antorsae/lx/baffle_modeling/l22mg-current-status/README.md

# L22MG current simulation status

This note identifies the current dense-BEM validation artifacts and the remaining gap to the requested acceptance target. The current default target is Juan's same-room/same-driver L22MG top-baffle measurement, not an Andres regenerated or retimed HDF5.

Requirement-by-requirement evidence and gaps are tracked in `docs/l22mg-requirement-trace/README.md`.

Secondary LX521 full-system context is now isolated in `docs/l22mg-lx521-system-sanity/README.md`. That report audits `output/data/polar_data_lx521_system.h5` only as a sanity surface for the measured high-mid system data path; it is not an L22MG mounted-alone acceptance target and is not used to tune the source or any rear/source scalar.

## Current Juan-Target Validation Path

- Current target: `output/data/polar_data_juan_lx521_top_raw.h5`, driver `L22MG (LX521 top raw)`.
- Measurement geometry: 0.50 m and LM/L22MG height, matching Juan's baffleless source measurements.
- Default validation angles: loaded from the target HDF5. For the Juan L22MG top-baffle target this is exactly 0/15/30/45/60/75/90 deg.
- Smoke evidence: `docs/l22mg-juan-top-target-angle-smoke/README.md` records `validation_angle_policy=target_hdf5_angles`, identical model/target angle lists, and no angular interpolation.
- Gate evidence: `docs/l22mg-juan-top-target-angle-smoke-gates/README.md` is a bounded edge-solver smoke, not acceptance. It proves the current target/geometry/angle provenance is auditable; the current full dense-BEM 300-1200 Hz evidence is the q7/near Juan-target candidate family summarized below, and it still fails shape, mesh, and passive-geometry gates.
- Mesh-target gate evidence: `scripts/backfill_l22mg_mesh_target_metadata.py` computes the same lambda/6 broad and lambda/10 boundary/local sizing metadata from stored HDF5 BEM attrs, and `docs/l22mg-mesh-target-metadata-smoke-gates/README.md` proves the gate-summary layer consumes it as an acceptance gate. The smoke intentionally fails because a 90 mm dense-BEM mesh at 2 kHz exceeds those targets. The current full-band artifacts have now been backfilled and report `mesh target = fail`: the h42/local32 rows are below lambda/6 broadly at 1200 Hz but exceed the 28.58 mm lambda/10 boundary/local target. This sizing gate is still not mesh-convergence proof.
- Mesh-target-compliant BEM smoke: `docs/l22mg-bem-juan-top-h1659-modal-compact2-solid-passive-h42-h28-q7near-meshtarget-smoke-gates/README.md` reruns the compact2 solid-passive q7/near path sparsely from 300-1200 Hz with h42/boundary28/local28. It passes the mesh-target gate at the 1200 Hz exported max frequency, with 28.00 mm boundary/local h below the 28.58 mm lambda/10 target, exact Juan target angles, direct-solver residual 8.315e-16, and source-CV pass. It is not an acceptance run: no mesh-convergence pair was run, all-angle normalized RMS is 4.028 dB, target-quality warnings remain, and passive-geometry parity remains `not_proven`.
- Mesh-target-compliant convergence smoke: `docs/l22mg-bem-juan-top-h1659-modal-compact2-solid-passive-h42-h28-h36-h24-q7near-meshtarget-conv-smoke-gates/README.md` adds the missing BEM convergence pair for the same sparse compact2 solid-passive path, comparing h42/boundary28/local28 against h36/boundary24/local24 while still solving exactly at the Juan 0/15/30/45/60/75/90 deg target angles. It passes coverage, angle-grid, source-CV, mesh-target sizing, and direct-solver gates, but it still fails acceptance: max normalized-polar mesh movement is 0.702 dB over 300-1200 Hz, above the 0.5 dB gate, all-angle normalized RMS remains 4.028 dB, target-quality warnings remain, and passive-geometry parity remains `not_proven`.
- Finer mesh-target convergence checks: `docs/l22mg-bem-juan-top-h1659-modal-compact2-solid-passive-h36-h24-h32-h21-q7near-meshtarget-conv-smoke-gates/README.md`, `docs/l22mg-bem-juan-top-h1659-modal-compact2-solid-passive-h32-h21-h28-h18-q7near-meshtarget-conv-smoke-gates/README.md`, and `docs/l22mg-bem-juan-top-h1659-modal-compact2-solid-passive-h28-h18-h24-h16-q7near-meshtarget-conv-smoke-gates/README.md` continue the same sparse current-format path with h36/boundary24/local24 versus h32/boundary21/local21, h32/boundary21/local21 versus h28/boundary18/local18, and h28/boundary18/local18 versus h24/boundary16/local16. All pass mesh-target sizing, exact Juan target angles, source-CV, and direct-solver gates, but all still fail all-angle mesh convergence because the 300 Hz / 90 deg point moves 1.179 dB, 1.733 dB, and 3.444 dB respectively. Through-80 movement is much lower, 0.227 dB, 0.572 dB, and 0.305 dB, but the acceptance gate is all-angle and remains failed.
- Target-panel averaging diagnostics: `docs/l22mg-bem-juan-top-h1659-modal-compact2-solid-passive-h32-h21-h28-h18-q7near-targetavg3-meshtarget-conv-smoke-gates/README.md` and `docs/l22mg-bem-juan-top-h1659-modal-compact2-solid-passive-h32-h21-h28-h18-q7near-targetavg7-meshtarget-conv-smoke-gates/README.md` repeat the h32/boundary21/local21 versus h28/boundary18/local18 pair with target-panel normal-trace averaging. q3 reduces the 300-1200 Hz max mesh movement from 1.733 dB to 0.953 dB and through-80 movement from 0.572 dB to 0.310 dB. q7 improves the same pair further to 0.672 dB all-angle max and 0.187 dB through-80 max, with 0.168 dB RMS movement, but still fails the 0.5 dB all-angle convergence gate. Shape also still fails at 3.920 dB all-angle normalized RMS. The regenerated convergence summary/detail CSVs explicitly record `target_average_order=3`, `target_average_order=7`, and `target_average_chunk_size=128`, so this numerical control is no longer implicit.
- Juan acceptance scorecard: `docs/l22mg-juan-acceptance-scorecard/README.md` selects the current strongest Juan-target row, `compact2-h32-h21-h28-h18-targetavg7-meshtarget-conv-smoke`, and expands the gate result into one row per criterion. It passes target provenance, 0.50 m LM/L22 measurement geometry, exact 0/15/30/45/60/75/90 deg target-angle solving, one global validation gain plus one global delay, zero angle-dependent/band-specific/rear/source dB corrections, full 300-1200 Hz coverage, wavelength mesh-target sizing, direct dense-BEM residual metadata, source-CV, source-offplane-not-required, contours, decomposition, and non-blocking `driver_stl_geometry_provenance` for the H1659-derived geometry dimensions. It still fails acceptance because all-angle shape is 3.920 dB, mesh movement is 0.672 dB versus the 0.5 dB gate, the 300 Hz / 75 deg target-quality warnings remain blocking, and the L22-only passive state is unproven. The scorecard now also writes `target_quality_masked_shape_diagnostic.csv`: excluding the stored 75 deg / 300.293-383.423 Hz target-quality cluster lowers the diagnostic-only all-angle RMS to 3.461 dB and through-80 RMS to 2.858 dB, but full-data acceptance remains unchanged. It also links the separate current-radius five-width deliverable, with 205/255/305/355/405 mm rows and required 205/305/405 rows present, while keeping width behavior qualitative because the 305 mm baseline still fails.
- Dense-BEM Juan-target smoke: `docs/l22mg-bem-juan-top-h1659-modal-compact2-dipole-angle-smoke/README.md` uses the current best Juan-only recommended source row, `h1659-modal-compact2-az24-reg1e-06`, with `rear_phase_mode=dipole`, exact target HDF5 angles, 640 BEM panels, and direct-solve max relative residual 7.106e-16. Its gate summary, `docs/l22mg-bem-juan-top-h1659-modal-compact2-dipole-angle-smoke-gates/README.md`, passes target provenance, angle-grid, source-CV, source off-plane-not-required, and BEM linear-solver gates. It is still `not_proven` overall because it is a bounded 300-360 Hz smoke and has no BEM mesh-convergence sweep.
- Full-band coarse dense-BEM Juan-target check: `docs/l22mg-bem-juan-top-h1659-modal-compact2-fullband-coarse-gates/README.md` compares h60/local45 against h50/local38 and h50/local38 against h42/local32 over 300-1200 Hz using the same Juan target and source-CV recommended source. Both rows pass target provenance, exact angle-grid, source-CV, source off-plane-not-required, full-band coverage, and direct-solver residual gates. Both still fail acceptance: h60/h50 has 4.795 dB all-angle normalized RMS and 1.058 dB mesh change; h50/h42 has 4.607 dB all-angle normalized RMS and 1.662 dB mesh change. Through-60 RMS is much better at 1.045 dB and 0.945 dB, but all-angle failure is dominated by the 75 deg low-frequency residual near 300.3 Hz.
- q7/near-panel full-band follow-up: `docs/l22mg-bem-juan-top-h1659-modal-compact2-fullband-q7near-gates/README.md` repeats the current Juan-target/source-CV recommended path with q7 integration and q7 near-panel subdivision. The default gate-summary report, `docs/l22mg-validation-gate-summary/README.md`, now summarizes this current Juan q7/near candidate family by default; legacy Andres/diagnostic artifacts require an explicit artifact preset. The `andres-mounted` q7/near run reduces the h50/local38 versus h42/local32 mesh delta from 1.662 dB to 1.207 dB, but h42/local32 versus h36/local27 is still 1.376 dB, so the low-frequency high-angle mesh movement is not solved by q7/near-panel integration alone. Its best row still fails shape at 4.429 dB all-angle normalized RMS over 300-1200 Hz, with through-60 RMS 0.934 dB and worst residual about +19.8 dB at 300.3 Hz / 75 deg.
- Width-sweep reporting guard: gate summaries now require the 205/305/405 mm rows before any passing 305 mm baseline can be called a quantitative width sweep, and they mark width-sweep artifacts with stale Juan source radius metadata as `stale_source_radius_diagnostic_only`. The current five-width BEM sweep, `docs/l22mg-bem-juan-top-h1659-modal-compact2-current-width-sweep-h42-h28-q7near-targetavg7-gates/README.md`, uses the corrected 0.50 m Juan radius and exact target angles, includes 205/255/305/355/405 mm rows, and is `qualitative_only` because the 305 mm baseline still fails all-angle shape and has no internal mesh-convergence pair. If a future baseline passes but still lacks required rows, the status is `not_proven`.
- Solid-passive Juan-target follow-up: `docs/l22mg-bem-juan-top-h1659-modal-compact2-solid-passive-gates/README.md` adds a target-neutral `passive-aperture-treatment=none` variant for the compact2 source, exact Juan HDF5 angles, 0.50 m source/target radius, q7 near-panel integration, and h42/local32 versus h36/local27 convergence. This is still the best current default-gate row by all-angle shape, but it fails acceptance: 4.233 dB all-angle normalized RMS, 0.977 dB through 60 deg, 3.541 dB through 80 deg, and worst residual +18.9 dB at 300.293 Hz / 75 deg. Mesh convergence worsens to 2.344 dB max, and passive-geometry parity remains `not_proven`.
- Additional source-candidate follow-up: the remaining finite H1659 rows that passed Juan-only source-CV now have current 0.50 m Juan-target full-band solid-passive BEM evidence. `docs/l22mg-bem-juan-top-h1659-modal-full2-solid-passive-gates/README.md` rejects full2 at 4.270 dB all-angle RMS, 3.558 dB through 80 deg, and 2.326 dB mesh max. `docs/l22mg-bem-juan-top-h1659-modal-compact3-solid-passive-gates/README.md` rejects compact3 at 5.410 dB all-angle RMS, 4.308 dB through 80 deg, and 5.470 dB mesh max. `docs/l22mg-bem-juan-top-h1659-modal-full4-svd-solid-passive-gates/README.md` rejects full4-SVD at 10.911 dB all-angle RMS, 8.705 dB through 80 deg, and 3.643 dB mesh max. `docs/l22mg-bem-juan-top-h1659-profile-ring-full-solid-passive-gates/README.md` rejects the full profile-ring SVD/no-SVD rows at 9.254/9.265 dB all-angle RMS, 6.696/6.707 dB through 80 deg, and 0.902/0.889 dB mesh max. This means the current recommended finite equivalent-source family is now contradicted by mapped BEM evidence, not merely missing BEM evidence.
- Axisymmetric directivity Juan-target diagnostic: `docs/l22mg-bem-juan-top-axisymmetric-directivity-1000-1200-current/README.md` and `docs/l22mg-bem-juan-top-axisymmetric-directivity-1000-1200-current-gates/README.md` map the no-inversion rotated naked-polar source into the current Juan L22 top-baffle target at the corrected 0.50 m radius and exact 0/15/30/45/60/75/90 deg target angles. It is current negative evidence, not a fit correction: source CV remains `diagnostic_only`, coverage is only 1000-1200 Hz, all-angle normalized RMS is 5.768 dB, through-80 RMS is 3.344 dB, worst error is +13.807 dB at 1000.1 Hz / 90 deg, and passive geometry remains `not_proven`.
- Passive-geometry gate: the default gate-summary report marks all current Juan q7/near rows as `passive geom = not_proven`. The older rows use `andres-mounted` passive geometry, meaning a raised UM face and closed tweeter patches inherited from the Andres mounted-driver condition. The solid-passive rows avoid silently applying Andres-mounted geometry, but the current validation target is Juan's L22-only top-baffle capture and the HDF5 also contains a separate `L22MG+L10NEO+Tweeters (LX521 top raw)` capture; the L22-only HDF5 now records `passive_state_status=unused_um_tweeter_state_unrecorded`, which is an explicit unknown rather than evidence for open holes, covered patches, or mounted inactive drivers. This is an explicit parity blocker, not a correction knob.
- Juan passive-state provenance audit: `docs/l22mg-juan-top-passive-state-audit/README.md` reads the stored HDF5 notes directly and writes the structured passive-state attrs. It confirms the L22MG target notes prove 50 cm distance, LM/L22MG mic height, LX521 top-baffle mounting, and raw/no-crossover/no-EQ processing, while the unused L10NEO/tweeter physical state remains unrecorded. It also confirms the multi-driver capture explicitly records L22MG + L10NEO + tweeters on the top baffle, but that is a multi-source no-crossover context measurement, not an L22-alone passive-geometry target. The passive-geometry gate now points to this audit.
- Focused Juan low-frequency/high-angle diagnostic: `docs/l22mg-juan-top-lowfreq-high-angle-diagnostic/README.md` reads the previous mounted-passive q7/near artifact's `/validation_decomposition` group without refitting or rerunning. At the worst point, 300.3 Hz / 75 deg, the Juan top-baffle target is -29.9 dB normalized, the synthetic nude reference is -10.6 dB, and the mounted model is -10.1 dB. Relative to the synthetic nude field, the target deepens by -19.3 dB while the model fills by +0.5 dB. The same report reads the stored mesh-convergence summary: h42/local32 versus h36/local27 moves 1.38 dB at 300 Hz / 90 deg and 0.572 dB through 80 deg at 300 Hz / 75 deg. The newer solid-passive row leaves the same measured-target null as the dominant all-angle blocker: +18.909 dB at 300.293 Hz / 75 deg. New BEM convergence runs now also export `bem_mesh_convergence_detail.csv` so this mesh-delta surface is inspectable per frequency and angle instead of only as maxima. The focused rerun `docs/l22mg-juan-top-q7near-300hz-mesh-detail-diagnostic/README.md` uses the same h42/local32 versus h36/local27 q7/near pair over the 300 Hz blocker and shows the side-by-side detail: at 300.293 Hz / 75 deg the validation residual is +19.806 dB while the mesh normalized delta is -0.572 dB; at 90 deg the validation residual is only +1.518 dB while the mesh delta is -1.374 dB. So the 75 deg acceptance failure is primarily model/source/measurement physics, while the 90 deg point remains the larger local mesh-movement diagnostic.
- Juan measured-target null audit: `docs/l22mg-juan-top-target-null-audit/README.md` compares measured Juan L22 top-baffle, measured Juan L22 nude, and the multi-driver top-baffle capture without running BEM or changing gates. At 300.293 Hz / 75 deg the L22-alone top target is -29.894 dB normalized while the measured L22 nude is -9.594 dB, so the measured target-minus-nude transfer is -20.300 dB. The multi-driver top capture at the same frequency/angle is -18.024 dB, 11.870 dB shallower than the L22-alone target. That does not invalidate the L22-alone target, but it makes this 75 deg null a repeatability/target-quality item before treating it as decisive proof of BEM/source failure.
- Juan top-baffle front/rear consistency audit: `docs/l22mg-juan-top-front-rear-consistency/README.md` reads measured Juan HDF5 front and rear data only. At the same 300.293 Hz / 75 deg blocker, the L22-alone front target is -29.894 dB but the rear side is -9.455 dB, so front-minus-rear is -20.440 dB and the measured front-minus-rear baffle-transfer delta is -21.300 dB. Over 300-600 Hz and 60-90 deg, L22 top front/rear normalized RMS difference is 10.733 dB. This strengthens the target-quality/repeatability warning and prevents a future BEM/source change from being accepted merely because it target-fits that isolated front-side null.
- Juan target-polar-quality audit: `docs/l22mg-juan-top-target-polar-quality/README.md` flags the same low-frequency region without looking at the model. With a -25 dB threshold over 300-600 Hz, it finds one deep cluster: 75 deg at 300.293 Hz, -29.894 dB normalized, 83.1 Hz wide, and 17.3 dB deeper than adjacent angles. The same-angle local contrast is only -0.6 dB, so this is broad in frequency but angularly isolated.
- Target-null gate-summary integration: `docs/l22mg-juan-top-target-null-gate-summary/README.md` shows the current q7/near full-band row and the focused 300 Hz row now report `target null = warning`. The warning is diagnostic target-quality context, not an alternate target and not a scalar correction; it prevents the 300 Hz / 75 deg residual from being read as a silent clean acceptance anchor.
- Juan low-frequency geometry sensitivity: `docs/l22mg-juan-top-lowfreq-geometry-sensitivity/README.md` reruns only the 300.293/304.321 Hz blocker against the Juan target while changing physical geometry/passive assumptions, not source/rear scalars. Tested variants include the current raised UM face, closed solid passive patches, open passive holes, raised tweeter faces, and Wmax 205/405 mm. None closes the 75 deg null: the best 70-90 deg RMS is still 13.301 dB (`width205_um_face`), and every variant's max miss remains at 300.293 Hz / 75 deg around 18.9-19.9 dB. Simple baffle width/passive treatment changes therefore do not explain the measured L22-alone 75 deg target null.
- Juan passive-state band sensitivity: `docs/l22mg-juan-top-passive-state-band-sensitivity/README.md` reruns a sparse 300-600 Hz diagnostic at the actual Juan target angles 0/15/30/45/60/75/90 deg. Solid patches are the best of the tested passive-state variants, but still leave 9.890 dB RMS over 70-90 deg and 0.932 dB RMS over 0-60 deg; open holes are essentially similar at 9.919 dB over 70-90 deg. This does not prove the passive state, but it shows simple passive-state assumptions do not close the low-frequency high-angle target null.
- Juan low-frequency source-support/acoustic-center sweep: `docs/l22mg-juan-top-lowfreq-source-support-sweep/README.md` reuses the same 300.293/304.321 Hz Juan target hotspot and fixed mounted-baffle BEM geometry, then varies only Juan-fitted source supports plus bounded acoustic-center offsets of -20/0/+20 mm. The best row, `d65_r0-25-50-75-95_svd1e-6_ac-20mm`, keeps 0-60 deg RMS at 1.434 dB and improves 70-90 deg RMS from 14.046 dB for the current source to 7.361 dB. That is useful sensitivity evidence, but still far from the 1.5 dB target and not an acceptance path; it also remains a source-support diagnostic, not a target-derived correction.
- Andres published parity remains available only as an explicit legacy validation target, now through `--validation-preset andres-published-parity`. Preset smoke evidence: `docs/l22mg-andres-published-parity-preset-smoke/README.md` records the canonical HDF5/driver/hypothesis bundle, exact 0/10/.../90 deg target-angle solve, 1 m UM-height mic (+165 mm relative to L22), published-explorer parity match, and no angular interpolation; `docs/l22mg-andres-published-parity-preset-smoke-gates/README.md` verifies the same provenance through the gate-summary layer. The gate-summary and source-decision join now also reject Andres published-parity rows unless the stored mic geometry is explicitly `validation_mic_reference=um`, `validation_mic_z_offset_mm=165.0`, and `validation_mic_horizontal_radius_m=1.0`; the passive-geometry gate also requires `andres-mounted` plus `passive_um_driver_included=True`, so a UM cutout without a modeled mounted UM driver face cannot pass as published-parity evidence. First-lobe, strongest-lobe, direct-gate, and late-window Andres variants remain diagnostics unless the published explorer is regenerated from the same data.
- Current-format Andres dense-BEM preset smoke: `docs/l22mg-bem-andres-published-parity-preset-h1659-compact2-smoke/README.md` runs the actual dense Neumann BEM backend, not the edge baseline, with `--validation-preset andres-published-parity`, the corrected 0.50 m Juan naked-source radius, H1659 modal compact-2 source, Andres-mounted passive geometry, and direct solver residual 7.106e-16. Its gate summary, `docs/l22mg-bem-andres-published-parity-preset-h1659-compact2-smoke-gates/README.md`, passes target provenance, exact target-angle grid, source-CV, BEM solver residual, contours, and decomposition. It is still not acceptance evidence because it only covers 300-360 Hz, has no mesh-convergence sweep, fails source off-plane spread, and the available-overlap all-angle RMS is 9.277 dB due to the published 90 deg low-frequency null. Through-60 over this bounded overlap is 0.333 dB and through-80 is 1.515 dB.
- Current-format Andres bounded BEM convergence smoke: `docs/l22mg-bem-andres-published-parity-preset-h1659-compact2-conv-smoke/README.md` repeats that dense-BEM preset path and compares h60/boundary45/local45 against h50/boundary38/local38 over 300-360 Hz. The gate summary, `docs/l22mg-bem-andres-published-parity-preset-h1659-compact2-conv-smoke-gates/README.md`, keeps it `not_proven`: coverage is not full-band and the h60-to-h50 mesh movement is still too large for acceptance, with max normalized change 1.303 dB at 300 Hz / 80 deg and RMS 0.511 dB over the available overlap. The validation miss itself remains dominated by the published 90 deg low-frequency null: all-angle RMS 9.277 dB, through-60 0.333 dB, through-80 1.515 dB, worst +29.386 dB at 330 Hz / 90 deg.
- Current-format Andres q7/near bounded convergence smoke: `docs/l22mg-bem-andres-published-parity-preset-h1659-compact2-q7near-h50-h42-smoke/README.md` compares h50/boundary38/local38 against h42/boundary32/local32 with q7 triangle quadrature plus q7 near-panel integration over the same 300-360 Hz Andres preset band. Its gate summary, `docs/l22mg-bem-andres-published-parity-preset-h1659-compact2-q7near-h50-h42-smoke-gates/README.md`, is still diagnostic: max normalized mesh change is 1.236 dB at 300 Hz / 90 deg, through-80 max is 0.994 dB at 300 Hz / 80 deg, and RMS mesh movement is 0.461 dB. The finer/q7 path improves the validation overlap versus the h60 smoke, with all-angle RMS 8.852 dB, through-60 0.170 dB, through-80 0.989 dB, and worst +28.244 dB at 331.4 Hz / 90 deg, but it still cannot be read as full-band or mesh-converged acceptance evidence.
- Current-format Andres physical rear-basket smoke: `docs/l22mg-bem-andres-published-parity-physical-rear-basket-smoke/README.md` runs the coupled H1659 physical-diaphragm/rear-basket prescribed-Neumann source against Andres published parity at the corrected 0.50 m Juan radius, exact 0/10/.../90 deg target angles, Andres-mounted passive geometry, and no source/rear scalar correction. Its gate summary, `docs/l22mg-bem-andres-published-parity-physical-rear-basket-smoke-gates/README.md`, is negative bounded evidence only: it covers 300-301 Hz, passes target provenance, exact angle grid, mesh-target sizing, dense direct residual, passive geometry, contours, and decomposition, but fails coverage, source CV, source off-plane generalization, target measurement quality, and shape at 6.869 dB all-angle RMS. Through-60 is 0.233 dB and through-80 is 1.218 dB, but the worst residual remains +21.4 dB at 301 Hz / 90 deg. It is now joined into the source-candidate decision report as Andres side evidence, not as Juan acceptance evidence.

- Current-format Andres coupled rear-basket plus active-driver feature-proxy smoke: `docs/l22mg-bem-andres-published-parity-coupled-rear-basket-feature-proxy-smoke/README.md` adds the explicit H1659 feature-proxy path to the same coupled physical source: rigid STL-derived frame/flange/motor scatterer, mounting pockets forced on, thin 0.6 mm flange sidewalls omitted as a labelled constant-panel mesh-quality approximation, Andres-mounted passive geometry, corrected 0.50 m Juan source radius, and exact Andres target HDF5 angles. Its gate summary, `docs/l22mg-bem-andres-published-parity-coupled-rear-basket-feature-proxy-smoke-gates/README.md`, is also negative bounded evidence only. Over the same 300-301 Hz overlap it worsens the physical rear-basket smoke to 13.965 dB all-angle RMS, 2.465 dB through 60 deg, 6.156 dB through 80 deg, and worst +40.1 dB at 301 Hz / 90 deg. This rules out the first rigid feature-proxy obstruction as a hidden fix for the Andres low-frequency high-angle null; it is not a raw-STL solve, not elastic driver physics, and not a scalar correction.
- Current-format Andres full-band modal-full2 rerun: `docs/l22mg-bem-andres-published-parity-h1659-modal-full2-300-1200-current/README.md` reruns the strongest historical Andres full-band source family with `--validation-preset andres-published-parity`, corrected 0.50 m Juan naked-source radius, exact 0/10/.../90 deg target-angle solve, Andres-mounted passive geometry, q7 plus q7 near integration, and h22/local13.2 versus h20/local12 convergence over 300-1200 Hz. Its gate summary, `docs/l22mg-bem-andres-published-parity-h1659-modal-full2-300-1200-current-gates/README.md`, passes target provenance, full 300-1200 coverage, exact target-angle grid, mesh convergence (0.111 dB max, 0.027 dB RMS), direct solver residual (1.576e-15), Juan-only source-CV, passive geometry, contours, and decomposition. It still fails acceptance because all-angle normalized RMS is 4.428 dB and source off-plane generalization fails; through-60 RMS is 0.686 dB and through-80 RMS is 1.377 dB.
- Andres acceptance scorecard: `docs/l22mg-andres-acceptance-scorecard/README.md` selects that current full-band modal-full2 row as the strongest current-radius published-parity evidence because it has full 300-1200 coverage and proven mesh convergence. The scorecard expands the gate result into one row per criterion: target provenance, UM-height measurement geometry, exact target-angle solve, one global validation gain plus one global delay, zero angle-dependent/band-specific/rear/source dB corrections, coverage, mesh convergence, wavelength mesh-target sizing, dense direct residual, source CV, passive geometry, contours, and decomposition pass; target measurement quality remains `not_proven` because late-window/high-angle stability is unresolved, all-angle normalized polar shape fails at 4.428 dB, and source off-plane generalization fails at 13.406 dB over 70-90 deg. The off-plane row now separates the selected source's small z=0-to-UM-height movement (0.153 dB RMS over 70-90 deg) from the much larger Juan-CV-eligible source-family spread at UM height (13.406 dB RMS / 26.652 dB max over 70-90 deg). It now also includes a `validation_metric_breakdown` diagnostic row for on-axis, baffle-transfer, F90-F0, DI, -6 dB beamwidth, and complex-pressure residuals, plus `high_angle_late_window_caveat` and `target_quality_masked_shape_diagnostic` rows that record the through-60/through-80 shape numbers, raw-IR gate movement, target-quality cluster masking, and target >= -20 dB masking without excluding data or changing acceptance. The diagnostic CSV, `docs/l22mg-andres-acceptance-scorecard/target_quality_masked_shape_diagnostic.csv`, shows full-data RMS 4.428 dB, cluster-masked RMS 2.561 dB, and target >= -20 dB RMS 1.365 dB; this localizes the high-angle target-quality blocker but is not an acceptance substitute. Width sweeps remain `qualitative_only`.
- Current-format Andres axisymmetric-directivity diagnostic: `docs/l22mg-bem-andres-published-parity-axisymmetric-directivity-1000-1200-current/README.md` refreshes the no-inversion directivity-table source with the corrected 0.50 m Juan radius, Andres published-parity target, exact 0/10/.../90 deg target angles, Andres-mounted passive geometry, and h42/local32 q7-near BEM. Its gate summary, `docs/l22mg-bem-andres-published-parity-axisymmetric-directivity-1000-1200-current-gates/README.md`, passes target provenance, exact angle grid, direct solver residual (1.041e-15), passive geometry, contours, and decomposition, but remains rejected diagnostic evidence: coverage is only 1000-1200 Hz, no mesh convergence sweep was run, all-angle normalized RMS is 3.912 dB over the available overlap, source CV is `diagnostic_only`, and source off-plane spread fails at 13.940 dB over 70-90 deg. The direct rotated naked polar is therefore current-radius negative evidence, not a high-fidelity acceptance source.

## Historical Andres Corrected-Geometry Validation Artifact

- Report: `docs/l22mg-bem-passive-um-cutout-widecloud-svd1e-5-h20-h18-conv-q7-near-1200-12ppo/README.md`.
- HDF5: `output/l22mg-bem-passive-um-cutout-widecloud-svd1e-5-h20-h18-conv-q7-near-1200-12ppo/polar_data_l22mg_lx5214_baffle_sim.h5`.
- Strict gate report: `docs/l22mg-validation-gate-current-backfilled/README.md`.
- Validation decomposition diagnostic: `docs/l22mg-validation-decomposition-current/README.md`.
- Solver: dense constant-element exterior Neumann BEM, finite-thickness LX521.4 top baffle, passive aperture treatment `andres-mounted`.
- Baffle thickness: 19.05 mm.
- Mesh: `delaunay-local`, broad h = 20.0 mm, boundary/local h = 12.0 mm, local refinement width = 36.6 mm, q7 triangle quadrature plus q7 near-panel integration with one subdivision and distance factor 2.5.
- Mounted passive geometry: parameterized rigid UM face, diameter 82 mm, height 4 mm, mesh h 16 mm, over an 82 mm UM cutout; tweeter positions closed as solid patches.
- Source: split front/rear finite monopole cloud fit to Juan nude L22MG only, half-depth 45 mm, radii 0/35/70/95 mm, regularization 1e-6, SVD rcond 1e-5.
- Important: this is the latest mesh-converged corrected-geometry validation comparison now replayed against the canonical Andres published-parity target, `output/data/polar_data_andres_early_peak_legacy.h5`. That HDF5 matches the already-published polar explorer at 1004 Hz, so it is the acceptance target unless the published explorer is regenerated from a different HDF5 in the same commit. The h20/local12.0 versus h18/local10.8 q7-near mesh comparison passes the 0.5 dB max-change gate, but the artifact still fails shape validation.
- Superseded reference: `docs/l22mg-bem-local-h22-h20-conv-1200-q3-d25-t1905-48ppo/README.md` used literal open passive UM/tweeter holes, so it is no longer a valid Andres-geometry baseline.
- Superseded mounted-passive reference: `docs/l22mg-bem-passive-um-widecloud-svd1e-5-h22-q7-near-1200-12ppo/README.md` placed the raised UM face over a closed solid patch. It remains useful as a before/after diagnostic, but not as the current Andres-mounted geometry baseline.
- Important: the current corrected-geometry artifacts now satisfy both the h22/h20 and h20/h18 mesh-change checks, but no current dense-BEM artifact satisfies the Andres shape validation target.

## Best Source Diagnostic So Far

- Report: `docs/l22mg-bem-passive-um-cutout-widecloud-svd1e-5-h22-q7-near-1200-12ppo/README.md`.
- HDF5: `output/l22mg-bem-passive-um-cutout-widecloud-svd1e-5-h22-q7-near-1200-12ppo/polar_data_l22mg_lx5214_baffle_sim.h5`.
- Difference from the older stable 0/40/75 mm source artifact: source radii are 0/35/70/95 mm, with 45 mm half-depth, dipole reconstructed rear phase, and SVD rcond 1e-5. The passive UM is now modeled as a mounted face over the UM cutout rather than over a solid patch.
- Conditioning: SVD-truncated Juan-only fit with `--source-svd-rcond 1e-5`; raw `design_cond_max` remains about 6.8e9, but effective condition is capped around 9.6e4 with effective rank 4-6.
- Validation improvement versus the older stable 0/40/75 mm source: normalized polar RMS 300-1200 Hz is 3.658 dB against the canonical published-parity Andres target in the stored h20/h18 mesh-converged wide/SVD baseline. Through-60-deg RMS is 1.327 dB and through-80-deg RMS is 1.956 dB, but the all-angle result still fails because the worst residual is +19.740 dB at 344.6 Hz / 90 deg. Important correction: these stored BEM artifacts were generated with the old, mistaken 0.75 m Juan source radius, so they are now historical geometry/numerics diagnostics until rerun at 0.50 m.
- Caveat: this still fails all-angle acceptance. `output/data/polar_data_andres_early_peak_legacy.h5` is now the canonical published-parity target because it matches the published polar explorer; first-lobe, direct-gate, and strongest-lobe HDF5 variants are diagnostics only unless the published explorer is regenerated from the same data.
- Diagnostic target replays: `docs/l22mg-retimed-artifact-rerank/README.md` and related direct-gate reports rerank older stored predictions against explicitly labelled first-lobe/direct-gate Andres variants without re-solving BEM. They remain useful for target-sensitivity and source-ranking diagnostics, but they do not replace the published-parity target.
- Acoustic-center offset test: `docs/l22mg-bem-passive-um-widecloud-svd1e-5-ac20-h22-q7-near-1200-12ppo/README.md` moves the wide-cloud equivalent source 20 mm rearward. It makes the F90 mean error shallower (+2.042 dB instead of -4.537 dB) but worsens all-angle normalized RMS to 6.161 dB and through-60 RMS to 3.666 dB. Acoustic-center offset alone is therefore not a viable fix for the high-angle miss.
- High-angle residual diagnostic: `docs/l22mg-high-angle-residual-um-cutout-full/README.md` decomposes the current mounted-UM-cutout error. For the current SVD wide-cloud model, 0-60 deg RMS is 1.341 dB, but 70-90 deg RMS is 7.139 dB. The 90 deg mean error is now near zero at +0.172 dB, but the 70-90 deg group still has a worst residual of 25.298 dB at about 1070 Hz / 80 deg. That means the remaining miss is a localized high-angle lobe/null-shape problem, not a single scalar null-depth, 90-degree timing issue, or acoustic-center issue.
- Juan-only source cross-validation: `docs/l22mg-source-model-cross-validation/README.md` now uses the corrected 0.50 m Juan source radius and holds out one nonzero naked angle at a time while keeping 0 deg as the normalization anchor. The current wide/SVD source has in-sample Juan normalized front/rear RMS 2.404/2.500 dB and absolute front/rear RMS 2.381/2.469 dB over 300-1200 Hz, but held-out worst-side RMS is 8.810 dB and is marked `rejected_weak_cv`. The first finite source that passes the Juan-only thresholds is `h1659-modal-compact2-az24-reg1e-06` at 3.298 dB, followed by `h1659-modal-full2-az24-reg1e-06` at 3.300 dB and `h1659-modal-compact3-az24-reg1e-06` at 3.768 dB. Stored 0.75 m BEM replays, including `h1659-modal-full2-300-1200`, are now stale for acceptance joining until rerun at 0.50 m.
- Active H1659 source-surface CV: the expanded source-CV table now includes Juan-fitted prescribed-Neumann active-surface rows. The stored split active-surface m4/gap30 candidate maps to `split-active-surface-compact-m4-az16-gap30-q3-reg1e-06-svd1e-05`, rank 12 of 29, but is `rejected_bad_insample_fit` with 3.673 dB in-sample side-worst and 4.376 dB held-out worst-side RMS; its stored BEM overlap is also poor at 5.320 dB all-angle RMS from 1000-1200 Hz. The single active-surface m3 row is rank 16 of 29, also `rejected_bad_insample_fit`, with 7.047 dB held-out worst-side RMS and 6.815 dB stored BEM overlap. `docs/l22mg-source-cv-active-surface-annular/README.md` adds a focused Juan-only annular active-surface basis audit: the best annular row is split compact, measured rear phase, gap 30 mm, with 4.179 dB held-out worst-side RMS but 3.728 dB in-sample side-worst RMS, so it remains `rejected_bad_insample_fit`. `docs/l22mg-bem-split-active-surface-annular-cv-smoke/README.md` verifies the simulator/HDF5 report path now labels `active_surface_basis_kind=annular` and matches that focused CV row; this is a smoke/report check, not an acceptance run.
- Physical diaphragm source CV: `docs/l22mg-source-cv-physical-diaphragm/README.md` adds a Juan-only coupled H1659 prescribed-Neumann source family with four capped radial velocity modes: piston, two cone bending/tilt shapes, and surround. No row passes the source recommendation gates. The best row, `physical-diaphragm-full-coupled-measured-az16-q3-reg1e-06-svd1e-05`, has 3.448 dB held-out side-worst RMS, but is still `rejected_bad_insample_fit` because in-sample side-worst normalized/absolute/phase RMS are 3.119 dB / 4.712 dB / 62.053 deg.
- Physical rear-filter diagnostic: `docs/l22mg-physical-rear-filter/README.md` fits the same four-mode physical diaphragm to Juan front only, then fits a smooth bounded rear transfer function from Juan rear only. The front-only diaphragm fit is acceptable on the front side over 300-1200 Hz (2.067 dB normalized, 2.053 dB absolute, 13.342 deg phase RMS), but rear normalized RMS remains 3.180 dB after both an unconstrained scalar and the smooth bounded filter. The smooth bounded filter has median -7.569 dB gain and cannot repair rear angular shape because it is shared by all rear angles.
- Physical rear-basket source CV: `docs/l22mg-source-cv-physical-rear-basket/README.md` keeps the diaphragm modes coupled front/rear and adds a small Juan-only rear basket/directivity block. The refreshed full-band set now includes bounded rb3/rb4 measured-phase probes plus frequency-smoothing probes around the actual best low-order m2/rb1 family. The best row is still unsmoothed `physical-rear-basket-compact-measured-m2-rb1-az16-gap16-q3-reg1e-06`, rejected at 3.592 dB held-out side-worst RMS because in-sample side-worst absolute/phase are 4.543 dB / 72.737 deg. The m2/rb1 smoothing probes do not fix this: fsmooth1e-8/1e-7/1e-6 stay at 3.592/3.593/3.596 dB held-out side-worst, 4.543/4.544/4.557 dB absolute, and about 72.74 deg phase. The older m4/rb2 and rb3/rb4 rows remain rejected, so frequency smoothing and extra rear-only terms do not create a Juan-accepted physical source.
- Bounded active-surface annular sweep: `docs/l22mg-source-cv-active-surface-annular-sweep/README.md` sweeps compact/full H1659 annular source surfaces, measured rear phase, 30/36 mm split gaps, and no/SVD truncation over 12 Juan-only candidates. No row passes the Juan-only recommendation gates. The best row is still the compact gap-30 annular source, now without SVD truncation, with 4.179 dB held-out worst-side RMS and 3.728 dB in-sample side-worst RMS over 300-1200 Hz. Because all rows are `rejected_bad_insample_fit`, this sweep is negative source evidence and does not justify a new BEM acceptance attempt.
- Source-CV report integration: current simulator reports now look up matching rows in `docs/l22mg-source-model-cross-validation/source_cv_summary.csv` plus physical-diaphragm and physical-rear-basket summaries by default, then copy the held-out metrics, in-sample side-worst normalized/absolute/phase metrics, recommendation status, recommendation reason, and matched CSV path into both README text and HDF5 metadata. `docs/l22mg-validation-gate-summary/README.md` now refuses stale embedded source-CV metadata when an artifact carries `naked_source_reference_radius_m=0.75`; those artifacts report source CV as not proven against the corrected 0.50 m Juan distance.
- Source-candidate decision join: `docs/l22mg-source-candidate-decision/README.md` combines the current 0.50 m main, physical-diaphragm, physical-diaphragm frequency-smoothing, and physical-rear-basket source-CV rows with the off-plane UM-height source ambiguity audit and the q7 target-averaged compact2 gate summary. It reports zero accepted source candidates across 129 current-radius rows. It now also attaches current-radius Andres published-parity BEM rows as a separate legacy comparison channel, not as Juan acceptance evidence: compact2 maps to the 300-360 Hz q7 smoke at 8.852 dB all-angle / 0.989 dB through-80, full2 maps to the full-band published-parity rerun at 4.428 dB all-angle / 1.377 dB through-80, and the coupled physical rear-basket smoke maps to `physical-rear-basket-andres-smoke` at 6.869 dB all-angle / 1.218 dB through-80 over 300-301 Hz. The decision input list also includes the current feature-proxy Andres smoke, which is worse at 13.965 dB all-angle / 6.156 dB through-80 over 300-301 Hz and therefore does not replace the selected lower-RMS rear-basket side row. The current five-width sweep gate summary for current-radius width reporting and the coupled physical rear-basket Juan-target BEM smoke, `docs/l22mg-coupled-rear-basket-source-smoke-gates/README.md`, remain subject to normal gate ordering and neither can make a failing baseline accepted. The physical rear-basket smoke now appears in the decision table as `coupled-rear-basket-source-smoke`, and rejects `physical-rear-basket-compact-measured-m4-rb2-az16-gap16-q3-reg1e-06` by both source CV and failed available-overlap BEM evidence: 7.608 dB all-angle RMS, 8.189 dB through-80, worst +19.8 dB at 300 Hz / 75 deg. The best physical rear-basket source-CV row, `physical-rear-basket-compact-measured-m2-rb1-az16-gap16-q3-reg1e-06`, is now also joined to bounded Juan and Andres BEM smokes; it is rejected by source CV and failed overlap evidence, with `physical-rear-basket-m2rb1-juan-smoke` at 6.447 dB all-angle / 6.959 dB through-80 and `physical-rear-basket-m2rb1-andres-smoke` at 10.021 dB all-angle / 1.719 dB through-80 over 300-301 Hz. The new m2/rb1 frequency-smoothed rows appear immediately behind it in the decision table, but remain rejected by source CV and have no BEM evidence because they do not pass the Juan source gates. The join maps physical rear-basket rb1/rb2 off-plane cases as well as physical-diaphragm cases; rb3/rb4 rows remain rejected by source CV before off-plane evidence is needed. It also carries the Juan-only rear shared-sign diagnostic: the current `-1` outward-normal convention remains the best normalized front/rear fit at 2.635 dB versus 3.584 dB for the deliberate `+1` diagnostic, so a sign flip is not a hidden source-fit fix. All six finite H1659 sources that pass Juan-only source-CV are attached to current Juan-target full-band BEM evidence and rejected. Compact2 is now joined to the mesh-target-compliant q7 target-averaged row at 3.920 dB all-angle RMS, 3.491 dB through-80 RMS, and 0.672 dB mesh movement; it still fails shape, all-angle mesh convergence, target-quality, and passive-geometry gates. The remaining mapped finite sources are unchanged: full2 is 4.270/3.558 dB, compact3 is 5.410/4.308 dB, full4-SVD is 10.911/8.705 dB, and the profile-ring-full SVD/no-SVD rows are 9.254/6.696 dB and 9.265/6.707 dB.
- Current validation decomposition diagnostics read the exported `/validation_decomposition` group without rerunning or refitting. Against the canonical published-parity target, the mesh-converged wide/SVD row's worst point is 344.6 Hz / 90 deg: Andres is -42.4 dB normalized, the synthetic nude reference is -20.8 dB, and the model is -22.7 dB. The h1659-modal-full2 full-band row's worst point is similar, 338.0 Hz / 90 deg: Andres is -42.6 dB normalized, synthetic nude is -21.7 dB, and the model is -19.4 dB. The failure is therefore not a hidden scalar-alignment issue; the published target contains a much deeper 90 deg low-frequency null than the model/nude reference. High-angle target-processing sensitivity remains diagnostic context and is treated separately below.
- Published-null context audit: `docs/l22mg-published-null-context/README.md` ties the low-frequency 90 deg blocker to the canonical published-parity target, diagnostic target variants, IR timing, and current model residual. The deepest published high-angle null is -42.74 dB at 330.3 Hz / 90 deg. At 338.013 Hz / 90 deg, published parity is -42.65 dB, while first-lobe, legacy-strongest, and direct-gate diagnostics are -16.75, -18.27, and -21.77 dB respectively. The current h1659-modal-full2 geometry baseline is -19.95 dB mean over the 338/344.6 Hz 90 deg group. The audit confirms the published/legacy high-angle peak is not the -12 ms early event, but at 90 deg it is the later absolute lobe of the near-reference wavelet, 0.083 ms / 28.6 mm after the first strong lobe; this keeps F90/null-depth diagnostic rather than decisive.
- Low-frequency null source-support sweep: `docs/l22mg-lowfreq-null-source-support-sweep/README.md` reuses a fixed h22/local13.2 q7-near Andres-mounted BEM system at 338.0 and 344.6 Hz, then varies only Juan-fitted source support. The sweep now includes H1659 profile/modal ring candidates as well as split-discrete supports. The best row is `h1659-modal-full3-az24-reg1e-06`: it keeps 0-60 deg RMS at 0.190 dB and improves the 70-90 deg low-frequency hotspot from 11.720 dB for the current split-discrete source to 8.289 dB, but it remains far from the 1.5 dB target and is not acceptance evidence. This rules out a simple Juan-only source-support retune as the explanation for the published 90 deg low-frequency null.
- Low-frequency null physical-geometry sensitivity: `docs/l22mg-lowfreq-null-geometry-sensitivity/README.md` holds the canonical Andres published-parity target fixed and uses the Juan-only `h1659-modal-full-2` source, then varies only physical/mic assumptions around the 338.0/344.6 Hz low-frequency null. The correct Andres-mounted baseline is still excellent through 60 deg (0.237 dB RMS) but fails 70-90 deg at 13.077 dB RMS and 90 deg at 22.596 dB RMS because the published target is about -42.5 dB at 90 deg while the model is about -19.9 dB. Raised tweeter faces are effectively neutral (13.073 dB 70-90 RMS), bounded mic-height shifts from 120 to 210 mm are effectively neutral, and 18.3 mm thickness is worse. Deliberately wrong UM/open-hole controls reduce the residual to about 9.2-9.4 dB over 70-90 deg but remain diagnostic-only and still far from acceptance, so the published low-frequency null is not explained by simple mounted-passive geometry, thickness, or mic-height tweaks.
- Linkwitz theory check: `docs/l22mg-linkwitz-baffle-dipole-theory/README.md` extracts the relevant baffle/dipole guidance from `linkwitz/linkwitzlab_archive.md`. It supports the finite-BEM approach and warns against point-source-only or scalar baffle corrections. It also motivated a bounded `ideal-dipole` rear-source diagnostic: forcing rear = -front deepens the h1659-modal-full2 90 deg low-frequency model by only about 0.67 dB, leaving 21.924 dB RMS error at 90 deg and 12.667 dB over 70-90 deg. The low-frequency null is therefore not explained by a simple measured-rear-magnitude imbalance.
- Direct-gated Andres target diagnostic: `scripts/build_andres_l22mg_direct_gate_target.py` builds `output/data/polar_data_andres_l22mg_direct_gate_0p8ms.h5` from the raw `.mdat` impulse responses using the first strong near-reference lobe and a 0.5 ms left / 0.8 ms right gate. The HDF5 is marked `diagnostic_only` and `not_acceptance_target`. Against the canonical published-parity target, `docs/l22mg-target-robustness/README.md` shows this short-gate target moves 0.836 dB RMS through 60 deg but 6.741 dB RMS over 70-90 deg. Raw saved-window references are not-first-lobe at 60/70/80/90 deg; those saved/global peaks are later than the first strong lobe and are treated as rejected reflected/scattered local-wave energy for timing. Replaying stored BEM artifacts against this diagnostic target can lower high-angle residuals, but it is still not a clean acceptance pass and cannot replace the published-parity target.
- Compact H1659 SVD profile-ring decomposition: `docs/l22mg-validation-decomposition-profile-ring-compact-svd/README.md` shows the same failure mode on the Juan-better compact profile-ring source. At 1070.1 Hz / 80 deg, Andres is -45.3 dB normalized, synthetic nude is -19.4 dB, and the model is -4.1 dB, so the model fills the high-angle null by +15.4 dB relative to its own nude reference while the measured mounted speaker is -25.9 dB below that reference. `docs/l22mg-high-angle-residual-profile-ring-compact-svd/README.md` confirms this source worsens the common 1000-1200 Hz 70-90 deg RMS from 6.963 dB for the current baseline to 17.032 dB.
- Split-discrete source hyperparameter sweep: `docs/l22mg-source-cv-split-discrete-sweep/README.md` runs a Juan-only leave-one-angle-out sweep over 152 finite split front/rear monopole-cloud candidates, varying source half-depth, radial support, ridge regularization, and SVD truncation. No candidate passes the Juan-only recommendation threshold. The best row is `sweep-split-discrete-d65-r0_20_40_60_80_95-reg1e-06`, with held-out worst-side RMS 6.729 dB over 300-1200 Hz. That older sweep is not yet regenerated for the corrected 0.50 m radius; the current compact 0.50 m wide/SVD row is 8.810 dB.
- Split-discrete smoothness regularization sweep: `docs/l22mg-source-cv-split-discrete-smoothness/README.md` adds an adjacent-source Tikhonov smoothness penalty to the finite split cloud and reruns Juan-only leave-one-angle-out CV. Smoothness does not help: the no-smooth d65/r0-20-40-60-80-95 baseline remains best at 6.729 dB held-out worst-side RMS, while the best smoothed row rises to 6.756 dB and all rows remain `rejected_weak_cv`. This rules out simple adjacent-source smoothness regularization as the missing source constraint.
- Best split-discrete sweep BEM check: `docs/l22mg-bem-passive-um-d65-r20-95-hotband/README.md` reruns that best Juan-only sweep candidate over 1000-1200 Hz with the current Andres-mounted geometry and q7-near dense BEM. It is not an acceptance run, but it rules out this hyperparameter path as a high-angle fix: on the common 1000-1200 Hz overlap, `docs/l22mg-high-angle-residual-d65-r20-95/README.md` shows 70-90 deg RMS worsening from 6.963 dB for the current corrected wide/SVD baseline to 7.893 dB for d65/r20-95, while 0-60 deg changes only from 1.540 to 1.462 dB. The 1070 Hz / 80 deg residual remains the dominant failure.
- Asymmetric split-discrete support diagnostic: current code now supports independent front/rear depth and ring radii for `--source-model split-discrete` via `--split-discrete-front-depth-mm`, `--split-discrete-rear-depth-mm`, `--split-discrete-front-ring-radii-mm`, and `--split-discrete-rear-ring-radii-mm`. This is still a Juan-only source-support parameterization, not an Andres-derived correction. The existing asymmetric sweep was generated before the 0.50 m correction and remains a source-support diagnostic, not current acceptance evidence; asymmetric front/rear support is available and auditable, but it has not revealed a hidden high-angle acceptance path.

## Mesh Convergence Status

- Feature-aware auto mesh smoke: `docs/l22mg-bem-auto-feature-mesh-smoke/README.md` verifies the simulator's `--bem-auto-mesh` path now derives BEM broad/local spacings from both wavelength and active baffle features. For an Andres-mounted 1200 Hz target it switches to `delaunay-local`, broad h = 23.75 mm from the L22 cutout diameter/8 cap, boundary/local h = 13.67 mm from the upper-mid feature diameter/6 cap, local refinement width = 36.6 mm, and passive UM face mesh h = 13.67 mm. This is a mesh-sizing policy smoke, not a convergence proof or acceptance run.
- Active-source-surface auto sampling: `--bem-auto-mesh` now also sizes H1659 prescribed-Neumann active-source-surface azimuth sampling from the source outer acoustic diameter and lambda/10 chord length, independently from the baffle local h. At a 2 kHz target, the compact H1659 surface is raised from 16 to 33 azimuth samples. Auto-mesh now also records and, unless explicitly overridden, applies a local refinement band width target of `max(2x local h, 2x baffle thickness, lambda/2 capped by L22 cutout radius)`, so future auto-mesh reports expose whether edge/cutout refinement was only narrow-thickness refinement or a wavelength-scale band. This closes a mesh-policy gap for active-surface/feature-proxy diagnostics; it is still not BEM convergence proof or acceptance evidence.
- Delaunay feature-clearance mesh smoke: `docs/l22mg-bem-feature-clearance-mesh-smoke/README.md` adds an explicit `--bem-feature-clearance-factor` for dense-BEM Delaunay meshes. Boundary rings are still sampled, but interior/local seed points are kept away from baffle edges and cutouts by a fraction of the local spacing. At h16/local9.6 on the current Andres-mounted cutout geometry, the default 0.25 clearance improves minimum triangle angle from 0.222 deg to 11.310 deg and max edge ratio from 90.1 to 5.1 while reducing panels from 4,450 to 4,048. `docs/l22mg-bem-feature-clearance-cli-smoke/README.md` verifies the CLI/HDF5/report path exports the same setting and mesh-quality metadata. `docs/l22mg-bem-feature-clearance-lobe-probe/README.md` then applies the same guard to the 1697 Hz / 70 deg h18/h16 q7 lobe probe: max normalized change drops from 1.916 dB unguarded to 1.008 dB guarded, and RMS change drops from 0.634 dB to 0.320 dB. This is a real numerical improvement, but still fails the 0.5 dB max-change convergence gate, so it is not validation evidence.
- Driver-frame auto-mesh smoke: `docs/l22mg-auto-mesh-driver-frame-mounting-holes-smoke/README.md` verifies `--bem-auto-mesh` now sizes the optional H1659 driver-frame submesh separately from the baffle local mesh. With a 2 kHz auto-mesh target and screw pockets enabled, the baffle local h stays at 13.67 mm from the UM feature cap while the driver-frame azimuth count is raised from 24 to 41 from the front-flange/lambda10 chord rule. This avoids both failure modes: silently ignoring active-driver frame detail, or forcing the entire baffle to millimeter-scale panels because of 8.8 mm screw pockets. The smoke is only 300-310 Hz q1 and is not validation evidence.
- Driver-STL feature audit/remesh proxy: `docs/l22mg-driver-stl/README.md` welds the H1659 STL topology, extracts a feature-edge graph, and exports a bounded feature proxy OBJ. With a 0.001 mm weld tolerance and 30 deg crease threshold, the raw STL has 5,138 welded vertices, 9,888 triangles, 15,024 unique edges, and 4,026 feature edges over 9.52 m of total feature-edge length. The raw STL triangle quality is poor for direct dense BEM use: minimum angle 1.18 deg, p01 minimum angle 1.18 deg, and max edge ratio 48.7. The refreshed feature proxy preserves the generated STL's circular acoustic profile, flange footprint, screw pockets, basket rings, six struts, and motor envelope at 1,620 triangles, about 0.164x the raw STL panel count, with no degenerate triangles and max edge ratio 9.3. It explicitly omits the 0.6 mm thin flange sidewalls to avoid long skinny constant-panel triangles; that is a labelled mesh-quality approximation, not a raw-STL solve, not elastic cone physics, and not validation evidence until paired with an accepted solver/source formulation.
- Passive tweeter raised-face diagnostic: current code now supports optional `--passive-tweeter-drivers`, adding two simple raised rigid 47 mm tweeter faces over otherwise closed tweeter patches. `docs/l22mg-passive-tweeter-faces-hotspot/README.md` checks that approximation at the dominant 1070.1 Hz / 80 deg residual using the current wide/SVD source and current Andres-mounted UM cutout geometry. It does not fix the null: the one-frequency normalized residual is +25.680 dB at 80 deg, through-80 RMS is 9.707 dB, and through-60 RMS is 1.714 dB. The report/HDF5 label the tweeter faces explicitly, so this is an auditable geometry diagnostic, not an Andres-derived correction or acceptance run.
- Active-driver acoustic feature-proxy smoke: `docs/l22mg-active-feature-proxy-explicit-smoke/README.md` verifies the new explicit `--active-driver-feature-proxy` path. The output HDF5 records `active_driver_feature_proxy_requested=True`, `active_driver_feature_proxy_included=True`, `include_driver_frame=True`, and `driver_frame_include_mounting_holes=True`; the report states this is a rigid H1659 frame/flange/motor scatterer plus a Juan-fitted prescribed-Neumann source surface, not a scalar correction, not fitted to Andres, not raw-STL BEM, and not elastic FEM-BEM. The simulator feature-proxy path now also defaults the 0.6 mm flange sidewalls off, matching the STL feature-proxy inspection and making that constant-panel mesh-quality approximation explicit; standalone driver-frame diagnostics keep sidewalls on unless disabled. This smoke is only 1000-1001 Hz, uses intentionally coarse q1/180 mm BEM, and fails the available-overlap shape diagnostic at 7.349 dB all-angle RMS, so it is metadata/plumbing evidence only, not validation evidence. Earlier `docs/l22mg-active-feature-proxy-smoke/README.md` verifies the legacy `--include-driver-frame` plus active-surface-source combination is also labelled as the same proxy path.
- Explicit feature-proxy annular hotspot check: `docs/l22mg-active-feature-proxy-annular-hotspot/README.md` runs the explicit feature-proxy path at the dominant 1070.1 Hz / 80 deg residual using Andres-mounted passive geometry, h20/local12 q7-near BEM, and the best bounded annular split active-surface source settings from Juan-only CV. It is negative evidence: the report matches `sweep-split-active-surface-compact-annular-az16-gap30-q3-reg1e-06` in the annular sweep CSV and records `rejected_bad_insample_fit`; the one-frequency normalized residual is +42.444 dB at 80 deg, through-80 RMS is 18.056 dB, and through-60 RMS is 5.897 dB. This rules out the current explicit feature-proxy plus annular source formulation as a high-angle fix, but it is still a hotspot diagnostic rather than full-band acceptance evidence.
- Mesh-quality metadata smoke: `docs/l22mg-mesh-quality-metadata-smoke/README.md` verifies the dense-BEM solver now writes mesh edge-length and triangle-quality metadata into the simulation HDF5 and report. The smoke is intentionally coarse, 300-310 Hz only, and not validation evidence; it exists to make mesh quality auditable in future convergence runs.
- Earlier sparse check: `docs/l22mg-bem-local-h24-h22-conv-1200-q3-d25-t1905/README.md` used 6 points/octave and found h24/local14.4 versus h22/local13.2 max normalized change = 0.394 dB. That is no longer treated as acceptance-grade convergence evidence.
- High-resolution h24/local14.4 versus h22/local13.2 check: `docs/l22mg-bem-local-h24-h22-conv-1200-q3-d25-t1905-48ppo/README.md`, 48 points/octave, max normalized change = 0.835 dB at about 899 Hz / 80 deg, RMS = 0.084 dB. This fails the 0.5 dB max-change target.
- High-resolution h22/local13.2 versus h20/local12.0 check: `docs/l22mg-bem-local-h22-h20-conv-1200-q3-d25-t1905-48ppo/README.md`, 48 points/octave, max normalized change = 1.391 dB at about 939 Hz / 80 deg, RMS = 0.092 dB. This also fails the 0.5 dB max-change target.
- Targeted lobe probe: `docs/l22mg-bem-mesh-lobe-probe/README.md` reruns only 850-985 Hz and confirms the hot spot is localized near 80 deg. The h20/local12.0 versus h18/local10.8 probe still reaches 1.185 dB at about 899 Hz / 80 deg, so finer constant-element panels have not removed the high-angle lobe sensitivity.
- Quadrature sensitivity probe: `docs/l22mg-bem-mesh-lobe-probe-q1q3/README.md` compares q1 and q3 integration at fixed mesh. It shows same-mesh changes above 0.5 dB at the same hot lobe: h22 worst = 2.232 dB at about 899 Hz / 80 deg, h20 worst = 0.574 dB at 875 Hz / 80 deg, and h18 worst = 1.145 dB at about 899 Hz / 80 deg. q3 remains required, but q3 alone is not a convergence proof.
- Higher-quadrature hot-spot probe: `docs/l22mg-bem-mesh-lobe-probe-q3q7-hotspot/README.md` compares q3 and q7 integration at fixed mesh for 875, 899, and 939 Hz. It still reaches 1.174 dB at about 899 Hz / 80 deg on h18/local10.8 and 1.116 dB at about 939 Hz / 80 deg, so q3 is not acceptance-grade integration for the hot lobe. The q7 h20/local12.0 versus h18/local10.8 mesh row still reaches 0.894 dB at about 899 Hz / 80 deg, so higher quadrature alone does not close the convergence gap.
- Near-panel integration probe: `docs/l22mg-bem-mesh-lobe-probe-q7-near/README.md` adds local q7 source-panel subdivision for close panel pairs. With one subdivision and distance factor 2.5, h22/local13.2 versus h20/local12.0 drops below the 0.5 dB lobe gate in the 850-985 Hz probe, but h20/local12.0 versus h18/local10.8 still reaches 0.532 dB at 920 Hz / 80 deg. This is a major reduction from the non-near q7 h20/h18 0.894 dB hot spot, but it is still not full convergence.
- Deeper near-panel subdivision is not automatically better: `docs/l22mg-bem-mesh-lobe-probe-q7-near2-hotspot/README.md` shows q7 near2 improves h20/local12.0 versus h18/local10.8 at 899-939 Hz, but worsens h22/local13.2 versus h20/local12.0 to 0.622 dB at about 899 Hz / 80 deg. Near-panel integration therefore needs a principled rule, not tuning to a single lobe.
- Corrected passive-geometry smoke: `docs/l22mg-bem-andres-mounted-q7-near-hotspot/README.md` reruns the q7/near hotspot probe with passive aperture treatment `andres-mounted`, meaning the UM/tweeter positions are closed rigid patches rather than open holes. That artifact predates the raised passive-UM face mesh, but it remains useful as a flat-mounted reference. The three-frequency probe still fails the 0.5 dB gate: h22/local13.2 q7-near1 versus h20/local12.0 q7-near1 reaches 0.766 dB at about 899 Hz / 80 deg, and h20/local12.0 q7-near1 versus h18/local10.8 q7-near1 reaches 0.530 dB at 920 Hz / 80 deg.
- Passive-UM raised-face probe: `docs/l22mg-bem-passive-um-q7-near-hotspot/README.md` adds the parameterized rigid UM face while keeping tweeters as closed solid patches. This improves the h20/local12.0 q7-near1 versus h18/local10.8 q7-near1 920 Hz hotspot from 0.530 dB to 0.317 dB, but the h22/local13.2 q7-near1 versus h20/local12.0 q7-near1 row still reaches 0.651 dB at about 899 Hz / 80 deg. The raised passive-UM geometry is therefore more faithful to Andres' mounted-driver condition, but still not full convergence.
- Pre-cutout current-source retimed hotspot probe: `docs/l22mg-bem-wide-svd-retimed-hotspot-q7-near/README.md` reruns selected high-angle residual hot spots, including 1070.1 Hz, using the wide/SVD source (45 mm half-depth, radii 0/35/70/95 mm, rcond 1e-5), raised passive UM over the older solid patch, closed tweeter patches, Andres UM-height mic, and 19.05 mm baffle. Raw q7 h20/local12.0 versus h18/local10.8 still reaches 0.548 dB at 1070.1 Hz / 90 deg, but q7-near1 h20/local12.0 versus h18/local10.8 drops to 0.389 dB. At 1070.1 Hz / 80 deg, the near1 h20/h18 normalized difference is -0.217 dB, much smaller than the measured/model residual peak, so the 1070 Hz / 80 deg validation failure is not explained by mesh movement alone. This probe should be rerun with `mounted_um_cutout=True` before using it as the current geometry convergence evidence.
- Exact current-geometry full-band convergence: `docs/l22mg-bem-passive-um-cutout-widecloud-svd1e-5-h22-h20-conv-q7-near-1200-12ppo/README.md` reruns the current mounted-UM-cutout wide/SVD source over 300-1200 Hz with q7 near-panel integration and compares h22/local13.2 against h20/local12.0. The default h22 case has max normalized-polar mesh change 0.210 dB at about 1133 Hz / 60 deg, RMS 0.058 dB, through-80 max 0.210 dB, and F90 RMS 0.078 dB. This passes the requested 0.5 dB mesh gate for the h22-versus-h20 check. It does not fix validation shape: normalized polar RMS remains 4.068 dB, through-60 RMS 1.341 dB, and through-80 RMS 3.905 dB.
- Exact current-geometry h20/h18 confirmation: `docs/l22mg-bem-passive-um-cutout-widecloud-svd1e-5-h20-h18-conv-q7-near-1200-12ppo/README.md` repeats the same corrected geometry with the h20/local12.0 baseline and h18/local10.8 comparison. The default h20 case has max normalized-polar mesh change 0.273 dB at 1200 Hz / 80 deg, RMS 0.067 dB, through-80 max 0.273 dB, and F90 RMS 0.098 dB. This also passes the 0.5 dB mesh gate. It slightly changes the validation numbers but still fails shape: normalized polar RMS is 4.053 dB, through-60 RMS 1.327 dB, and through-80 RMS 3.889 dB.
- Hot-spot matrix conditioning: `output/l22mg-bem-mesh-lobe-numerics.csv` checks the dense Neumann operator at 898.984 and 938.786 Hz for h24, h22, and h20 local meshes. Condition numbers are only about 10-11, so the lobe sensitivity is not explained by a near-singular BEM matrix at those hot spots.
- The exact current-geometry h22/h20 and h20/h18 q7-near sweeps now pass the 0.5 dB 300-1200 Hz max-change gate. The 300-1200 acceptance blocker is no longer mesh movement at these resolutions; it is the 70-90 deg validation shape.

## Linear Solver Residual Status

- The simulator now exposes `--bem-linear-solver direct|gmres|gmres-matrix-free` and writes BEM linear-solver settings plus max/RMS residual summaries into the simulation HDF5 root metadata. The generated README also states the linear solver and residual status.
- Smoke evidence: `docs/l22mg-bem-linear-solver-direct-smoke/README.md`, `docs/l22mg-bem-linear-solver-gmres-smoke/README.md`, and `docs/l22mg-linear-solver-smoke-summary/README.md`.
- The smoke is intentionally coarse and covers only 990-1010 Hz, so it is not an acceptance run. It checks only that the dense linear solve path is auditable and that direct LU and GMRES agree on the same dense system.
- Direct LU residual in that smoke: max relative residual 9.823e-16. GMRES residual: max relative residual 5.813e-09, max info 0, max iterations 29. Direct-vs-GMRES exported magnitude difference is 2.491e-07 dB max.
- Matrix-free GMRES smoke: `docs/l22mg-matrix-free-gmres-smoke-summary/README.md` verifies the new `gmres-matrix-free` path against the assembled dense direct solve on the same bounded 990-1010 Hz coarse setup. The matrix-free run has info 0, max relative residual 9.009e-09, max 30 iterations, and direct-vs-matrix-free exported front magnitude agreement 5.334e-07 dB. This removes dense operator storage for targeted larger diagnostics, but it is still an O(N^2) dense-kernel matvec, not FMM-BEM or H-matrix acceleration.
- Convergence-row residual smoke: `docs/l22mg-bem-convergence-residual-smoke/README.md` verifies the main `bem_mesh_convergence_metrics.csv` path now writes per-case linear-solver residual columns. Its coarse 990-1010 Hz run is not acceptance evidence, but it reports direct-solve max relative residual 1.036e-15 across convergence cases.
- Mesh-lobe probe residual smoke: `docs/l22mg-mesh-lobe-residual-smoke/README.md` verifies `scripts/probe_l22mg_mesh_lobes.py` now records coarse/reference linear-solver residuals in `mesh_lobe_probe_summary.csv` and prints the worst probed residual in the README. Its direct-solve max relative residual is 7.791e-16.
- This separates linear-solve error from the real remaining blockers. It does not fix the Andres shape failure and does not replace the failed 300-2000 constant-panel mesh convergence. GMRES in the current backend is still a dense or matrix-free dense-kernel audit/control path, not FMM-BEM or H-matrix acceleration.

## Measurement Geometry

- Juan nude source measurement distance in HDF5: 0.50 m front and rear. `polar_data_loader.py` promotes note-derived measurement location into structured HDF5 angle attrs on save, and `scripts/simulate_l22mg_baffle.py` rejects a silent mismatch between that structured Juan distance and `--naked-source-radius-m`; `--allow-naked-source-radius-mismatch` is required for an explicitly labelled legacy/diagnostic run.
- Current mounted-baffle validation target: Juan's same-room/same-driver LX521 top-baffle raw/no-crossover HDF5, `output/data/polar_data_juan_lx521_top_raw.h5`, driver `L22MG (LX521 top raw)`. It carries `measurement_distance_m=0.50` and `measurement_height_reference=l22mg`, so the default validation mic resolves to 50 cm exactly at LM/L22MG height rather than Andres' UM-height point.
- Andres validation geometry remains an explicit legacy target: 1 m horizontal radius at upper-mid height, +165 mm relative to L22 center.
- Andres L22MG timing audit: the legacy published-data validation target is the published polar explorer parity HDF5, `output/data/polar_data_andres_early_peak_legacy.h5`, and it is accepted only because `scripts/verify_andres_published_parity.py` proves the embedded/published explorer values match it at 1004 Hz. The first-lobe, strongest-lobe, and direct-gate HDF5 variants remain diagnostics unless the published explorer is regenerated from that same HDF5 in the same commit.
- Diagnostic first-lobe audit: `docs/andres-l22mg-ir-peak-audit/README.md` selects the first strong near-reference lobe at 70/80/90 deg, about 0.045/0.047/0.040 ms, and does not use the raw -12 ms early events or the later 0.128/0.131/0.123 ms absolute maxima. The old strongest-lobe audit is preserved only as legacy/diagnostic evidence in `docs/andres-l22mg-ir-peak-audit-strongest-legacy/README.md`; it shows why the absolute maximum is a bad high-angle timing anchor.
- Pipeline guard: the Andres pipeline default HDF5 name is the published-parity file, `polar_data_andres_early_peak_legacy.h5`, but `run_pipeline.py` refuses to overwrite it from the current loader unless `--allow-published-parity-hdf5-overwrite` is supplied. Use an alternate `--hdf5-output` for first-lobe/direct-gate diagnostics, or regenerate the published explorer in the same commit before changing the canonical file.
- Simulator target guard: `scripts/simulate_l22mg_baffle.py` now defaults to the Juan LX521 top raw L22MG target and refuses unknown/diagnostic targets unless an explicit diagnostic override is passed. Explicit Andres published-parity runs should use `--validation-preset andres-published-parity`; they are accepted only when the HDF5 is proven to match the published polar explorer. First-lobe, strongest-lobe, and raw direct-gate HDF5 files cannot silently become acceptance targets.
- Target robustness audit: `docs/l22mg-target-robustness/README.md` compares diagnostic Andres target variants against the published-parity reference after each is normalized to its own 0 deg response. The first-lobe diagnostic target moves only 0.040 dB RMS through 60 deg over 300-1200 Hz, but moves 4.326 dB RMS through 80 deg and 9.546 dB RMS over 70-90 deg, with a maximum -42.6 dB swing at 639 Hz / 70 deg. This does not exclude data; it shows that all-angle/high-angle acceptance is highly target-processing sensitive while through-60 is much more robust.
- Late-window sensitivity audit: `docs/l22mg-andres-late-window-sensitivity/README.md` recomputes raw-IR normalized polars with the same first-strong peak and compares shorter right gates to the 3.0 ms gate. The 0.8 ms-vs-3.0 ms movement is 0.822 dB RMS through 60 deg but 6.424 dB RMS over 70-90 deg, with a +34.8 dB delta at 1074 Hz / 80 deg. This is not an alternate target or correction; it quantifies why the late-window gate remains a blocker and why F90/null-depth cannot be decisive without corroborated Andres high-angle measurements.
- Target polar quality audit: `docs/l22mg-target-polar-quality/README.md` flags the deep measured target nulls that dominate validation. In the canonical published-parity Andres target, the main deep-null cluster is 90 deg / 330 Hz at -42.7 dB normalized, with 26.2 dB adjacent-angle contrast. The diagnostic first-lobe and legacy strongest-lobe variants have different deep high-angle nulls. These rows are not excluded from validation, but they are high-sensitivity target-quality warnings and should be corroborated before treating all-angle failure as clean direct-sound BEM-only residual.
- Andres passive-driver clarification: the upper-mid and both tweeters were physically mounted during Andres' L22MG baffle measurement. The validation geometry should therefore not model those positions as open holes. Current code supports `--passive-aperture-treatment andres-mounted`, which closes passive positions; open passive holes are now only a diagnostic.
- For BEM with `andres-mounted`, the simulator now defaults to a parameterized rigid passive-UM face (`--passive-um-driver`, default diameter 82 mm, height 4 mm, mesh h 16 mm). The tweeter locations remain closed solid patches because we do not yet have a useful tweeter faceplate/basket model in the dense-BEM mesh.
- Baffle-transfer metrics subtract the nude equivalent source evaluated at the same validation mic height.
- Rear level correction: none. Juan's rear magnitude is used as stored.
- Low-frequency rear-balance diagnostics: `docs/l22mg-lowfreq-null-rear-balance/README.md` now uses the corrected 0.50 m Juan source radius and splits the Andres published-parity h1659-modal-full2 BEM into front-only and rear-only responses at 338/344.6 Hz. A free complex rear scalar can force the published 90 deg null, but only with about +6.3 to +7.0 dB rear magnitude and about -61 to -62 deg phase; the Juan source-constraint check rejects it because it moves measured rear level by up to +7.31 dB and phase by about 60 deg. The current Juan-specific companion `docs/l22mg-juan-top-lowfreq-null-rear-balance/README.md` asks the same question at the 300.293 Hz / 75 deg top-baffle null. A scalar can match 75 deg alone, but it requires +9.53 dB rear level and -164.8 deg phase, violating Juan rear level/phase by +9.96 dB / 162 deg; fitting 75-90 deg still leaves 6.000 dB RMS and requires +10.73 dB / -167.4 deg. Both `rear_scalar_verdict.csv` files mark the target-fitting scalar rows `rejected_diagnostic`: this is diagnostic sensitivity evidence only, not a validation correction.
- Validation alignment: one scalar gain and one delay only.

## Normalization Rationale

- Juan and Andres absolute SPL levels are not assumed to be matched, so the primary validation compares normalized polar shape: SPL(theta)-SPL(0) at each frequency.
- The single scalar gain and delay align the validation comparison only; they are not source-fit parameters and cannot change normalized polar or directivity errors.
- The gate summary now also exports complex relative RMS after that same one gain/delay alignment. This exposes the optional complex-pressure residual without adding any source, rear, angle, or band-specific correction.
- On-axis SPL error after scalar gain is reported separately from the normalized-polar acceptance result.
- Baffle-transfer metrics use the same dataset-level reference alignment as validation before subtracting the nude equivalent source at Andres mic height. This is not a rear/source level correction and does not change normalized polar or directivity errors.

## Current Validation Result

The current strict gate surface for the same-room/same-driver workflow is `docs/l22mg-validation-gate-summary/README.md`, using Juan's L22MG top-baffle target at 50 cm and LM/L22MG height. It is regenerated from the current Juan q7/near candidate set, with detailed companion copies for the compact2, full2, compact3, full4-SVD, and profile-ring-full solid-passive source candidates. The aggregate compact2 row, `q7near-solid-h42-h36`, passes target provenance, full 300-1200 Hz coverage, exact target-angle modeling, BEM linear-solver residual, Juan-only source-CV, source off-plane-not-required, contour, and validation-decomposition gates. It still fails acceptance because all-angle normalized RMS is 4.233 dB, mesh max movement is 2.344 dB, BEM mesh-target wavelength sizing fails because boundary/local h = 32.00 mm exceeds the 1200 Hz lambda/10 target of 28.58 mm, the target measurement-quality gate is `not_proven`, and passive-geometry parity is `not_proven`. The newer q7 target-averaged compact2 row in `docs/l22mg-bem-juan-top-h1659-modal-compact2-solid-passive-h32-h21-h28-h18-q7near-targetavg7-meshtarget-conv-smoke-gates/README.md` improves those numbers to 3.920 dB all-angle RMS, 0.672 dB mesh movement, and mesh-target pass, but it still fails the 1.5 dB shape and 0.5 dB all-angle mesh-convergence gates. Through-60/through-80 RMS for that newer row is 0.875/3.491 dB, and the all-angle blocker remains the measured 300.293 Hz / 75 deg null. The front/rear consistency audit shows that blocker is front-side isolated relative to the rear top-baffle measurement, with -21.300 dB front-minus-rear baffle-transfer delta at the same point; the default gate summary now surfaces this as `target F/R = warning` and blocks acceptance as not proven until repeatability/provenance is resolved. The other recommended finite H1659 source rows are all worse by mounted-baffle validation shape: full2 4.270 dB, compact3 5.410 dB, full4-SVD 10.911 dB, and profile-ring-full SVD/no-SVD 9.254/9.265 dB all-angle RMS.

Andres published-parity gate summaries remain available only as explicit legacy comparison surfaces. The aggregate Andres gate report is now `docs/l22mg-validation-gate-andres-published-parity/README.md`, generated with `scripts/summarize_l22mg_validation_gates.py --artifact-preset andres-published-parity`; older broad diagnostics remain available with `--artifact-preset legacy-diagnostic`. Diagnostic first-lobe, direct-gate, and strongest-lobe comparisons are retained separately as target-sensitivity evidence and cannot become acceptance targets unless the published explorer is regenerated from the same HDF5. Those gates check published-parity target provenance, full 300-1200 Hz coverage where available, normalized polar RMS <= 1.5 dB, dense-BEM mesh convergence <= 0.5 dB, BEM mesh-target wavelength sizing metadata, BEM linear-solver residual metadata, the audit surface, the Juan-only source-CV gate, and the source off-plane generalization gate. Target robustness and late-window sensitivity are context only, not alternate acceptance targets.

The simulator writes `validation_decomposition.csv` and a `/validation_decomposition` HDF5 group for each run. Current Juan-target artifacts use those outputs for per-frequency/angle mounted-target SPL, gain-aligned model SPL, synthetic nude reference SPL at the validation mic, normalized polar residual, and baffle-transfer residual. This is an audit output only; it adds no target-derived source/rear correction.

The decomposition backfill utility supports batch/default-artifact mode and also refreshes strict timing attrs plus `validation_metrics.csv` from the audited target HDF5. The mesh-target backfill utility independently annotates stored BEM artifacts with wavelength-sizing metadata without rerunning acoustics. The default gate-summary set now follows the current Juan q7/near candidate family and reports decomposition present for all ten summarized rows, so the remaining gate failures are due to target-quality warnings, mesh convergence, failed mesh-target sizing, passive-geometry provenance, and polar-shape evidence rather than missing audit surfaces.

The current full-band baseline was generated before that export and strict timing metadata existed, so `scripts/backfill_l22mg_validation_decomposition.py` has backfilled the same decomposition, strict timing attrs, and validation metrics into its stored HDF5 and CSV without rerunning BEM. The backfilled metric reproduces the current 4.053 dB normalized RMS while changing the clean-timing count from 10 to 4 angles, confirming this is an audit-surface/timing-metadata update rather than a simulation change.

Current mounted-UM-cutout wide/SVD baseline:

- Full 300-1200 Hz coverage: yes.
- Normalized polar RMS 300-1200 Hz: 4.053 dB.
- Legacy clean-window subset RMS 300-1200 Hz: 1.035 dB, but that subset excludes 40-90 deg late-window warnings and is not an acceptance metric. The current gate treats the direct timing anchor separately from late-window target contamination.
- Normalized polar RMS through 60 deg 300-1200 Hz: 1.327 dB.
- Normalized polar RMS through 80 deg 300-1200 Hz: 3.889 dB.
- Worst normalized polar residual 300-1200 Hz: +25.451 dB at 1070.1 Hz / 80 deg; through-60 max is 3.976 dB at 1008.9 Hz / 40 deg.
- Baffle-transfer RMS 300-1200 Hz: 6.445 dB.
- F90-F0 mean error 300-1200 Hz: +0.185 dB; F90-F0 RMS error: 5.305 dB.
- DI RMS error 300-1200 Hz: 1.185 dB.
- On-axis RMS error after scalar gain alignment 300-1200 Hz: 5.771 dB.
- Mesh convergence: h20/local12.0 versus h18/local10.8 q7-near passes, max normalized change 0.273 dB over 300-1200 Hz.
- Juan-only source CV for these stored artifacts is now not proven in the gate summary because their HDF5 metadata carries the old 0.75 m source radius. The same source parameters rerun in the corrected 0.50 m source-CV table give 8.810 dB worst-side held-out normalized SPL RMS over 300-1200 Hz, rank 26 of 29 in the compact source-CV set.
- Source off-plane gate: fail. The mapped wide/SVD source has 1.601 dB z=0-to-UM-height movement and 14.751 dB legacy-reference source-family spread over 70-90 deg; the Juan-recommended h1659-modal-full2 full-band candidate also fails with 13.406 dB spread against the eligible recommended-source ensemble. Juan's horizontal polars therefore do not yet prove the 3D incident field at Andrés' UM-height mic.

This fails the requested normalized polar RMS target of <= 1.5 dB over 300-1200 Hz. `docs/l22mg-validation-gate-summary/README.md` now reports `width_sweep_status=qualitative_only` for these failed-baseline artifacts, so width sweeps remain diagnostics rather than accepted LX521 width behavior.

Measurement-geometry provenance is now explicit in the HDF5 files, not just in remembered notes. `docs/l22mg-measurement-geometry-provenance/README.md` audits Juan's L22MG naked front/rear data as 0.50 m measurements, Juan's LX521 top-baffle raw L22MG/L10NEO/multi-driver captures as 0.50 m at LM/L22MG height, and Andres' canonical published-parity L22MG target as 1.0 m at UM height. The Juan top-baffle file `output/data/polar_data_juan_lx521_top_raw.h5` now carries `measurement_distance_m=0.5` and `measurement_height_reference=l22mg` on the relevant driver groups as well as angle groups. The canonical published-parity file `output/data/polar_data_andres_early_peak_legacy.h5` has been backfilled with `measurement_distance_m=1.0` and `measurement_height_reference=um` on the `L22MG` group and all L22MG angle groups; this is provenance metadata only and does not change pressure data or target policy.

The current mesh-converged wide/SVD corrected-geometry baseline reaches the <=1.5 dB target through 60 deg, but all-angle acceptance is still blocked by late-window target contamination, high-angle lobe/null shape, source CV, and source off-plane generalization. The h1659-modal-full2 full-band replay improves through 80 deg to 1.470 dB against the published-parity target and passes its h22/local13.2 vs h20/local12.0 mesh-convergence check at 0.082 dB max change, but all-angle RMS is still 4.193 dB because of the 90 deg low-frequency miss and its source off-plane spread is 13.406 dB against the Juan-CV recommended-source ensemble. The refreshed rear-balance probes show that target-fitted rear gain/phase knobs can mimic single high-angle nulls, including the current Juan 300.293 Hz / 75 deg blocker, but the Juan consistency table exposes the cheat: normalized rear shape cannot reject a uniform scalar, while measured rear level/phase does. The generated `rear_scalar_verdict.csv` files mark those target-fitting scalar rows `rejected_diagnostic`, so this path cannot be read as a candidate acceptance fix. High-angle/F90/null-depth evidence remains diagnostic because late in-window peaks are still flagged and raw-IR short-gate sensitivity is about 6.4 dB RMS over 70-90 deg.

## Primary 300-2000 Hz Diagnostic

- Report: `docs/l22mg-bem-passive-um-cutout-widecloud-svd1e-5-h20-h18-conv-q7-near-2000-12ppo/README.md`.
- HDF5: `output/l22mg-bem-passive-um-cutout-widecloud-svd1e-5-h20-h18-conv-q7-near-2000-12ppo/polar_data_l22mg_lx5214_baffle_sim.h5`.
- Scope: corrected Andres-mounted geometry, UM-height mic, 19.05 mm baffle, current wide/SVD source, h20/local12.0 mesh, q7 quadrature, and q7 near-panel integration from 300-2000 Hz, with h18/local10.8 as the comparison mesh.
- This is not a new acceptance result. The formal acceptance gate remains the 300-1200 Hz shape plus dense-BEM mesh-convergence gate above.
- Full 300-2000 Hz diagnostic result: normalized polar RMS 5.334 dB, through-60 RMS 2.638 dB, through-80 RMS 5.222 dB, baffle-transfer RMS 9.801 dB, DI RMS 2.241 dB, -6 dB beamwidth RMS 18.545 deg, and on-axis RMS after scalar gain alignment 11.088 dB.
- Primary-band h20/h18 convergence fails: max normalized-polar mesh change is 4.065 dB at about 1697 Hz / 70 deg, with RMS 0.248 dB and through-80 max 4.065 dB. The same artifact still passes the 300-1200 mesh gate at 0.273 dB max. So the current mesh is adequate for the 300-1200 acceptance check but not for 300-2000 claims.
- The h22/h20 primary-band check also failed, but less severely: `docs/l22mg-bem-passive-um-cutout-widecloud-svd1e-5-h22-h20-conv-q7-near-2000-12ppo/README.md` found 2.315 dB max change at the same 1697 Hz / 70 deg region. The nonmonotonic h22/h20 to h20/h18 behavior means this high-frequency lobe needs finer/higher-order or accelerated BEM before 2 kHz results are acceptance-grade.
- Targeted 1697 Hz h16/h14 probes confirm this is not solved by one more dense constant-panel refinement. `docs/l22mg-bem-mesh-lobe-probe-q7-near-h16-1697/README.md` found h18/local10.8 q7-near1 versus h16/local9.6 q7-near1 still moves 1.376 dB at 70 deg. `docs/l22mg-bem-mesh-lobe-probe-q7-near2-h16-1697/README.md` found h18/local10.8 q7-near2 versus h16/local9.6 q7-near2 still moves 1.710 dB. `docs/l22mg-bem-mesh-lobe-probe-q7-near2-h14-1697/README.md` found h16/local9.6 q7-near2 versus h14/local8.4 q7-near2 still moves 2.368 dB. Fixed-mesh q7-to-near2 changes at the same lobe are still about 2.0-3.3 dB, so the current near-panel quadrature rule is also not stable enough for 300-2000 acceptance claims.
- Wider local-refinement check: `docs/l22mg-bem-mesh-lobe-probe-q7-near-width80-h16-1697/README.md` reruns the h18/local10.8 versus h16/local9.6 q7-near1 probe with local refinement width widened from 36.6 mm to 80 mm. It still fails, with max normalized-polar movement 1.494 dB at 1697.1 Hz / 70 deg and fixed-mesh q7-to-near1 changes of 2.587-3.087 dB. Direct-solve residuals are around 2.6-3.1e-15. This rules out an overly narrow 36.6 mm local-refinement band as the main cause of the primary-band lobe instability.
- Target-panel averaging check: `docs/l22mg-bem-mesh-lobe-probe-q7-near-targetavg3-h16-1697/README.md` adds q3 target-panel normal-trace averaging to the h18/local10.8 versus h16/local9.6 1697.1 Hz probe. It still fails: q7-near1 mesh movement is 2.497 dB at 70 deg, and fixed-mesh q7-to-near1 changes remain 1.541-2.468 dB. Direct-solve residuals remain around 2.5-3.0e-15. This rules out centroid target collocation as the main cause of the 1697 Hz primary-band lobe instability.
- The 300-1200 metrics in the same h20 run match the h20 acceptance diagnostic: normalized polar RMS 4.053 dB, through-60 RMS 1.327 dB, and through-80 RMS 3.889 dB. The additional 1200-2000 Hz span therefore worsens the primary-band comparison rather than hiding the existing high-angle issue.

## Dense Qualitative Width Sweep

- Deliverable rollup: `docs/l22mg-width-sweep-deliverable/README.md` verifies the current corrected-geometry sweep includes all required widths (205/305/405 mm) and all recommended widths (205/255/305/355/405 mm), with corrected 0.50 m Juan source radius.
- Report: `docs/l22mg-bem-juan-top-h1659-modal-compact2-current-width-sweep-h42-h28-q7near-targetavg7/README.md`.
- Gate summary: `docs/l22mg-bem-juan-top-h1659-modal-compact2-current-width-sweep-h42-h28-q7near-targetavg7-gates/README.md`.
- HDF5: `output/l22mg-bem-juan-top-h1659-modal-compact2-current-width-sweep-h42-h28-q7near-targetavg7/polar_data_l22mg_lx5214_baffle_sim.h5`.
- Settings use the current Juan top-baffle target at 0.50 m and LM/L22MG height, exact 0/15/30/45/60/75/90 deg target angles, target-neutral solid passive positions (`passive-aperture-treatment=none`), h42/boundary28/local28 mesh, q7 quadrature, q7 near-panel integration, and q7 target-panel normal-trace averaging. This sweep does not rerun a mesh convergence pair inside the invocation.
- The 305 mm baseline still fails acceptance: normalized polar RMS 300-1200 Hz = 4.214 dB, baffle-transfer RMS = 4.408 dB, DI RMS = 0.721 dB. The sweep is therefore qualitative current-radius evidence, not accepted LX521 width behavior.
- Superseded stale-radius width-sweep reference: `docs/l22mg-width-sweep-stale-radius-gate-smoke/README.md` and `docs/l22mg-bem-passive-um-cutout-widecloud-svd1e-5-h22-width-sweep-q7-near-1200-12ppo/README.md` used the old 0.75 m Juan source radius and remain historical diagnostics only. `docs/l22mg-bem-local-h24-width-sweep-1200-q3-d25-t1905/README.md` used older passive-hole geometry, q3 integration, and the older 0/40/75 mm source support.

| Wmax mm | F90-F0 mean 300-1200 dB | DI mean 300-1200 dB | -6 dB BW median 300-1200 deg | rear/front norm RMS 300-2000 dB |
| ---: | ---: | ---: | ---: | ---: |
| 205 | -19.50 | 5.29 | 113.2 | 0.90 |
| 255 | -18.00 | 5.33 | 112.9 | 0.99 |
| 305 | -17.77 | 5.44 | 111.6 | 1.25 |
| 355 | -18.54 | 5.63 | 108.9 | 1.69 |
| 405 | -18.74 | 5.72 | 107.7 | 2.06 |

## Implication

The latest mesh refinement work moved the dense backend to an auditable local mesh and found that localized high-angle mesh and quadrature sensitivity is strongly reduced by q7 near-panel integration inside the 300-1200 Hz acceptance band, but the current Juan-target h42/local32 versus h36/local27 rows still fail the 0.5 dB mesh gate. The raw Andres `.mdat` saved REW window references still point to later/global lobes at 60-90 deg, so they must not be reused as timing anchors; diagnostic first-lobe/direct-gate HDF5 files remain target-sensitivity checks, not acceptance targets. The low-frequency rear-balance probes show a free rear scalar can reproduce a single target null, but only as a target-fitted gain/phase knob that violates Juan rear level/phase; the Juan 75 deg fit alone needs +9.53 dB / -164.8 deg, and the 75-90 group still misses by 6.000 dB RMS. `rear_scalar_verdict.csv` marks the target-fitting scalar rows `rejected_diagnostic`, so this is rejected as a correction. The Juan-only physical rear-filter diagnostic reaches the same conclusion from the other direction: a smooth bounded rear transfer fitted only to Juan rear cannot change the remaining 3.180 dB rear normalized RMS, so the missing rear behavior is angular/spatial, not a shared scalar filter. The 300-2000 diagnostic is a separate numerical blocker: the 1697 Hz / 70 deg lobe still moves by 1.4-2.5 dB through targeted h16/h14, wider-refinement, and target-panel averaged probes. The current 0.50 m BEM reruns for the finite H1659 Juan-CV recommended sources are now complete and rejected by mapped Juan-target evidence, so the next step is source-surface/driver-geometry improvement and higher-order/adaptive or accelerated BEM before making 2 kHz claims.

## Geometry Diagnostics

- Corrected passive-aperture CLI smoke: `docs/l22mg-andres-mounted-cli-smoke/README.md` verifies the main simulator exports `passive_aperture_treatment=andres-mounted`, `include_passive_holes=False`, and reports the closed-patch approximation.
- Passive-UM contour smoke: `docs/l22mg-contour-passive-um-smoke/README.md` verifies the main simulator exports `passive_um_driver_included=True`, uses the Andres UM-height mic offset, keeps tweeter positions as solid patches, and writes `plots/naked_baffle_model_contours.png`. This is only a 300-360 Hz q1 smoke, not a 300-1200 Hz acceptance run.
- Passive-UM q7/near hotspot probe: `docs/l22mg-bem-passive-um-q7-near-hotspot/README.md` verifies the raised passive-UM BEM path on the 899/920/939 Hz lobe, and confirms it still fails the 0.5 dB convergence gate.
- Mounted-UM cutout correction: current code now represents Andres-mounted UM as an 82 mm cutout with a raised rigid UM face, not a cap over a solid baffle patch. The full 300-1200 Hz artifact `docs/l22mg-bem-passive-um-cutout-widecloud-svd1e-5-h22-q7-near-1200-12ppo/README.md` uses the current wide/SVD source and q7-near h22/local13.2 mesh. Versus the older solid-patch UM face full-band artifact, `docs/l22mg-high-angle-residual-um-cutout-full/README.md` shows 0-60 deg RMS improves from 1.561 to 1.341 dB, 70-90 deg RMS improves from 8.124 to 7.139 dB, and 90 deg-only RMS improves from 7.494 to 5.313 dB. The worst residual remains at about 1070 Hz / 80 deg. This is a real geometry correction, not an acceptance fix.
- Passive tweeter raised-face check: `docs/l22mg-passive-tweeter-faces-hotspot/README.md` adds simple rigid raised faces at the two tweeter positions while keeping their baffle patches closed. It does not explain the measured high-angle null: at 1070.1 Hz the 80 deg residual remains +25.680 dB, versus +25.451 dB in the current full-band baseline decomposition. The current baseline therefore keeps flat closed tweeter patches unless this option is explicitly requested for diagnostics.
- Active L22 flange hotband diagnostic: `docs/l22mg-bem-passive-um-active-face-hotband/README.md` adds the STL-derived surface annulus over 850-1100 Hz. It does not fix the null: hotband normalized RMS is 8.100 dB versus 8.061 dB for the no-active-face baseline over the same band.
- Active L22 low-panel STL-envelope hotband diagnostic: `docs/l22mg-bem-cutout-wide-svd-stl-envelope-hotband/README.md` reruns the coarse revolved STL radius envelope using the current wide/SVD source and corrected mounted-UM-cutout geometry. It worsens the 1000-1200 Hz comparison badly: normalized RMS 9.607 dB, through-60 RMS 4.054 dB, through-80 RMS 9.041 dB, baffle-transfer RMS 9.679 dB, F90-F0 mean error +12.876 dB, DI RMS 4.045 dB, and beamwidth RMS 96.067 deg. `docs/l22mg-high-angle-residual-stl-envelope-current/README.md` shows 70-90 deg RMS rising from 6.965 dB for the current wide/SVD source to 16.411 dB on the common 1000-1200 Hz overlap. The STL envelope remains only an obstruction-sensitivity diagnostic, not a feature-preserving STL solve or acceptance evidence.
- Active L22 feature-aware driver-frame diagnostic: `docs/l22mg-bem-passive-um-driver-frame-hotband/README.md` adds a coarse rigid H1659-derived flange/basket/strut/motor frame using `--include-driver-frame` while deliberately leaving the equivalent-source aperture open. This is an explicit physical obstruction test, not a scalar correction. It worsens the 1000-1200 Hz validation badly: common-overlap 70-90 deg RMS rises from 7.941 dB for the current wide/SVD model to 23.466 dB, 80-90 deg RMS rises from 7.208 dB to 23.148 dB, and 90 deg RMS rises from 5.075 dB to 20.814 dB (`docs/l22mg-high-angle-residual-driver-frame/README.md`). The first coarse rigid frame model is therefore ruled out as a fix for the high-angle residual.
- Driver-frame mounting-pocket smoke: `docs/l22mg-driver-frame-mounting-holes-smoke/README.md` verifies the coarse H1659 frame can now include the six STL-derived flange screw pockets via `--driver-frame-include-mounting-holes`. The smoke is only 300-310 Hz, q1, and not validation evidence; it confirms HDF5/report metadata exports `driver_frame_include_mounting_holes=True` and the solver uses a 1,164-panel coarse frame with mounting pockets, instead of silently treating the flange as a featureless annulus.
- Active prescribed-Neumann piston smoke: `docs/l22mg-bem-active-piston-smoke/README.md` adds `--bem-active-piston-source`, a flat 170 mm source disk inside the L22 cutout with default strength following Juan's 0 deg naked response only. This is a source-surface boundary-condition diagnostic, not an Andres-derived correction and not a Juan-polar source fit. On the 1000-1050 Hz smoke overlap it fails badly: normalized RMS is 10.086 dB all-angle, 3.673 dB through 60 deg, 8.951 dB through 80 deg, and F90-F0 mean error is +17.132 dB. A naive flat active piston therefore under-predicts the measured high-angle null and is ruled out as an immediate fix.
- Active H1659 modal Neumann-surface diagnostic: current code supports `--source-model active-surface-modal`, which fits radial modal normal-velocity amplitudes on an H1659-shaped source surface to Juan's naked polars only, then reuses those amplitudes as a prescribed Neumann boundary in the baffle solve. This is not an Andres-derived correction. The raw-normal corrected bounded 1000-1200 Hz hotband, `docs/l22mg-bem-active-surface-modal-oriented-hotband/README.md`, uses the compact H1659 profile, 3 radial modes, 16 azimuth samples, SVD rcond 1e-5, and dipole rear phase. It fails validation: normalized RMS 6.815 dB, through-60 RMS 2.602 dB, through-80 RMS 6.554 dB, target-above-minus-20 RMS 3.458 dB, and F90-F0 mean error +6.965 dB. It also fails the new source-CV screen as `rejected_bad_insample_fit`, with 7.047 dB held-out worst-side RMS. The earlier `docs/l22mg-bem-active-surface-modal-hotband/README.md` was generated before the active-surface raw-normal fix and should be treated as superseded.
- Active-frame plus active-surface feature proxy: current reports now expose `--active-driver-feature-proxy` as the explicit acoustic feature-proxy switch: rigid frame/flange/motor scattering plus Juan-fitted active H1659 prescribed-Neumann source surface, with mounting pockets forced on. Legacy runs that combine `--include-driver-frame` with active H1659 source surfaces are still labelled as the same proxy path. The explicit annular hotspot check above shows that the best current annular split active-surface proxy worsens the 1070 Hz / 80 deg miss, so this path is not an immediate validation fix. It is still not raw-STL BEM, not elastic cone/suspension coupling, and not an Andres-fitted correction.
- Split active H1659 modal Neumann-surface diagnostic: current code now also supports `--source-model split-active-surface-modal`, which fits independent front/rear prescribed-Neumann H1659 source surfaces to Juan only. The split-source gap is a source-model discretization parameter, not an Andres correction. The best bounded hotband checked here, `docs/l22mg-bem-split-active-surface-measured-m4g30-hotband/README.md`, uses stored Juan rear phase, 4 radial modes, 16 azimuth samples, 30 mm front/rear gap, and SVD rcond 1e-5. It improves F90-F0 mean error to +0.894 dB on 1000-1200 Hz but still fails shape validation: normalized RMS 5.320 dB, through-60 RMS 2.090 dB, through-80 RMS 5.364 dB, target-above-minus-20 RMS 2.634 dB, baffle-transfer RMS 5.697 dB, DI RMS 1.029 dB, and beamwidth RMS 14.097 deg. It now maps to the source-CV row `split-active-surface-compact-m4-az16-gap30-q3-reg1e-06-svd1e-05`, rank 12 of 29, but is `rejected_bad_insample_fit`. This rules out the current split active-surface formulation as an immediate acceptance fix.
- Axisymmetric directivity-table diagnostic: current code supports `--source-model axisymmetric-directivity`, which rotates Juan's measured complex front/rear angular field around the driver axis and propagates it from the corrected 0.50 m measurement radius. This is a no-inversion Juan-only source diagnostic and does not use Andres or Juan top-baffle data as a fit knob. Its Juan-only held-out CV is strong at 1.229 dB worst-side RMS, but it is marked `diagnostic_only`, not a finite source-support recommendation. The current Juan-target BEM diagnostic at `docs/l22mg-bem-juan-top-axisymmetric-directivity-1000-1200-current/README.md` maps to source-decision label `axisymmetric-directivity-juan-current` and rejects it against the canonical target: 5.768 dB normalized RMS over the 1000-1200 Hz overlap, 3.344 dB through 80 deg, and +13.807 dB worst residual at 1000.1 Hz / 90 deg, with passive geometry still `not_proven`. The refreshed Andres published-parity BEM diagnostic at `docs/l22mg-bem-andres-published-parity-axisymmetric-directivity-1000-1200-current/README.md` also rejects it as an acceptance source: 3.912 dB normalized RMS over 1000-1200 Hz, 3.145 dB through 80 deg, and +8.514 dB worst residual at 1199.7 Hz / 80 deg, with source off-plane spread still 13.940 dB.
- Axisymmetric directivity high-angle residual: the older `docs/l22mg-high-angle-residual-axisymmetric-directivity/README.md` remains a stale pre-0.50 m comparison and is superseded by the current published-parity BEM diagnostic above. The conclusion is unchanged: directly rotating the naked polar table is useful negative evidence, not a high-angle fix or finite high-fidelity source model.
- Source-family high-angle matrix: `docs/l22mg-source-family-high-angle-matrix/README.md` replays stored current-source, source-support, axisymmetric, active-surface, profiled/modal H1659, passive-tweeter-face, and explicit feature-proxy predictions as high-angle diagnostics. The refreshed report ranks the 70-90 deg residual over each case's available 300-1200 Hz coverage so hotspot-only rows cannot be mistaken for full-band rows. It remains source-family evidence, not an acceptance target override; the current source-candidate decision table is the authoritative Juan-target join.
- Juan-only leave-one-angle-out source CV: `docs/l22mg-source-model-cross-validation/README.md` is now the strongest source-fit overfit check. It uses only Juan's corrected 0.50 m naked measurements and scores held-out normalized SPL angle-minus-0, with no Andres gain/delay/rear correction. The current wide/SVD split cloud ranks 26th of 29 compact candidates with 8.810 dB worst-side held-out RMS over 300-1200 Hz, despite in-sample side-worst normalized/absolute/phase 2.500 dB / 2.469 dB / 14.961 deg. The practical conclusion is unchanged: fitting the seven horizontal naked angles is not enough; the next source step needs stronger physical constraints or additional measurements, not Andres-derived scalar correction.
- Source CV absolute and phase source-fit guards: the compact source-CV report now also records in-sample absolute SPL and phase RMS fit metrics and requires side-worst normalized <= 3.0 dB, side-worst absolute SPL <= 3.0 dB, and side-worst phase <= 30 deg before a finite source can be `recommended_juan_only`. This closes the scalar/timing loopholes exposed by `docs/l22mg-lowfreq-null-rear-balance/README.md`: normalized shape cannot detect a uniform rear gain, absolute SPL cannot detect a uniform rear timing/phase error, but Juan source-level and phase fit can. The finite H1659 sources that pass these Juan-only gates now all have mapped current Juan-target BEM evidence and are rejected there: compact2, full2, compact3, full4-SVD, profile-ring-full-SVD, and profile-ring-full. `docs/l22mg-source-candidate-decision/README.md` exposes normalized, absolute, and phase in-sample source-fit columns and finds zero accepted source candidates across 129 current-radius rows.
- Source coefficient frequency-smoothness audit: `docs/l22mg-source-cv-frequency-roughness-smoke/README.md` verifies that source-CV summaries now export `coeff_frequency_roughness_rms_rel_per_octave`, `coeff_frequency_roughness_max_rel_per_octave`, and coefficient-norm dB step metrics. This is a Juan-only diagnostic smoothness surface, not an Andres-derived correction and not yet an acceptance threshold. The bounded smoke covers only 300-360 Hz and is deliberately labelled diagnostic-only; it reports RMS relative coefficient roughness of 1.162/octave for the current wide/SVD source and 1.488/octave for the stable split source.
- Active-surface coefficient frequency-smoothing control: `scripts/simulate_l22mg_baffle.py` now exposes `--source-frequency-smoothness-regularization` for active-surface source models only. It applies log-frequency second-difference smoothing to Juan-fitted active-surface coefficients and exports `source_frequency_smoothness_regularization` plus smoothing diagnostics, so this is a source-model regularization control, not a validation-target correction. Smoke evidence `docs/l22mg-source-cv-physical-diaphragm-fsmooth-smoke/README.md` covers 300-600 Hz only and is diagnostic/incomplete-band; the smoothed compact physical-diaphragm rows exercise the new metadata (`source_frequency_smoothness_rows=2`) but remain rejected as source candidates in that smoke.
- Focused full-band active-surface frequency-smoothing CV: `docs/l22mg-source-cv-physical-diaphragm-fsmooth/README.md` tests 16 compact/full physical-diaphragm rows over 300-1200 Hz. The best row remains the unsmoothed full measured physical diaphragm at 3.481 dB held-out side-worst CV, but it is still `rejected_bad_insample_fit` because the side-worst in-sample normalized, absolute, and phase errors are 3.159 dB, 4.726 dB, and 61.985 deg. Smoothed rows exercise `source_frequency_smoothness_rows=23` but slightly worsen CV/in-sample metrics, so no smoothed physical-diaphragm row deserves mounted-BEM follow-up yet.
- Extended, uniform-annular, and fine active-surface CV: `docs/l22mg-source-cv-active-surface-annular-extended/README.md` expands the Juan-only H1659 prescribed-Neumann annular source search around side gap, azimuth count, regularization, SVD cutoff, full/compact profile, and rear phase. `docs/l22mg-source-cv-active-surface-annular-fine/README.md` adds 88 finer annular/uniform-annular rows. The older extended/uniform/fine summaries are now phase-backfilled from the same Juan-only full-fit path as the compact CV report. The best held-out side RMS is below the 4 dB CV threshold (`3.913 dB` for compact annular gap 28 mm, reg 3e-6), but every fine row is still `rejected_bad_insample_fit`: the best row has 3.867 dB in-sample side-worst normalized RMS, 4.379 dB in-sample side-worst absolute RMS, and 48.735 deg phase RMS. The off-plane audit now includes these extended, uniform-annular, and fine rows: the best gap-28/reg3e-6 row has only 0.103 dB z-offset sensitivity over 70-90 deg, but 13.432 dB source-family spread at UM height; the best uniform-annular local row is similarly small in z-offset movement but has 13.743 dB source-family spread. `docs/l22mg-source-candidate-decision/README.md` includes these sets and still has zero accepted source candidates.
- Source-support hotspot sweep: `docs/l22mg-source-support-hotspot-sweep/README.md` reuses one fixed Andres-mounted BEM matrix at the 1070.068 Hz / 80 deg residual hotspot and sweeps 22 Juan-only split-discrete source supports. The best coarse-screen row, 55 mm half-depth with radii 0/25/50/75/95 mm and SVD rcond 1e-5, improves the one-frequency 70-90 deg RMS from 17.096 dB for the current support to 12.812 dB while keeping 0-60 deg at 1.441 dB. A higher-fidelity q7-near 1000-1200 Hz rerun in `docs/l22mg-bem-passive-um-d55-r25-95-svd1e-5-hotband/README.md` does not confirm an acceptance path: common-overlap 70-90 deg RMS is 7.551 dB versus 6.965 dB for the current wide/SVD source, and 80-90 deg RMS is 6.889 dB versus 6.812 dB (`docs/l22mg-high-angle-residual-d55-r25-95/README.md`). It slightly improves 0-60 deg RMS from 1.603 to 1.299 dB on the same 1000-1200 Hz overlap, but the high-angle residual remains dominated by 1070 Hz / 80 deg. This rules out simple symmetric source-support retuning as a sufficient fix.
- A thin STL-derived surface-mounted flange annulus was tested in `docs/l22mg-bem-local-h24-1200-q3-d25-stl-face/README.md`.
- The annulus dimensions were derived from `linkwitz/H1659-08_U22REX_P-SL_driver.stl`: inner diameter 190 mm, outer diameter 221 mm, proud height 0.6 mm.
- This diagnostic worsened validation relative to the 18.3 mm no-flange baseline: normalized polar RMS 300-1200 Hz rose from 4.561 dB to 7.658 dB, and F90-F0 mean error rose from +1.742 dB to +12.533 dB.
- The active validation artifact therefore remains no-flange, now with the h22/local13.2 d25 finite-source run and 19.05 mm baffle thickness.

## Source Diagnostics

- Consolidated source/active-geometry diagnostics: `docs/l22mg-source-geometry-diagnostics/README.md`.
- A split axisymmetric ring source was tested in `docs/l22mg-bem-local-h24-1200-q3-ring-d25/README.md`.
- It is more circularly symmetric and better conditioned than the split point cloud, but it fits Juan's measured horizontal naked polars worse.
- It worsened Andres normalized polar RMS 300-1200 Hz from 4.561 dB to 5.513 dB relative to the 18.3 mm split-discrete baseline, although it improved on-axis RMS from 4.861 dB to 2.246 dB.
- A Juan-only discrete measured-phase source diagnostic was tested in `docs/l22mg-bem-local-h24-1200-q3-discrete-measured-d45-t1905/README.md`.
- It uses stored Juan rear phase rather than reconstructed dipole phase and fits Juan's naked polars better than the current split-dipole source, but it worsens Andres validation: normalized polar RMS 300-1200 Hz rises from 4.528 dB to 6.062 dB, baffle-transfer RMS rises from 4.557 dB to 8.256 dB, and DI RMS error rises from 1.203 dB to 4.608 dB.
- Hotband source diagnostics are summarized in `docs/l22mg-hotband-variant-comparison.csv`. The 45 mm half-depth split cloud with radii 0/35/70/95 mm reduces 850-1100 Hz normalized RMS from 8.061 dB to 3.177 dB, but it is poorly conditioned.
- Full-band SVD-conditioned wide-cloud diagnostic: `docs/l22mg-bem-passive-um-widecloud-svd1e-5-h22-q7-near-1200-12ppo/README.md` is now summarized against the published-parity target in `docs/l22mg-validation-gate-summary/README.md` as 3.284 dB all-angle, 1.561 dB through 60 deg, and 1.908 dB through 80 deg. It still fails all-angle acceptance and source CV.
- Full-band untruncated wide-cloud diagnostic: `docs/l22mg-bem-passive-um-widecloud-h22-q7-near-1200-12ppo/README.md` replays at 4.632 dB all-angle against the retimed target, essentially matching the SVD-conditioned result, but has `design_cond_max` about 6.8e9.
- The explicit d25 wide-cloud check, `docs/l22mg-bem-passive-um-widecloud-d25-h22-q7-near-1200-12ppo/README.md`, replays at 7.587 dB all-angle against the retimed target and remains worse.
- Full-band ultrawide source test: `docs/l22mg-bem-passive-um-ultrawide-svd1e-5-h22-q7-near-1200-12ppo/README.md` uses radii 0/35/70/95/110 mm and SVD rcond 1e-5. It improves the Juan nude source fit but worsens Andres validation to 5.426 dB all-angle and 3.081 dB through 60 deg, indicating that the remaining error is not fixed by a wider equivalent-source support alone.
- Full-band acoustic-center test: `docs/l22mg-bem-passive-um-widecloud-svd1e-5-ac20-h22-q7-near-1200-12ppo/README.md` uses the best wide-cloud source with `--acoustic-center-offset-mm 20`. It worsens validation to 6.161 dB all-angle even though it fills the F90 null, so fitting the high-angle null by moving the source center would damage the rest of the polar.
- High-angle residual decomposition: `docs/l22mg-high-angle-residual/README.md` should be used when judging future source/geometry variants. A useful variant must reduce the 70-90 deg RMS and the 1070 Hz / 80 deg residual without increasing the already-near-threshold 0-60 deg RMS.
- Extended circular-source audit: `docs/l22mg-source-model-audit-ring-extended/README.md` adds denser axisymmetric split-ring candidates with radii up to the 95 mm cutout scale, 48 azimuth samples, and SVD truncation. The best rich split-ring row is still only rank 27 in the Juan-only source-fit audit, with worst-side normalized RMS 2.629 dB over 300-1200 Hz. This means a circular aperture basis is more physical for off-plane evaluation, but the current ring basis does not fit the naked L22 data as well as the split-discrete clouds.
- Rich circular-source BEM hotspot check: `docs/l22mg-bem-passive-um-rich-ring-hotspot/README.md` runs a 1000-1200 Hz dense-BEM diagnostic with the best rich split-ring candidate, raised passive UM, closed tweeter patches, q7-near1 integration, and Andres UM-height mic. It worsens the high-angle validation on the same 1000-1200 Hz overlap: 70-90 deg RMS rises from 7.941 dB for the current wide/SVD source to 11.009 dB, 80-90 deg RMS rises from 7.208 dB to 12.255 dB, and 90 deg RMS rises from 5.075 dB to 14.618 dB. The current failure is therefore not fixed by imposing a simple circular ring source.
- H1659 acoustic-surface source-profile diagnostic: `docs/l22mg-bem-passive-um-h1659-profile-compact-hotband/README.md` and `docs/l22mg-bem-passive-um-h1659-profile-full-hotband/README.md` move the split-discrete equivalent-source points from the artificial +/-45 mm source planes onto cone/surround depth profiles derived from `linkwitz/generate_H1659_driver_stl.py`, while keeping points in Juan's measured horizontal plane and adding no rigid active-driver scatterer. These profiles fit Juan's naked source better than the current wide/SVD source over 300-1200 Hz: compact/full overall fit RMS is about 1.282/1.292 dB versus 2.200 dB for the wide/SVD source. But both badly over-fill the mounted high-angle null on the common 1000-1200 Hz overlap (`docs/l22mg-high-angle-residual-h1659-profile-all/README.md`): 70-90 deg RMS rises from 7.941 dB for wide/SVD to 23.406 dB compact and 22.085 dB full; 90 deg RMS rises from 5.075 dB to 20.903/19.578 dB. Better naked-source least-squares fit alone is therefore not a sufficient validation criterion.
- H1659 profiled axisymmetric-ring source diagnostic: `docs/l22mg-source-model-audit-profiled-ring/README.md` adds circular rings at the H1659 cone/surround radius-depth profile. The compact profile is the best conditioned finite Juan-only source in that audit: worst-side normalized fit RMS 1.121 dB over 300-1200 Hz with condition max 1.2e5. Its bounded 1000-1200 Hz BEM check in `docs/l22mg-bem-passive-um-profile-ring-compact-hotband/README.md` improves over the horizontal H1659 point-profile hotband, but still misses Andres badly: available-overlap normalized RMS 8.865 dB, through-60 RMS 1.976 dB, through-80 RMS 7.987 dB, and F90-F0 mean error +12.466 dB. The exact Juan-CV compact SVD profile-ring row is now tested in `docs/l22mg-bem-passive-um-profile-ring-compact-svd1e-5-hotband/README.md`; it fits Juan better than the current wide/SVD source but is worse against Andres, with 9.596 dB all-angle RMS, 8.698 dB through 80 deg, and +41.260 dB worst residual at 1070 Hz / 80 deg. The full H1659 profile-ring candidate cross-validates slightly better against Juan at 3.321 dB held-out worst-side RMS, but its bounded BEM check in `docs/l22mg-bem-passive-um-profile-ring-full-hotband/README.md` also fails: available-overlap normalized RMS 6.898 dB, through-60 RMS 4.394 dB, through-80 RMS 6.756 dB, and worst residual +27.945 dB at 1070 Hz / 80 deg. The high-angle comparison in `docs/l22mg-high-angle-residual-profile-ring-compact-svd/README.md` shows compact SVD profile-ring 70-90 deg RMS 17.032 dB versus 6.963 dB for the current corrected wide/SVD baseline on the common 1000-1200 Hz overlap. This rules out profiled ring support as an immediate high-angle fix, while preserving it as a cleaner Juan-only source option than the flat ring basis.
- H1659 smooth modal-ring source diagnostic: current code also supports `h1659-modal-*` source profiles, which use smooth radial modal combinations of the H1659 cone/surround rings instead of one free fitted strength per radius. The Juan-only audit in `docs/l22mg-source-model-audit-modal-ring/README.md` shows `h1659-modal-full-4` fits the naked data well: worst-side normalized fit RMS 1.138 dB over 300-1200 Hz with max design condition 2.82e5 and SVD effective condition 9.06e4. Its bounded 1000-1200 Hz BEM check in `docs/l22mg-bem-passive-um-h1659-modal-full4-hotband/README.md` fails badly against Andres: available-overlap normalized RMS 11.286 dB, through-60 RMS 5.572 dB, through-80 RMS 10.548 dB, and F90-F0 mean error +14.285 dB. The comparison in `docs/l22mg-high-angle-residual-modal-ring/README.md` shows 70-90 deg RMS rises from 6.965 dB for the current wide/SVD source to 18.764 dB on the common 1000-1200 Hz overlap. Smooth radial modal source support is therefore ruled out as a high-angle fix, despite its improved Juan-only fit.
- Off-plane source ambiguity audit: `docs/l22mg-offplane-source-ambiguity/README.md` evaluates Juan-fitted sources at the Andres UM-height mic positions before any BEM scattering. The wide/SVD source changes by 1.601 dB RMS in the 70-90 deg group when moving from Juan's horizontal plane to z=+165 mm, while the axisymmetric directivity table changes by only 0.147 dB, axisymmetric H1659 sources change by 0.098-0.183 dB, and the active-surface/physical rear-basket variants change by about 0.090-0.234 dB. More importantly, the different Juan-source families disagree strongly at UM height; the extended, uniform-annular, fine annular, physical-diaphragm, and physical rear-basket rows are now included in that spread. The targeted eligible-source report exports `source_eligible_pairwise_spread_surface.csv` and `plots/source_eligible_pairwise_spread_contour.png`, showing the Juan-CV recommended finite H1659 ensemble reaches 26.655 dB pointwise spread at 734 Hz / 90 deg. The audit now also exports front/rear normalized, absolute, and phase source-fit RMS columns because normalized SPL fit alone is not sufficient evidence for an acceptance-grade physical source; the selected Andres `modal-full2` row has side-worst in-sample fit 2.682 dB normalized, 2.629 dB absolute, and 15.134 deg phase. That means the 3D incident field used by BEM at Andres' mic height is not uniquely constrained by Juan's horizontal naked polars. This remains an explicit source-generalization gate in the strict summary; it does not replace Andres BEM validation.

## Thickness Diagnostic

- The 19.05 mm alternate thickness was tested in `docs/l22mg-bem-local-h24-h22-conv-1200-q3-d25-t1905/README.md`.
- It slightly improved normalized polar RMS 300-1200 Hz from 4.561 dB to 4.528 dB in the sparse 6 points/octave h24 run.
- This is a real geometry parameter from the original scope, not an Andres-derived correction, but it is far too small an improvement to resolve the validation failure.

The generated solver-upgrade path report, `docs/l22mg-bem-upgrade-path/README.md`, now reads the current Andres/Juan scorecards and driver-STL audit directly. It records the corrected 0.50 m Juan source radius, keeps 0.75 m source-radius artifacts stale, and separates raw STL, feature proxy, dense BEM, FMM/H-matrix, and higher-order BEM roles.

The next serious steps are still:

- improve the finite equivalent-source model without Andres-derived corrections;
- pair the quality-controlled driver-STL feature proxy with a validated source/driver-surface formulation instead of using the diagnostic envelope or raw STL facets directly;
- move to FMM/H-matrix or higher-order BEM before treating detailed driver geometry as acceptance-grade.
