antorsae/lx/top_baffle_v2/artifacts/obiwan/README.md

# Obiwan — regular and integrated waveguide uppers

For current H2C print files and the integrated **Dayton ND25FN-4 waveguide**
upper, use the [H2C catalog](../../to_print/h2c/README.md) and
[three-family selection guide](../../docs/TWEETER_OPTIONS.md).
This facade retains the regular carrier and earlier split geometry; current
print files for every upper are linked below.

Obiwan ND25FW-4, coaxial BMR, opposed BMR and ND25FN-4 waveguide uppers
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
