antorsae/lx/top_baffle_v2/candidates/nd25fn4_crescent/README.md

# Dayton ND25FN-4 waveguide — design sources and geometry evidence

The **Dayton ND25FN-4 waveguide** is the third tweeter family in this project.
It fuses the Obiwan MU10 upper-mid carrier and the printed front/rear tweeter
waveguides into one body. The same body fits both LM stand states.
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
