antorsae/lx/docs/andres/static_plots/core/10F8424_contour_absolute.png

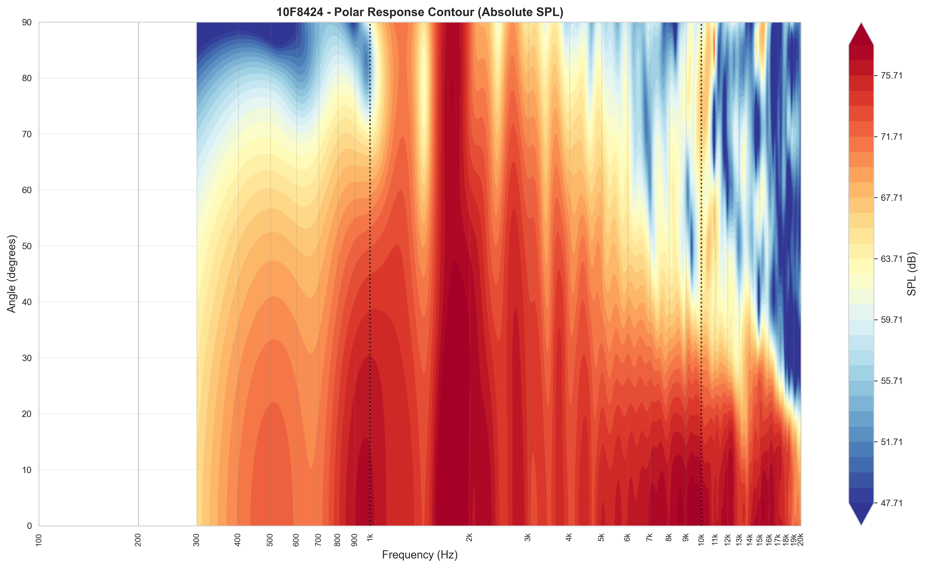
docs/andres/static_plots/core/10F8424_contour_absolute.png
