antorsae/lx/docs/andres/static_plots/core/10F8424_contour_normalized.png

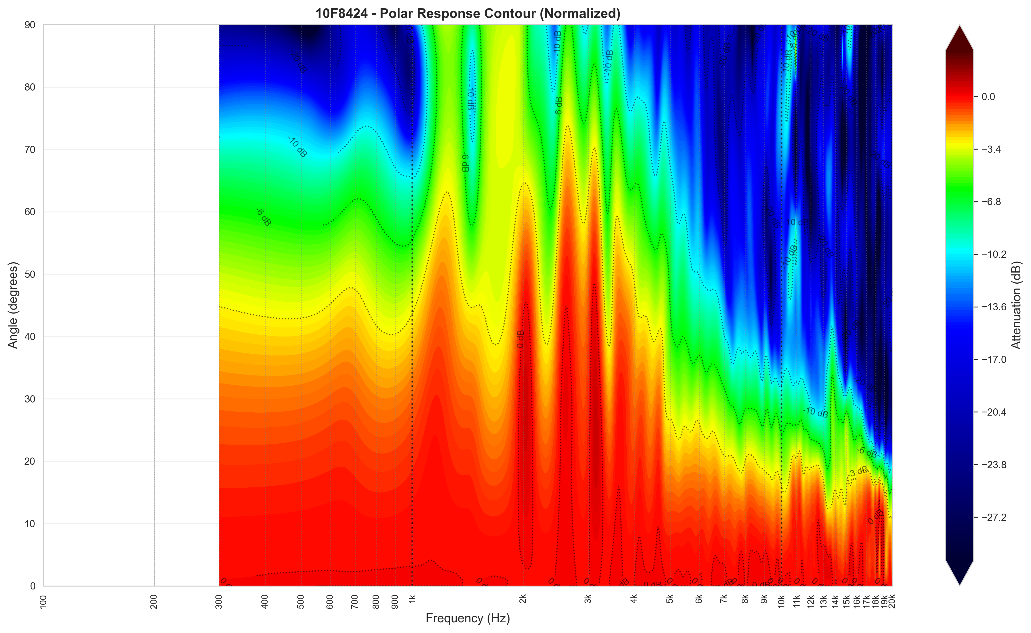
docs/andres/static_plots/core/10F8424_contour_normalized.png
