antorsae/lx/docs/andres/static_plots/core/10F8424_freq_response_angles.png

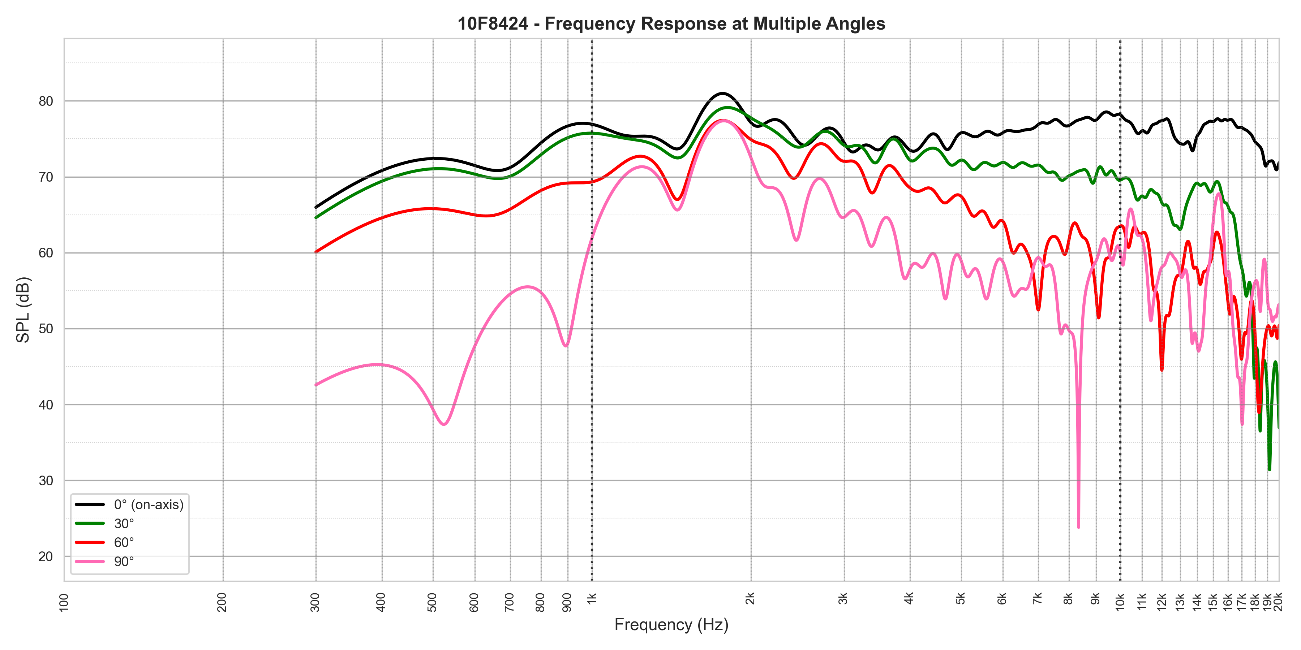
docs/andres/static_plots/core/10F8424_freq_response_angles.png
