antorsae/lx/docs/andres/static_plots/core/di_comparison.png

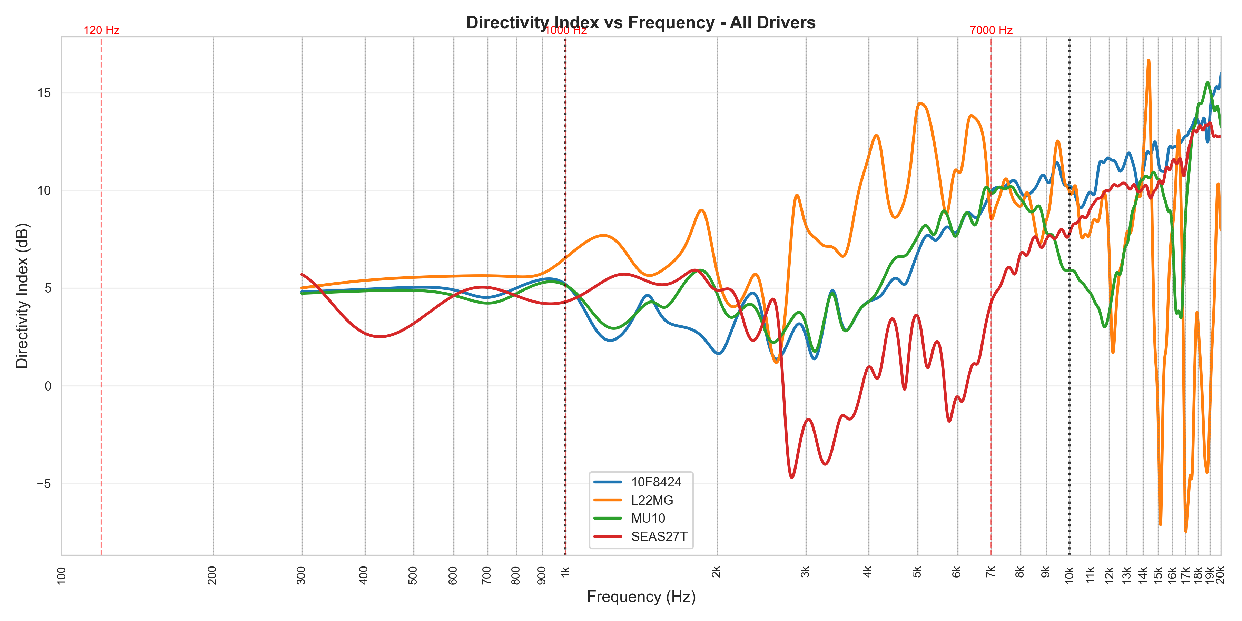
docs/andres/static_plots/core/di_comparison.png
