antorsae/lx/docs/andres/static_plots/core/L22MG_contour_normalized.png

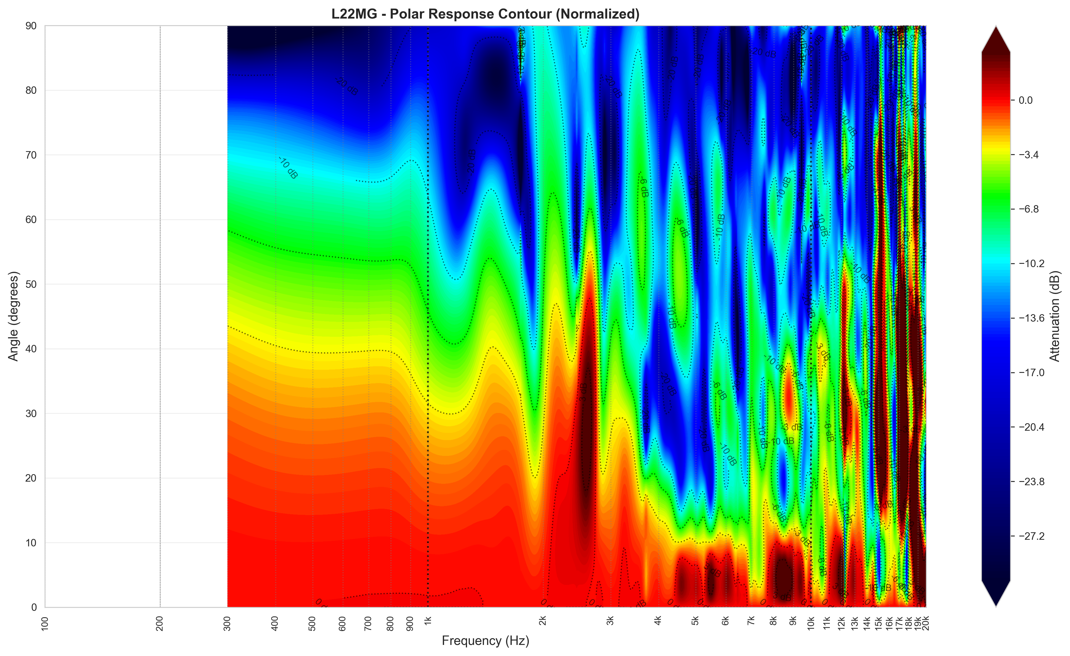
docs/andres/static_plots/core/L22MG_contour_normalized.png
