antorsae/lx/docs/andres/static_plots/core/L22MG_freq_response_angles.png

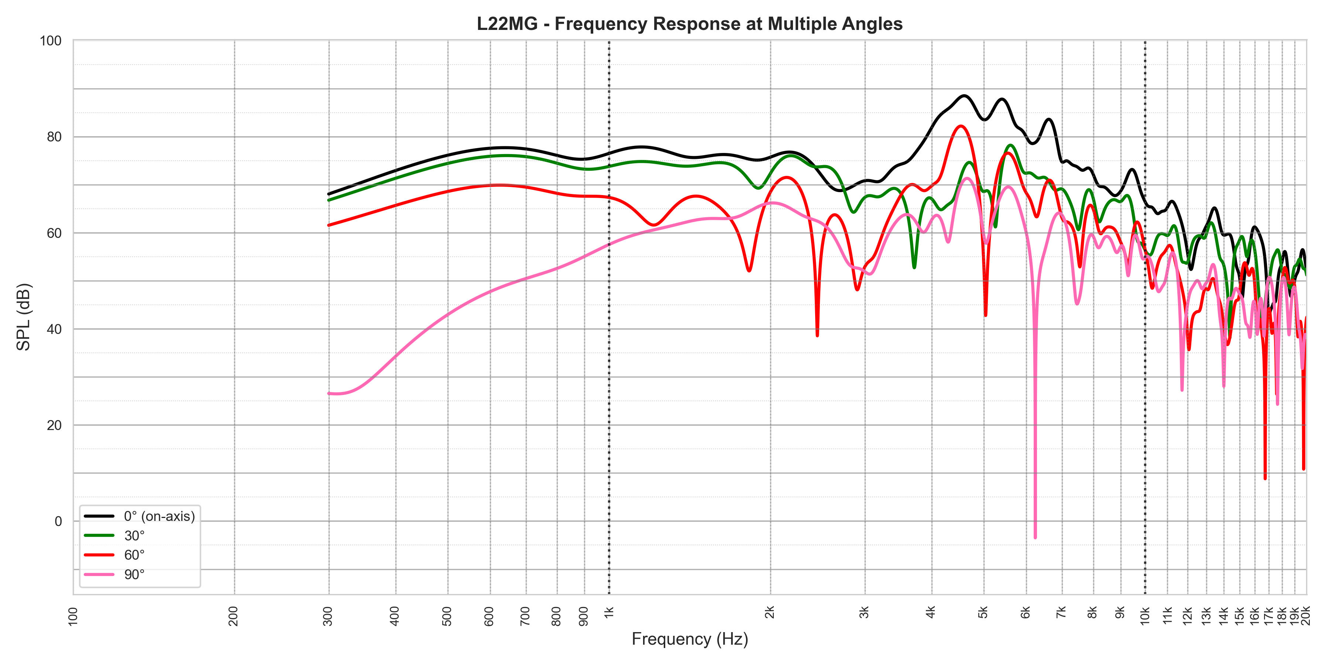
docs/andres/static_plots/core/L22MG_freq_response_angles.png
