antorsae/lx/docs/andres/static_plots/core/MU10_contour_absolute.png

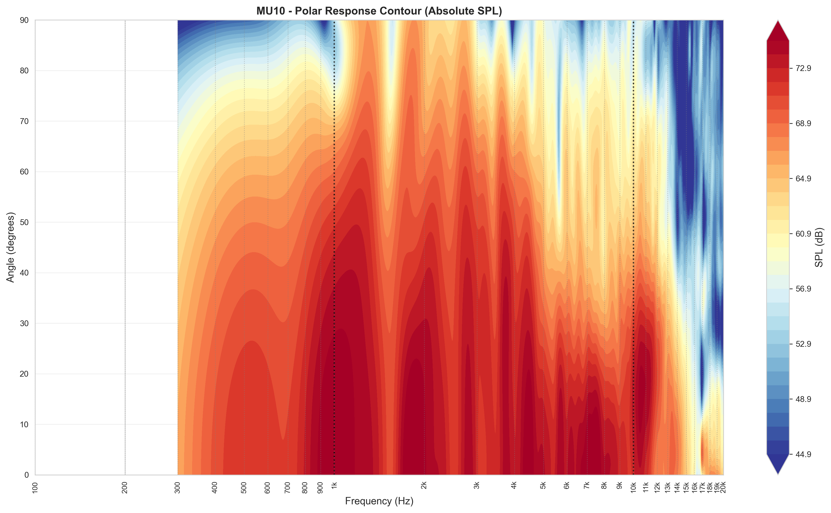
docs/andres/static_plots/core/MU10_contour_absolute.png
