antorsae/lx/docs/andres/static_plots/core/MU10_contour_normalized.png

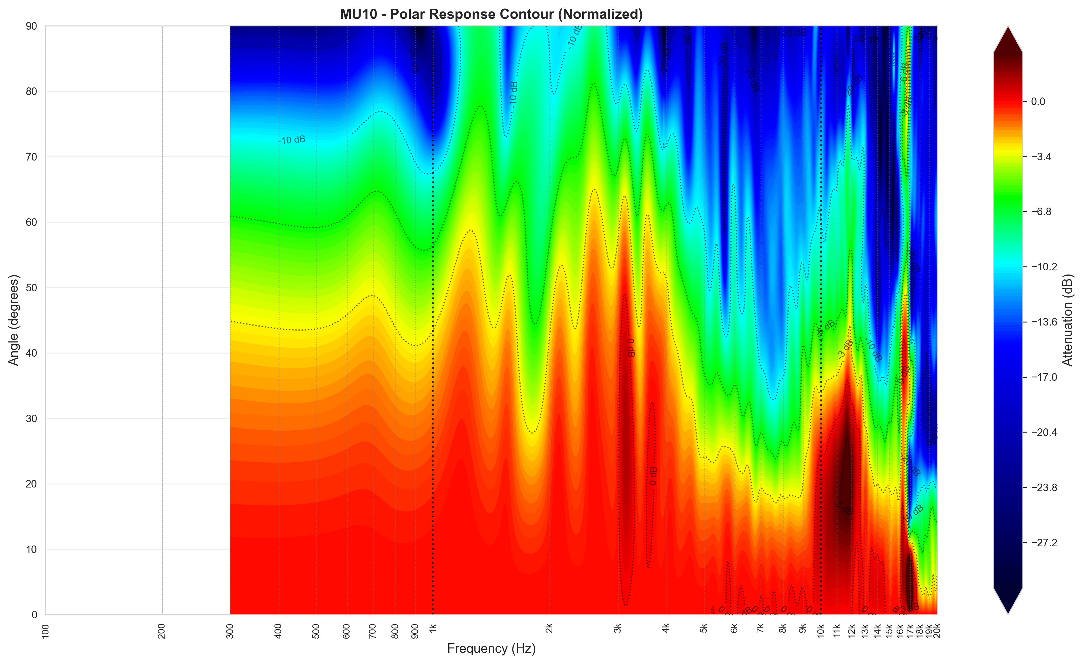
docs/andres/static_plots/core/MU10_contour_normalized.png
