antorsae/lx/docs/andres/static_plots/core/MU10_freq_response_normalized.png

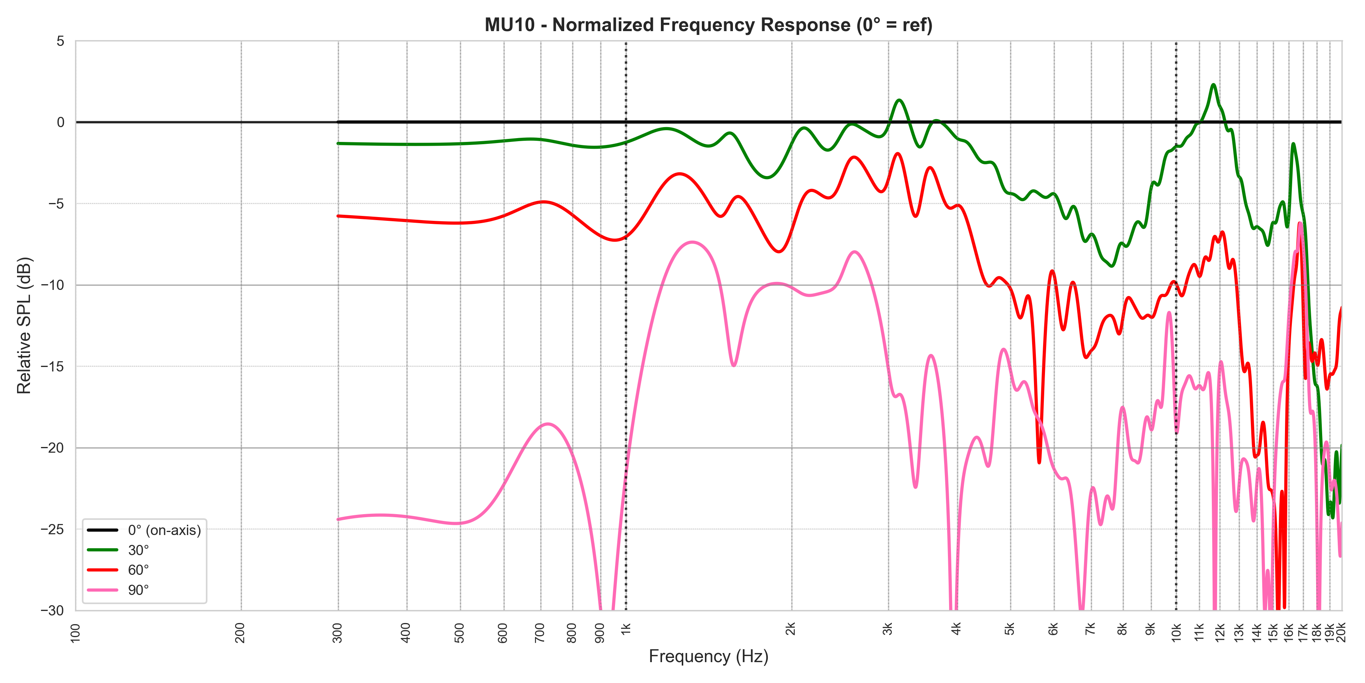
docs/andres/static_plots/core/MU10_freq_response_normalized.png
