antorsae/lx/docs/andres/static_plots/core/SEAS27T_contour_absolute.png

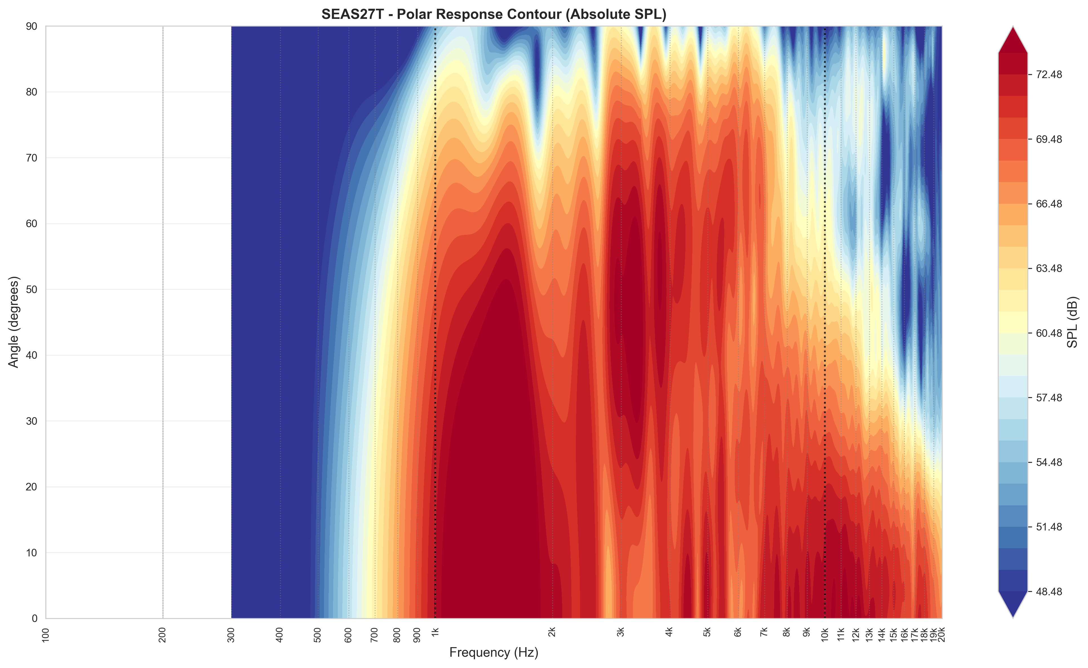
docs/andres/static_plots/core/SEAS27T_contour_absolute.png
