antorsae/lx/docs/andres/static_plots/core/SEAS27T_freq_response_angles.png

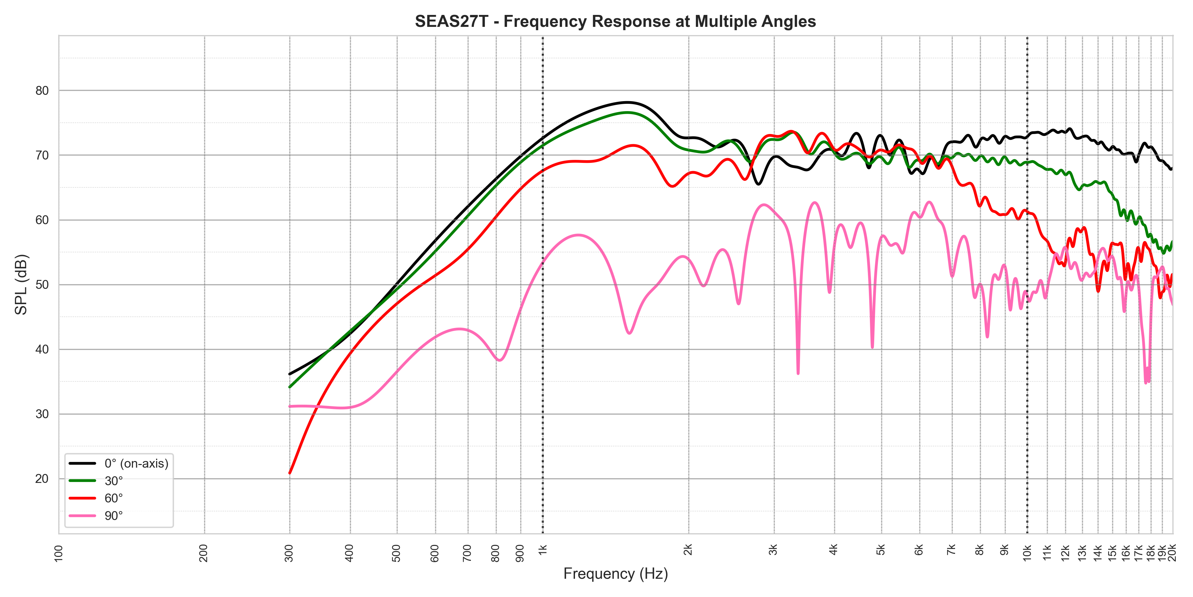
docs/andres/static_plots/core/SEAS27T_freq_response_angles.png
