antorsae/lx/docs/andres/static_plots/crossover/crossover_120Hz.png

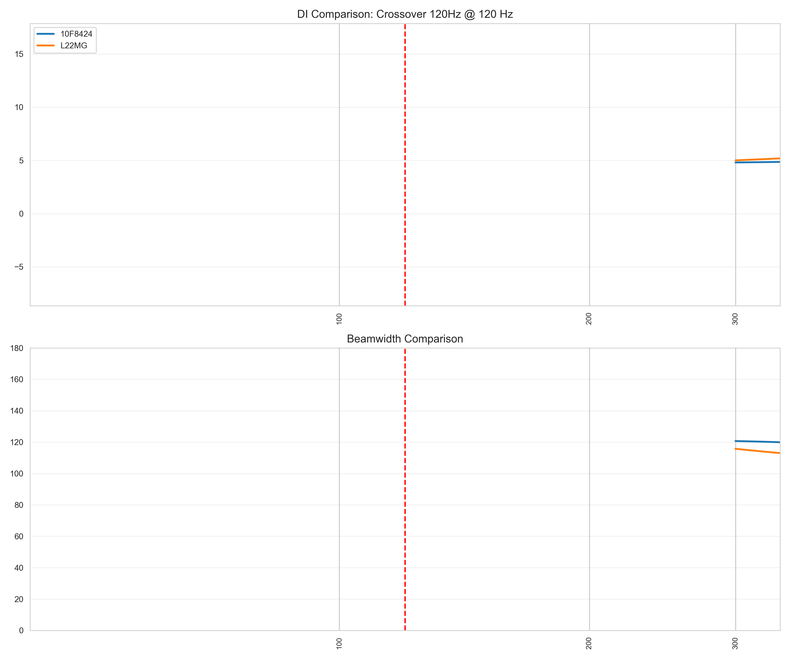
docs/andres/static_plots/crossover/crossover_120Hz.png
