antorsae/lx/docs/andres/static_plots/polar/10F8424_polar_circular.png

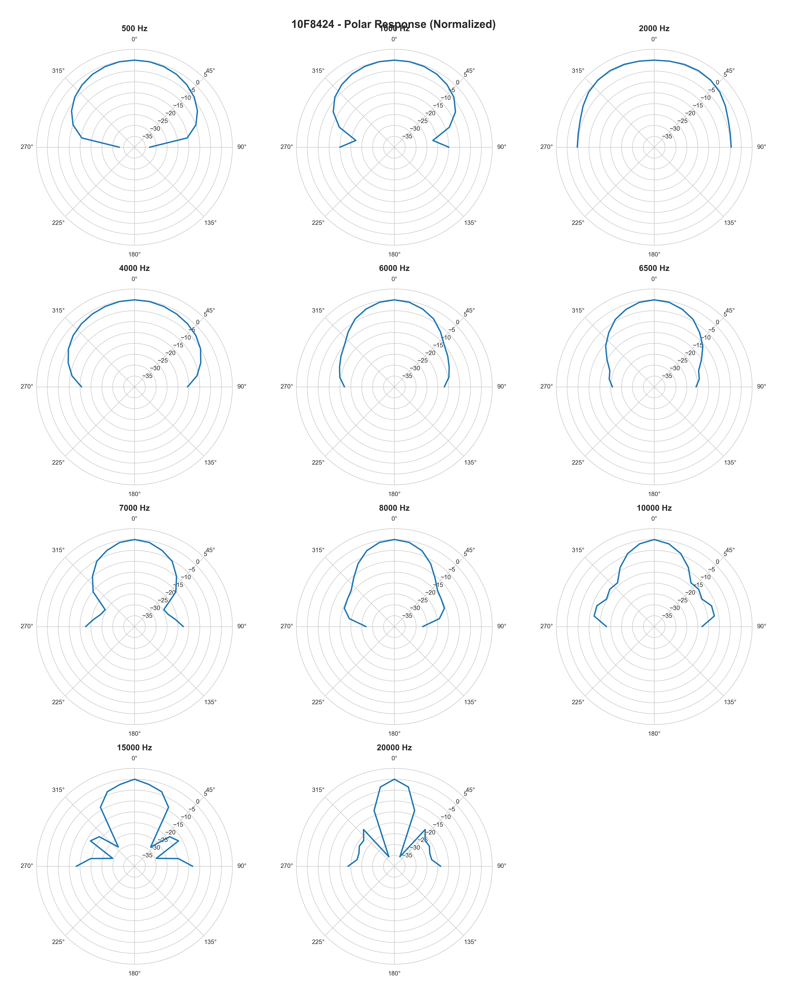
docs/andres/static_plots/polar/10F8424_polar_circular.png
