antorsae/lx/docs/andres/static_plots/polar/polar_gallery_overlaid.png

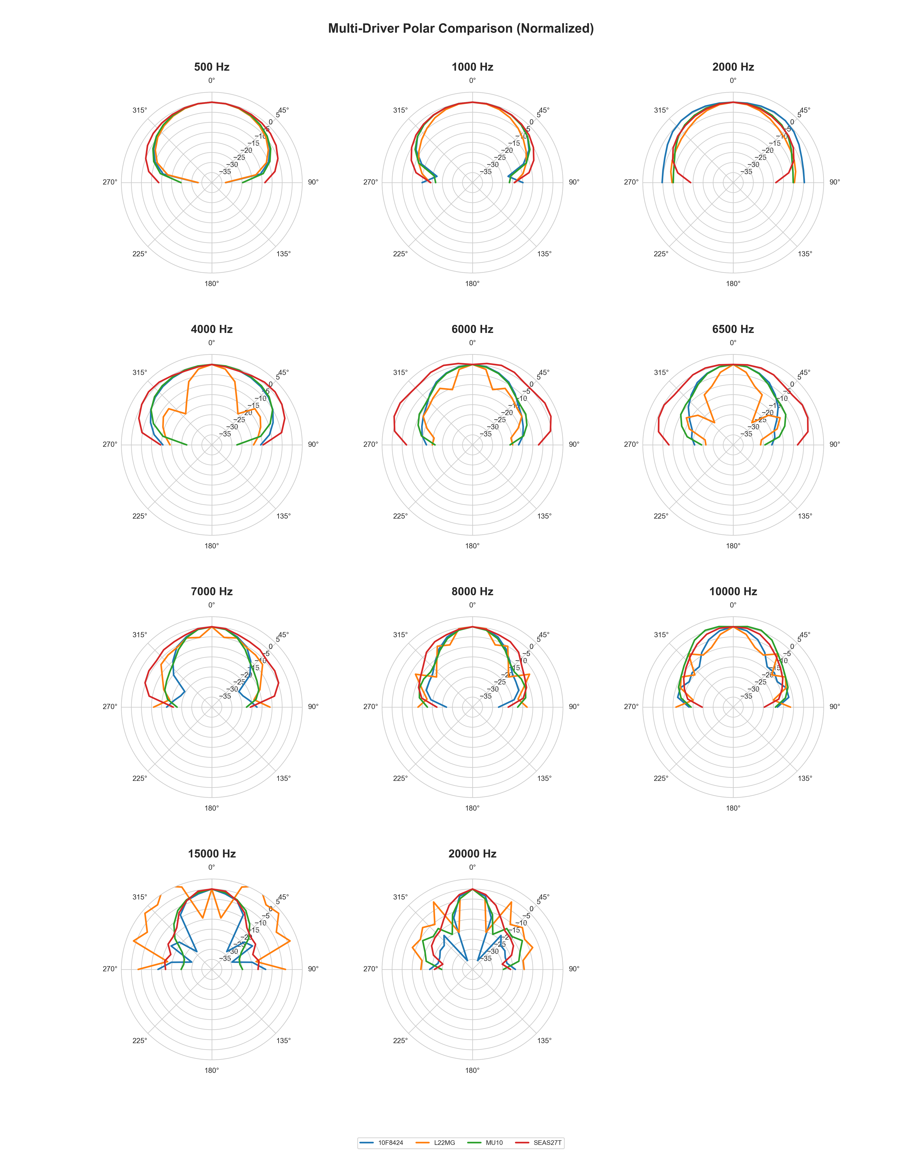
docs/andres/static_plots/polar/polar_gallery_overlaid.png
