antorsae/lx/docs/juan-baffleless-cdsl-baseline/static_plots/core/cdsl_contour_absolute.png

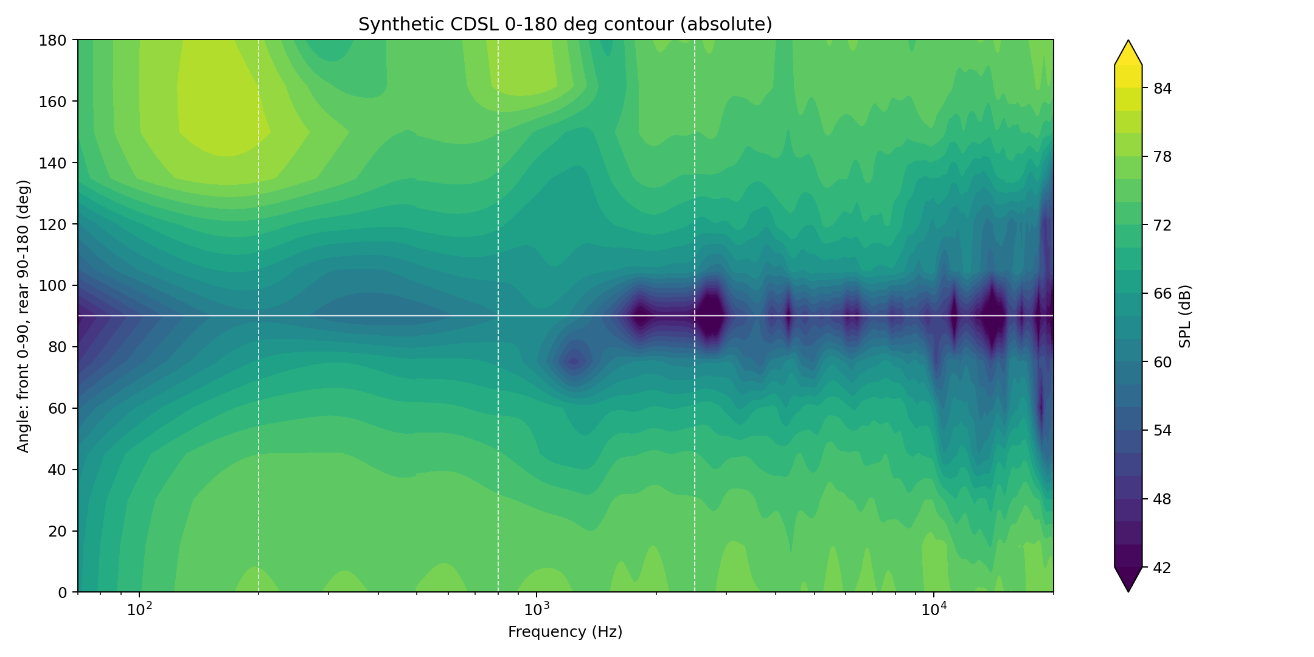
docs/juan-baffleless-cdsl-baseline/static_plots/core/cdsl_contour_absolute.png
