antorsae/lx/docs/juan-baffleless-cdsl-baseline/static_plots/core/cdsl_search_top_candidates.png

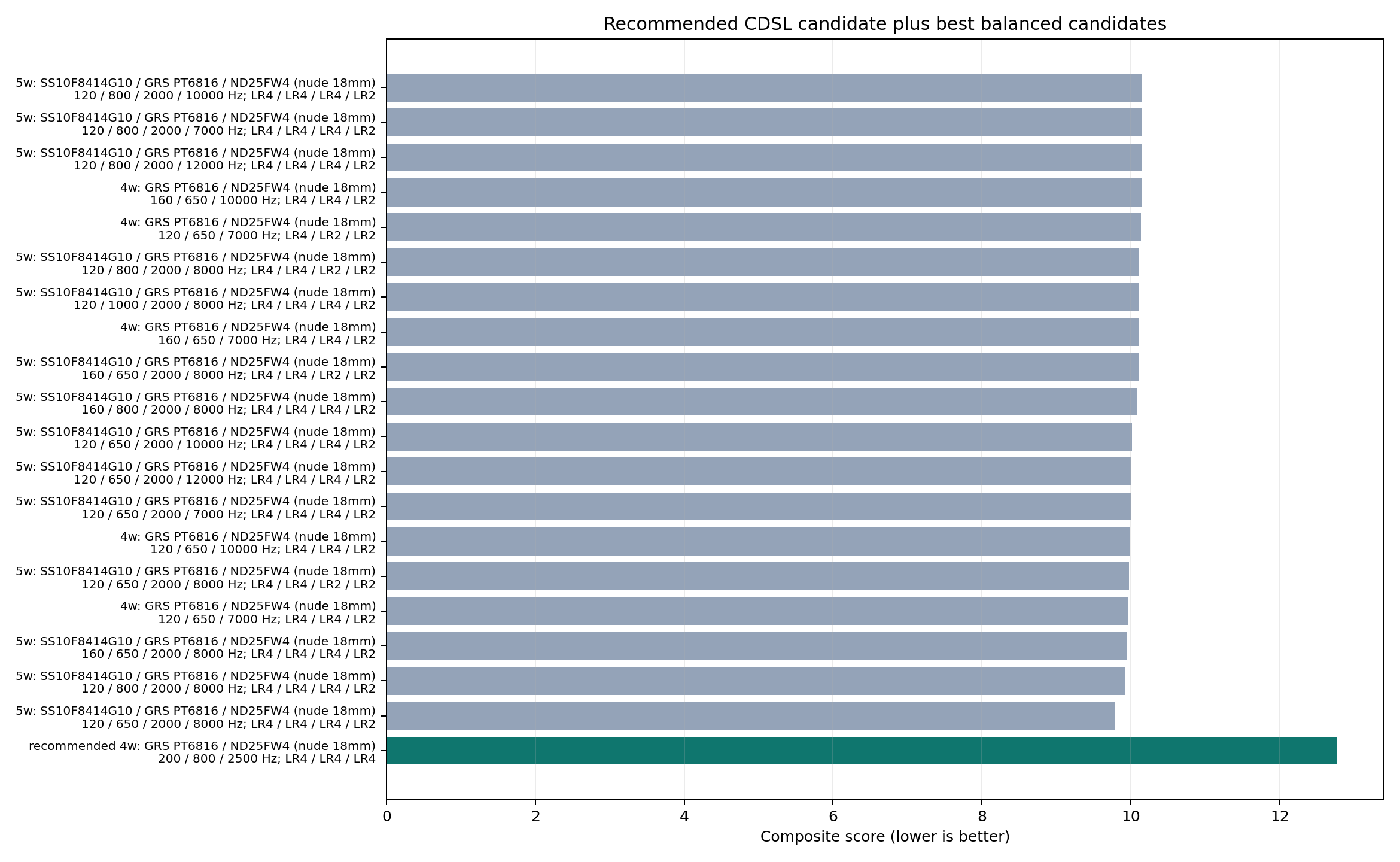
docs/juan-baffleless-cdsl-baseline/static_plots/core/cdsl_search_top_candidates.png
