antorsae/lx/docs/juan-baffleless-cdsl-baseline/static_plots/core/cdsl_vs_lx521_30_vs_60.png

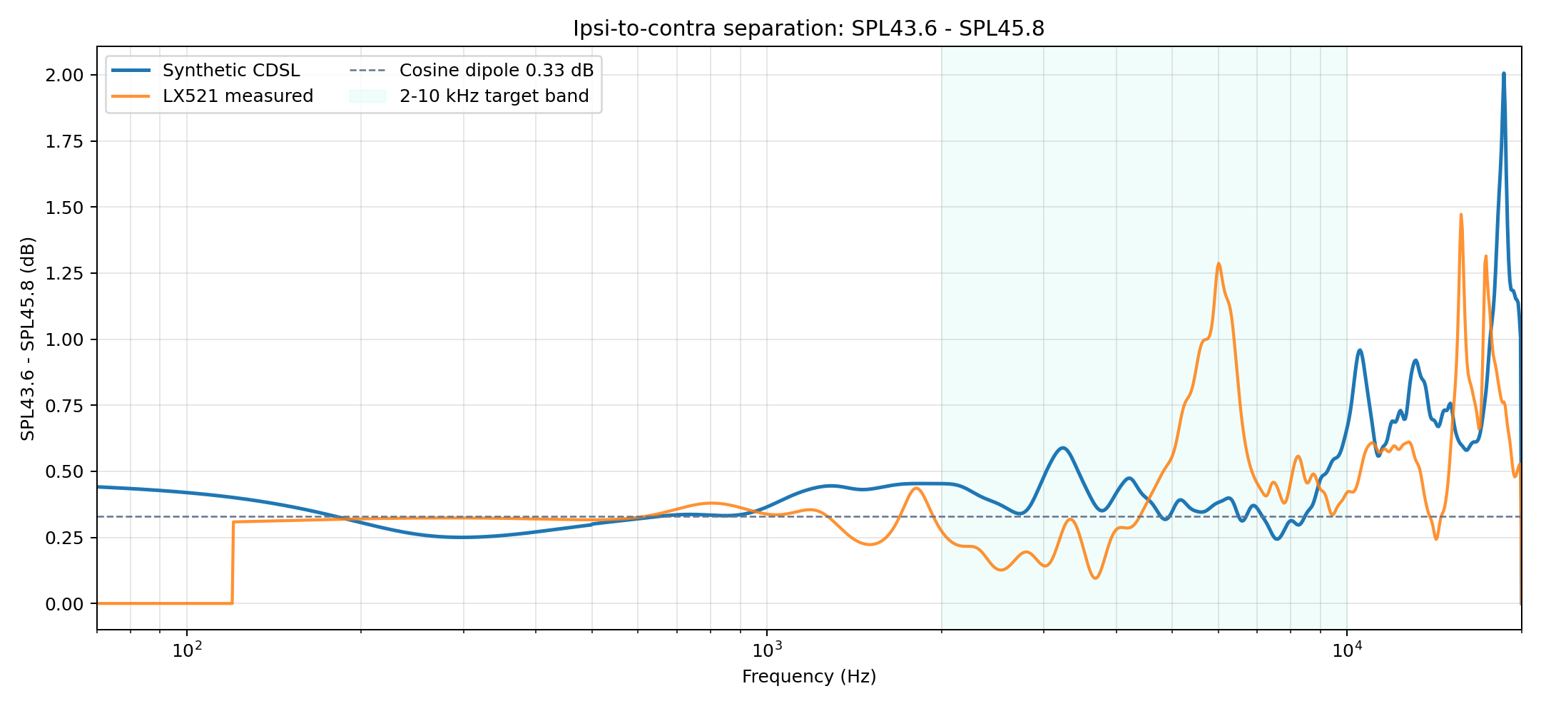
docs/juan-baffleless-cdsl-baseline/static_plots/core/cdsl_vs_lx521_30_vs_60.png
