antorsae/lx/docs/juan-baffleless-cdsl-baseline/static_plots/core/cdsl_vs_lx521_di.png

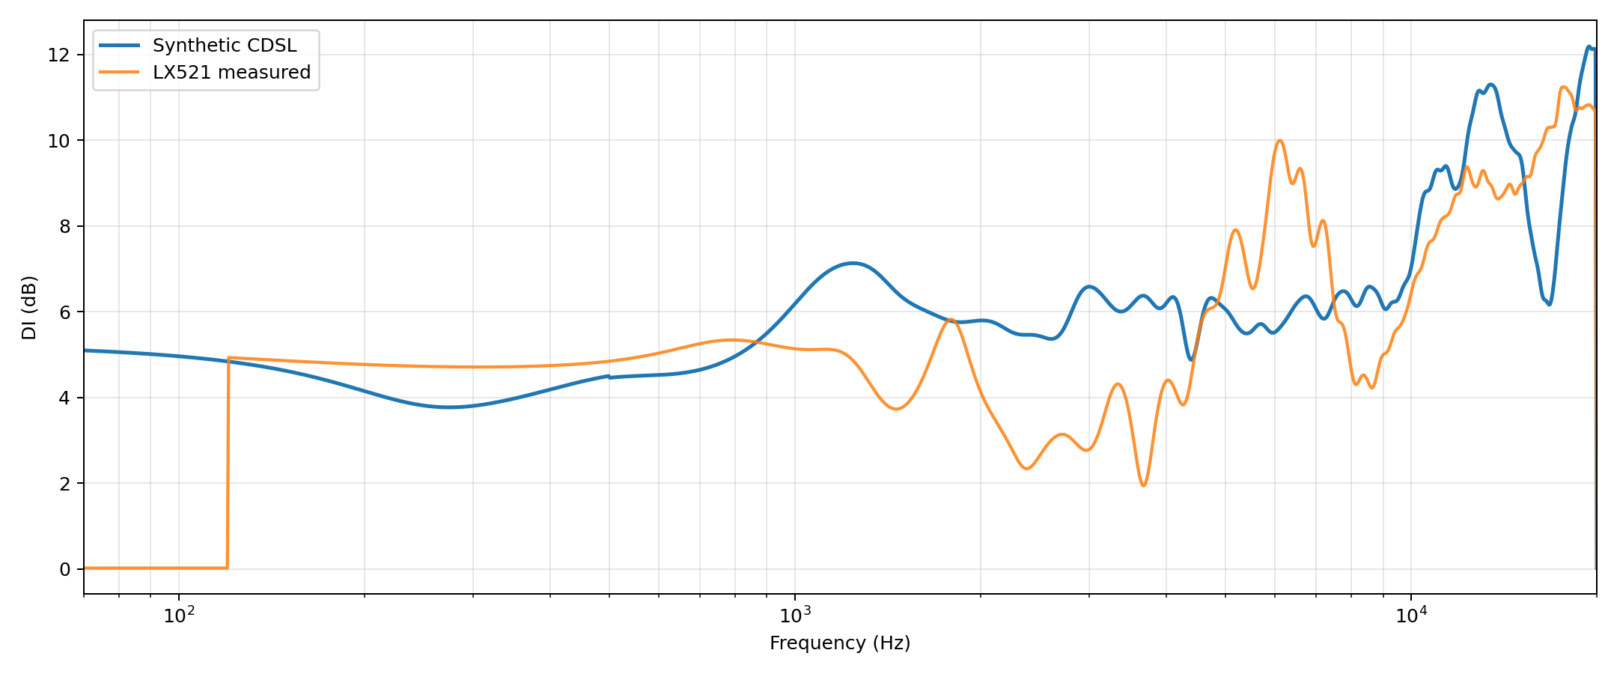
docs/juan-baffleless-cdsl-baseline/static_plots/core/cdsl_vs_lx521_di.png
