antorsae/lx/docs/juan-baffleless-cdsl-baseline/static_plots/polar/cdsl_vs_lx521_polar_circular.png

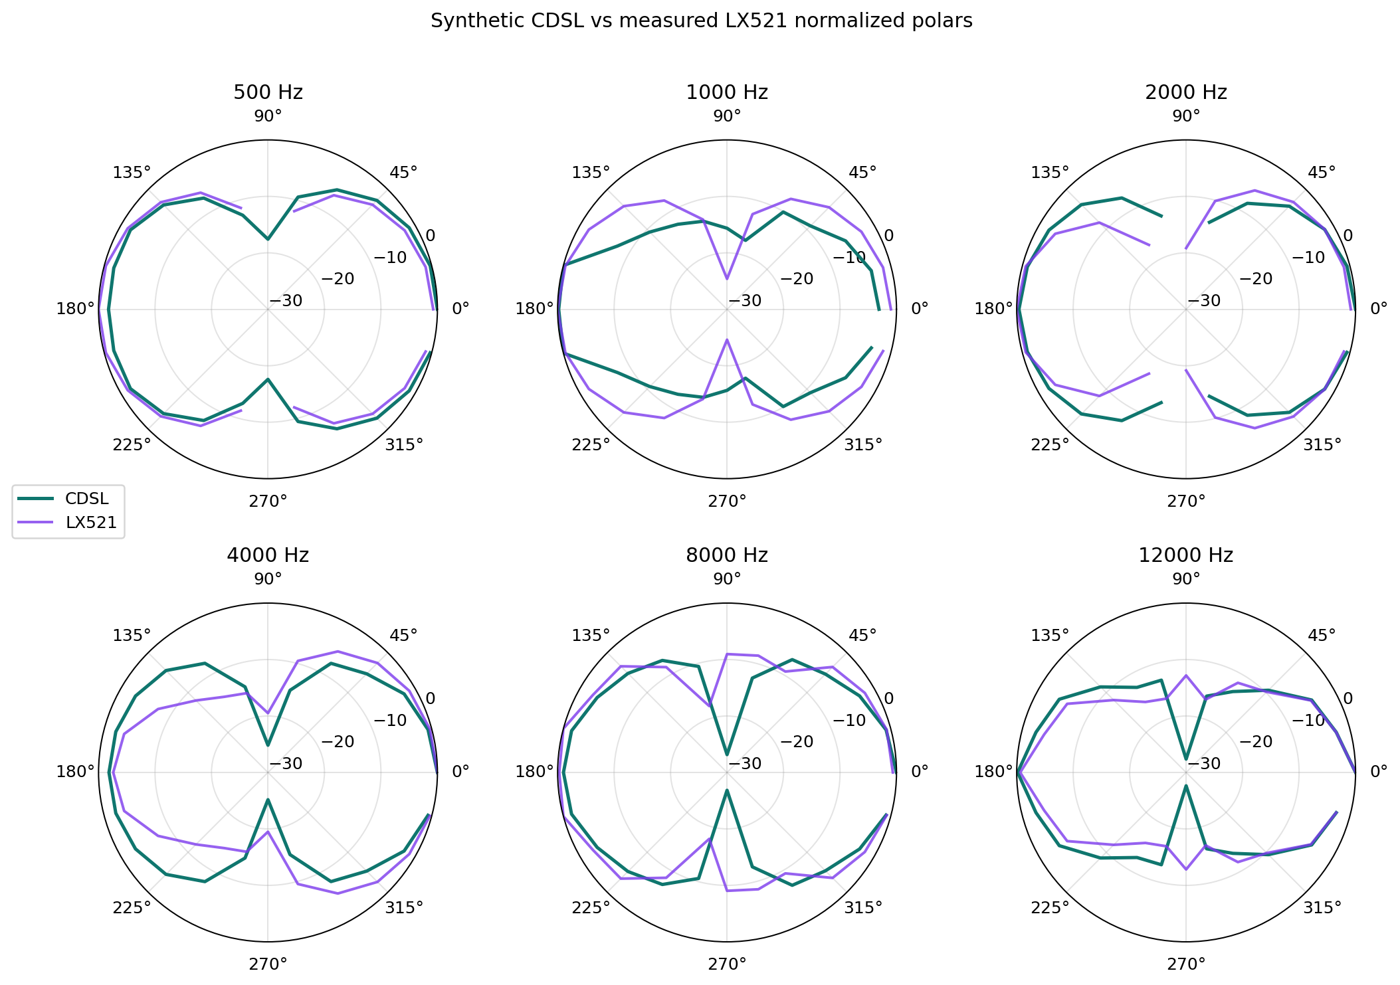
docs/juan-baffleless-cdsl-baseline/static_plots/polar/cdsl_vs_lx521_polar_circular.png
