antorsae/lx/docs/juan-baffleless-cdsl/static_plots/core/cdsl_crossover_regions.png

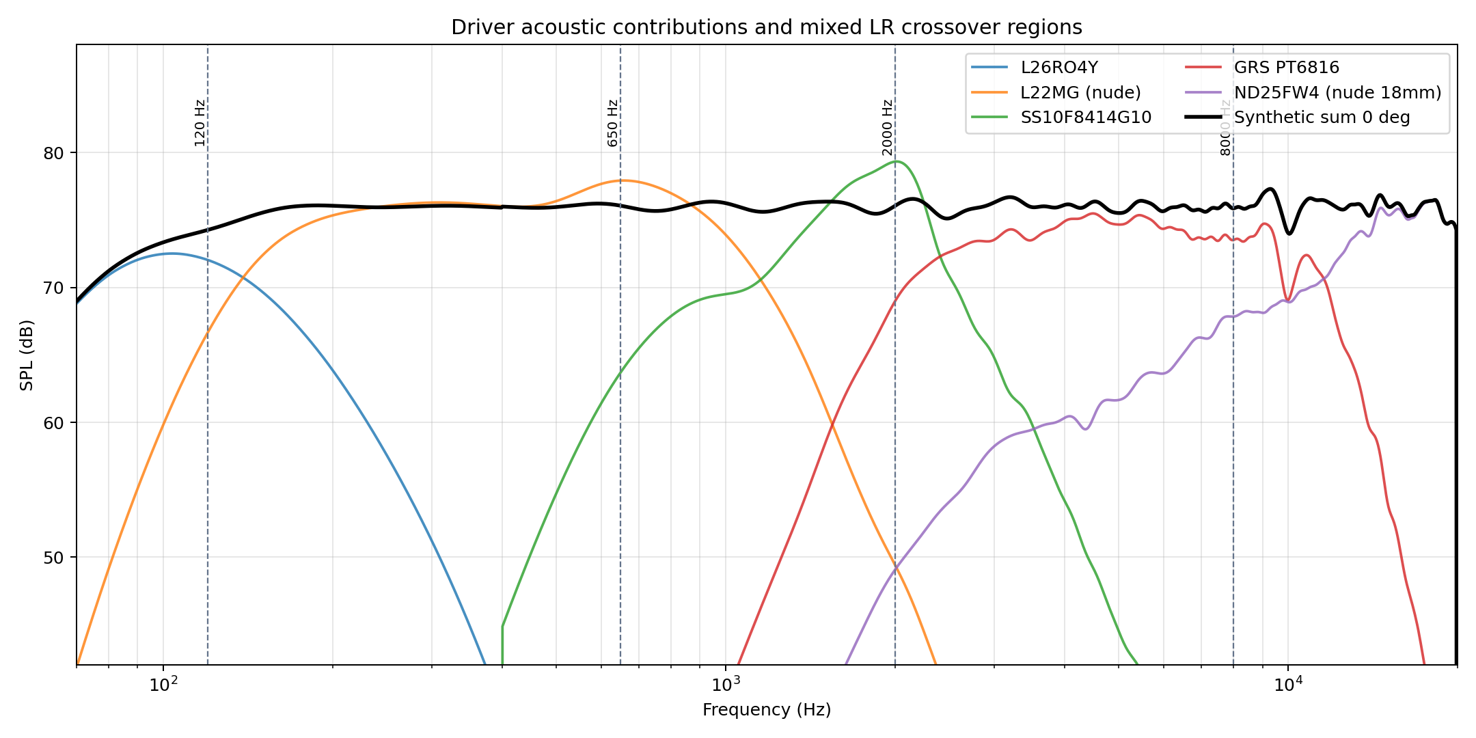
docs/juan-baffleless-cdsl/static_plots/core/cdsl_crossover_regions.png
