antorsae/lx/docs/juan-baffleless-cdsl/static_plots/core/cdsl_di_beamwidth.png

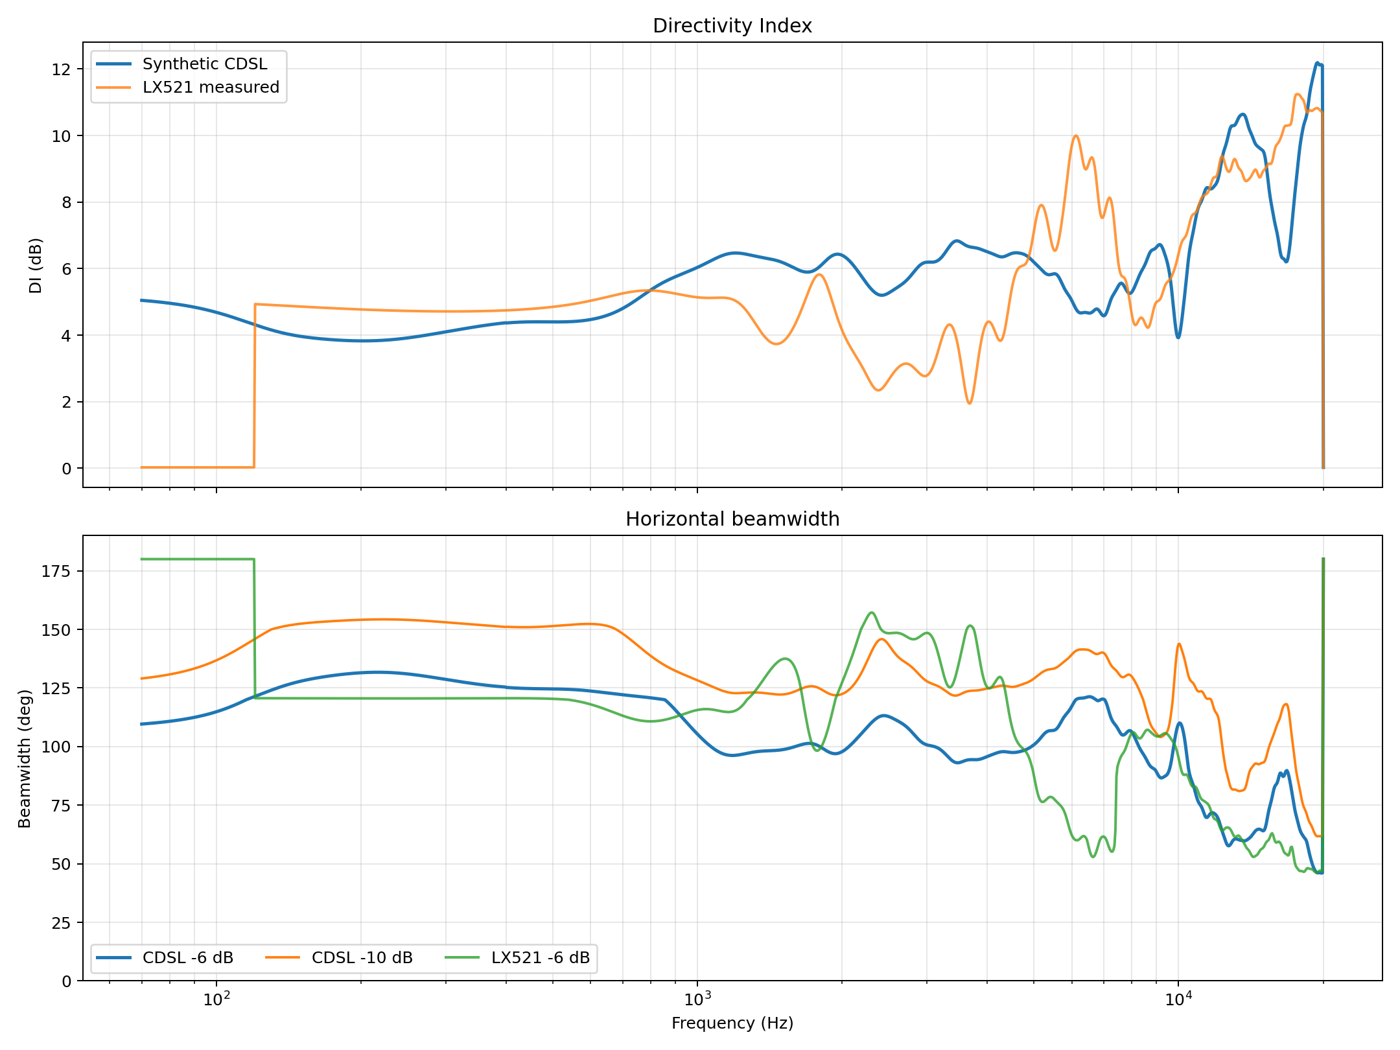
docs/juan-baffleless-cdsl/static_plots/core/cdsl_di_beamwidth.png
