antorsae/lx/docs/juan-baffleless-cdsl/static_plots/core/cdsl_vs_lx521_beamwidth.png

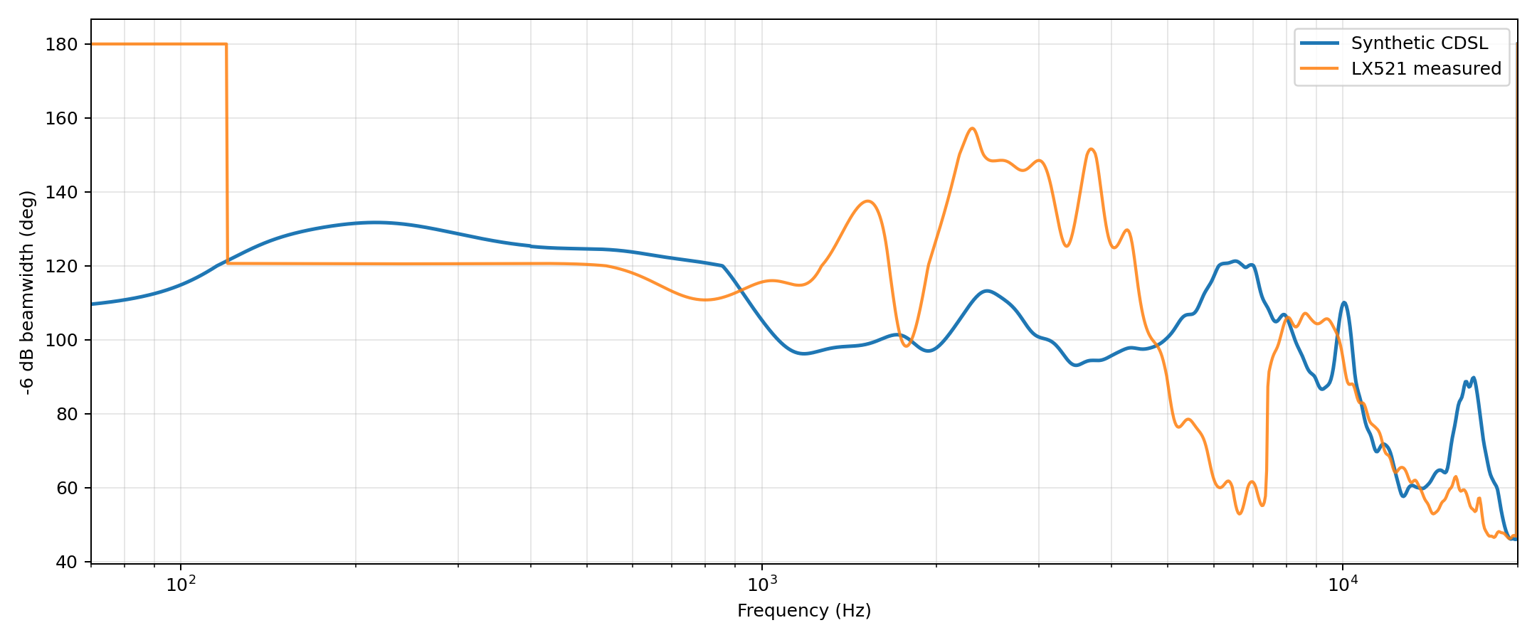
docs/juan-baffleless-cdsl/static_plots/core/cdsl_vs_lx521_beamwidth.png
