antorsae/lx/docs/juan-baffleless-cdsl/static_plots/polar/cdsl_vs_lx521_polar_circular.png

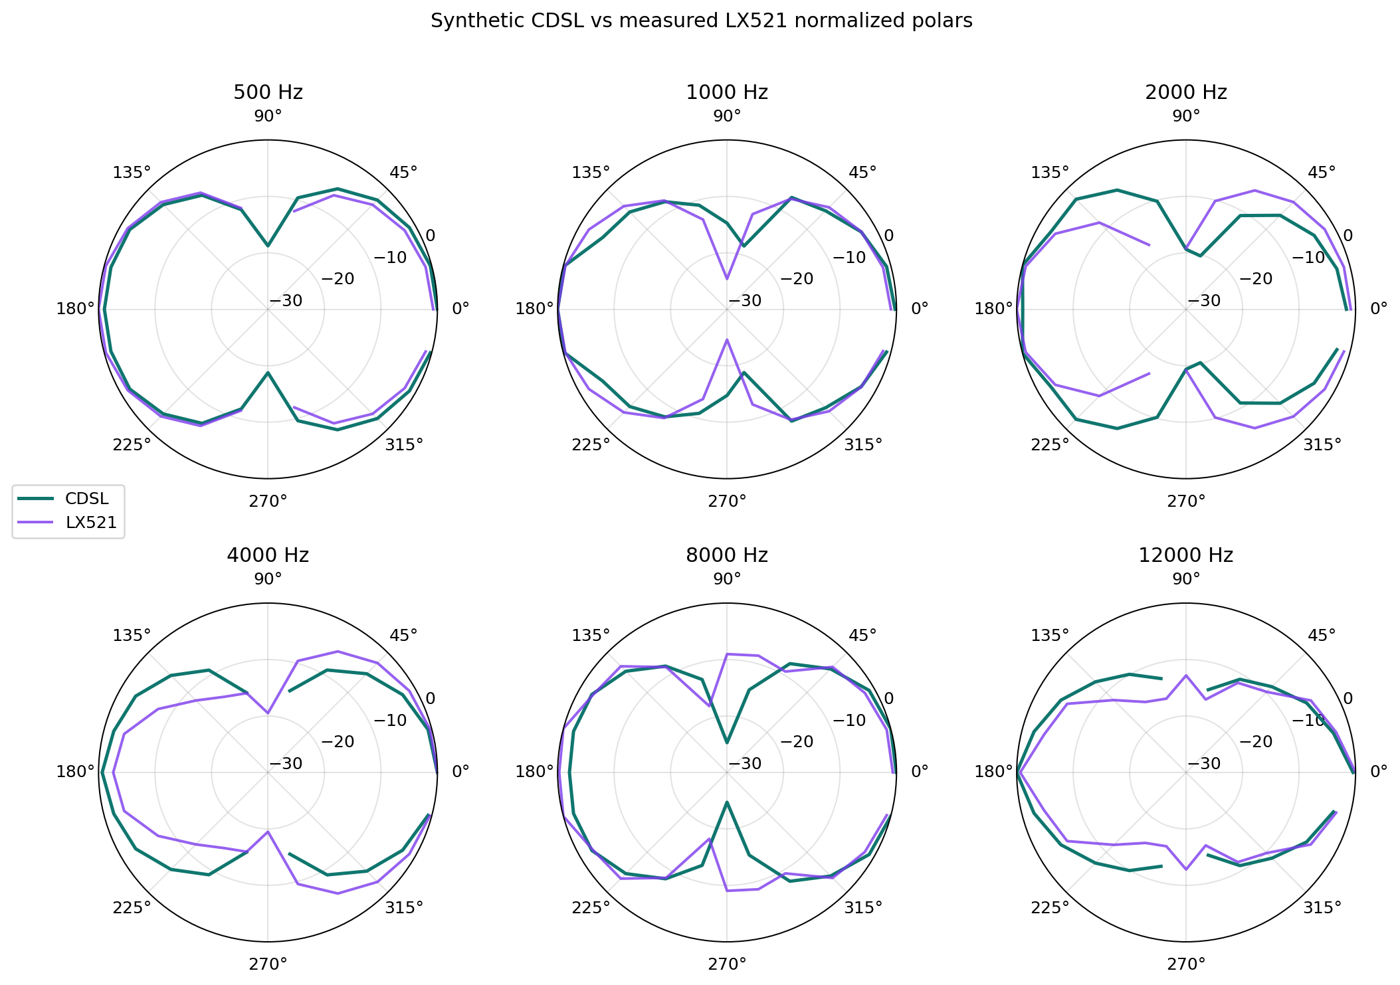
docs/juan-baffleless-cdsl/static_plots/polar/cdsl_vs_lx521_polar_circular.png
