antorsae/lx/docs/juan-baffleless/static_plots/core/beamwidth_comparison.png

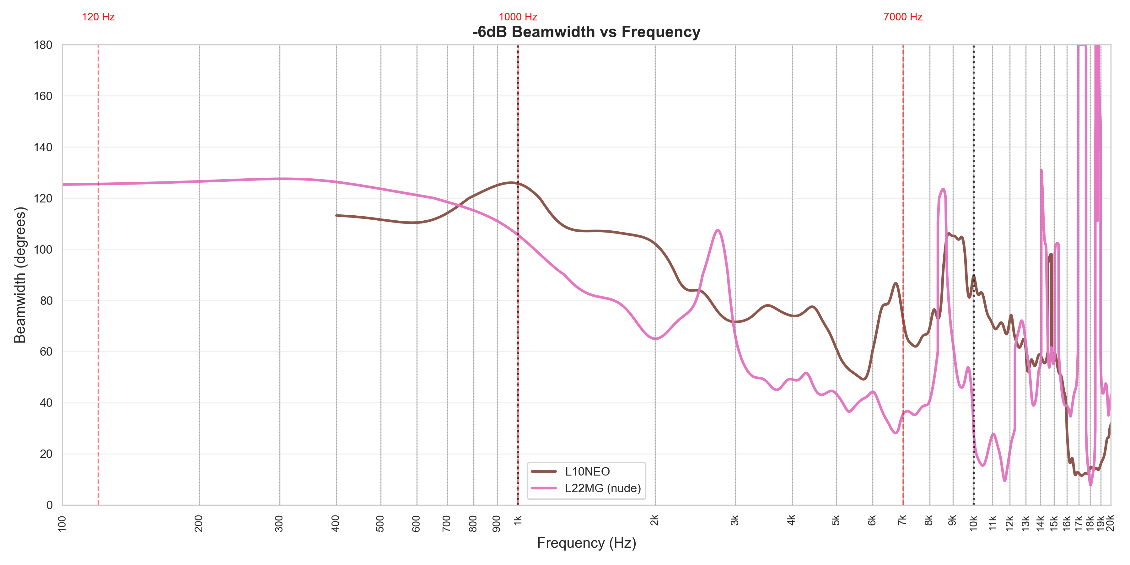
docs/juan-baffleless/static_plots/core/beamwidth_comparison.png
