antorsae/lx/docs/juan-baffleless/static_plots/core/di_comparison.png

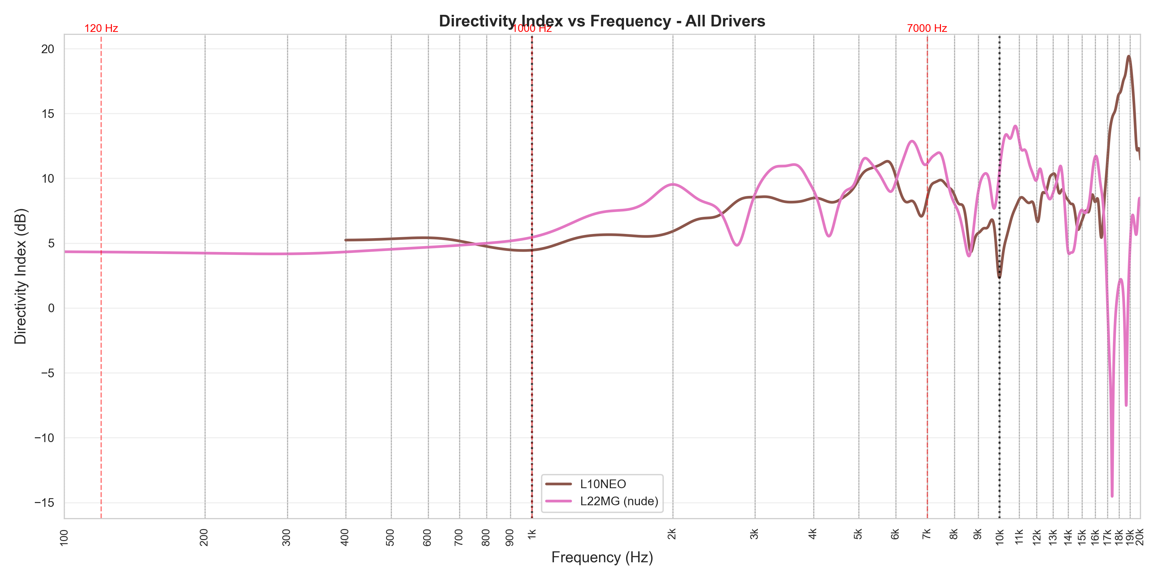
docs/juan-baffleless/static_plots/core/di_comparison.png
