antorsae/lx/docs/juan-baffleless/static_plots/core/dipole_null_analysis.png

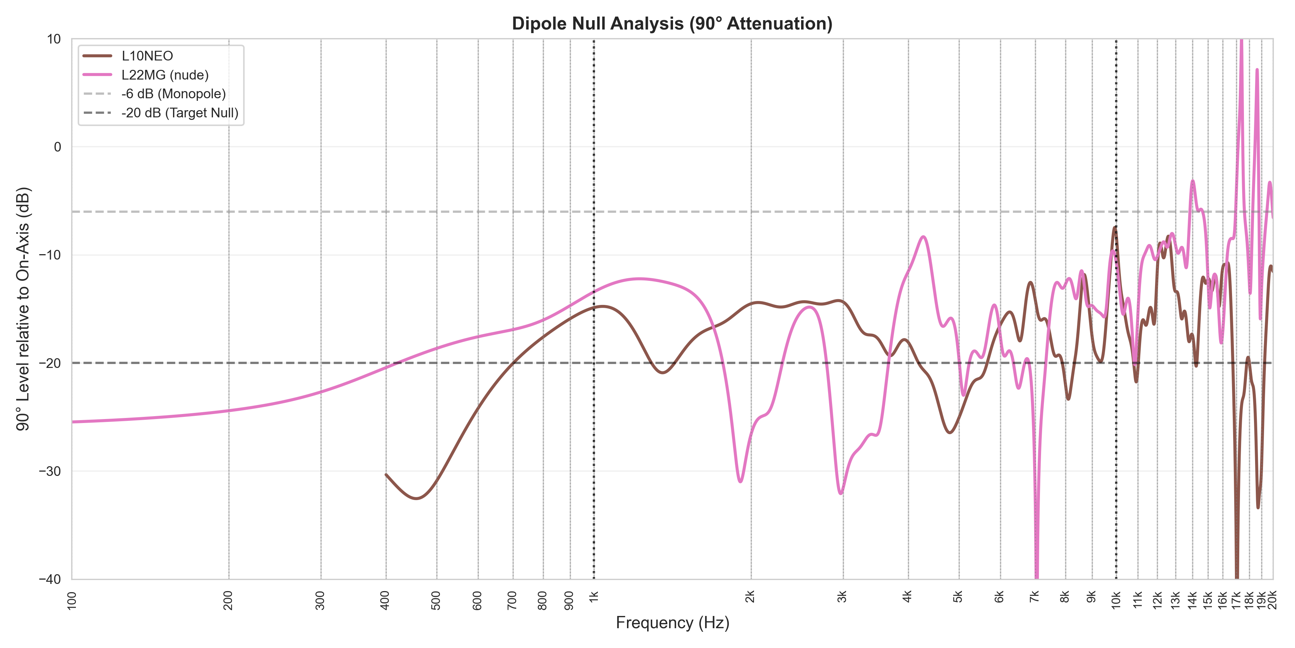
docs/juan-baffleless/static_plots/core/dipole_null_analysis.png
