antorsae/lx/docs/juan-baffleless/static_plots/core/L10NEO_contour_normalized.png

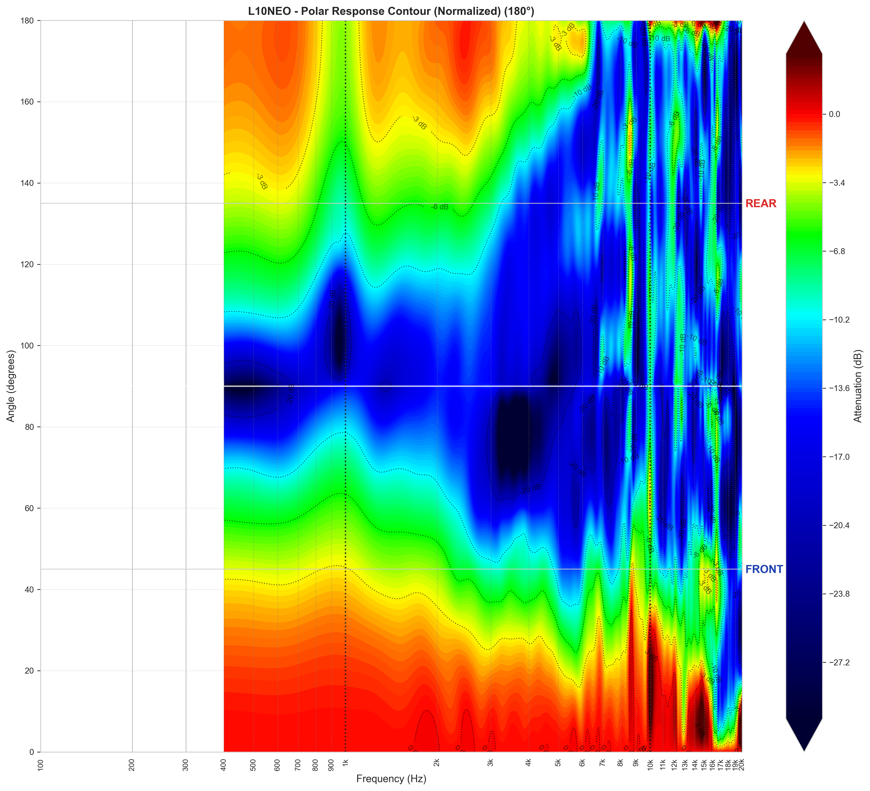
docs/juan-baffleless/static_plots/core/L10NEO_contour_normalized.png
