antorsae/lx/docs/juan-baffleless/static_plots/core/L10NEO_freq_response_angles.png

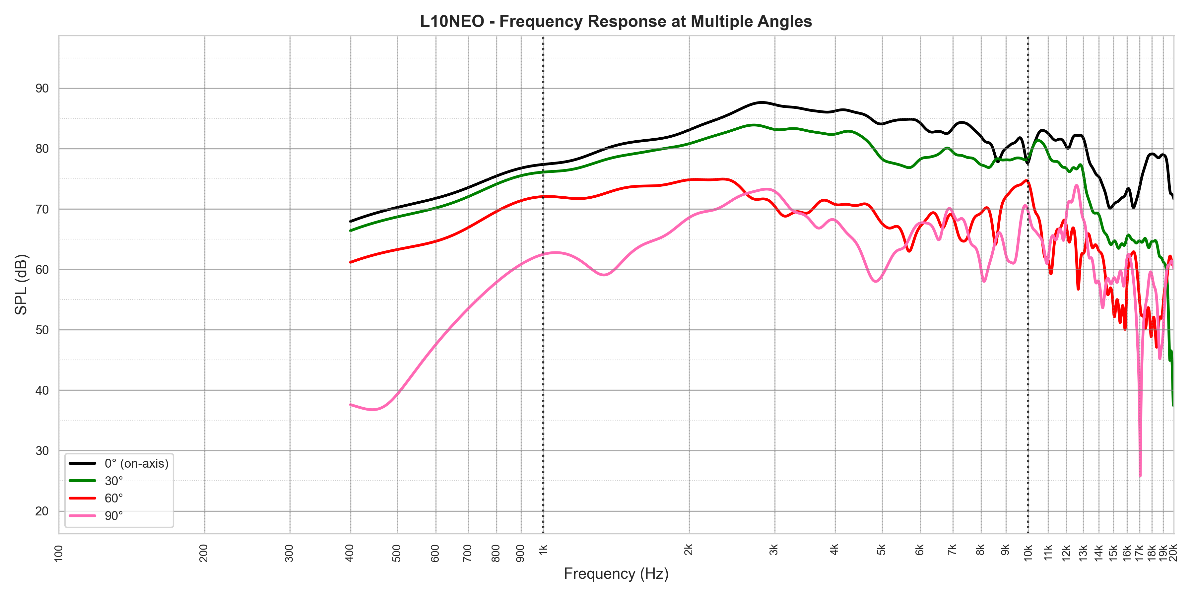
docs/juan-baffleless/static_plots/core/L10NEO_freq_response_angles.png
