antorsae/lx/docs/juan-baffleless/static_plots/core/L22MG (nude)_contour_normalized.png

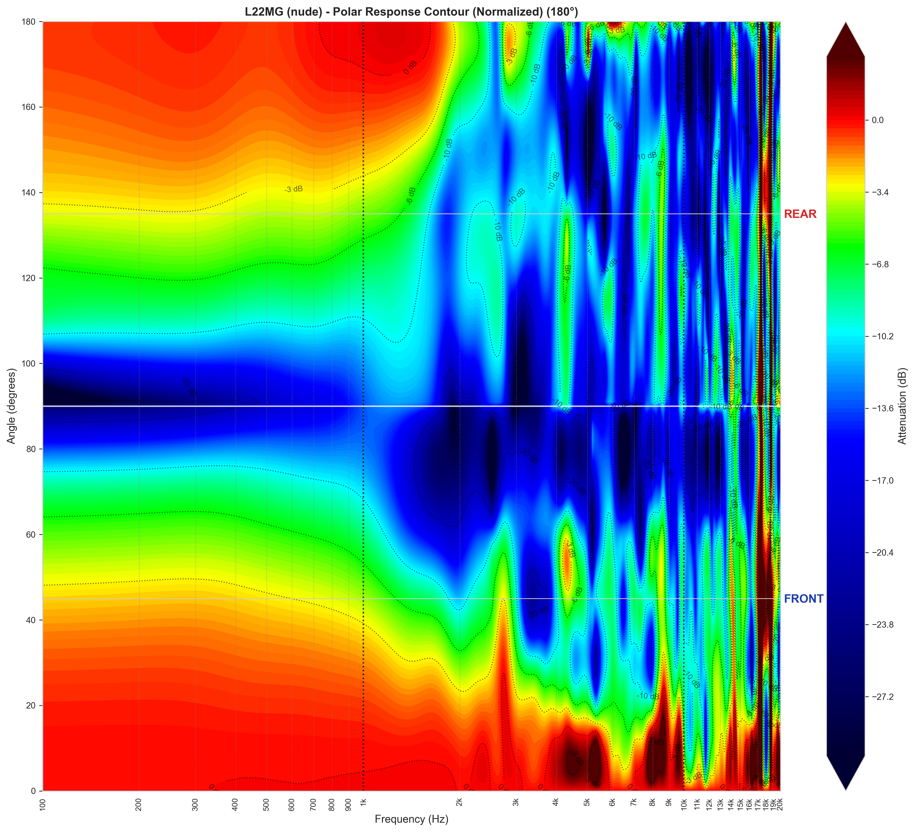
docs/juan-baffleless/static_plots/core/L22MG (nude)_contour_normalized.png
