antorsae/lx/docs/juan-lx521-top-raw/static_plots/core/beamwidth_comparison.png

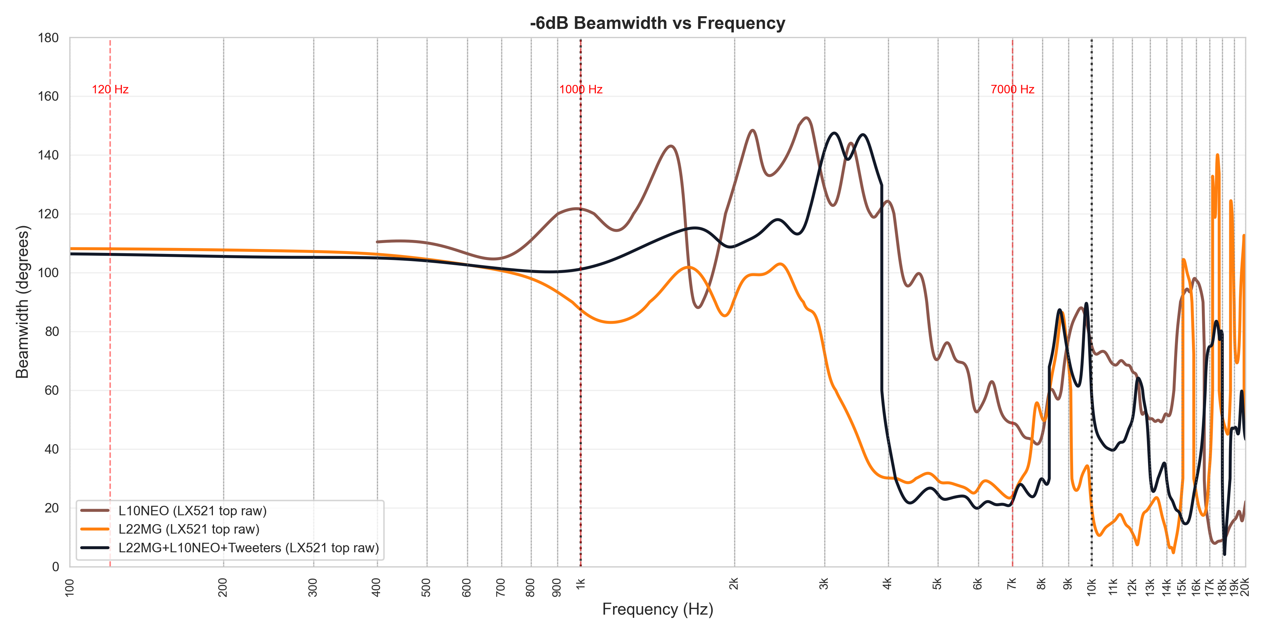
docs/juan-lx521-top-raw/static_plots/core/beamwidth_comparison.png
