antorsae/lx/docs/juan-lx521-top-raw/static_plots/core/di_comparison.png

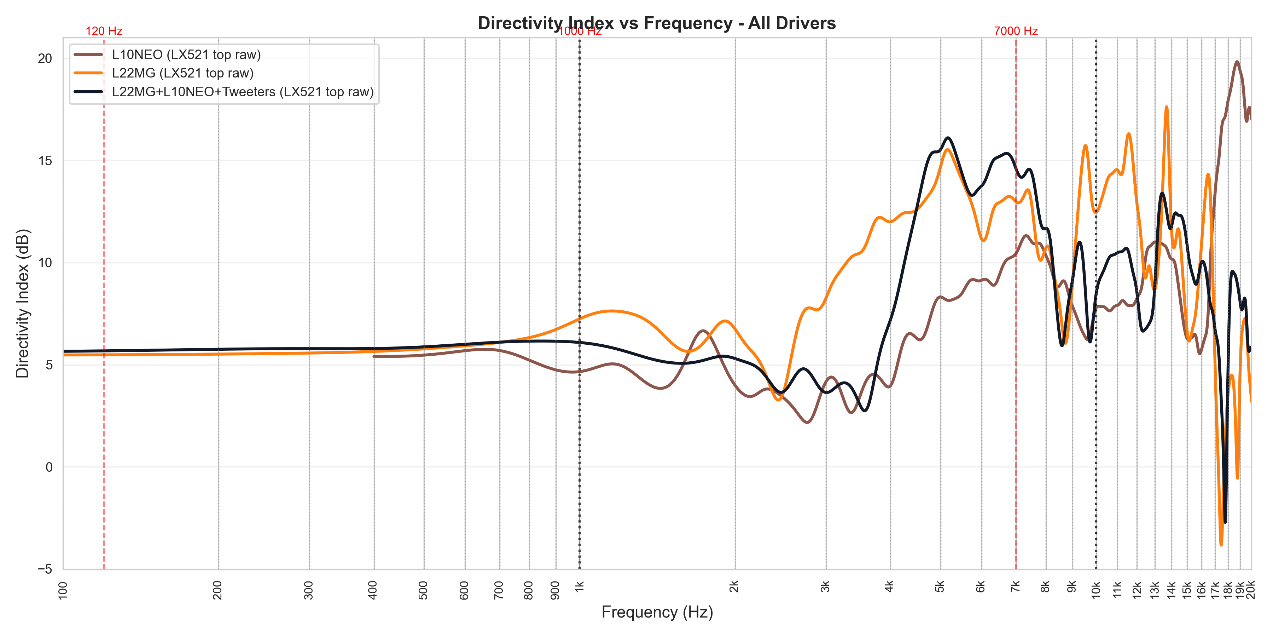
docs/juan-lx521-top-raw/static_plots/core/di_comparison.png
