antorsae/lx/docs/juan-lx521-top-raw/static_plots/core/dipole_null_analysis.png

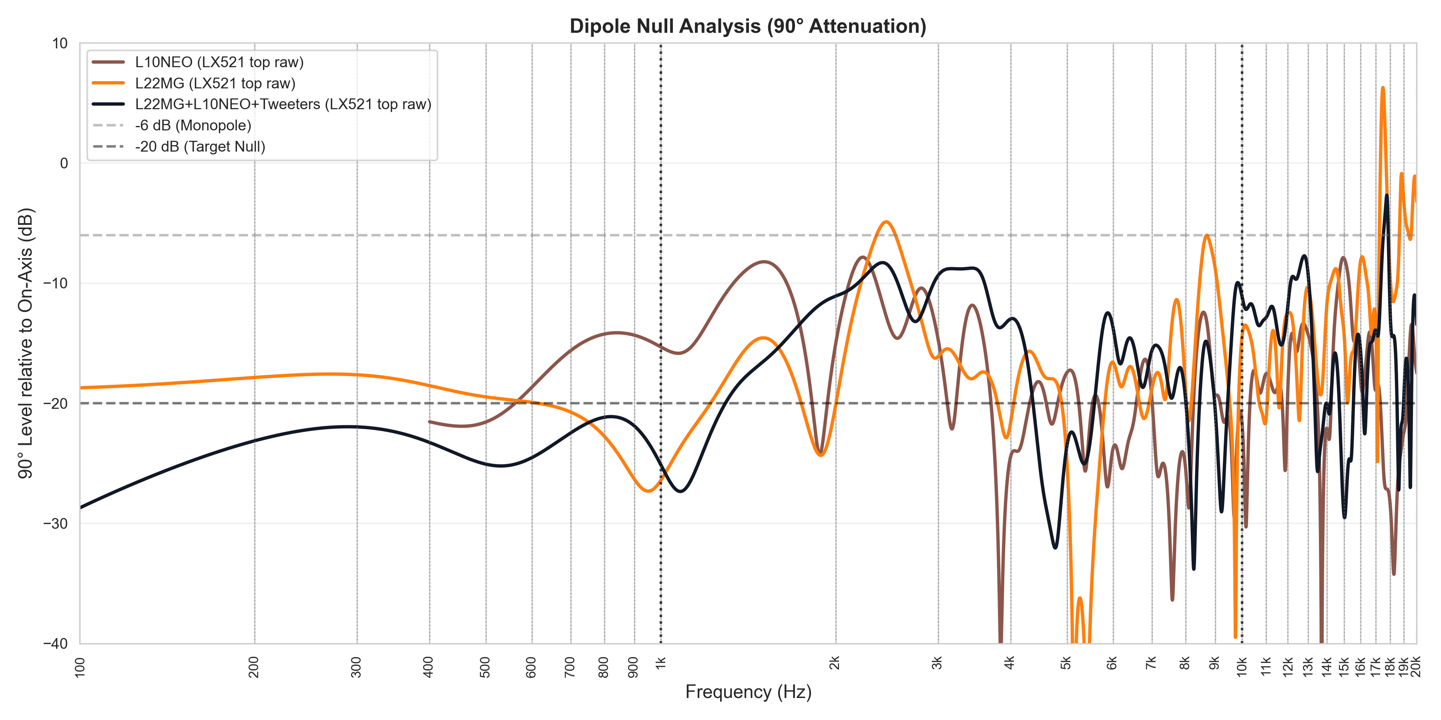
docs/juan-lx521-top-raw/static_plots/core/dipole_null_analysis.png
