antorsae/lx/docs/juan-lx521-top-raw/static_plots/core/L10NEO (LX521 top raw)_contour_absolute.png

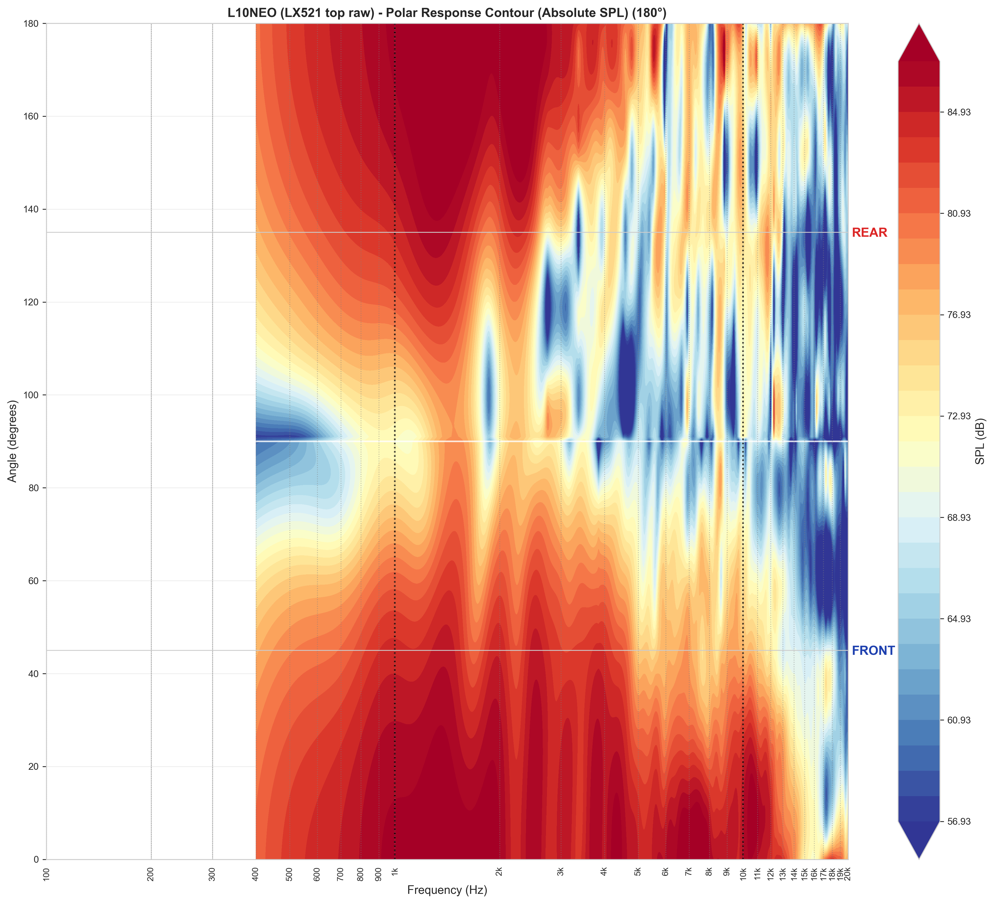
docs/juan-lx521-top-raw/static_plots/core/L10NEO (LX521 top raw)_contour_absolute.png
