antorsae/lx/docs/juan-lx521-top-raw/static_plots/core/L22MG (LX521 top raw)_contour_normalized.png

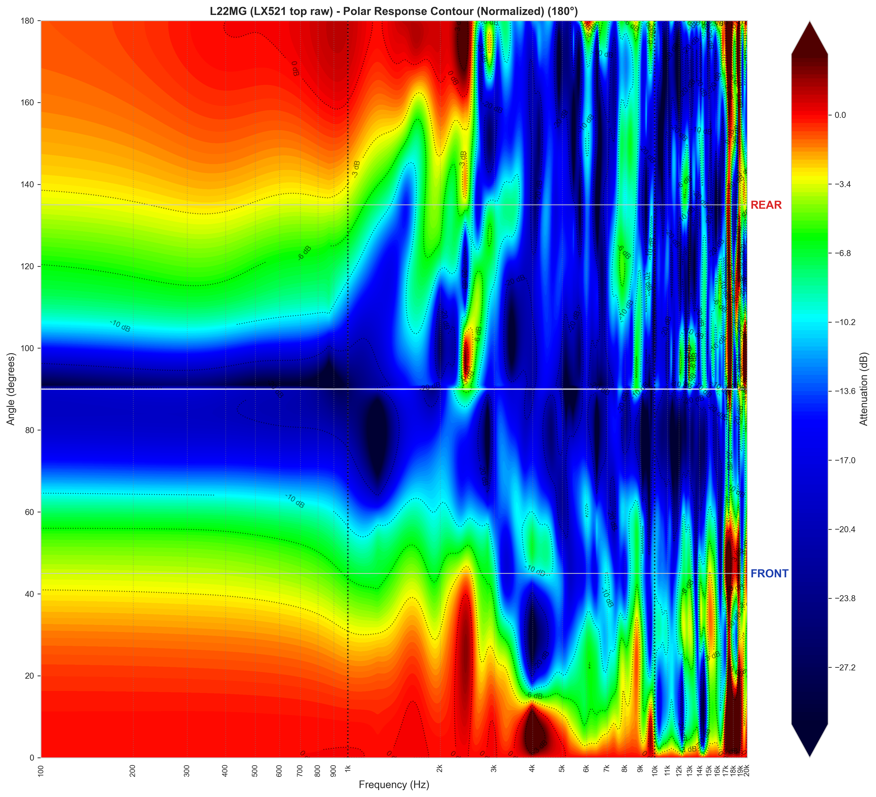
docs/juan-lx521-top-raw/static_plots/core/L22MG (LX521 top raw)_contour_normalized.png
