antorsae/lx/docs/juan-lx521-top-raw/static_plots/core/L22MG+L10NEO+Tweeters (LX521 top raw)_freq_response_angles.png

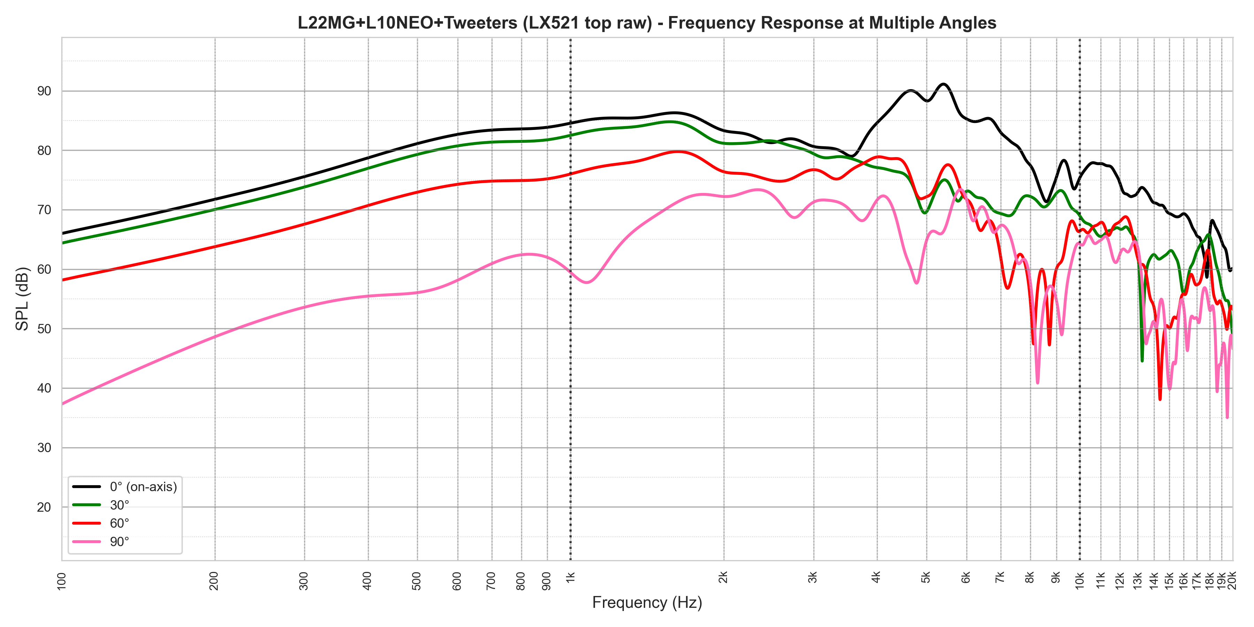
docs/juan-lx521-top-raw/static_plots/core/L22MG+L10NEO+Tweeters (LX521 top raw)_freq_response_angles.png
