antorsae/lx/docs/juan-lx521-top-raw/static_plots/polar/L22MG+L10NEO+Tweeters (LX521 top raw)_polar_circular.png

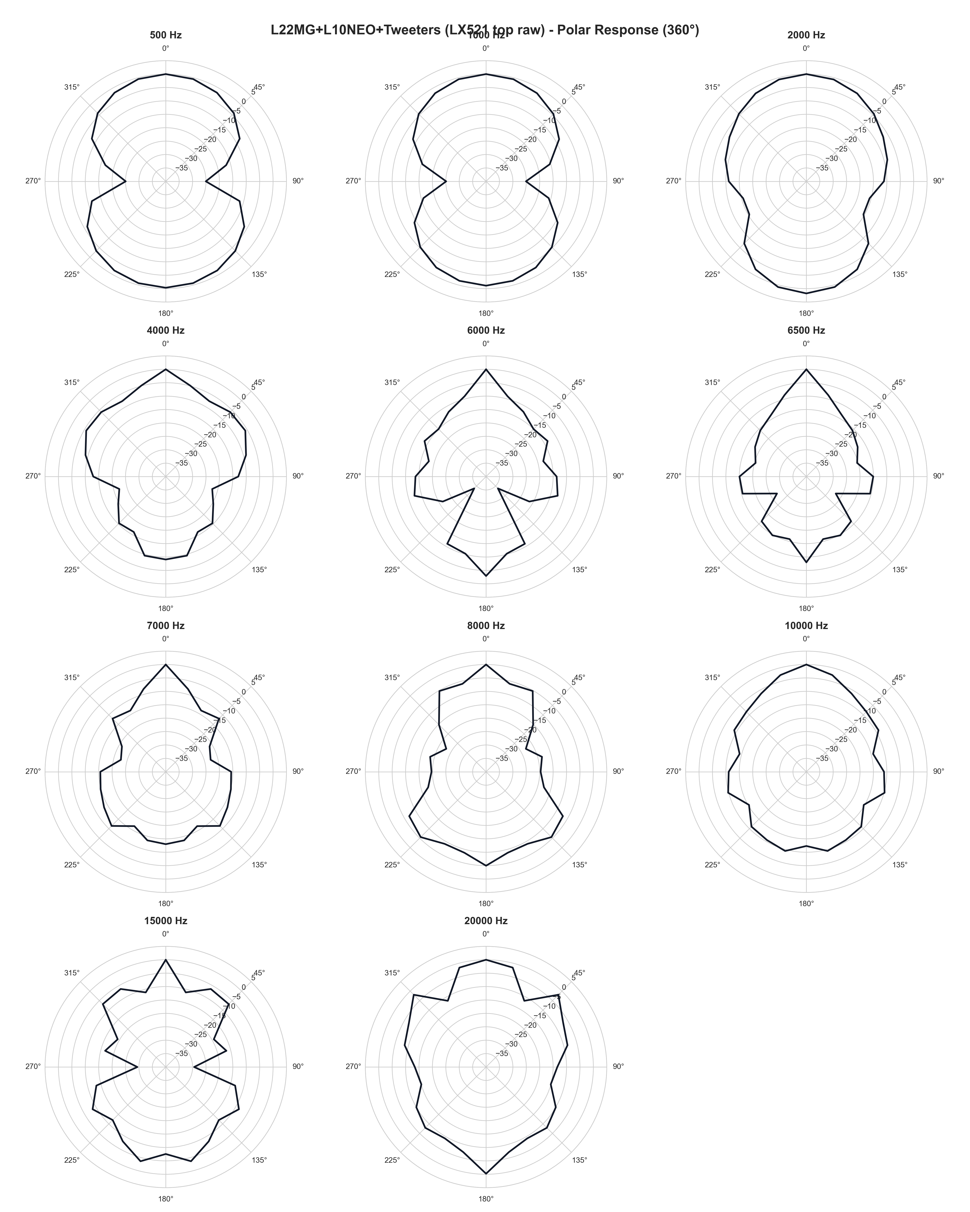
docs/juan-lx521-top-raw/static_plots/polar/L22MG+L10NEO+Tweeters (LX521 top raw)_polar_circular.png
