antorsae/lx/docs/lx521-system/static_plots/core/di_comparison.png

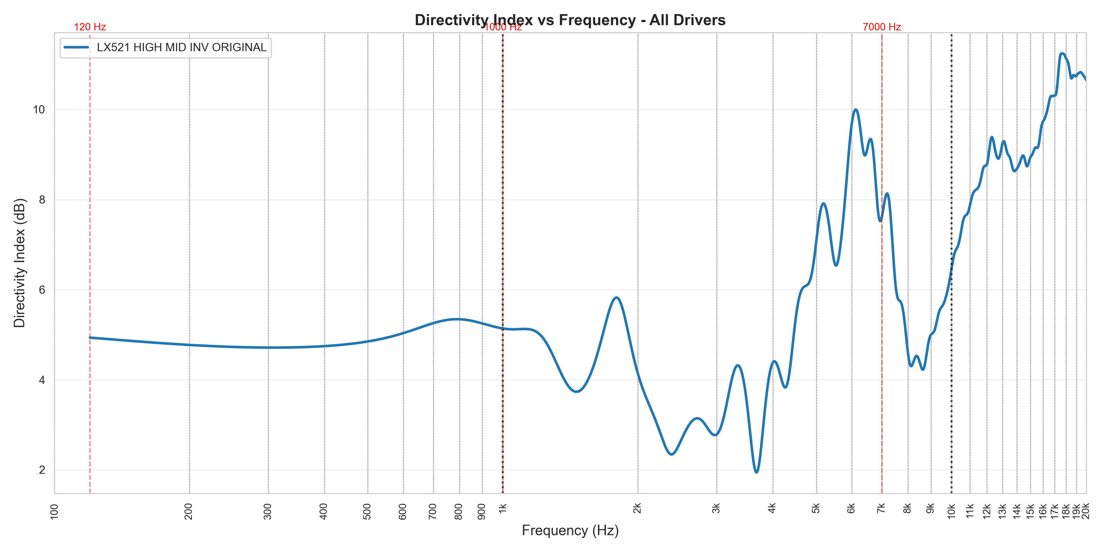
docs/lx521-system/static_plots/core/di_comparison.png
