antorsae/lx/docs/lx521-system/static_plots/core/LX521 HIGH MID INV ORIGINAL_freq_response_normalized.png

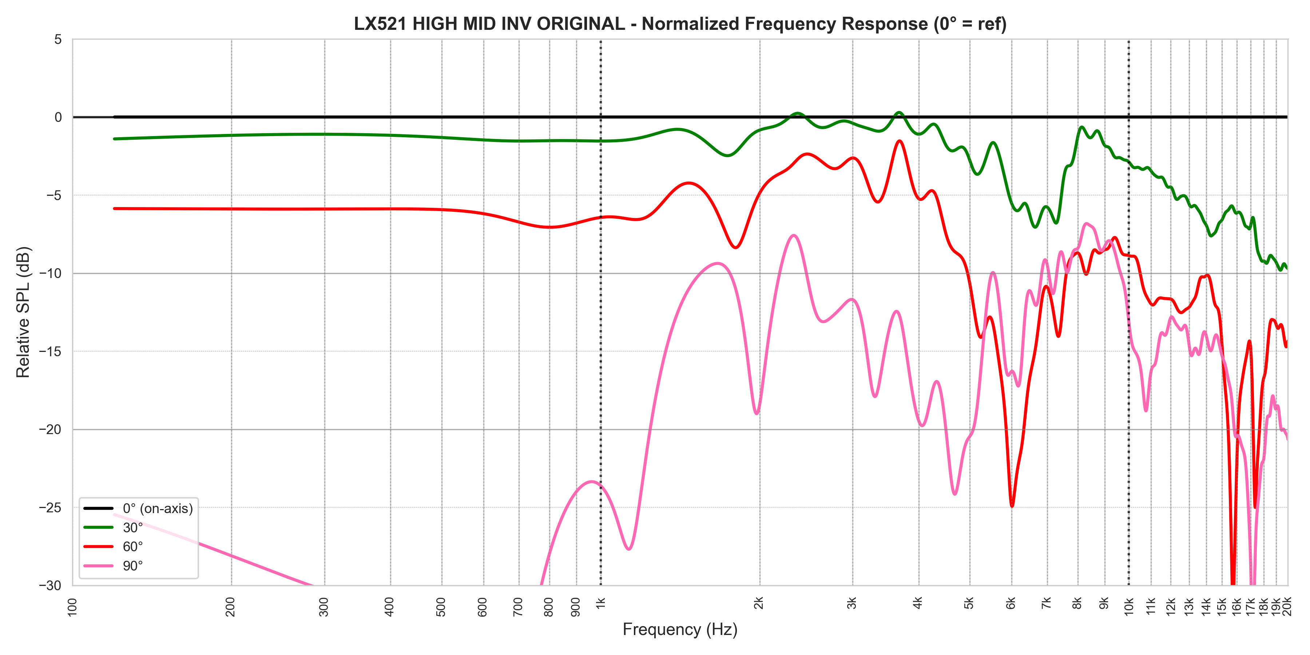
docs/lx521-system/static_plots/core/LX521 HIGH MID INV ORIGINAL_freq_response_normalized.png
