antorsae/lx/top_baffle_v2/build/common/obiwan_wing_design_map.png

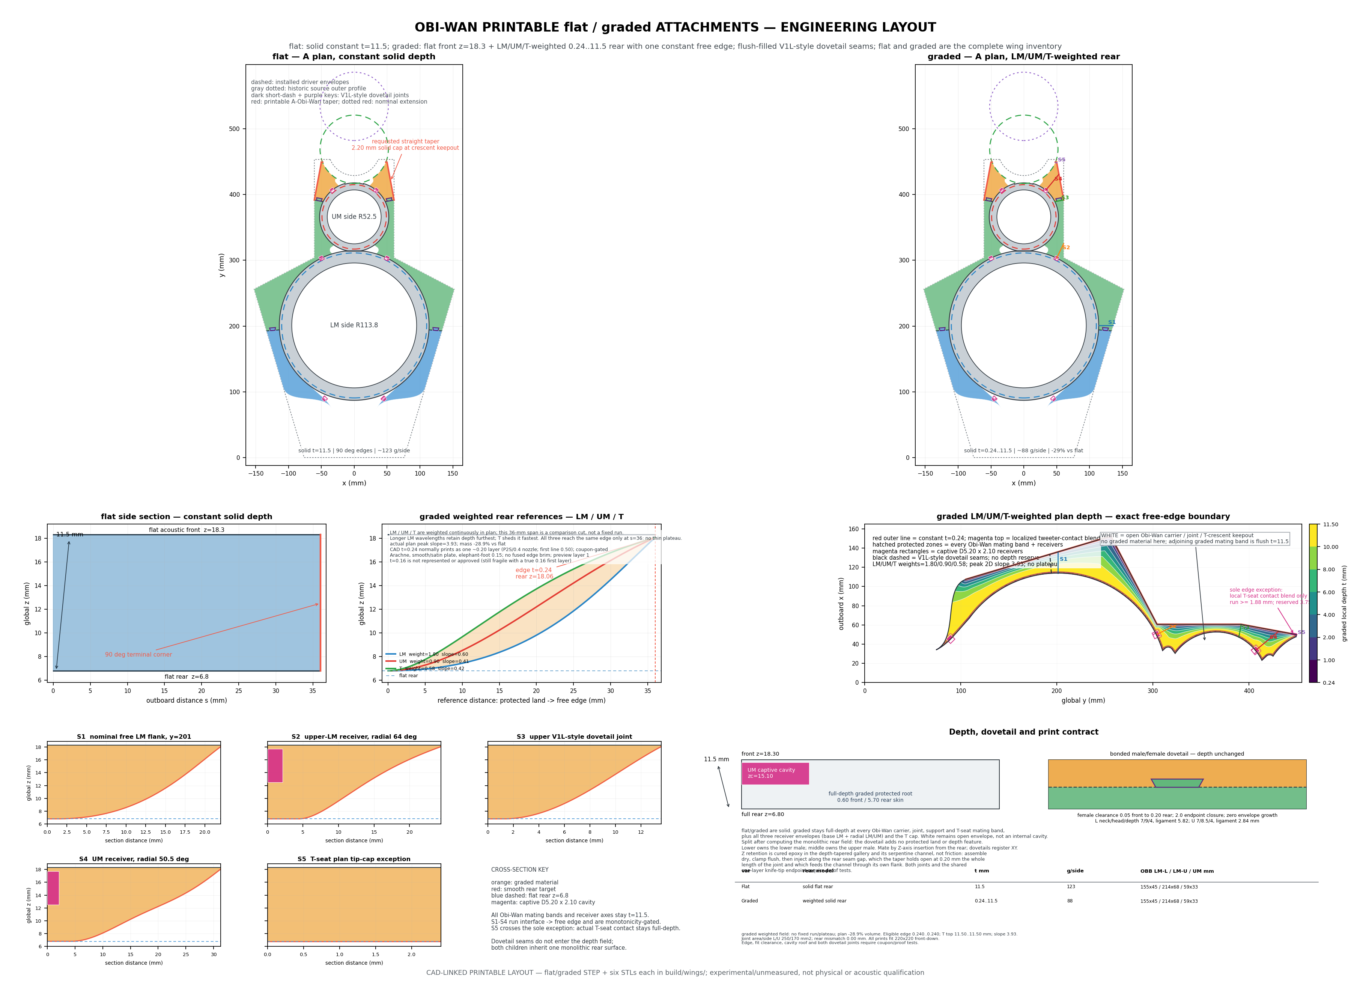
top_baffle_v2/build/common/obiwan_wing_design_map.png
