antorsae/lx/top_baffle_v2/images/generated/catalog/ALL_ITEMS_MAGNET_CATALOG.png

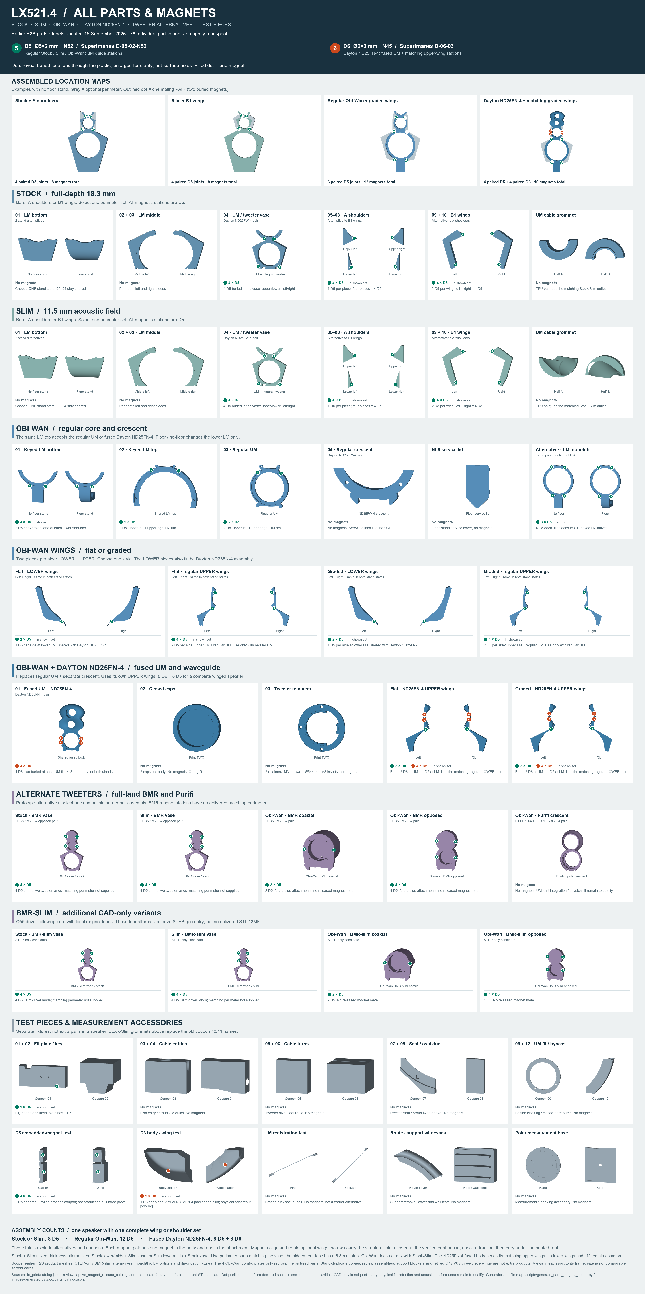
top_baffle_v2/images/generated/catalog/ALL_ITEMS_MAGNET_CATALOG.png
