antorsae/lx/top_baffle_v2/images/generated/catalog/tiles/01_D6_body_coupon_363x264.png

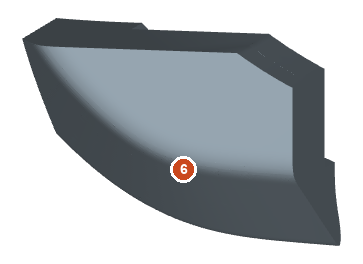
top_baffle_v2/images/generated/catalog/tiles/01_D6_body_coupon_363x264.png
