antorsae/lx/top_baffle_v2/images/generated/catalog/tiles/bmr_coaxial_736x304.png

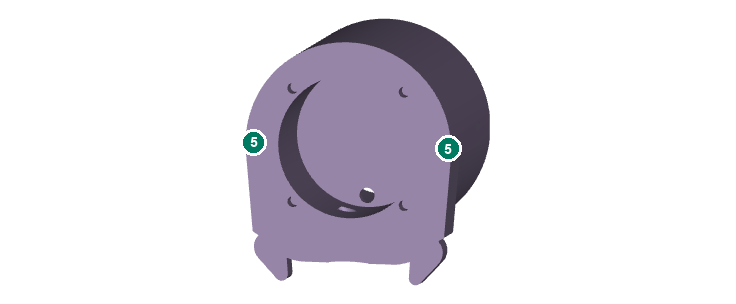
top_baffle_v2/images/generated/catalog/tiles/bmr_coaxial_736x304.png
