antorsae/lx/top_baffle_v2/images/generated/catalog/tiles/bmr_slim_opposed_939x244.png

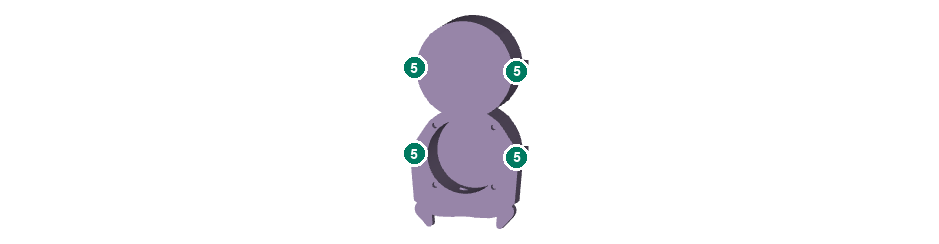
top_baffle_v2/images/generated/catalog/tiles/bmr_slim_opposed_939x244.png
