antorsae/lx/top_baffle_v2/images/generated/catalog/tiles/coupon_1_363x264.png

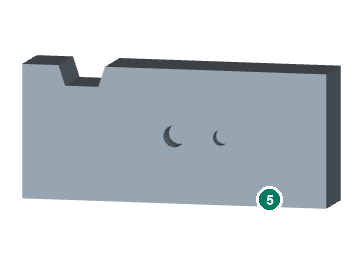
top_baffle_v2/images/generated/catalog/tiles/coupon_1_363x264.png
