antorsae/lx/top_baffle_v2/images/generated/catalog/tiles/native_route_cover_363x264.png

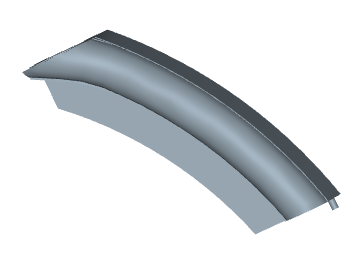
top_baffle_v2/images/generated/catalog/tiles/native_route_cover_363x264.png
