antorsae/lx/top_baffle_v2/images/generated/catalog/tiles/obi_monolith_no_floor_stand_295x324.png

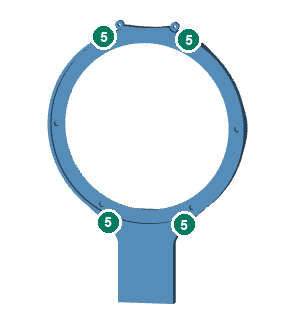
top_baffle_v2/images/generated/catalog/tiles/obi_monolith_no_floor_stand_295x324.png
