antorsae/lx/top_baffle_v2/images/generated/catalog/tiles/obiwan_01_LM_bottom_keyed_1_of_2_floor_stand_295x324.png

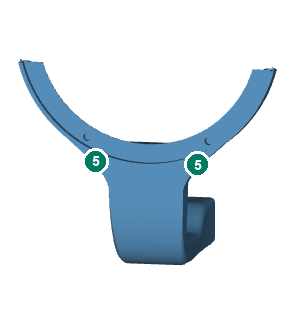
top_baffle_v2/images/generated/catalog/tiles/obiwan_01_LM_bottom_keyed_1_of_2_floor_stand_295x324.png
