antorsae/lx/top_baffle_v2/images/generated/catalog/tiles/obiwan_02_LM_top_keyed_2_of_2_600x324.png

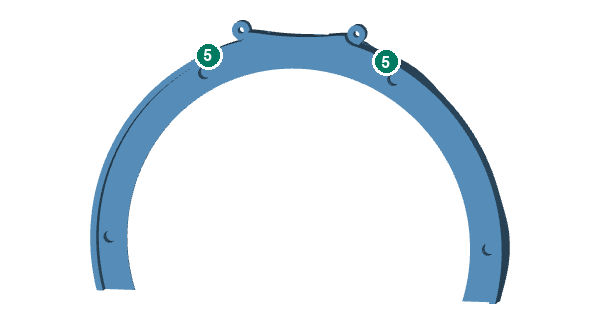
top_baffle_v2/images/generated/catalog/tiles/obiwan_02_LM_top_keyed_2_of_2_600x324.png
