antorsae/lx/top_baffle_v2/images/generated/catalog/tiles/obiwan_03_UM_carrier_1_of_1_600x324.png

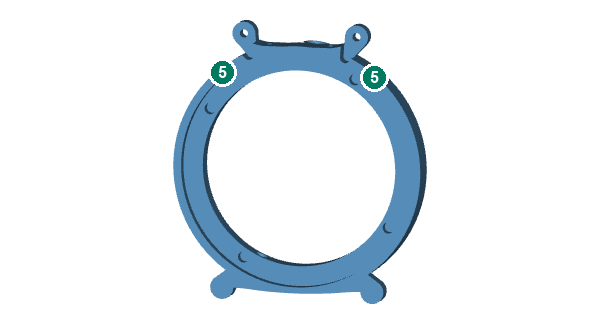
top_baffle_v2/images/generated/catalog/tiles/obiwan_03_UM_carrier_1_of_1_600x324.png
