antorsae/lx/top_baffle_v2/images/generated/catalog/tiles/obiwan_04_T_tweeter_crescent_1_of_1_600x324.png

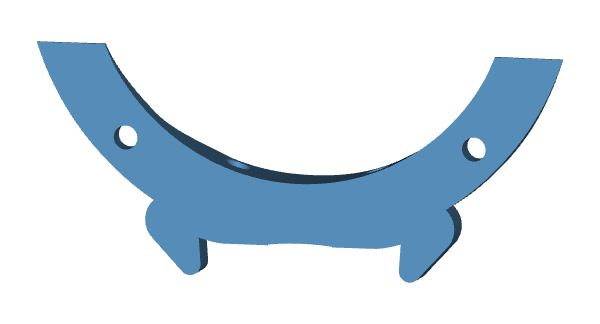
top_baffle_v2/images/generated/catalog/tiles/obiwan_04_T_tweeter_crescent_1_of_1_600x324.png
