antorsae/lx/top_baffle_v2/images/generated/catalog/tiles/obiwan_wing_flat_left_split2_1_of_2_lm_lower_464x294.png

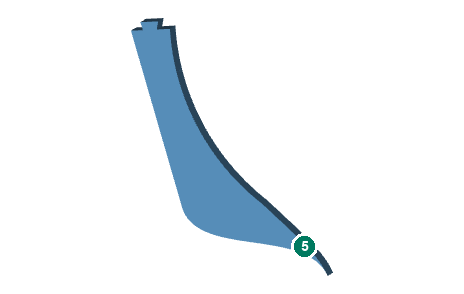
top_baffle_v2/images/generated/catalog/tiles/obiwan_wing_flat_left_split2_1_of_2_lm_lower_464x294.png
