antorsae/lx/top_baffle_v2/images/generated/catalog/tiles/obiwan_wing_flat_left_split2_2_of_2_lm_um_upper_464x294.png

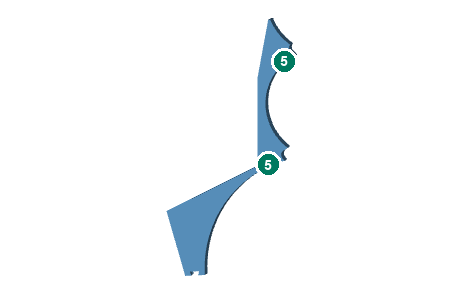
top_baffle_v2/images/generated/catalog/tiles/obiwan_wing_flat_left_split2_2_of_2_lm_um_upper_464x294.png
