antorsae/lx/top_baffle_v2/images/generated/catalog/tiles/polar_1of2_base_363x264.png

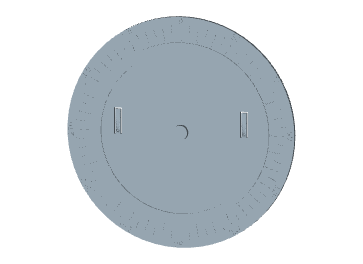
top_baffle_v2/images/generated/catalog/tiles/polar_1of2_base_363x264.png
