antorsae/lx/top_baffle_v2/images/generated/catalog/tiles/purifi_736x304.png

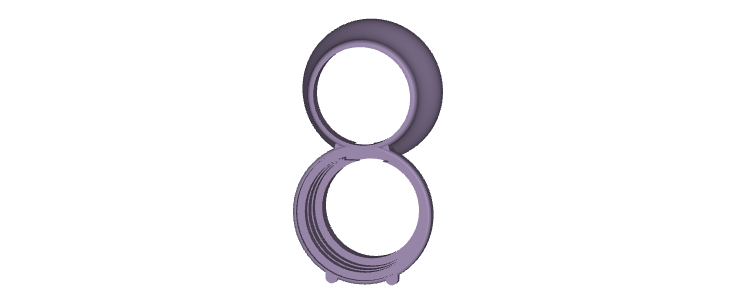
top_baffle_v2/images/generated/catalog/tiles/purifi_736x304.png
