antorsae/lx/top_baffle_v2/images/generated/catalog/tiles/registration_male_pin_363x264.png

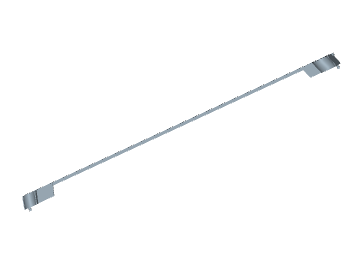
top_baffle_v2/images/generated/catalog/tiles/registration_male_pin_363x264.png
