antorsae/lx/top_baffle_v2/images/generated/catalog/tiles/slim_02_LM_mid_left_2_of_3_295x294.png

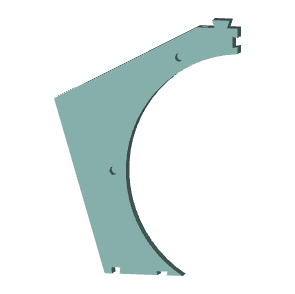
top_baffle_v2/images/generated/catalog/tiles/slim_02_LM_mid_left_2_of_3_295x294.png
