antorsae/lx/top_baffle_v2/images/generated/catalog/tiles/slim_03_LM_mid_right_3_of_3_295x294.png

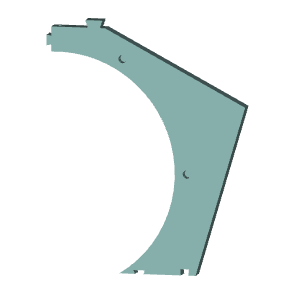
top_baffle_v2/images/generated/catalog/tiles/slim_03_LM_mid_right_3_of_3_295x294.png
