antorsae/lx/top_baffle_v2/images/generated/catalog/tiles/slim_04_UM_vase_1_of_1_600x294.png

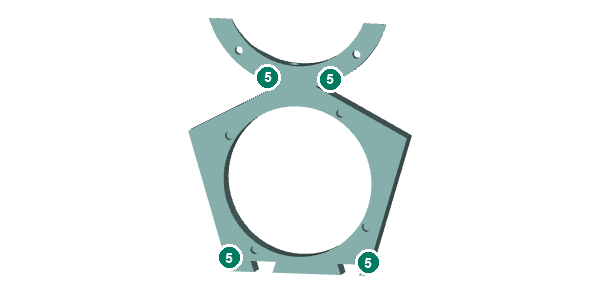
top_baffle_v2/images/generated/catalog/tiles/slim_04_UM_vase_1_of_1_600x294.png
