antorsae/lx/top_baffle_v2/images/generated/catalog/tiles/slim_06_A_shoulder_top_left_2_of_4_295x129.png

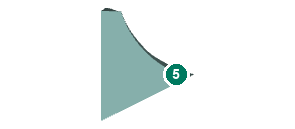
top_baffle_v2/images/generated/catalog/tiles/slim_06_A_shoulder_top_left_2_of_4_295x129.png
