antorsae/lx/top_baffle_v2/images/generated/catalog/tiles/slim_08_A_shoulder_top_right_4_of_4_295x129.png

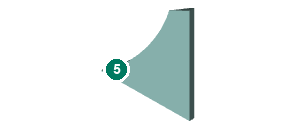
top_baffle_v2/images/generated/catalog/tiles/slim_08_A_shoulder_top_right_4_of_4_295x129.png
