antorsae/lx/top_baffle_v2/images/generated/catalog/tiles/slim_09_B1_wing_left_1_of_2_295x294.png

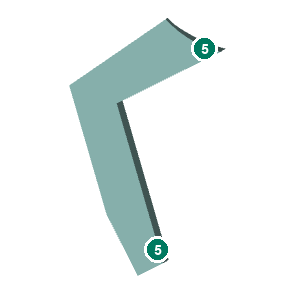
top_baffle_v2/images/generated/catalog/tiles/slim_09_B1_wing_left_1_of_2_295x294.png
