antorsae/lx/top_baffle_v2/images/generated/catalog/tiles/slim_10_B1_wing_right_2_of_2_295x294.png

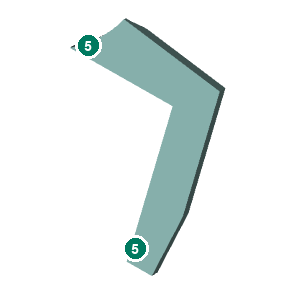
top_baffle_v2/images/generated/catalog/tiles/slim_10_B1_wing_right_2_of_2_295x294.png
