antorsae/lx/top_baffle_v2/images/generated/catalog/tiles/slim_grommet_b_295x294.png

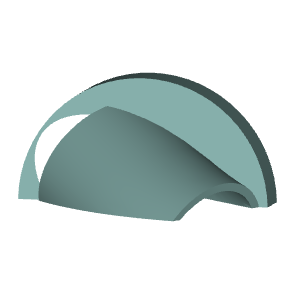
top_baffle_v2/images/generated/catalog/tiles/slim_grommet_b_295x294.png
