antorsae/lx/top_baffle_v2/images/generated/catalog/tiles/stock_01_LM_bottom_1_of_3_no_floor_stand_295x294.png

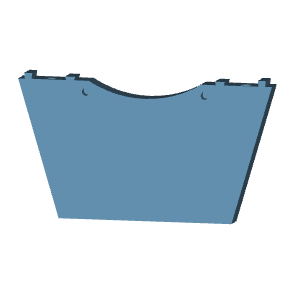
top_baffle_v2/images/generated/catalog/tiles/stock_01_LM_bottom_1_of_3_no_floor_stand_295x294.png
