antorsae/lx/top_baffle_v2/images/generated/catalog/tiles/stock_grommet_b_295x294.png

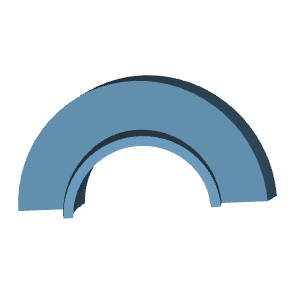
top_baffle_v2/images/generated/catalog/tiles/stock_grommet_b_295x294.png
