antorsae/lx/top_baffle_v2/images/generated/catalog/tiles/v4_cap_736x354.png

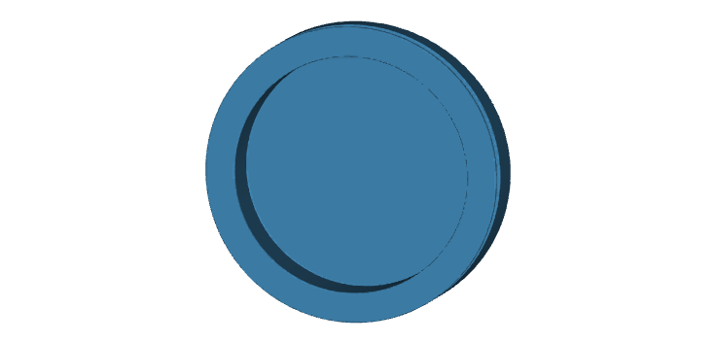
top_baffle_v2/images/generated/catalog/tiles/v4_cap_736x354.png
