antorsae/lx/top_baffle_v2/images/generated/catalog/tiles/v4_graded_right_363x354.png

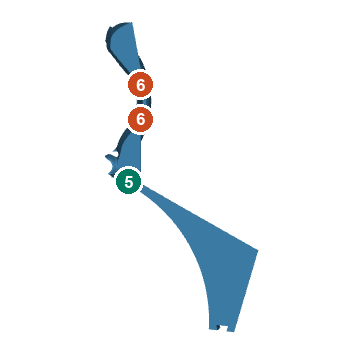
top_baffle_v2/images/generated/catalog/tiles/v4_graded_right_363x354.png
