antorsae/lx/top_baffle_v2/images/generated/iso/obiwan_floor_stand.png

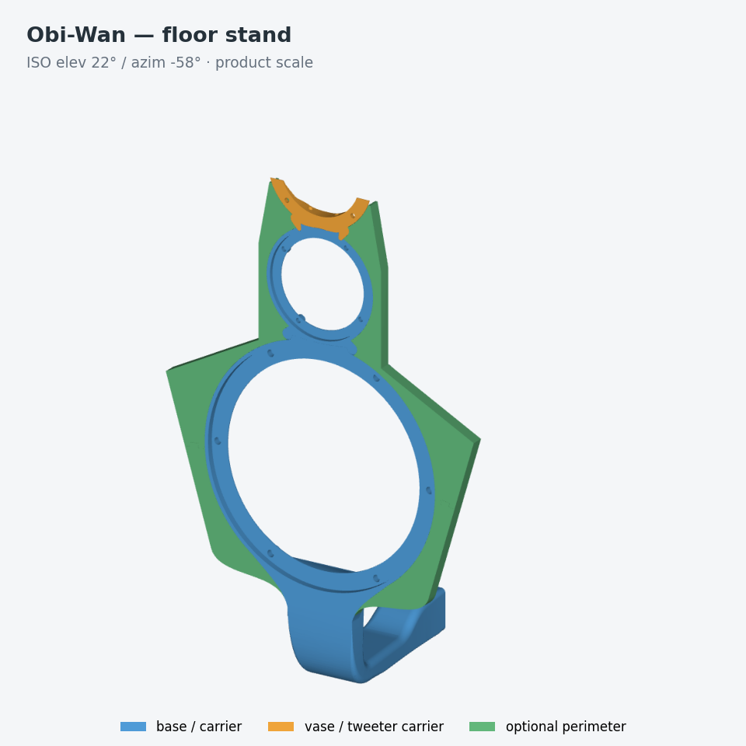
top_baffle_v2/images/generated/iso/obiwan_floor_stand.png
