antorsae/lx/top_baffle_v2/images/generated/iso/tweeter_nd25fw4_crescent.png

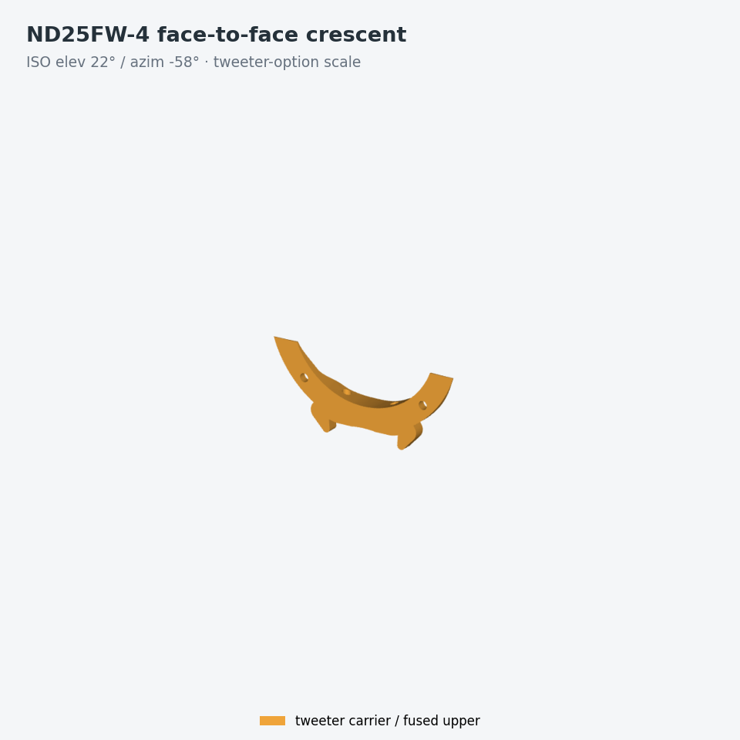
top_baffle_v2/images/generated/iso/tweeter_nd25fw4_crescent.png
