antorsae/lx/top_baffle_v2/images/generated/iso/tweeter_tebm35c10_4_crescent.png

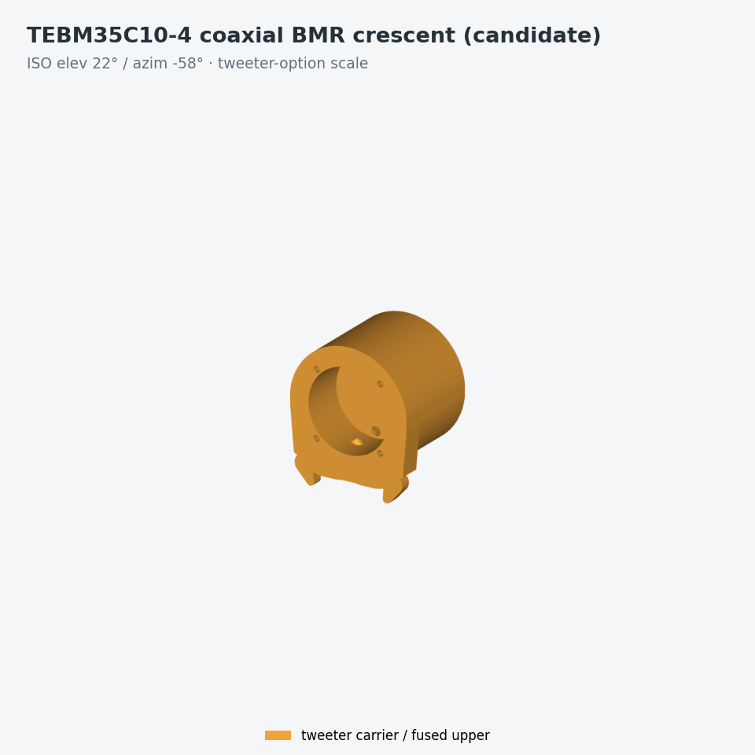
top_baffle_v2/images/generated/iso/tweeter_tebm35c10_4_crescent.png
