antorsae/lx/top_baffle_v2/images/generated/obiwan/floor/core_iso_20260718T100002Z.png

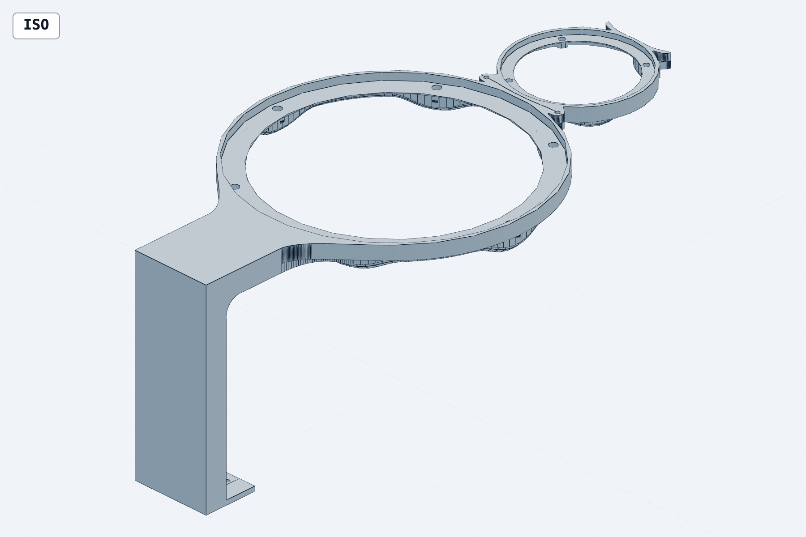
top_baffle_v2/images/generated/obiwan/floor/core_iso_20260718T100002Z.png
