antorsae/lx/top_baffle_v2/images/generated/obiwan/floor/core_iso_opposite_20260718T100009Z.png

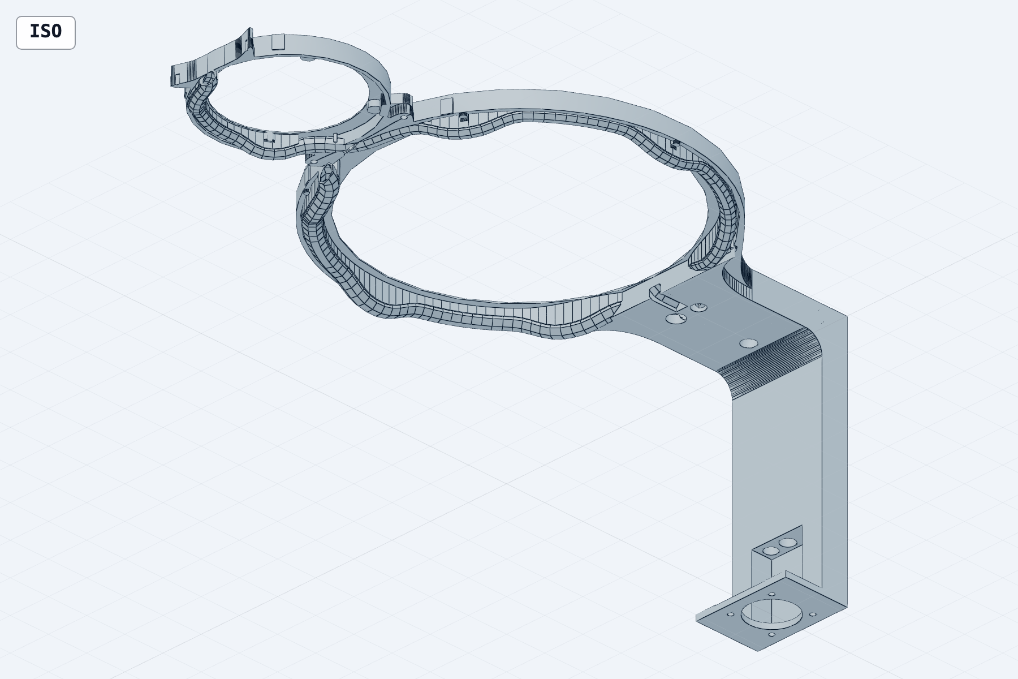
top_baffle_v2/images/generated/obiwan/floor/core_iso_opposite_20260718T100009Z.png
