antorsae/lx/top_baffle_v2/images/generated/obiwan/no_floor/core_front_20260718T100000Z.png

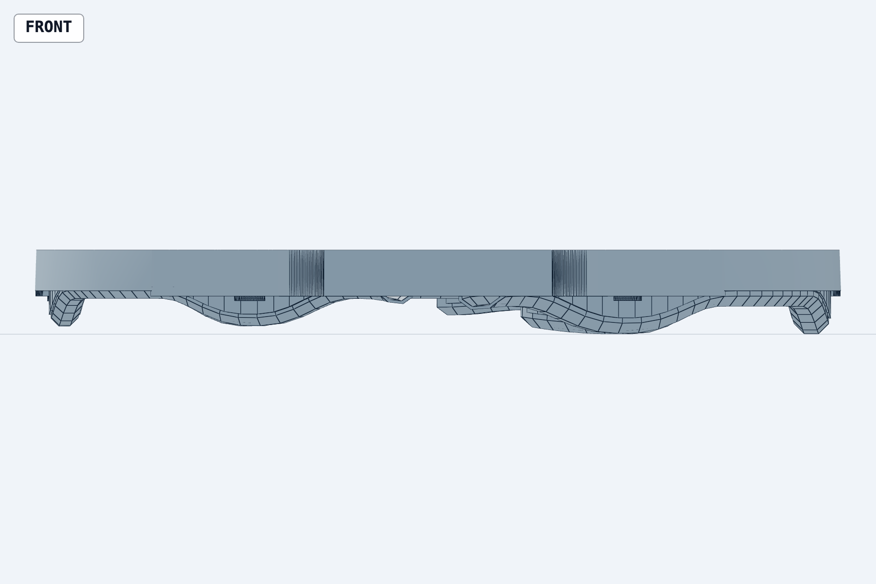
top_baffle_v2/images/generated/obiwan/no_floor/core_front_20260718T100000Z.png
