antorsae/lx/top_baffle_v2/images/generated/obiwan/no_floor/lm_keyed_left_relief_socket_closeup_20260719T144251Z.png

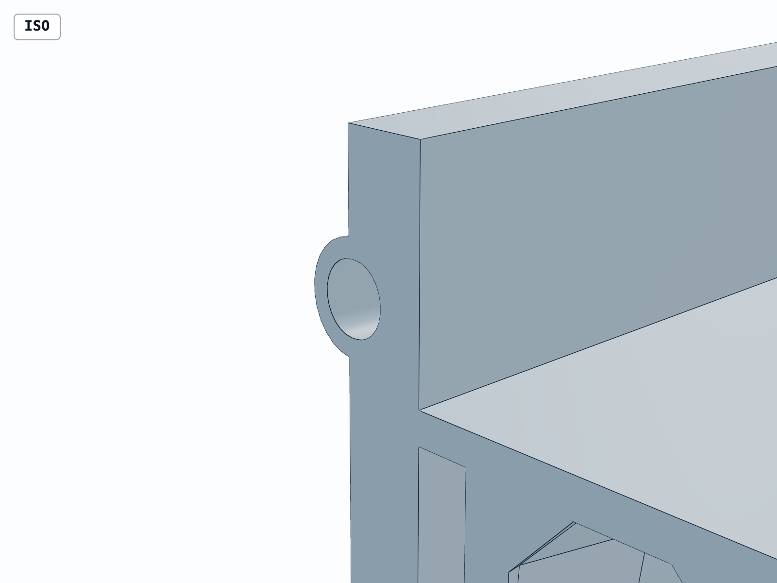
top_baffle_v2/images/generated/obiwan/no_floor/lm_keyed_left_relief_socket_closeup_20260719T144251Z.png
