antorsae/lx/top_baffle_v2/images/generated/slim/base_front_20260718T095922Z.png

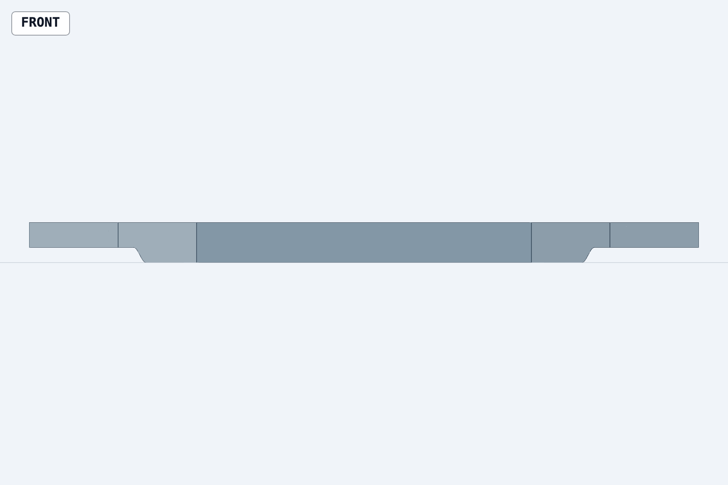
top_baffle_v2/images/generated/slim/base_front_20260718T095922Z.png
