antorsae/lx/top_baffle_v2/images/generated/slim/base_top_20260718T095919Z.png

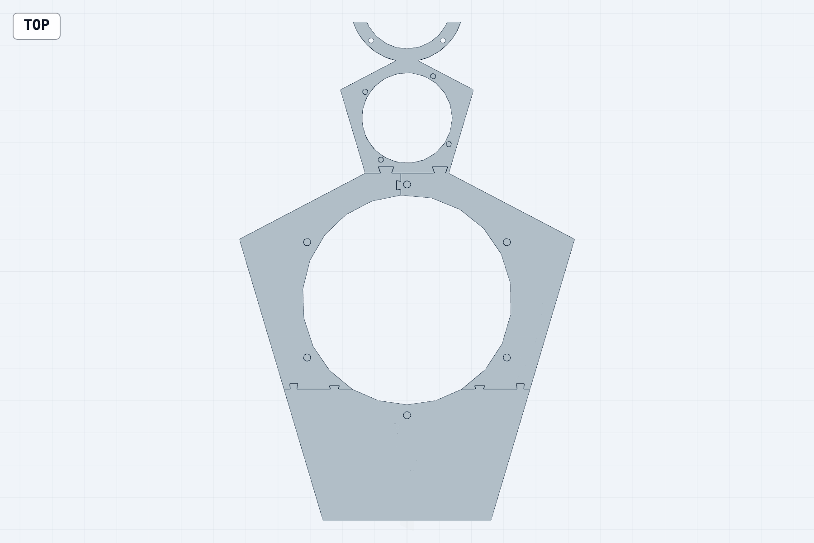
top_baffle_v2/images/generated/slim/base_top_20260718T095919Z.png
