antorsae/lx/top_baffle_v2/images/generated/stock/base_iso_20260718T095853Z.png

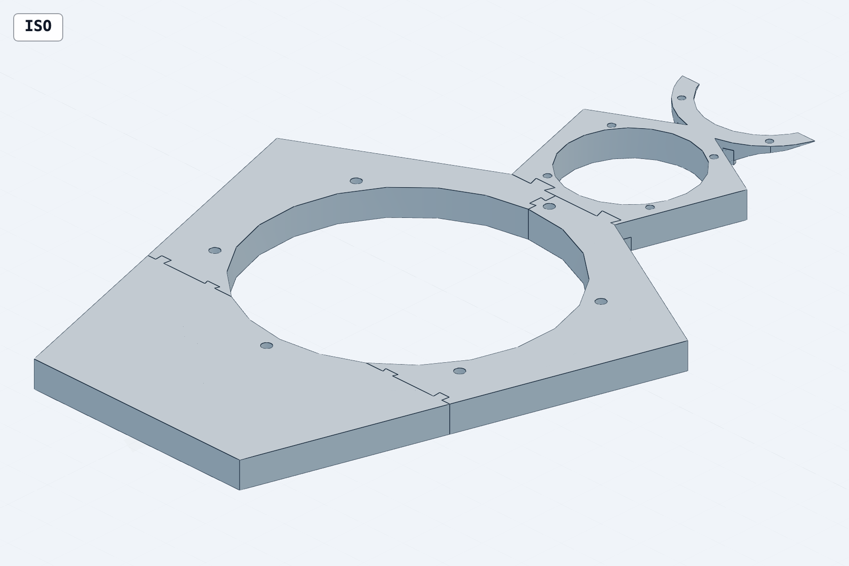
top_baffle_v2/images/generated/stock/base_iso_20260718T095853Z.png
