antorsae/lx/top_baffle_v2/images/generated/stock/base_iso_opposite_20260718T095901Z.png

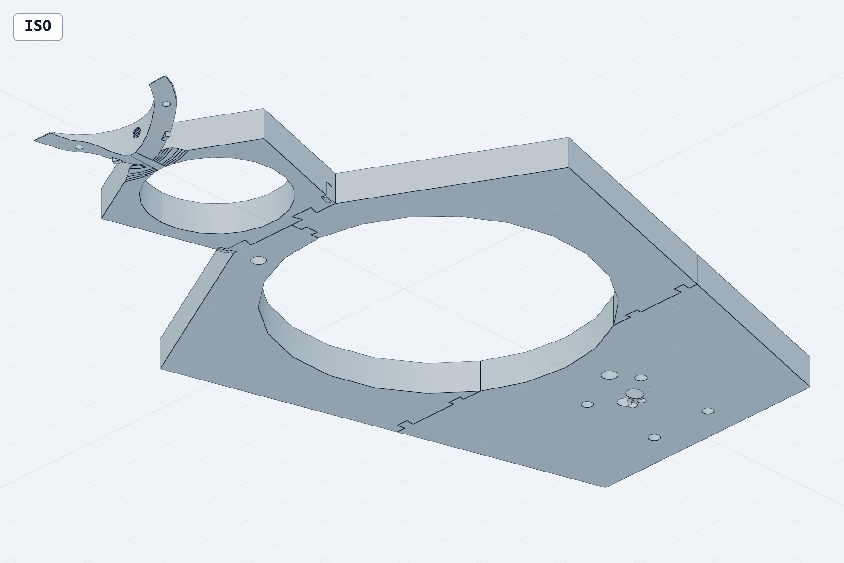
top_baffle_v2/images/generated/stock/base_iso_opposite_20260718T095901Z.png
