antorsae/lx/top_baffle_v2/review/part_views/concept/lm_block_magnet_coupon.png

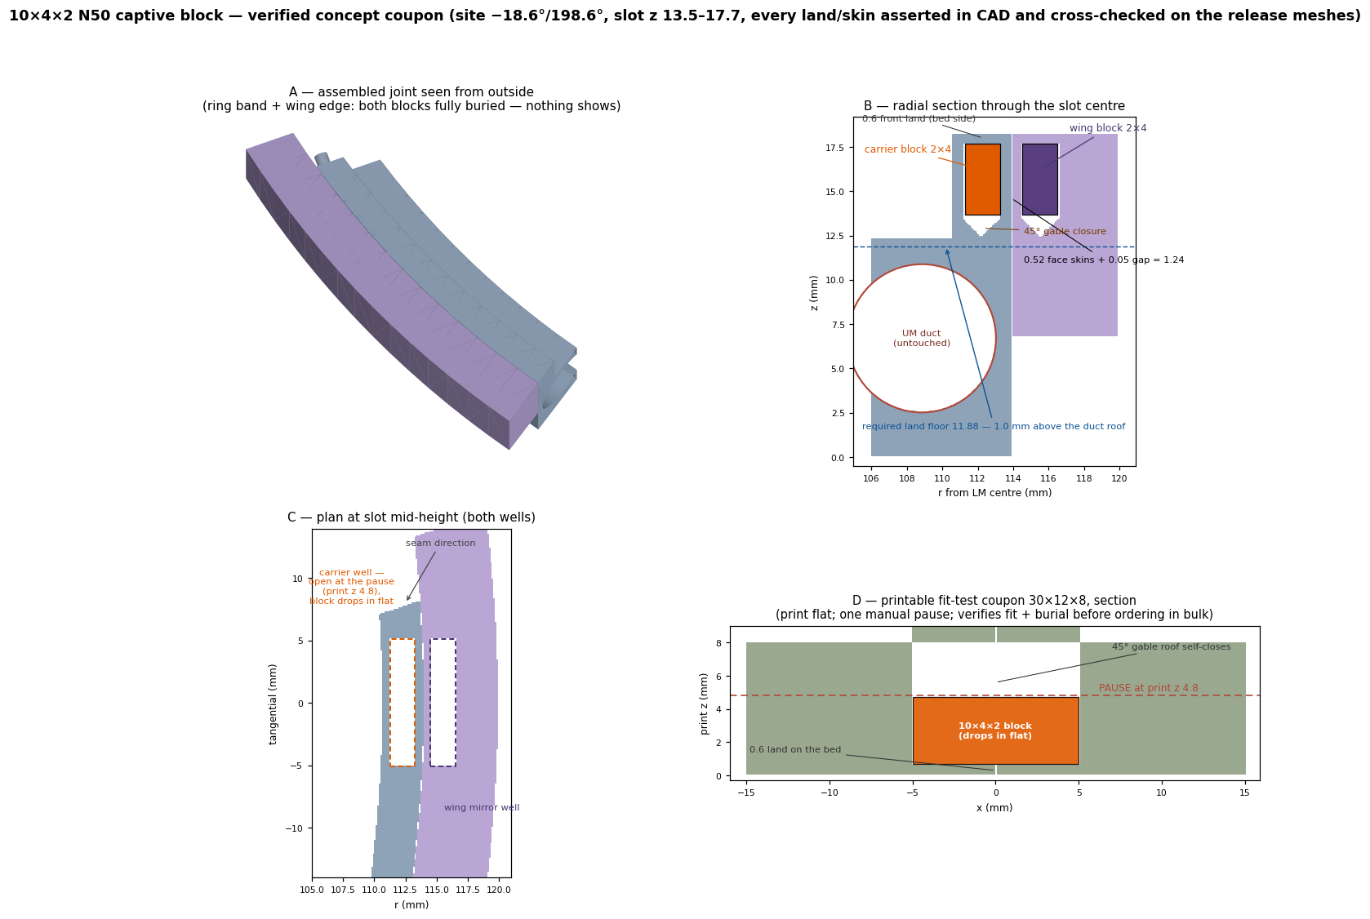
top_baffle_v2/review/part_views/concept/lm_block_magnet_coupon.png
