antorsae/lx/top_baffle_v2/review/part_views/concept/lm_seam_magnet_concept.png

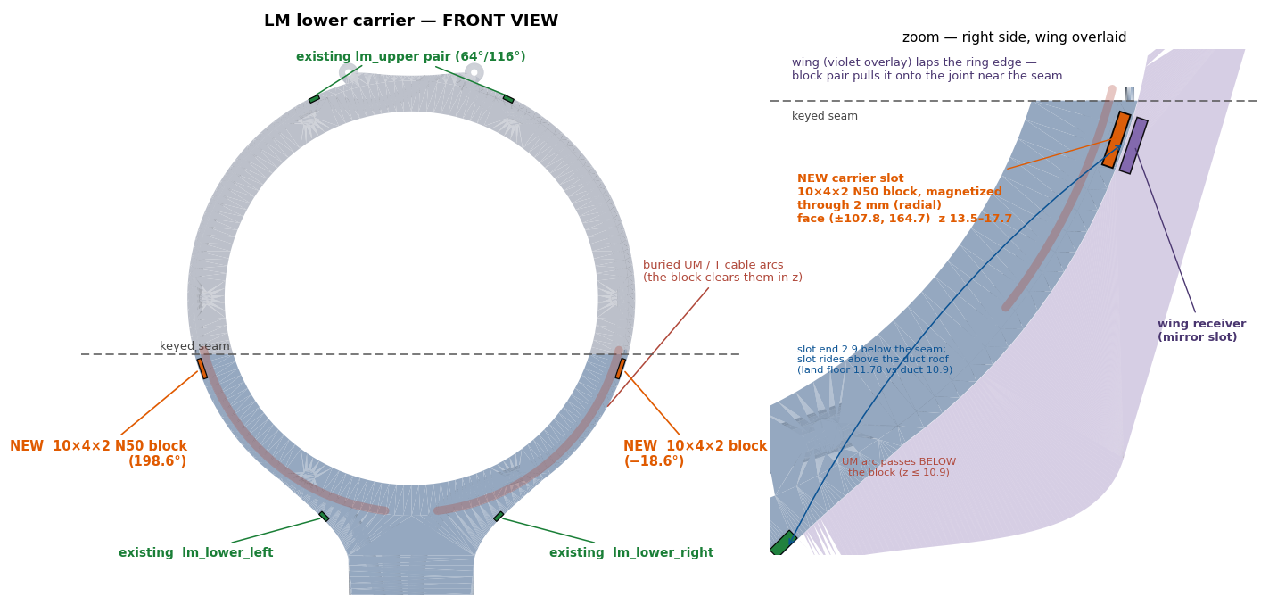
top_baffle_v2/review/part_views/concept/lm_seam_magnet_concept.png
