antorsae/lx/top_baffle_v2/review/part_views/concept/ptt13_dipole_crescent_views.png

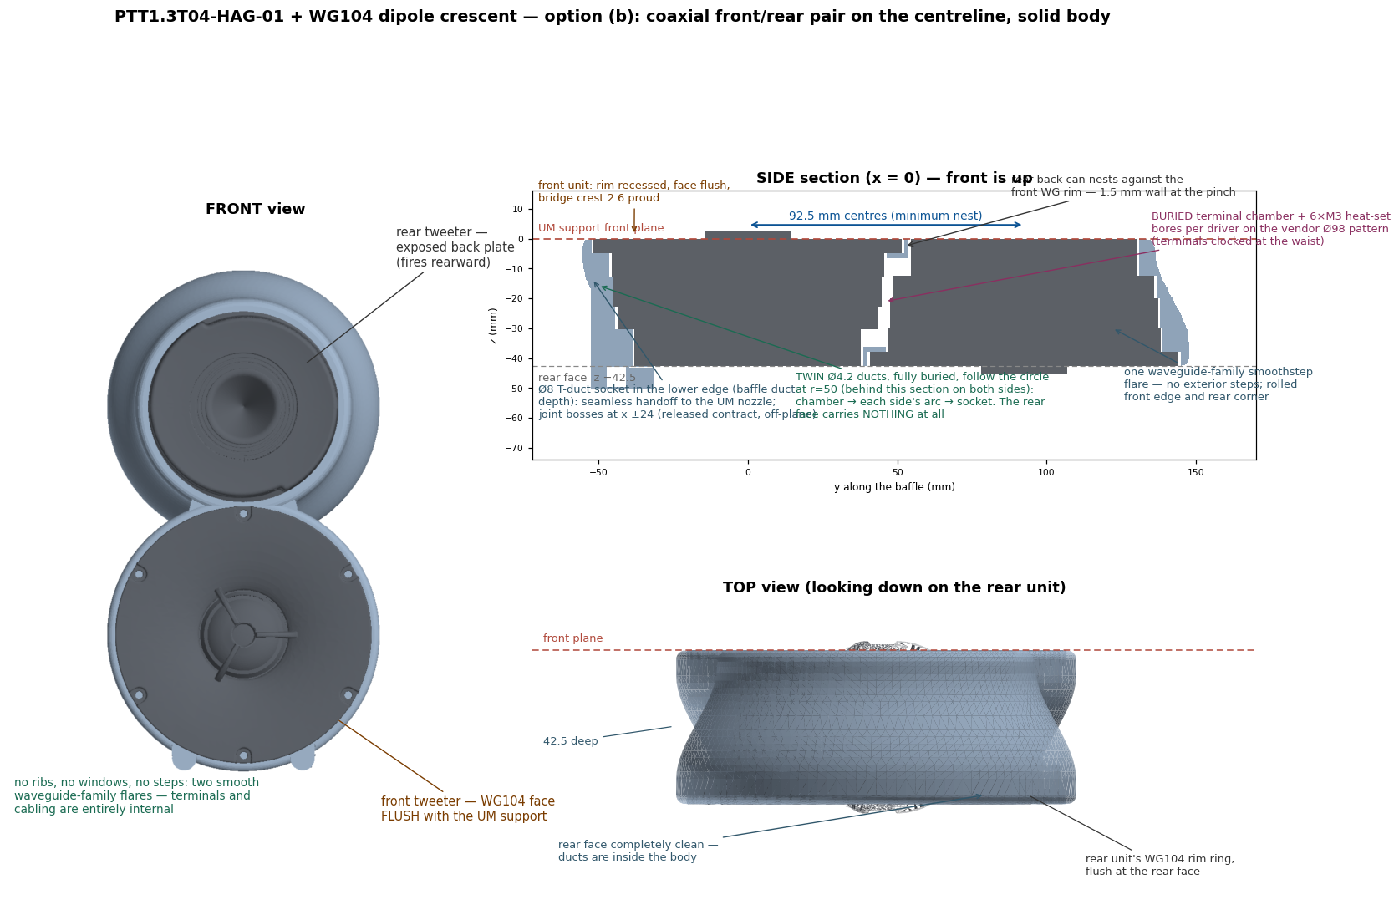
top_baffle_v2/review/part_views/concept/ptt13_dipole_crescent_views.png
