antorsae/lx/top_baffle_v2/review/part_views/concept/ptt13_insert_bores_proof.png

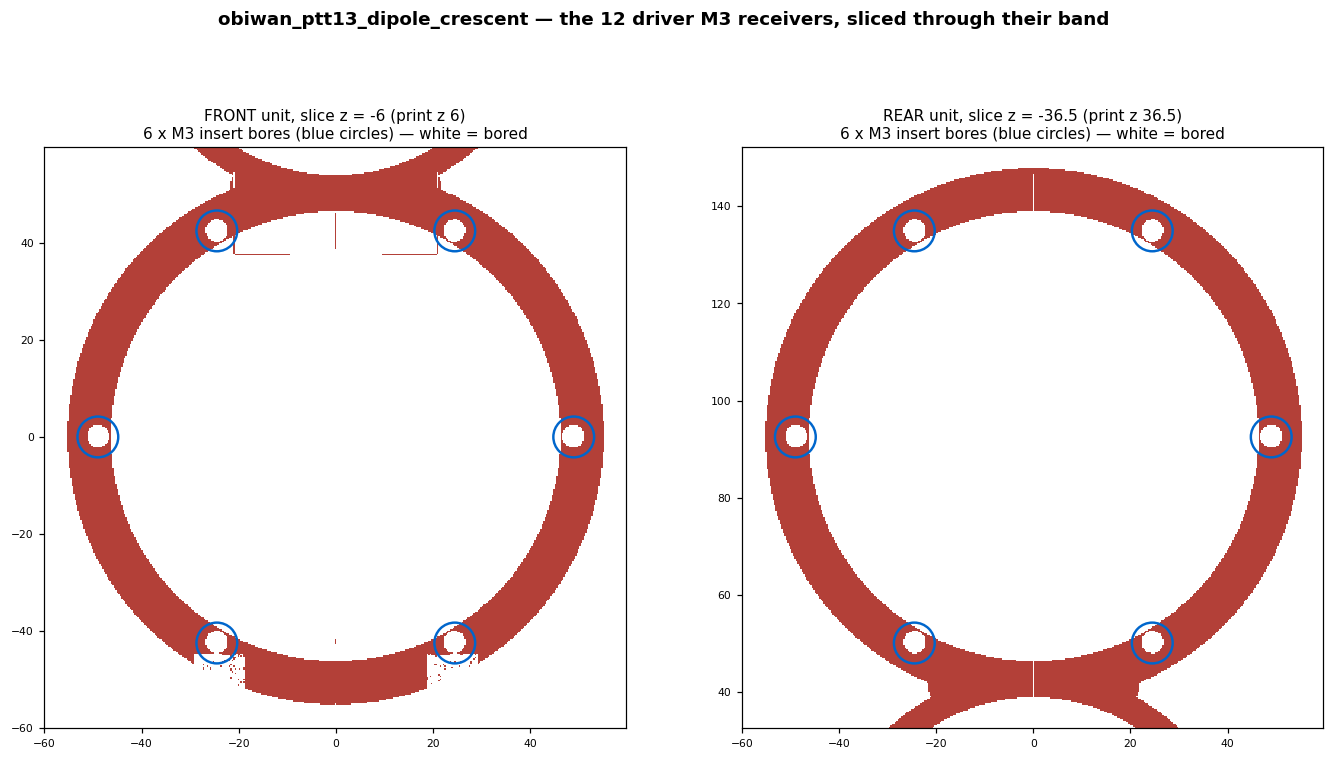
top_baffle_v2/review/part_views/concept/ptt13_insert_bores_proof.png
