antorsae/lx/top_baffle_v2/review/part_views/concept/ptt13_underside_bores.png

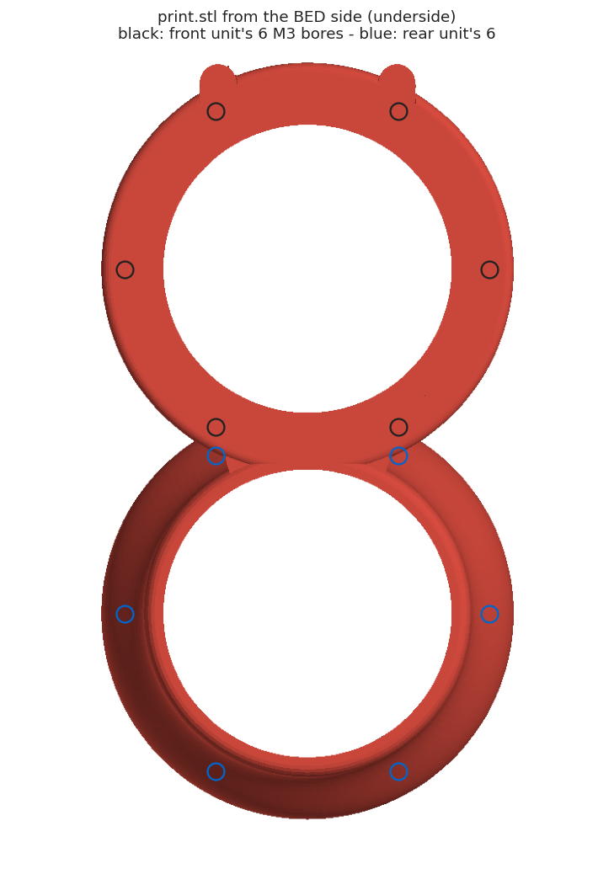
top_baffle_v2/review/part_views/concept/ptt13_underside_bores.png
