antorsae/lx/baffle_modeling/l22mg-juan-top-lowfreq-source-support-sweep/source_support_hotspot_sweep.csv

candidate | angle_group | source_model | source_point_profile | acoustic_center_offset_mm | half_depth_mm | ring_radii_mm | front_depth_mm | rear_depth_mm | front_ring_radii_mm | rear_ring_radii_mm | source_count | source_svd_rcond | source_regularization | source_fit_rms_db_300_1200 | source_fit_front_rms_db_300_1200 | source_fit_rear_rms_db_300_1200 | mesh_panels | mesh_area_m2 | freqs_hz | angle_min_deg | angle_max_deg | target_norm_mean_db | sim_norm_mean_db | signed_mean_error_db | rms_error_db | max_abs_error_db | max_abs_error_freq_hz | max_abs_error_angle_deg
current_d45_r0-35-70-95_svd1e-5_ac-20mm | 0_60 | split-discrete | symmetric_depth_rings | -20.0 | 45.0 | 0 35 70 95 | 45.0 | 45.0 | 0 35 70 95 | 0 35 70 95 | 14 | 1e-05 | 1e-06 | 2.436070246468478 | 2.677798950153336 | 2.1675491399310127 | 832 | 0.18508636079717677 | 300.293 304.321 | 0.0 | 60.0 | -2.69651179161757 | 0.08949372192717178 | 2.7860055135447417 | 3.7319890545115446 | 6.922557560186739 | 304.321 | 60.0
current_d45_r0-35-70-95_svd1e-5_ac-20mm | 70_90 | split-discrete | symmetric_depth_rings | -20.0 | 45.0 | 0 35 70 95 | 45.0 | 45.0 | 0 35 70 95 | 0 35 70 95 | 14 | 1e-05 | 1e-06 | 2.436070246468478 | 2.677798950153336 | 2.1675491399310127 | 832 | 0.18508636079717677 | 300.293 304.321 | 70.0 | 90.0 | -23.58416110268448 | -7.797863174131626 | 15.786297928552855 | 18.166754244054186 | 24.923053396178197 | 300.293 | 75.0
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
