antorsae/lx/top_baffle_v2/review/captive_magnet_slice_audit/captive_magnet_pause_manifest.csv

artifact_id | state | variant | part | print_orientation | group | sites | magnet_count | last_completely_open_layer_z_mm | cavity_bury_roof_start_plane_z_mm | first_closing_layer_z_mm | pause_marker_z_mm | minimum_seated_below_last_open_layer_mm | minimum_seated_below_first_closing_layer_mm | print_insertion_direction_xyz | insertion_instruction | stl | stl_sha256 | gcode | gcode_sha256 | audited_bambu_3mf | audited_bambu_3mf_sha256 | ready_project | ready_project_output_fingerprint | discovery_gcode | discovery_gcode_sha256 | discovery_bambu_3mf | discovery_bambu_3mf_sha256 | bambu_arrange_rz_degrees | polarity
floor_stand:A:stock_shoulder_1_of_4_top_left | floor_stand | A | stock_shoulder_1_of_4_top_left | front_face_down | 1 | stock_upper_left_receiver | 1 | 5.8 | 5.80 | 5.96 | 5.96 | 0.09999990000004377 | 0.2599999000000439 | [0.0,0.0,-1.0] | insert vertically downward from above the paused part (+Z side) through the open loading chimney along print -Z | /Users/antor/gh/lx/top_baffle_v2/build/floor_stand/stl/stock_shoulder_1_of_4_top_left.stl | c226846fba25d831631e1ae83f2d20bd4229407e62ae8a196c1116f13d903091 | /Users/antor/gh/lx/top_baffle_v2/review/captive_magnet_slice_audit/slices/floor_stand_A_stock_shoulder_1_of_4_top_left/ready/plate_1.gcode | 11680bde026834627075778de1df6691a39f6e9ccd39b240afbd620fa075df7c | /Users/antor/gh/lx/top_baffle_v2/review/captive_magnet_slice_audit/slices/floor_stand_A_stock_shoulder_1_of_4_top_left/ready/ready_to_print.gcode.3mf | d7a407cab135a1818f646ed8aad7fdb91802d473e617ab727cda2249fd93764f | True | 5289096de7a3c82120b0334734a5e60c2c8ebe23bd7ae2cb83d3dc579ce9ae3b | /Users/antor/gh/lx/top_baffle_v2/review/captive_magnet_slice_audit/slices/floor_stand_A_stock_shoulder_1_of_4_top_left/plate_1.gcode | fdf236d228405f8d1b6552924e9457ca39e982d1a3b6c28dc0fc9f0caf9403e8 | /Users/antor/gh/lx/top_baffle_v2/review/captive_magnet_slice_audit/slices/floor_stand_A_stock_shoulder_1_of_4_top_left/audited_slice_project.3mf | ecc75c35478f3346cc9f83d36fff9774c64127ac6f187ef546afc32ef7c0f548 | 0.0 | [{"site":"stock_upper_left_receiver","print_marked_pole_axis_xyz":[-0.35021039696371,0.9366710617172503,0.0],"installed_marked_pole_axis_xyz":[-0.35021039696371,-0.9366710617172503,0.0],"instruction":"marked/N pole points along the same installed pair-axis vector as the carrier magnet; the face toward the carrier is therefore the opposite pole"}]
floor_stand:A:stock_shoulder_2_of_4_top_right | floor_stand | A | stock_shoulder_2_of_4_top_right | front_face_down | 1 | stock_upper_right_receiver | 1 | 5.8 | 5.80 | 5.96 | 5.96 | 0.09999990000004377 | 0.2599999000000439 | [0.0,0.0,-1.0] | insert vertically downward from above the paused part (+Z side) through the open loading chimney along print -Z | /Users/antor/gh/lx/top_baffle_v2/build/floor_stand/stl/stock_shoulder_2_of_4_top_right.stl | 97d976c11078ed0a4e6e6f4f3862bbcd9042994b48a21ef5ee254f8f71fd838f | /Users/antor/gh/lx/top_baffle_v2/review/captive_magnet_slice_audit/slices/floor_stand_A_stock_shoulder_2_of_4_top_right/ready/plate_1.gcode | 48af6533b2ece1b8fd41c55c3c6b9dd7ecc8ce491474b01adceba90a8eb378f8 | /Users/antor/gh/lx/top_baffle_v2/review/captive_magnet_slice_audit/slices/floor_stand_A_stock_shoulder_2_of_4_top_right/ready/ready_to_print.gcode.3mf | 8a3f4d40edbc7517611f82ebd848b28ca39a6605e7718b3dac8e862395ab663d | True | b17a58691a16a9ba87cdb649e33e9f4ddef53b18c65e5ee3a61bb3ecfe2bac1d | /Users/antor/gh/lx/top_baffle_v2/review/captive_magnet_slice_audit/slices/floor_stand_A_stock_shoulder_2_of_4_top_right/plate_1.gcode | 57f121d23c70590c077b9a2cb28c6c11b07c1fa8117812dbbde82369569d4a13 | /Users/antor/gh/lx/top_baffle_v2/review/captive_magnet_slice_audit/slices/floor_stand_A_stock_shoulder_2_of_4_top_right/audited_slice_project.3mf | dadd7d62a7e1e84902f1b8d13a2f4bb40b9dca5a03ef8fc9851acf8201feff9d | 0.0 | [{"site":"stock_upper_right_receiver","print_marked_pole_axis_xyz":[0.35021039696371,0.9366710617172503,0.0],"installed_marked_pole_axis_xyz":[0.35021039696371,-0.9366710617172503,0.0],"instruction":"marked/N pole points along the same installed pair-axis vector as the carrier magnet; the face toward the carrier is therefore the opposite pole"}]
floor_stand:A:stock_shoulder_3_of_4_bottom_left | floor_stand | A | stock_shoulder_3_of_4_bottom_left | front_face_down | 1 | stock_lower_left_receiver | 1 | 5.8 | 5.80 | 5.96 | 5.96 | 0.10000000000003428 | 0.2600000000000344 | [0.0,0.0,-1.0] | insert vertically downward from above the paused part (+Z side) through the open loading chimney along print -Z | /Users/antor/gh/lx/top_baffle_v2/build/floor_stand/stl/stock_shoulder_3_of_4_bottom_left.stl | 498086f24109d792c45212144855bd570c06af4b5128fdca371a8cdb00960cf3 | /Users/antor/gh/lx/top_baffle_v2/review/captive_magnet_slice_audit/slices/floor_stand_A_stock_shoulder_3_of_4_bottom_left/ready/plate_1.gcode | 3b636d2fb762e508c71bc0c053d39d5117bba4bb5cf65b8fc3af6f1a76df46f1 | /Users/antor/gh/lx/top_baffle_v2/review/captive_magnet_slice_audit/slices/floor_stand_A_stock_shoulder_3_of_4_bottom_left/ready/ready_to_print.gcode.3mf | 37e68912f18059f8a82b819806a3595e8597cca4a546b99dc19f806afde219cf | True | f28d011e41dd3168905969580824d5120278b99e424f73991e88938ff5b40d3a | /Users/antor/gh/lx/top_baffle_v2/review/captive_magnet_slice_audit/slices/floor_stand_A_stock_shoulder_3_of_4_bottom_left/plate_1.gcode | 0c83750224456f9d4228ad436e5ad0d516c2e0b9217aef8aa5bed7d7ea064439 | /Users/antor/gh/lx/top_baffle_v2/review/captive_magnet_slice_audit/slices/floor_stand_A_stock_shoulder_3_of_4_bottom_left/audited_slice_project.3mf | c24e897df3413aa85ce6ee1bed64813eb3832227e562a9b2a99004897a2bc5d5 | 0.0 | [{"site":"stock_lower_left_receiver","print_marked_pole_axis_xyz":[-0.9584785342953424,0.2851646880226448,0.0],"installed_marked_pole_axis_xyz":[-0.9584785342953424,-0.2851646880226448,0.0],"instruction":"marked/N pole points along the same installed pair-axis vector as the carrier magnet; the face toward the carrier is therefore the opposite pole"}]
floor_stand:A:stock_shoulder_4_of_4_bottom_right | floor_stand | A | stock_shoulder_4_of_4_bottom_right | front_face_down | 1 | stock_lower_right_receiver | 1 | 5.8 | 5.80 | 5.96 | 5.96 | 0.10000000000003428 | 0.2600000000000344 | [0.0,0.0,-1.0] | insert vertically downward from above the paused part (+Z side) through the open loading chimney along print -Z | /Users/antor/gh/lx/top_baffle_v2/build/floor_stand/stl/stock_shoulder_4_of_4_bottom_right.stl | 43fa254e1c788a6b9ec2170bf892955be8ec8321bc9aea0408f494038ea10792 | /Users/antor/gh/lx/top_baffle_v2/review/captive_magnet_slice_audit/slices/floor_stand_A_stock_shoulder_4_of_4_bottom_right/ready/plate_1.gcode | d6334076c57a43f5e6f58e8a61908affc5eafe03e5a6b325902133a75ba2ff14 | /Users/antor/gh/lx/top_baffle_v2/review/captive_magnet_slice_audit/slices/floor_stand_A_stock_shoulder_4_of_4_bottom_right/ready/ready_to_print.gcode.3mf | d790aedb02e21d629ae2f03a4a721a3a4ba66762d23374998248cb6ebd903e0f | True | 67c5a4588e921911ce734407f8df30ecd1acfbff0e093de06535f1f33df3d322 | /Users/antor/gh/lx/top_baffle_v2/review/captive_magnet_slice_audit/slices/floor_stand_A_stock_shoulder_4_of_4_bottom_right/plate_1.gcode | 25016fd7e9f6eee4cb9e91b7c3735d0f3266d16bce17b16bf1840fc6ed205c39 | /Users/antor/gh/lx/top_baffle_v2/review/captive_magnet_slice_audit/slices/floor_stand_A_stock_shoulder_4_of_4_bottom_right/audited_slice_project.3mf | 3d09fb3b29e7576f5b252f320abb4d53f857f414879f5c6df72613519cac5ad2 | 0.0 | [{"site":"stock_lower_right_receiver","print_marked_pole_axis_xyz":[0.9584785342953424,0.2851646880226448,0.0],"installed_marked_pole_axis_xyz":[0.9584785342953424,-0.2851646880226448,0.0],"instruction":"marked/N pole points along the same installed pair-axis vector as the carrier magnet; the face toward the carrier is therefore the opposite pole"}]
floor_stand:B1:stock_wing_1_of_2_left | floor_stand | B1 | stock_wing_1_of_2_left | front_face_down | 1 | stock_lower_left_receiver; stock_upper_left_receiver | 2 | 5.8 | 5.80 | 5.96 | 5.96 | 0.09999990000004733 | 0.25999990000004747 | [0.0,0.0,-1.0] | insert vertically downward from above the paused part (+Z side) through the open loading chimney along print -Z | /Users/antor/gh/lx/top_baffle_v2/build/floor_stand/stl/stock_wing_1_of_2_left.stl | 7749a25921f930432d155f8988afe0dd8516f2b119560c11890f4f2a309794f1 | /Users/antor/gh/lx/top_baffle_v2/review/captive_magnet_slice_audit/slices/floor_stand_B1_stock_wing_1_of_2_left/ready/plate_1.gcode | 23f31e18fb84701437db74aafdfac289557b692e85e89933c29b05b877b5f2ca | /Users/antor/gh/lx/top_baffle_v2/review/captive_magnet_slice_audit/slices/floor_stand_B1_stock_wing_1_of_2_left/ready/ready_to_print.gcode.3mf | 6ab50be44cb104f09c5e8415741c2a7c1e6dec6e7fdaaebcdedc4af9d1672157 | True | f250f25feb57b81df819ee8af5bedc7f5f92dd019f12ee5b4b99f44537346b2e | /Users/antor/gh/lx/top_baffle_v2/review/captive_magnet_slice_audit/slices/floor_stand_B1_stock_wing_1_of_2_left/plate_1.gcode | 552244fecbb3701a933bba542debf233b7830d090518fcba4ccb724406e83061 | /Users/antor/gh/lx/top_baffle_v2/review/captive_magnet_slice_audit/slices/floor_stand_B1_stock_wing_1_of_2_left/audited_slice_project.3mf | bfb475a52f841d778064aa645b02133954948465dc2d17e15241ec247e6a7bfd | 0.0 | [{"site":"stock_lower_left_receiver","print_marked_pole_axis_xyz":[-0.9584785342953424,0.2851646880226448,0.0],"installed_marked_pole_axis_xyz":[-0.9584785342953424,-0.2851646880226448,0.0],"instruction":"marked/N pole points along the same installed pair-axis vector as the carrier magnet; the face toward the carrier is therefore the opposite pole"},{"site":"stock_upper_left_receiver","print_marked_pole_axis_xyz":[-0.35021039696371,0.9366710617172503,0.0],"installed_marked_pole_axis_xyz":[-0.35021039696371,-0.9366710617172503,0.0],"instruction":"marked/N pole points along the same installed pair-axis vector as the carrier magnet; the face toward the carrier is therefore the opposite pole"}]
floor_stand:B1:stock_wing_2_of_2_right | floor_stand | B1 | stock_wing_2_of_2_right | front_face_down | 1 | stock_lower_right_receiver; stock_upper_right_receiver | 2 | 5.8 | 5.80 | 5.96 | 5.96 | 0.09999990000004377 | 0.2599999000000439 | [0.0,0.0,-1.0] | insert vertically downward from above the paused part (+Z side) through the open loading chimney along print -Z | /Users/antor/gh/lx/top_baffle_v2/build/floor_stand/stl/stock_wing_2_of_2_right.stl | 8da84750e2cff0075955bd8245831ebfc0ddfc97d9bc36e97789069cadf5d67b | /Users/antor/gh/lx/top_baffle_v2/review/captive_magnet_slice_audit/slices/floor_stand_B1_stock_wing_2_of_2_right/ready/plate_1.gcode | 4b76571b6f5b22031e16d6dc48e7aadf4e487447e2f1842308d207289c511c73 | /Users/antor/gh/lx/top_baffle_v2/review/captive_magnet_slice_audit/slices/floor_stand_B1_stock_wing_2_of_2_right/ready/ready_to_print.gcode.3mf | 93385625ea772775968b8bf5569f8b3cfb6f74801779c6a5e512e0ab70f01a1c | True | c9905b92e3136a654a83bd173faee766f1e7b5452f2c1e906ddd1096a072cc8d | /Users/antor/gh/lx/top_baffle_v2/review/captive_magnet_slice_audit/slices/floor_stand_B1_stock_wing_2_of_2_right/plate_1.gcode | 3f3cb71d05d96d5e971e241a97a66ceabb5fc9da4982aa4e8e57258c93a596da | /Users/antor/gh/lx/top_baffle_v2/review/captive_magnet_slice_audit/slices/floor_stand_B1_stock_wing_2_of_2_right/audited_slice_project.3mf | 07889c3294dbcc8611713743deb60e068a4703782eccee1fe0fe368d27cf3804 | 0.0 | [{"site":"stock_lower_right_receiver","print_marked_pole_axis_xyz":[0.9584785342953424,0.2851646880226448,0.0],"installed_marked_pole_axis_xyz":[0.9584785342953424,-0.2851646880226448,0.0],"instruction":"marked/N pole points along the same installed pair-axis vector as the carrier magnet; the face toward the carrier is therefore the opposite pole"},{"site":"stock_upper_right_receiver","print_marked_pole_axis_xyz":[0.35021039696371,0.9366710617172503,0.0],"installed_marked_pole_axis_xyz":[0.35021039696371,-0.9366710617172503,0.0],"instruction":"marked/N pole points along the same installed pair-axis vector as the carrier magnet; the face toward the carrier is therefore the opposite pole"}]
floor_stand:B2:stock_4_of_4_vase_b2 | floor_stand | B2 | stock_4_of_4_vase_b2 | front_face_down | 1 | stock_lower_right_base; stock_lower_left_base; stock_upper_right_base; stock_upper_left_base | 4 | 5.8 | 5.80 | 5.96 | 5.96 | 0.09999990000003667 | 0.2599999000000368 | [0.0,0.0,-1.0] | insert vertically downward from above the paused part (+Z side) through the open loading chimney along print -Z | /Users/antor/gh/lx/top_baffle_v2/build/floor_stand/stl/stock_4_of_4_vase_b2.stl | 6c7b57df55b27ffa725e07d2d034f816f8350c86876d29a788fbc33ef0dfb25a | /Users/antor/gh/lx/top_baffle_v2/review/captive_magnet_slice_audit/slices/floor_stand_B2_stock_4_of_4_vase_b2/ready/plate_1.gcode | 1c541bf20edc30264d2435958735bdd0b84ddad45b4b8caec668f1c013c3fd5c | /Users/antor/gh/lx/top_baffle_v2/review/captive_magnet_slice_audit/slices/floor_stand_B2_stock_4_of_4_vase_b2/ready/ready_to_print.gcode.3mf | 7248dee7943947731407c16af0af4e4da0f794f99e720d03e9d57ace13e3f2ea | True | 083b904bad21d1a4d2bc94ba189598888276d26db1133596f77acc6176d58a12 | /Users/antor/gh/lx/top_baffle_v2/review/captive_magnet_slice_audit/slices/floor_stand_B2_stock_4_of_4_vase_b2/plate_1.gcode | e2ad61042f2a4c187f2f7c5029d37039baac5d71352271b78a9f049a0095242d | /Users/antor/gh/lx/top_baffle_v2/review/captive_magnet_slice_audit/slices/floor_stand_B2_stock_4_of_4_vase_b2/audited_slice_project.3mf | 9a48e51ddfee47f1895552de903c46f8f80f37cee1248f5a0b16d3ff3c04f4ae | 0.0 | [{"site":"stock_lower_right_base","print_marked_pole_axis_xyz":[0.9584785342953424,0.2851646880226448,0.0],"installed_marked_pole_axis_xyz":[0.9584785342953424,-0.2851646880226448,0.0],"instruction":"marked/N pole points OUT from carrier toward its mating piece, along installed_marked_pole_axis_xyz"},{"site":"stock_lower_left_base","print_marked_pole_axis_xyz":[-0.9584785342953424,0.2851646880226448,0.0],"installed_marked_pole_axis_xyz":[-0.9584785342953424,-0.2851646880226448,0.0],"instruction":"marked/N pole points OUT from carrier toward its mating piece, along installed_marked_pole_axis_xyz"},{"site":"stock_upper_right_base","print_marked_pole_axis_xyz":[0.35021039696371,0.9366710617172503,0.0],"installed_marked_pole_axis_xyz":[0.35021039696371,-0.9366710617172503,0.0],"instruction":"marked/N pole points OUT from carrier toward its mating piece, along installed_marked_pole_axis_xyz"},{"site":"stock_upper_left_base","print_marked_pole_axis_xyz":[-0.35021039696371,0.9366710617172503,0.0],"installed_marked_pole_axis_xyz":[-0.35021039696371,-0.9366710617172503,0.0],"instruction":"marked/N pole points OUT from carrier toward its mating piece, along installed_marked_pole_axis_xyz"}]
floor_stand:Obi-Wan-split:obiwan_optional_lm_keyed_1_of_2_bottom | floor_stand | Obi-Wan-split | obiwan_optional_lm_keyed_1_of_2_bottom | front_face_down | 1 | lm_lower_left; lm_lower_right | 2 | 5.8 | 5.80 | 5.96 | 5.96 | 0.0999999000000047 | 0.25999990000000484 | [0.0,0.0,-1.0] | insert vertically downward from above the paused part (+Z side) through the open loading chimney along print -Z | /Users/antor/gh/lx/top_baffle_v2/build/floor_stand/stl/obiwan_optional_lm_keyed_1_of_2_bottom.stl | df222c6fbf8a2b7ddaee8c7ca5e467389eafd219b15c17d546d7a956cc03dd49 | /Users/antor/gh/lx/top_baffle_v2/review/captive_magnet_slice_audit/slices/floor_stand_Obi-Wan-split_obiwan_optional_lm_keyed_1_of_2_bottom/ready/plate_1.gcode | 548048d611cb19079eb3fc4d9e9b7ce284a26f8631ce2f177580605d173d9e21 | /Users/antor/gh/lx/top_baffle_v2/review/captive_magnet_slice_audit/slices/floor_stand_Obi-Wan-split_obiwan_optional_lm_keyed_1_of_2_bottom/ready/ready_to_print.gcode.3mf | e8fb4effeb65be01f6fff35039a2a0dadac4203da95697a8f6109c659132a3bd | True | 06feb3900e58bfe35305e49297987cc477932acd97224b8873ce95064650daf5 | /Users/antor/gh/lx/top_baffle_v2/review/captive_magnet_slice_audit/slices/floor_stand_Obi-Wan-split_obiwan_optional_lm_keyed_1_of_2_bottom/plate_1.gcode | 3013f189711f5bd92172d3ca63c7d7df617b73e126b170cfbf1e9f561e9f4483 | /Users/antor/gh/lx/top_baffle_v2/review/captive_magnet_slice_audit/slices/floor_stand_Obi-Wan-split_obiwan_optional_lm_keyed_1_of_2_bottom/audited_slice_project.3mf | 0b932e5443d5ad12a58ad835ae3dbece6585366fff52cff81afe6759e46537b4 | 0.0 | [{"site":"lm_lower_left","print_marked_pole_axis_xyz":[-0.9452165115184645,0.3264440937631809,0.0],"installed_marked_pole_axis_xyz":[-0.7064513012709772,-0.7077616540421945,0.0],"instruction":"marked/N pole points OUT from carrier toward its mating piece, along installed_marked_pole_axis_xyz"},{"site":"lm_lower_right","print_marked_pole_axis_xyz":[0.32469193564684246,0.9458198279407695,0.0],"installed_marked_pole_axis_xyz":[0.7064513012709772,-0.7077616540421945,0.0],"instruction":"marked/N pole points OUT from carrier toward its mating piece, along installed_marked_pole_axis_xyz"}]
floor_stand:Obi-Wan-split:obiwan_optional_lm_keyed_2_of_2_top | floor_stand | Obi-Wan-split | obiwan_optional_lm_keyed_2_of_2_top | front_face_down | 1 | lm_upper_left; lm_upper_right | 2 | 5.8 | 5.80 | 5.96 | 5.96 | 0.09999990000001535 | 0.2599999000000155 | [0.0,0.0,-1.0] | insert vertically downward from above the paused part (+Z side) through the open loading chimney along print -Z | /Users/antor/gh/lx/top_baffle_v2/build/floor_stand/stl/obiwan_optional_lm_keyed_2_of_2_top.stl | 7798396fdbc5f837dc4b79fdc2792f781bcbd6af474e6b9dbb7edb9d78768ee4 | /Users/antor/gh/lx/top_baffle_v2/review/captive_magnet_slice_audit/slices/floor_stand_Obi-Wan-split_obiwan_optional_lm_keyed_2_of_2_top/ready/plate_1.gcode | da5c5b996b8adf340f432a71d30e43166c342f7379498c450ac271c655843ed0 | /Users/antor/gh/lx/top_baffle_v2/review/captive_magnet_slice_audit/slices/floor_stand_Obi-Wan-split_obiwan_optional_lm_keyed_2_of_2_top/ready/ready_to_print.gcode.3mf | 8ba179e469a92cfdc03ce0361dfc1d191206849512d51f3d01ab2cb410f7b13c | True | ac6bd1d6a9b4dd90596e25dd30e15681bb1c0f73ceaa8c3dd20348aac80d6241 | /Users/antor/gh/lx/top_baffle_v2/review/captive_magnet_slice_audit/slices/floor_stand_Obi-Wan-split_obiwan_optional_lm_keyed_2_of_2_top/plate_1.gcode | 2e992f38743538a0c1530d42543bdab29215931b6aa001167e0fc1e4329dbfa1 | /Users/antor/gh/lx/top_baffle_v2/review/captive_magnet_slice_audit/slices/floor_stand_Obi-Wan-split_obiwan_optional_lm_keyed_2_of_2_top/audited_slice_project.3mf | 1249036446f6c1978a5b9e6a550ede46524684374b9fef0c67470a2979c7b4f5 | 0.0 | [{"site":"lm_upper_left","print_marked_pole_axis_xyz":[0.3255681544571566,-0.9455185755993172,0.0],"installed_marked_pole_axis_xyz":[-0.4383711467890776,0.8987940462991671,0.0],"instruction":"marked/N pole points OUT from carrier toward its mating piece, along installed_marked_pole_axis_xyz"},{"site":"lm_upper_right","print_marked_pole_axis_xyz":[0.9455185755993168,-0.32556815445715676,0.0],"installed_marked_pole_axis_xyz":[0.43837114678907746,0.898794046299167,0.0],"instruction":"marked/N pole points OUT from carrier toward its mating piece, along installed_marked_pole_axis_xyz"}]
floor_stand:Obi-Wan:obiwan_core_2_of_2_um_carrier | floor_stand | Obi-Wan | obiwan_core_2_of_2_um_carrier | front_face_down | 1 | um_left; um_right | 2 | 5.8 | 5.80 | 5.96 | 5.96 | 0.09999990000003667 | 0.2599999000000368 | [0.0,0.0,-1.0] | insert vertically downward from above the paused part (+Z side) through the open loading chimney along print -Z | /Users/antor/gh/lx/top_baffle_v2/build/floor_stand/stl/obiwan_core_2_of_2_um_carrier.stl | 098ea541fa8424e193275313a99086f745ba701e71cbfb4b6bc7e1997fdac41d | /Users/antor/gh/lx/top_baffle_v2/review/captive_magnet_slice_audit/slices/floor_stand_Obi-Wan_obiwan_core_2_of_2_um_carrier/ready/plate_1.gcode | 118141a84566bbae0bd33f40297aaed13e6bbb02c6ab58429240e2a8f4ef37ab | /Users/antor/gh/lx/top_baffle_v2/review/captive_magnet_slice_audit/slices/floor_stand_Obi-Wan_obiwan_core_2_of_2_um_carrier/ready/ready_to_print.gcode.3mf | f9f49cfbb1dcc6f7e338e4a3ef51f3739e623bda17165a1b2b13c4d116489270 | True | dd8850a3bae0fe48b6fffad8055fa49881ae3e0b4864568bc15f6d1da11fc0d7 | /Users/antor/gh/lx/top_baffle_v2/review/captive_magnet_slice_audit/slices/floor_stand_Obi-Wan_obiwan_core_2_of_2_um_carrier/plate_1.gcode | ce5194f3baa6915032ed4b9698665e83ddce2fa5705a3db4116ef8e7cabf4d5b | /Users/antor/gh/lx/top_baffle_v2/review/captive_magnet_slice_audit/slices/floor_stand_Obi-Wan_obiwan_core_2_of_2_um_carrier/audited_slice_project.3mf | f8da45dec7611f25253c5eb1ae62227c62ad0a365a9c4981326677e2a17d86e2 | 0.0 | [{"site":"um_left","print_marked_pole_axis_xyz":[-0.6360782202777641,-0.7716245833877199,0.0],"installed_marked_pole_axis_xyz":[-0.6360782202777641,0.7716245833877199,0.0],"instruction":"marked/N pole points OUT from carrier toward its mating piece, along installed_marked_pole_axis_xyz"},{"site":"um_right","print_marked_pole_axis_xyz":[0.636078220277764,-0.77162458338772,0.0],"installed_marked_pole_axis_xyz":[0.636078220277764,0.77162458338772,0.0],"instruction":"marked/N pole points OUT from carrier toward its mating piece, along installed_marked_pole_axis_xyz"}]
floor_stand:V1-A:slim_shoulder_1_of_4_bottom_left | floor_stand | V1-A | slim_shoulder_1_of_4_bottom_left | front_face_down | 1 | v1_lower_left_receiver | 1 | 5.8 | 5.80 | 5.96 | 5.96 | 0.10000000000003428 | 0.2600000000000344 | [0.0,0.0,-1.0] | insert vertically downward from above the paused part (+Z side) through the open loading chimney along print -Z | /Users/antor/gh/lx/top_baffle_v2/build/floor_stand/stl/slim_shoulder_1_of_4_bottom_left.stl | 7ece5a1b6edf2e30a5764feb5abc982f8bb85bffb5269ebc66cbfacff1bcd2af | /Users/antor/gh/lx/top_baffle_v2/review/captive_magnet_slice_audit/slices/floor_stand_V1-A_slim_shoulder_1_of_4_bottom_left/ready/plate_1.gcode | 4c86c10926387d335bc4c7c7e9329a6449aae0b321c955628f954de970a4b2be | /Users/antor/gh/lx/top_baffle_v2/review/captive_magnet_slice_audit/slices/floor_stand_V1-A_slim_shoulder_1_of_4_bottom_left/ready/ready_to_print.gcode.3mf | 94362600e2003678534bde5890fbf8f08727afcd884dbdde2c47430095918bfb | True | 576f5cb1b587d170bfb7b8d243239b6045a247ff4c8ba9ccada1dc2714966a6a | /Users/antor/gh/lx/top_baffle_v2/review/captive_magnet_slice_audit/slices/floor_stand_V1-A_slim_shoulder_1_of_4_bottom_left/plate_1.gcode | 6f8fcc63eeca282d6372c99ef37c71993d7e08c7c21e6eb49362198a3bbf9548 | /Users/antor/gh/lx/top_baffle_v2/review/captive_magnet_slice_audit/slices/floor_stand_V1-A_slim_shoulder_1_of_4_bottom_left/audited_slice_project.3mf | cb5b737ae66ea23b5729a65a21a35c1988216803dafb520d2fee204c33019819 | 0.0 | [{"site":"v1_lower_left_receiver","print_marked_pole_axis_xyz":[-0.9584785342953424,0.2851646880226448,0.0],"installed_marked_pole_axis_xyz":[-0.9584785342953424,-0.2851646880226448,0.0],"instruction":"marked/N pole points along the same installed pair-axis vector as the carrier magnet; the face toward the carrier is therefore the opposite pole"}]
floor_stand:V1-A:slim_shoulder_2_of_4_top_left | floor_stand | V1-A | slim_shoulder_2_of_4_top_left | front_face_down | 1 | v1_upper_left_receiver | 1 | 5.8 | 5.80 | 5.96 | 5.96 | 0.09999990000004377 | 0.2599999000000439 | [0.0,0.0,-1.0] | insert vertically downward from above the paused part (+Z side) through the open loading chimney along print -Z | /Users/antor/gh/lx/top_baffle_v2/build/floor_stand/stl/slim_shoulder_2_of_4_top_left.stl | 6336437600757c539da9e109d44901fdb078da56c6e41d37c03b7c4717e5c6a1 | /Users/antor/gh/lx/top_baffle_v2/review/captive_magnet_slice_audit/slices/floor_stand_V1-A_slim_shoulder_2_of_4_top_left/ready/plate_1.gcode | 6cceafc155ecfd8b341c6cded1d0231d1668a593ea164a135646e2381715352a | /Users/antor/gh/lx/top_baffle_v2/review/captive_magnet_slice_audit/slices/floor_stand_V1-A_slim_shoulder_2_of_4_top_left/ready/ready_to_print.gcode.3mf | ab0e51268d44fa4c924a0ed801de47ea7332da47e09d136642608dd0b4c5a788 | True | 16fda953a4688bfc9c828b9064d980dc65c0f51ede49bb1ec2ae69b2af701384 | /Users/antor/gh/lx/top_baffle_v2/review/captive_magnet_slice_audit/slices/floor_stand_V1-A_slim_shoulder_2_of_4_top_left/plate_1.gcode | 13c27bb0b2aa024bd782e6bff6b892ec849e7eb8e3940ffe2459f6ee65b1e0b1 | /Users/antor/gh/lx/top_baffle_v2/review/captive_magnet_slice_audit/slices/floor_stand_V1-A_slim_shoulder_2_of_4_top_left/audited_slice_project.3mf | ff8288ba1e16528512daf8c575978af58d50c3934824bd9902c8b22d55f60a5e | 0.0 | [{"site":"v1_upper_left_receiver","print_marked_pole_axis_xyz":[-0.35021039696371,0.9366710617172503,0.0],"installed_marked_pole_axis_xyz":[-0.35021039696371,-0.9366710617172503,0.0],"instruction":"marked/N pole points along the same installed pair-axis vector as the carrier magnet; the face toward the carrier is therefore the opposite pole"}]
floor_stand:V1-A:slim_shoulder_3_of_4_bottom_right | floor_stand | V1-A | slim_shoulder_3_of_4_bottom_right | front_face_down | 1 | v1_lower_right_receiver | 1 | 5.8 | 5.80 | 5.96 | 5.96 | 0.10000000000003428 | 0.2600000000000344 | [0.0,0.0,-1.0] | insert vertically downward from above the paused part (+Z side) through the open loading chimney along print -Z | /Users/antor/gh/lx/top_baffle_v2/build/floor_stand/stl/slim_shoulder_3_of_4_bottom_right.stl | 3c520a232faa90973f9b422c8f8f549dc2d4d25cbb67ba466989bdb5f079b398 | /Users/antor/gh/lx/top_baffle_v2/review/captive_magnet_slice_audit/slices/floor_stand_V1-A_slim_shoulder_3_of_4_bottom_right/ready/plate_1.gcode | 9ac352754b19aed76ab290842a4eec89ebefe0a56fb8faa391f78e68bba6ec97 | /Users/antor/gh/lx/top_baffle_v2/review/captive_magnet_slice_audit/slices/floor_stand_V1-A_slim_shoulder_3_of_4_bottom_right/ready/ready_to_print.gcode.3mf | aeb85842ef085d1859c303e0eeca04160edc1bcd211fd5df4fc43d4308292d0a | True | 00ad7604fb9961f80c76ce33af1271bff1f4b8801450d3ed90dd5bba4853be1b | /Users/antor/gh/lx/top_baffle_v2/review/captive_magnet_slice_audit/slices/floor_stand_V1-A_slim_shoulder_3_of_4_bottom_right/plate_1.gcode | 88ec36fe93182b126d2147ee078096fa60622a1ff016b69c47115460804f4148 | /Users/antor/gh/lx/top_baffle_v2/review/captive_magnet_slice_audit/slices/floor_stand_V1-A_slim_shoulder_3_of_4_bottom_right/audited_slice_project.3mf | 165520ea6ef801fb6d485d7f1a9d58cce1dbe7013140f89e411bf5a32dd81f1d | 0.0 | [{"site":"v1_lower_right_receiver","print_marked_pole_axis_xyz":[0.9584785342953424,0.2851646880226448,0.0],"installed_marked_pole_axis_xyz":[0.9584785342953424,-0.2851646880226448,0.0],"instruction":"marked/N pole points along the same installed pair-axis vector as the carrier magnet; the face toward the carrier is therefore the opposite pole"}]
floor_stand:V1-A:slim_shoulder_4_of_4_top_right | floor_stand | V1-A | slim_shoulder_4_of_4_top_right | front_face_down | 1 | v1_upper_right_receiver | 1 | 5.8 | 5.80 | 5.96 | 5.96 | 0.09999990000004377 | 0.2599999000000439 | [0.0,0.0,-1.0] | insert vertically downward from above the paused part (+Z side) through the open loading chimney along print -Z | /Users/antor/gh/lx/top_baffle_v2/build/floor_stand/stl/slim_shoulder_4_of_4_top_right.stl | 647ee1a713b756e5fc4900af2d5f824c204598c99108a6b34ab602f12e1f562e | /Users/antor/gh/lx/top_baffle_v2/review/captive_magnet_slice_audit/slices/floor_stand_V1-A_slim_shoulder_4_of_4_top_right/ready/plate_1.gcode | d929316ed73def9f90be2894395a9f9e76afab6847fb1f039b0619980801419b | /Users/antor/gh/lx/top_baffle_v2/review/captive_magnet_slice_audit/slices/floor_stand_V1-A_slim_shoulder_4_of_4_top_right/ready/ready_to_print.gcode.3mf | e61f7a5a2d8e0726318bdceafdbdfcb09d1a123750fec0898753cdc5abcb0a77 | True | cb1f0908579c525d665f8905e6ac2aa3d14ff81fb14aaae8baa9195a7c309ba0 | /Users/antor/gh/lx/top_baffle_v2/review/captive_magnet_slice_audit/slices/floor_stand_V1-A_slim_shoulder_4_of_4_top_right/plate_1.gcode | 7e0f702dae654922d578866d6cb40dab6e88d5d5254a10bba8ad719cbb5b3149 | /Users/antor/gh/lx/top_baffle_v2/review/captive_magnet_slice_audit/slices/floor_stand_V1-A_slim_shoulder_4_of_4_top_right/audited_slice_project.3mf | d27a2642257d9ee552e9520527667c2159f6172ff19a0c367ef52c1f35c67b34 | 0.0 | [{"site":"v1_upper_right_receiver","print_marked_pole_axis_xyz":[0.35021039696371,0.9366710617172503,0.0],"installed_marked_pole_axis_xyz":[0.35021039696371,-0.9366710617172503,0.0],"instruction":"marked/N pole points along the same installed pair-axis vector as the carrier magnet; the face toward the carrier is therefore the opposite pole"}]
floor_stand:V1-B1:slim_wing_1_of_2_left | floor_stand | V1-B1 | slim_wing_1_of_2_left | front_face_down | 1 | v1_lower_left_receiver; v1_upper_left_receiver | 2 | 5.8 | 5.80 | 5.96 | 5.96 | 0.09999990000004733 | 0.25999990000004747 | [0.0,0.0,-1.0] | insert vertically downward from above the paused part (+Z side) through the open loading chimney along print -Z | /Users/antor/gh/lx/top_baffle_v2/build/floor_stand/stl/slim_wing_1_of_2_left.stl | 7b8a1ef0d700cd196d177ad16eed0e51da2601f81e91f777a77df314e40cd788 | /Users/antor/gh/lx/top_baffle_v2/review/captive_magnet_slice_audit/slices/floor_stand_V1-B1_slim_wing_1_of_2_left/ready/plate_1.gcode | 0872780e02867e8448c93c8b1425a60d923ed6163beb10d06a8fb61399ae4811 | /Users/antor/gh/lx/top_baffle_v2/review/captive_magnet_slice_audit/slices/floor_stand_V1-B1_slim_wing_1_of_2_left/ready/ready_to_print.gcode.3mf | 7197e6b562ad17aa0db820b0134ca4b3f0400a28cf324890a86c14fb2a4c23ec | True | 49e37932abb85d6dc988dc3802085828de583ec736baf53778a079366eeca1f9 | /Users/antor/gh/lx/top_baffle_v2/review/captive_magnet_slice_audit/slices/floor_stand_V1-B1_slim_wing_1_of_2_left/plate_1.gcode | 7effbedfbe638f82a3a596c812563a38d4035f8f74f519f5d56839a9785d94e0 | /Users/antor/gh/lx/top_baffle_v2/review/captive_magnet_slice_audit/slices/floor_stand_V1-B1_slim_wing_1_of_2_left/audited_slice_project.3mf | 6b7e0a055e400a81980e3f0961ed9ea26d293efeaa82f4e3cf802b1167fa5aa3 | 0.0 | [{"site":"v1_lower_left_receiver","print_marked_pole_axis_xyz":[-0.9584785342953424,0.2851646880226448,0.0],"installed_marked_pole_axis_xyz":[-0.9584785342953424,-0.2851646880226448,0.0],"instruction":"marked/N pole points along the same installed pair-axis vector as the carrier magnet; the face toward the carrier is therefore the opposite pole"},{"site":"v1_upper_left_receiver","print_marked_pole_axis_xyz":[-0.35021039696371,0.9366710617172503,0.0],"installed_marked_pole_axis_xyz":[-0.35021039696371,-0.9366710617172503,0.0],"instruction":"marked/N pole points along the same installed pair-axis vector as the carrier magnet; the face toward the carrier is therefore the opposite pole"}]
floor_stand:V1-B1:slim_wing_2_of_2_right | floor_stand | V1-B1 | slim_wing_2_of_2_right | front_face_down | 1 | v1_lower_right_receiver; v1_upper_right_receiver | 2 | 5.8 | 5.80 | 5.96 | 5.96 | 0.09999990000004377 | 0.2599999000000439 | [0.0,0.0,-1.0] | insert vertically downward from above the paused part (+Z side) through the open loading chimney along print -Z | /Users/antor/gh/lx/top_baffle_v2/build/floor_stand/stl/slim_wing_2_of_2_right.stl | 52491d7e9e756a76699d176edd2f0303dbb2ab9a473b85f588fb0dee194d73e9 | /Users/antor/gh/lx/top_baffle_v2/review/captive_magnet_slice_audit/slices/floor_stand_V1-B1_slim_wing_2_of_2_right/ready/plate_1.gcode | 5598c7b267e4bf422c63e151a3c54ff2276e8a9cc900d4ef5515f658b519451d | /Users/antor/gh/lx/top_baffle_v2/review/captive_magnet_slice_audit/slices/floor_stand_V1-B1_slim_wing_2_of_2_right/ready/ready_to_print.gcode.3mf | 99ade88ae80850adc88b92b69a7194c99079e105c4f1f9e1fd5bb1a0d4bfdc44 | True | 1ede8bb10e19ad7a5a9c86a2e9b861588c3aa14d01f6d7116afc38f69b6c269f | /Users/antor/gh/lx/top_baffle_v2/review/captive_magnet_slice_audit/slices/floor_stand_V1-B1_slim_wing_2_of_2_right/plate_1.gcode | 3ab73c77002091b22ffbd53cc636f57d9c8fc6cc7baf5149069d08e40407d76b | /Users/antor/gh/lx/top_baffle_v2/review/captive_magnet_slice_audit/slices/floor_stand_V1-B1_slim_wing_2_of_2_right/audited_slice_project.3mf | 2ee1c5c1c04e9b2c6ee837a10f0f53ddbe64b388864e9963f1bea1d156e73262 | 0.0 | [{"site":"v1_lower_right_receiver","print_marked_pole_axis_xyz":[0.9584785342953424,0.2851646880226448,0.0],"installed_marked_pole_axis_xyz":[0.9584785342953424,-0.2851646880226448,0.0],"instruction":"marked/N pole points along the same installed pair-axis vector as the carrier magnet; the face toward the carrier is therefore the opposite pole"},{"site":"v1_upper_right_receiver","print_marked_pole_axis_xyz":[0.35021039696371,0.9366710617172503,0.0],"installed_marked_pole_axis_xyz":[0.35021039696371,-0.9366710617172503,0.0],"instruction":"marked/N pole points along the same installed pair-axis vector as the carrier magnet; the face toward the carrier is therefore the opposite pole"}]
floor_stand:V1L:slim_4_of_4_vase_b2 | floor_stand | V1L | slim_4_of_4_vase_b2 | front_face_down | 1 | v1_lower_right_base; v1_lower_left_base; v1_upper_right_base; v1_upper_left_base | 4 | 5.8 | 5.80 | 5.96 | 5.96 | 0.09999990000003667 | 0.2599999000000368 | [0.0,0.0,-1.0] | insert vertically downward from above the paused part (+Z side) through the open loading chimney along print -Z | /Users/antor/gh/lx/top_baffle_v2/build/floor_stand/stl/slim_4_of_4_vase_b2.stl | 894fdc60dc89f515b7b8f15b1e6af96d493423f4f0f8ec213e6f66643602de7a | /Users/antor/gh/lx/top_baffle_v2/review/captive_magnet_slice_audit/slices/floor_stand_V1L_slim_4_of_4_vase_b2/ready/plate_1.gcode | 428ae1fb49008ad492f702f8f975329b3c6a645aeca4d5d5f32a22ec035c953b | /Users/antor/gh/lx/top_baffle_v2/review/captive_magnet_slice_audit/slices/floor_stand_V1L_slim_4_of_4_vase_b2/ready/ready_to_print.gcode.3mf | 3e42c741c6cb5492bc904026e5ef6469e9916608bb93356d045f6859c8f927b8 | True | dbb9b50dcaaaf071922d9213794a6204154da54849a99700650968b71f574096 | /Users/antor/gh/lx/top_baffle_v2/review/captive_magnet_slice_audit/slices/floor_stand_V1L_slim_4_of_4_vase_b2/plate_1.gcode | d147f8e6469b69f0cc95a62a8542d687bf7ba53cb9f90ad8f7565752d0cd3830 | /Users/antor/gh/lx/top_baffle_v2/review/captive_magnet_slice_audit/slices/floor_stand_V1L_slim_4_of_4_vase_b2/audited_slice_project.3mf | c97360d06ac229a2bc70dc5374949206d9264c84706a4ec426a9c841abff5f62 | 0.0 | [{"site":"v1_lower_right_base","print_marked_pole_axis_xyz":[0.9584785342953424,0.2851646880226448,0.0],"installed_marked_pole_axis_xyz":[0.9584785342953424,-0.2851646880226448,0.0],"instruction":"marked/N pole points OUT from carrier toward its mating piece, along installed_marked_pole_axis_xyz"},{"site":"v1_lower_left_base","print_marked_pole_axis_xyz":[-0.9584785342953424,0.2851646880226448,0.0],"installed_marked_pole_axis_xyz":[-0.9584785342953424,-0.2851646880226448,0.0],"instruction":"marked/N pole points OUT from carrier toward its mating piece, along installed_marked_pole_axis_xyz"},{"site":"v1_upper_right_base","print_marked_pole_axis_xyz":[0.35021039696371,0.9366710617172503,0.0],"installed_marked_pole_axis_xyz":[0.35021039696371,-0.9366710617172503,0.0],"instruction":"marked/N pole points OUT from carrier toward its mating piece, along installed_marked_pole_axis_xyz"},{"site":"v1_upper_left_base","print_marked_pole_axis_xyz":[-0.35021039696371,0.9366710617172503,0.0],"installed_marked_pole_axis_xyz":[-0.35021039696371,-0.9366710617172503,0.0],"instruction":"marked/N pole points OUT from carrier toward its mating piece, along installed_marked_pole_axis_xyz"}]
floor_stand:coupon1:lx521_coupon_1_fit_plate | floor_stand | coupon1 | lx521_coupon_1_fit_plate | front_face_down | 1 | coupon1_v1_upper_base | 1 | 6.6 | 6.60 | 6.76 | 6.76 | 0.1999999999999993 | 0.35999999999999943 | [0.0,0.0,-1.0] | insert vertically downward from above the paused part (+Z side) through the open loading chimney along print -Z | /Users/antor/gh/lx/top_baffle_v2/build/floor_stand/stl/lx521_coupon_1_fit_plate.stl | 88ec70cfeaf03b854e8271aaac5d0646c24efbdba8d6f374fad12a644df425a3 | /Users/antor/gh/lx/top_baffle_v2/review/captive_magnet_slice_audit/slices/floor_stand_coupon1_lx521_coupon_1_fit_plate/ready/plate_1.gcode | 4b4de9860fb3bdde82bbe670bd9f668554a857d309adb62591176acfd12a0e3f | /Users/antor/gh/lx/top_baffle_v2/review/captive_magnet_slice_audit/slices/floor_stand_coupon1_lx521_coupon_1_fit_plate/ready/ready_to_print.gcode.3mf | 820cb82c6cb48c4ae0190db60ae0f20bb71049a33dd5dfa724373d9c4893711b | True | 257a737b839f2b1f9f5c18b50677d0e6b2ccae6ddfbcf3455c3cf2c711af7788 | /Users/antor/gh/lx/top_baffle_v2/review/captive_magnet_slice_audit/slices/floor_stand_coupon1_lx521_coupon_1_fit_plate/plate_1.gcode | 9585cef398791041497e4d732334091754630af9182d8ea4b6995945fe97ecdb | /Users/antor/gh/lx/top_baffle_v2/review/captive_magnet_slice_audit/slices/floor_stand_coupon1_lx521_coupon_1_fit_plate/audited_slice_project.3mf | 3fd00e66594c442b07d3ca61eb27a763084a61a58cfe89da28b478029ed18cd0 | 0.0 | [{"site":"coupon1_v1_upper_base","print_marked_pole_axis_xyz":[0.0,1.0,0.0],"installed_marked_pole_axis_xyz":[0.0,-1.0,0.0],"instruction":"unpaired coupon1 regression station: marked/N pole points along installed -Y (print +Y under its X180/Z0 transform); there is no mating magnet and no attraction claim"}]
no_floor_stand:A:stock_shoulder_1_of_4_top_left | no_floor_stand | A | stock_shoulder_1_of_4_top_left | front_face_down | 1 | stock_upper_left_receiver | 1 | 5.8 | 5.80 | 5.96 | 5.96 | 0.09999990000004377 | 0.2599999000000439 | [0.0,0.0,-1.0] | insert vertically downward from above the paused part (+Z side) through the open loading chimney along print -Z | /Users/antor/gh/lx/top_baffle_v2/build/no_floor_stand/stl/stock_shoulder_1_of_4_top_left.stl | c226846fba25d831631e1ae83f2d20bd4229407e62ae8a196c1116f13d903091 | /Users/antor/gh/lx/top_baffle_v2/review/captive_magnet_slice_audit/slices/no_floor_stand_A_stock_shoulder_1_of_4_top_left/ready/plate_1.gcode | 2a5980fef81d0066dd0b0d229097bf26e4a9aa77084199eb1aafed517efbb51a | /Users/antor/gh/lx/top_baffle_v2/review/captive_magnet_slice_audit/slices/no_floor_stand_A_stock_shoulder_1_of_4_top_left/ready/ready_to_print.gcode.3mf | 0b6d490dc4ed58ec08df7e82a6626861c81b75b89bc51bf7fd5e6b35e68834b4 | True | 6d45ef11195f4d75523646067901814e6044b51a00d3fd57fff778eeeaaec9bd | /Users/antor/gh/lx/top_baffle_v2/review/captive_magnet_slice_audit/slices/no_floor_stand_A_stock_shoulder_1_of_4_top_left/plate_1.gcode | fdf236d228405f8d1b6552924e9457ca39e982d1a3b6c28dc0fc9f0caf9403e8 | /Users/antor/gh/lx/top_baffle_v2/review/captive_magnet_slice_audit/slices/no_floor_stand_A_stock_shoulder_1_of_4_top_left/audited_slice_project.3mf | 4d1d456d25b1cf049b2e4ab67c6beda772b000df88b671d54df70bb7848700fa | 0.0 | [{"site":"stock_upper_left_receiver","print_marked_pole_axis_xyz":[-0.35021039696371,0.9366710617172503,0.0],"installed_marked_pole_axis_xyz":[-0.35021039696371,-0.9366710617172503,0.0],"instruction":"marked/N pole points along the same installed pair-axis vector as the carrier magnet; the face toward the carrier is therefore the opposite pole"}]
no_floor_stand:A:stock_shoulder_2_of_4_top_right | no_floor_stand | A | stock_shoulder_2_of_4_top_right | front_face_down | 1 | stock_upper_right_receiver | 1 | 5.8 | 5.80 | 5.96 | 5.96 | 0.09999990000004377 | 0.2599999000000439 | [0.0,0.0,-1.0] | insert vertically downward from above the paused part (+Z side) through the open loading chimney along print -Z | /Users/antor/gh/lx/top_baffle_v2/build/no_floor_stand/stl/stock_shoulder_2_of_4_top_right.stl | 97d976c11078ed0a4e6e6f4f3862bbcd9042994b48a21ef5ee254f8f71fd838f | /Users/antor/gh/lx/top_baffle_v2/review/captive_magnet_slice_audit/slices/no_floor_stand_A_stock_shoulder_2_of_4_top_right/ready/plate_1.gcode | 4cfdc754d05b23c6a39c87a67219c6531d7a8529e1babcc72042e17d4e17d8c5 | /Users/antor/gh/lx/top_baffle_v2/review/captive_magnet_slice_audit/slices/no_floor_stand_A_stock_shoulder_2_of_4_top_right/ready/ready_to_print.gcode.3mf | 360556315d5f5f1944bd6736ad8cd4a2c2d8c63a7fb4ea2acc2dbdf86698b7db | True | 66f568f6d31ac91b80e38f9aac3d48f9da2be0745d1b65e4cc52503fb66e73f3 | /Users/antor/gh/lx/top_baffle_v2/review/captive_magnet_slice_audit/slices/no_floor_stand_A_stock_shoulder_2_of_4_top_right/plate_1.gcode | 57f121d23c70590c077b9a2cb28c6c11b07c1fa8117812dbbde82369569d4a13 | /Users/antor/gh/lx/top_baffle_v2/review/captive_magnet_slice_audit/slices/no_floor_stand_A_stock_shoulder_2_of_4_top_right/audited_slice_project.3mf | 00ac30d6a805dd8b52fb29171a1a77e8a2cab05d58965d2cdccbf266857ad433 | 0.0 | [{"site":"stock_upper_right_receiver","print_marked_pole_axis_xyz":[0.35021039696371,0.9366710617172503,0.0],"installed_marked_pole_axis_xyz":[0.35021039696371,-0.9366710617172503,0.0],"instruction":"marked/N pole points along the same installed pair-axis vector as the carrier magnet; the face toward the carrier is therefore the opposite pole"}]
no_floor_stand:A:stock_shoulder_3_of_4_bottom_left | no_floor_stand | A | stock_shoulder_3_of_4_bottom_left | front_face_down | 1 | stock_lower_left_receiver | 1 | 5.8 | 5.80 | 5.96 | 5.96 | 0.10000000000003428 | 0.2600000000000344 | [0.0,0.0,-1.0] | insert vertically downward from above the paused part (+Z side) through the open loading chimney along print -Z | /Users/antor/gh/lx/top_baffle_v2/build/no_floor_stand/stl/stock_shoulder_3_of_4_bottom_left.stl | 498086f24109d792c45212144855bd570c06af4b5128fdca371a8cdb00960cf3 | /Users/antor/gh/lx/top_baffle_v2/review/captive_magnet_slice_audit/slices/no_floor_stand_A_stock_shoulder_3_of_4_bottom_left/ready/plate_1.gcode | 3b636d2fb762e508c71bc0c053d39d5117bba4bb5cf65b8fc3af6f1a76df46f1 | /Users/antor/gh/lx/top_baffle_v2/review/captive_magnet_slice_audit/slices/no_floor_stand_A_stock_shoulder_3_of_4_bottom_left/ready/ready_to_print.gcode.3mf | 2feb2895c7ebbebe1aca78276256b24b99c6fd541471da0c2f2f4652af84846f | True | f5f0df06f27cceb5a3f1cd30ca7574df3c2d46c181d265bffb64abb839c283be | /Users/antor/gh/lx/top_baffle_v2/review/captive_magnet_slice_audit/slices/no_floor_stand_A_stock_shoulder_3_of_4_bottom_left/plate_1.gcode | 0c83750224456f9d4228ad436e5ad0d516c2e0b9217aef8aa5bed7d7ea064439 | /Users/antor/gh/lx/top_baffle_v2/review/captive_magnet_slice_audit/slices/no_floor_stand_A_stock_shoulder_3_of_4_bottom_left/audited_slice_project.3mf | 768bac208799df1c3ea92492dc8b5fc09410d325fe300586cae9a080359c6819 | 0.0 | [{"site":"stock_lower_left_receiver","print_marked_pole_axis_xyz":[-0.9584785342953424,0.2851646880226448,0.0],"installed_marked_pole_axis_xyz":[-0.9584785342953424,-0.2851646880226448,0.0],"instruction":"marked/N pole points along the same installed pair-axis vector as the carrier magnet; the face toward the carrier is therefore the opposite pole"}]
no_floor_stand:A:stock_shoulder_4_of_4_bottom_right | no_floor_stand | A | stock_shoulder_4_of_4_bottom_right | front_face_down | 1 | stock_lower_right_receiver | 1 | 5.8 | 5.80 | 5.96 | 5.96 | 0.10000000000003428 | 0.2600000000000344 | [0.0,0.0,-1.0] | insert vertically downward from above the paused part (+Z side) through the open loading chimney along print -Z | /Users/antor/gh/lx/top_baffle_v2/build/no_floor_stand/stl/stock_shoulder_4_of_4_bottom_right.stl | 43fa254e1c788a6b9ec2170bf892955be8ec8321bc9aea0408f494038ea10792 | /Users/antor/gh/lx/top_baffle_v2/review/captive_magnet_slice_audit/slices/no_floor_stand_A_stock_shoulder_4_of_4_bottom_right/ready/plate_1.gcode | d6334076c57a43f5e6f58e8a61908affc5eafe03e5a6b325902133a75ba2ff14 | /Users/antor/gh/lx/top_baffle_v2/review/captive_magnet_slice_audit/slices/no_floor_stand_A_stock_shoulder_4_of_4_bottom_right/ready/ready_to_print.gcode.3mf | 5a5384889140f93455ee039be265e13a85f10ccdff054626a5dbaeb7e37ca1b4 | True | d70dc480c34808487fe88acc7b1810988d87492e11f926cdf1b72ef984207e96 | /Users/antor/gh/lx/top_baffle_v2/review/captive_magnet_slice_audit/slices/no_floor_stand_A_stock_shoulder_4_of_4_bottom_right/plate_1.gcode | 25016fd7e9f6eee4cb9e91b7c3735d0f3266d16bce17b16bf1840fc6ed205c39 | /Users/antor/gh/lx/top_baffle_v2/review/captive_magnet_slice_audit/slices/no_floor_stand_A_stock_shoulder_4_of_4_bottom_right/audited_slice_project.3mf | 06ffdcf4150d7d1214d2e50e3c7deefeab5028731f996c7eb4af858006f3279b | 0.0 | [{"site":"stock_lower_right_receiver","print_marked_pole_axis_xyz":[0.9584785342953424,0.2851646880226448,0.0],"installed_marked_pole_axis_xyz":[0.9584785342953424,-0.2851646880226448,0.0],"instruction":"marked/N pole points along the same installed pair-axis vector as the carrier magnet; the face toward the carrier is therefore the opposite pole"}]
no_floor_stand:B1:stock_wing_1_of_2_left | no_floor_stand | B1 | stock_wing_1_of_2_left | front_face_down | 1 | stock_lower_left_receiver; stock_upper_left_receiver | 2 | 5.8 | 5.80 | 5.96 | 5.96 | 0.09999990000004733 | 0.25999990000004747 | [0.0,0.0,-1.0] | insert vertically downward from above the paused part (+Z side) through the open loading chimney along print -Z | /Users/antor/gh/lx/top_baffle_v2/build/no_floor_stand/stl/stock_wing_1_of_2_left.stl | 7749a25921f930432d155f8988afe0dd8516f2b119560c11890f4f2a309794f1 | /Users/antor/gh/lx/top_baffle_v2/review/captive_magnet_slice_audit/slices/no_floor_stand_B1_stock_wing_1_of_2_left/ready/plate_1.gcode | 23f31e18fb84701437db74aafdfac289557b692e85e89933c29b05b877b5f2ca | /Users/antor/gh/lx/top_baffle_v2/review/captive_magnet_slice_audit/slices/no_floor_stand_B1_stock_wing_1_of_2_left/ready/ready_to_print.gcode.3mf | 0bb47eb3c830cfc413ffa02d9bfff688a1e7cc38053788fc3a87b40f1cbf365f | True | 1cc52713b0f182d44d0bef20f57600d4a3c3546c3a730397e45e2edb84dcadd2 | /Users/antor/gh/lx/top_baffle_v2/review/captive_magnet_slice_audit/slices/no_floor_stand_B1_stock_wing_1_of_2_left/plate_1.gcode | 552244fecbb3701a933bba542debf233b7830d090518fcba4ccb724406e83061 | /Users/antor/gh/lx/top_baffle_v2/review/captive_magnet_slice_audit/slices/no_floor_stand_B1_stock_wing_1_of_2_left/audited_slice_project.3mf | b65ca9696b7e8a444504f217adfff8fefaf25be9b92493cbaa61e776c7abbf98 | 0.0 | [{"site":"stock_lower_left_receiver","print_marked_pole_axis_xyz":[-0.9584785342953424,0.2851646880226448,0.0],"installed_marked_pole_axis_xyz":[-0.9584785342953424,-0.2851646880226448,0.0],"instruction":"marked/N pole points along the same installed pair-axis vector as the carrier magnet; the face toward the carrier is therefore the opposite pole"},{"site":"stock_upper_left_receiver","print_marked_pole_axis_xyz":[-0.35021039696371,0.9366710617172503,0.0],"installed_marked_pole_axis_xyz":[-0.35021039696371,-0.9366710617172503,0.0],"instruction":"marked/N pole points along the same installed pair-axis vector as the carrier magnet; the face toward the carrier is therefore the opposite pole"}]
no_floor_stand:B1:stock_wing_2_of_2_right | no_floor_stand | B1 | stock_wing_2_of_2_right | front_face_down | 1 | stock_lower_right_receiver; stock_upper_right_receiver | 2 | 5.8 | 5.80 | 5.96 | 5.96 | 0.09999990000004377 | 0.2599999000000439 | [0.0,0.0,-1.0] | insert vertically downward from above the paused part (+Z side) through the open loading chimney along print -Z | /Users/antor/gh/lx/top_baffle_v2/build/no_floor_stand/stl/stock_wing_2_of_2_right.stl | 8da84750e2cff0075955bd8245831ebfc0ddfc97d9bc36e97789069cadf5d67b | /Users/antor/gh/lx/top_baffle_v2/review/captive_magnet_slice_audit/slices/no_floor_stand_B1_stock_wing_2_of_2_right/ready/plate_1.gcode | 4b76571b6f5b22031e16d6dc48e7aadf4e487447e2f1842308d207289c511c73 | /Users/antor/gh/lx/top_baffle_v2/review/captive_magnet_slice_audit/slices/no_floor_stand_B1_stock_wing_2_of_2_right/ready/ready_to_print.gcode.3mf | c703b4f71c9e0f3d35b235c8b378f083078080121dc9367eb52b4a782164a9ce | True | c23323662c73139bf341c031ea673018bae09d9f17a6fb1acd935e785277fbb9 | /Users/antor/gh/lx/top_baffle_v2/review/captive_magnet_slice_audit/slices/no_floor_stand_B1_stock_wing_2_of_2_right/plate_1.gcode | 3f3cb71d05d96d5e971e241a97a66ceabb5fc9da4982aa4e8e57258c93a596da | /Users/antor/gh/lx/top_baffle_v2/review/captive_magnet_slice_audit/slices/no_floor_stand_B1_stock_wing_2_of_2_right/audited_slice_project.3mf | bc4b3725dd996bc08fec06386ea9bb9d57639baed3cbceae2edb3f2c6c235e75 | 0.0 | [{"site":"stock_lower_right_receiver","print_marked_pole_axis_xyz":[0.9584785342953424,0.2851646880226448,0.0],"installed_marked_pole_axis_xyz":[0.9584785342953424,-0.2851646880226448,0.0],"instruction":"marked/N pole points along the same installed pair-axis vector as the carrier magnet; the face toward the carrier is therefore the opposite pole"},{"site":"stock_upper_right_receiver","print_marked_pole_axis_xyz":[0.35021039696371,0.9366710617172503,0.0],"installed_marked_pole_axis_xyz":[0.35021039696371,-0.9366710617172503,0.0],"instruction":"marked/N pole points along the same installed pair-axis vector as the carrier magnet; the face toward the carrier is therefore the opposite pole"}]
no_floor_stand:B2:stock_4_of_4_vase_b2 | no_floor_stand | B2 | stock_4_of_4_vase_b2 | front_face_down | 1 | stock_lower_right_base; stock_lower_left_base; stock_upper_right_base; stock_upper_left_base | 4 | 5.8 | 5.80 | 5.96 | 5.96 | 0.09999990000003667 | 0.2599999000000368 | [0.0,0.0,-1.0] | insert vertically downward from above the paused part (+Z side) through the open loading chimney along print -Z | /Users/antor/gh/lx/top_baffle_v2/build/no_floor_stand/stl/stock_4_of_4_vase_b2.stl | b8bf6122dbb5fa5e9f26f401264ef92a13c94149629db6742231b4a35ed38833 | /Users/antor/gh/lx/top_baffle_v2/review/captive_magnet_slice_audit/slices/no_floor_stand_B2_stock_4_of_4_vase_b2/ready/plate_1.gcode | 00a353e3e4cfeed4ace075a56dcf25026b6d84db32f1cae6c7d370c068b05403 | /Users/antor/gh/lx/top_baffle_v2/review/captive_magnet_slice_audit/slices/no_floor_stand_B2_stock_4_of_4_vase_b2/ready/ready_to_print.gcode.3mf | e35b1c09b3502db863b323f29f1d2d0f86cef96dd084bb916fa7daf74f807e8e | True | 14aa8719e598db9956c52de7135c86fd37f34be2aace56ec83928c65aa368f57 | /Users/antor/gh/lx/top_baffle_v2/review/captive_magnet_slice_audit/slices/no_floor_stand_B2_stock_4_of_4_vase_b2/plate_1.gcode | bfed7362f4ec882ca44550ddfcb2d5a5c526cf37470f2af46f93edd3a5d107fc | /Users/antor/gh/lx/top_baffle_v2/review/captive_magnet_slice_audit/slices/no_floor_stand_B2_stock_4_of_4_vase_b2/audited_slice_project.3mf | 56b4d625e9735cbc9c987db5a05418afeefb625420cbea04d2dfffee5bb32d29 | 0.0 | [{"site":"stock_lower_right_base","print_marked_pole_axis_xyz":[0.9584785342953424,0.2851646880226448,0.0],"installed_marked_pole_axis_xyz":[0.9584785342953424,-0.2851646880226448,0.0],"instruction":"marked/N pole points OUT from carrier toward its mating piece, along installed_marked_pole_axis_xyz"},{"site":"stock_lower_left_base","print_marked_pole_axis_xyz":[-0.9584785342953424,0.2851646880226448,0.0],"installed_marked_pole_axis_xyz":[-0.9584785342953424,-0.2851646880226448,0.0],"instruction":"marked/N pole points OUT from carrier toward its mating piece, along installed_marked_pole_axis_xyz"},{"site":"stock_upper_right_base","print_marked_pole_axis_xyz":[0.35021039696371,0.9366710617172503,0.0],"installed_marked_pole_axis_xyz":[0.35021039696371,-0.9366710617172503,0.0],"instruction":"marked/N pole points OUT from carrier toward its mating piece, along installed_marked_pole_axis_xyz"},{"site":"stock_upper_left_base","print_marked_pole_axis_xyz":[-0.35021039696371,0.9366710617172503,0.0],"installed_marked_pole_axis_xyz":[-0.35021039696371,-0.9366710617172503,0.0],"instruction":"marked/N pole points OUT from carrier toward its mating piece, along installed_marked_pole_axis_xyz"}]
no_floor_stand:Obi-Wan-split:obiwan_optional_lm_keyed_1_of_2_bottom | no_floor_stand | Obi-Wan-split | obiwan_optional_lm_keyed_1_of_2_bottom | front_face_down | 1 | lm_lower_left; lm_lower_right | 2 | 5.8 | 5.80 | 5.96 | 5.96 | 0.09999990000001535 | 0.2599999000000155 | [0.0,0.0,-1.0] | insert vertically downward from above the paused part (+Z side) through the open loading chimney along print -Z | /Users/antor/gh/lx/top_baffle_v2/build/no_floor_stand/stl/obiwan_optional_lm_keyed_1_of_2_bottom.stl | 87bcfde710cf16eb7ff094631e27071721a913945b55f23fdc34ebd36660eb23 | /Users/antor/gh/lx/top_baffle_v2/review/captive_magnet_slice_audit/slices/no_floor_stand_Obi-Wan-split_obiwan_optional_lm_keyed_1_of_2_bottom/ready/plate_1.gcode | 6e44bf7ac7f08b4537df3579836b41320fd1ad24285cfbed60c751731cb8f244 | /Users/antor/gh/lx/top_baffle_v2/review/captive_magnet_slice_audit/slices/no_floor_stand_Obi-Wan-split_obiwan_optional_lm_keyed_1_of_2_bottom/ready/ready_to_print.gcode.3mf | 1629c1af9c825eea0569ea97a90d1b06e63c2eabb3a51460d5bb3d0eed2f1cb8 | True | bd51b0cc2378aeceed2f05bcb30adf1c98cbfaf28180dd5fac8cedbe0a164cab | /Users/antor/gh/lx/top_baffle_v2/review/captive_magnet_slice_audit/slices/no_floor_stand_Obi-Wan-split_obiwan_optional_lm_keyed_1_of_2_bottom/plate_1.gcode | 2e9ea02879d58661f38f5af7439ee619d0c764387a6e0b022f4bdf785b5fb5d8 | /Users/antor/gh/lx/top_baffle_v2/review/captive_magnet_slice_audit/slices/no_floor_stand_Obi-Wan-split_obiwan_optional_lm_keyed_1_of_2_bottom/audited_slice_project.3mf | a61ace8a1a219b007fd2761624108a1342d219c51745f9202bd3a931f14b2eb0 | 0.0 | [{"site":"lm_lower_left","print_marked_pole_axis_xyz":[-0.9452165115184645,0.3264440937631809,0.0],"installed_marked_pole_axis_xyz":[-0.7064513012709772,-0.7077616540421945,0.0],"instruction":"marked/N pole points OUT from carrier toward its mating piece, along installed_marked_pole_axis_xyz"},{"site":"lm_lower_right","print_marked_pole_axis_xyz":[0.32469193564684246,0.9458198279407695,0.0],"installed_marked_pole_axis_xyz":[0.7064513012709772,-0.7077616540421945,0.0],"instruction":"marked/N pole points OUT from carrier toward its mating piece, along installed_marked_pole_axis_xyz"}]
no_floor_stand:Obi-Wan-split:obiwan_optional_lm_keyed_2_of_2_top | no_floor_stand | Obi-Wan-split | obiwan_optional_lm_keyed_2_of_2_top | front_face_down | 1 | lm_upper_left; lm_upper_right | 2 | 5.8 | 5.80 | 5.96 | 5.96 | 0.09999990000001535 | 0.2599999000000155 | [0.0,0.0,-1.0] | insert vertically downward from above the paused part (+Z side) through the open loading chimney along print -Z | /Users/antor/gh/lx/top_baffle_v2/build/no_floor_stand/stl/obiwan_optional_lm_keyed_2_of_2_top.stl | 8070ccbdd173aabe88e62020ce03f729a184750a8c3665caf8cc7d9e671adfe5 | /Users/antor/gh/lx/top_baffle_v2/review/captive_magnet_slice_audit/slices/no_floor_stand_Obi-Wan-split_obiwan_optional_lm_keyed_2_of_2_top/ready/plate_1.gcode | a9f600a284468260f152e1e0354bbb8f6146be453f4b62800ea19cf8d402bf5f | /Users/antor/gh/lx/top_baffle_v2/review/captive_magnet_slice_audit/slices/no_floor_stand_Obi-Wan-split_obiwan_optional_lm_keyed_2_of_2_top/ready/ready_to_print.gcode.3mf | 0462e346942f2316196c9ad7620bbaffa9c47959c618a75917e31f86f2a67143 | True | 8eb223142f22624c89a34693317dab8ef5bf7953699e4f30231725b85634cbd0 | /Users/antor/gh/lx/top_baffle_v2/review/captive_magnet_slice_audit/slices/no_floor_stand_Obi-Wan-split_obiwan_optional_lm_keyed_2_of_2_top/plate_1.gcode | cc16ee04c944ecf8d73ee35e1006ab9966f8d4daa99bc8cd0b12ebbe0dad8e27 | /Users/antor/gh/lx/top_baffle_v2/review/captive_magnet_slice_audit/slices/no_floor_stand_Obi-Wan-split_obiwan_optional_lm_keyed_2_of_2_top/audited_slice_project.3mf | b48f63e2e252d7aaaa08a435b19ac890a8cca447017e62a68e20fcc2ce6e13cf | 0.0 | [{"site":"lm_upper_left","print_marked_pole_axis_xyz":[0.3255681544571566,-0.9455185755993172,0.0],"installed_marked_pole_axis_xyz":[-0.4383711467890776,0.8987940462991671,0.0],"instruction":"marked/N pole points OUT from carrier toward its mating piece, along installed_marked_pole_axis_xyz"},{"site":"lm_upper_right","print_marked_pole_axis_xyz":[0.9455185755993168,-0.32556815445715676,0.0],"installed_marked_pole_axis_xyz":[0.43837114678907746,0.898794046299167,0.0],"instruction":"marked/N pole points OUT from carrier toward its mating piece, along installed_marked_pole_axis_xyz"}]
no_floor_stand:Obi-Wan:obiwan_core_2_of_2_um_carrier | no_floor_stand | Obi-Wan | obiwan_core_2_of_2_um_carrier | front_face_down | 1 | um_left; um_right | 2 | 5.8 | 5.80 | 5.96 | 5.96 | 0.09999990000003667 | 0.2599999000000368 | [0.0,0.0,-1.0] | insert vertically downward from above the paused part (+Z side) through the open loading chimney along print -Z | /Users/antor/gh/lx/top_baffle_v2/build/no_floor_stand/stl/obiwan_core_2_of_2_um_carrier.stl | fbf826d4d10de7f28049a649c3fb9a4464d5d3713ee35baf62780667d7608750 | /Users/antor/gh/lx/top_baffle_v2/review/captive_magnet_slice_audit/slices/no_floor_stand_Obi-Wan_obiwan_core_2_of_2_um_carrier/ready/plate_1.gcode | acb5c3066d213ad89ab19578135c8814af45b41249cb31b876f34dbf817bc3fe | /Users/antor/gh/lx/top_baffle_v2/review/captive_magnet_slice_audit/slices/no_floor_stand_Obi-Wan_obiwan_core_2_of_2_um_carrier/ready/ready_to_print.gcode.3mf | 4c4dbdf38d6e8f60d1cc65ba235c245e4732cb2966bcc3fad18e13cdbdc50b05 | True | 028a11cfdcd5cf5310730cdb6aa91613d6aa3eff11e627e4f5126e1d7b931e01 | /Users/antor/gh/lx/top_baffle_v2/review/captive_magnet_slice_audit/slices/no_floor_stand_Obi-Wan_obiwan_core_2_of_2_um_carrier/plate_1.gcode | 8c61dd268d1eb66844a70ec7121893da3ce06482d76e1368325d8124d93e7e3f | /Users/antor/gh/lx/top_baffle_v2/review/captive_magnet_slice_audit/slices/no_floor_stand_Obi-Wan_obiwan_core_2_of_2_um_carrier/audited_slice_project.3mf | 86bce769ce9af89c413f8cba297ee67c1e2df78dde272543ad5c01166952300c | 0.0 | [{"site":"um_left","print_marked_pole_axis_xyz":[-0.6360782202777641,-0.7716245833877199,0.0],"installed_marked_pole_axis_xyz":[-0.6360782202777641,0.7716245833877199,0.0],"instruction":"marked/N pole points OUT from carrier toward its mating piece, along installed_marked_pole_axis_xyz"},{"site":"um_right","print_marked_pole_axis_xyz":[0.636078220277764,-0.77162458338772,0.0],"installed_marked_pole_axis_xyz":[0.636078220277764,0.77162458338772,0.0],"instruction":"marked/N pole points OUT from carrier toward its mating piece, along installed_marked_pole_axis_xyz"}]
no_floor_stand:V1-A:slim_shoulder_1_of_4_bottom_left | no_floor_stand | V1-A | slim_shoulder_1_of_4_bottom_left | front_face_down | 1 | v1_lower_left_receiver | 1 | 5.8 | 5.80 | 5.96 | 5.96 | 0.10000000000003428 | 0.2600000000000344 | [0.0,0.0,-1.0] | insert vertically downward from above the paused part (+Z side) through the open loading chimney along print -Z | /Users/antor/gh/lx/top_baffle_v2/build/no_floor_stand/stl/slim_shoulder_1_of_4_bottom_left.stl | 7ece5a1b6edf2e30a5764feb5abc982f8bb85bffb5269ebc66cbfacff1bcd2af | /Users/antor/gh/lx/top_baffle_v2/review/captive_magnet_slice_audit/slices/no_floor_stand_V1-A_slim_shoulder_1_of_4_bottom_left/ready/plate_1.gcode | 4c86c10926387d335bc4c7c7e9329a6449aae0b321c955628f954de970a4b2be | /Users/antor/gh/lx/top_baffle_v2/review/captive_magnet_slice_audit/slices/no_floor_stand_V1-A_slim_shoulder_1_of_4_bottom_left/ready/ready_to_print.gcode.3mf | 30eab6cda8e6dfac05860f20d469bd8976320fc8abc6a8cdeaf27987a566b326 | True | ff4893a285fc0b8068825ef1dd43b25abfb5ccc8529a3eb16813585dc5aaeeb3 | /Users/antor/gh/lx/top_baffle_v2/review/captive_magnet_slice_audit/slices/no_floor_stand_V1-A_slim_shoulder_1_of_4_bottom_left/plate_1.gcode | 6f8fcc63eeca282d6372c99ef37c71993d7e08c7c21e6eb49362198a3bbf9548 | /Users/antor/gh/lx/top_baffle_v2/review/captive_magnet_slice_audit/slices/no_floor_stand_V1-A_slim_shoulder_1_of_4_bottom_left/audited_slice_project.3mf | 4d3e4a87e28192affeb3ba79dac0f722e677713e1011af41ddec3419fdd4efda | 0.0 | [{"site":"v1_lower_left_receiver","print_marked_pole_axis_xyz":[-0.9584785342953424,0.2851646880226448,0.0],"installed_marked_pole_axis_xyz":[-0.9584785342953424,-0.2851646880226448,0.0],"instruction":"marked/N pole points along the same installed pair-axis vector as the carrier magnet; the face toward the carrier is therefore the opposite pole"}]
no_floor_stand:V1-A:slim_shoulder_2_of_4_top_left | no_floor_stand | V1-A | slim_shoulder_2_of_4_top_left | front_face_down | 1 | v1_upper_left_receiver | 1 | 5.8 | 5.80 | 5.96 | 5.96 | 0.09999990000004377 | 0.2599999000000439 | [0.0,0.0,-1.0] | insert vertically downward from above the paused part (+Z side) through the open loading chimney along print -Z | /Users/antor/gh/lx/top_baffle_v2/build/no_floor_stand/stl/slim_shoulder_2_of_4_top_left.stl | 6336437600757c539da9e109d44901fdb078da56c6e41d37c03b7c4717e5c6a1 | /Users/antor/gh/lx/top_baffle_v2/review/captive_magnet_slice_audit/slices/no_floor_stand_V1-A_slim_shoulder_2_of_4_top_left/ready/plate_1.gcode | 6cceafc155ecfd8b341c6cded1d0231d1668a593ea164a135646e2381715352a | /Users/antor/gh/lx/top_baffle_v2/review/captive_magnet_slice_audit/slices/no_floor_stand_V1-A_slim_shoulder_2_of_4_top_left/ready/ready_to_print.gcode.3mf | c0acd2ab93ede487cac4811505197289dee1bdc5f2939dd3f1740ebabf5e16cb | True | c8f22c4abe7f981413cac9389b6ab241b62a9b2d004564d884cf7d1c5801a310 | /Users/antor/gh/lx/top_baffle_v2/review/captive_magnet_slice_audit/slices/no_floor_stand_V1-A_slim_shoulder_2_of_4_top_left/plate_1.gcode | 13c27bb0b2aa024bd782e6bff6b892ec849e7eb8e3940ffe2459f6ee65b1e0b1 | /Users/antor/gh/lx/top_baffle_v2/review/captive_magnet_slice_audit/slices/no_floor_stand_V1-A_slim_shoulder_2_of_4_top_left/audited_slice_project.3mf | c64034c5557aa950a7fb03988ab8440090e1fe198c7cfaf789a0f3d99cb3e781 | 0.0 | [{"site":"v1_upper_left_receiver","print_marked_pole_axis_xyz":[-0.35021039696371,0.9366710617172503,0.0],"installed_marked_pole_axis_xyz":[-0.35021039696371,-0.9366710617172503,0.0],"instruction":"marked/N pole points along the same installed pair-axis vector as the carrier magnet; the face toward the carrier is therefore the opposite pole"}]
no_floor_stand:V1-A:slim_shoulder_3_of_4_bottom_right | no_floor_stand | V1-A | slim_shoulder_3_of_4_bottom_right | front_face_down | 1 | v1_lower_right_receiver | 1 | 5.8 | 5.80 | 5.96 | 5.96 | 0.10000000000003428 | 0.2600000000000344 | [0.0,0.0,-1.0] | insert vertically downward from above the paused part (+Z side) through the open loading chimney along print -Z | /Users/antor/gh/lx/top_baffle_v2/build/no_floor_stand/stl/slim_shoulder_3_of_4_bottom_right.stl | 3c520a232faa90973f9b422c8f8f549dc2d4d25cbb67ba466989bdb5f079b398 | /Users/antor/gh/lx/top_baffle_v2/review/captive_magnet_slice_audit/slices/no_floor_stand_V1-A_slim_shoulder_3_of_4_bottom_right/ready/plate_1.gcode | 9ac352754b19aed76ab290842a4eec89ebefe0a56fb8faa391f78e68bba6ec97 | /Users/antor/gh/lx/top_baffle_v2/review/captive_magnet_slice_audit/slices/no_floor_stand_V1-A_slim_shoulder_3_of_4_bottom_right/ready/ready_to_print.gcode.3mf | 14e7aa324a3bd39531c0facc388c9ecb1ad1840b75def5e0728899c94e4ee497 | True | b60324c0b648f427145f8b6ba44fda65a95e607c8a5450de2a8f3e135ef5f999 | /Users/antor/gh/lx/top_baffle_v2/review/captive_magnet_slice_audit/slices/no_floor_stand_V1-A_slim_shoulder_3_of_4_bottom_right/plate_1.gcode | 88ec36fe93182b126d2147ee078096fa60622a1ff016b69c47115460804f4148 | /Users/antor/gh/lx/top_baffle_v2/review/captive_magnet_slice_audit/slices/no_floor_stand_V1-A_slim_shoulder_3_of_4_bottom_right/audited_slice_project.3mf | 3df027a6c41b1b16e2d6c00da5a43253739a953b777c98524be05c4953aace6c | 0.0 | [{"site":"v1_lower_right_receiver","print_marked_pole_axis_xyz":[0.9584785342953424,0.2851646880226448,0.0],"installed_marked_pole_axis_xyz":[0.9584785342953424,-0.2851646880226448,0.0],"instruction":"marked/N pole points along the same installed pair-axis vector as the carrier magnet; the face toward the carrier is therefore the opposite pole"}]
no_floor_stand:V1-A:slim_shoulder_4_of_4_top_right | no_floor_stand | V1-A | slim_shoulder_4_of_4_top_right | front_face_down | 1 | v1_upper_right_receiver | 1 | 5.8 | 5.80 | 5.96 | 5.96 | 0.09999990000004377 | 0.2599999000000439 | [0.0,0.0,-1.0] | insert vertically downward from above the paused part (+Z side) through the open loading chimney along print -Z | /Users/antor/gh/lx/top_baffle_v2/build/no_floor_stand/stl/slim_shoulder_4_of_4_top_right.stl | 647ee1a713b756e5fc4900af2d5f824c204598c99108a6b34ab602f12e1f562e | /Users/antor/gh/lx/top_baffle_v2/review/captive_magnet_slice_audit/slices/no_floor_stand_V1-A_slim_shoulder_4_of_4_top_right/ready/plate_1.gcode | d929316ed73def9f90be2894395a9f9e76afab6847fb1f039b0619980801419b | /Users/antor/gh/lx/top_baffle_v2/review/captive_magnet_slice_audit/slices/no_floor_stand_V1-A_slim_shoulder_4_of_4_top_right/ready/ready_to_print.gcode.3mf | 0119427b3be5e2fdb5a6dc245b90e229eddf886efe897cc7b77ad449c2734bcb | True | 640bf56beb3fb20dee72ac983c834161fbf54e9a71b2fdeadd3593cb7eac5391 | /Users/antor/gh/lx/top_baffle_v2/review/captive_magnet_slice_audit/slices/no_floor_stand_V1-A_slim_shoulder_4_of_4_top_right/plate_1.gcode | 7e0f702dae654922d578866d6cb40dab6e88d5d5254a10bba8ad719cbb5b3149 | /Users/antor/gh/lx/top_baffle_v2/review/captive_magnet_slice_audit/slices/no_floor_stand_V1-A_slim_shoulder_4_of_4_top_right/audited_slice_project.3mf | e7982596f13e12db19aed0d26bdf2996455a5edccef4b82a280b799f5c483513 | 0.0 | [{"site":"v1_upper_right_receiver","print_marked_pole_axis_xyz":[0.35021039696371,0.9366710617172503,0.0],"installed_marked_pole_axis_xyz":[0.35021039696371,-0.9366710617172503,0.0],"instruction":"marked/N pole points along the same installed pair-axis vector as the carrier magnet; the face toward the carrier is therefore the opposite pole"}]
no_floor_stand:V1-B1:slim_wing_1_of_2_left | no_floor_stand | V1-B1 | slim_wing_1_of_2_left | front_face_down | 1 | v1_lower_left_receiver; v1_upper_left_receiver | 2 | 5.8 | 5.80 | 5.96 | 5.96 | 0.09999990000004733 | 0.25999990000004747 | [0.0,0.0,-1.0] | insert vertically downward from above the paused part (+Z side) through the open loading chimney along print -Z | /Users/antor/gh/lx/top_baffle_v2/build/no_floor_stand/stl/slim_wing_1_of_2_left.stl | 7b8a1ef0d700cd196d177ad16eed0e51da2601f81e91f777a77df314e40cd788 | /Users/antor/gh/lx/top_baffle_v2/review/captive_magnet_slice_audit/slices/no_floor_stand_V1-B1_slim_wing_1_of_2_left/ready/plate_1.gcode | 0872780e02867e8448c93c8b1425a60d923ed6163beb10d06a8fb61399ae4811 | /Users/antor/gh/lx/top_baffle_v2/review/captive_magnet_slice_audit/slices/no_floor_stand_V1-B1_slim_wing_1_of_2_left/ready/ready_to_print.gcode.3mf | dcd505ee1a236b502fb51f785b76dc671cb553077d40686d9df6e57b29510de2 | True | 9f8aaf308eb7b4541ebd0521b89fc91d8cd22a5cdabefc38a278608e939734bb | /Users/antor/gh/lx/top_baffle_v2/review/captive_magnet_slice_audit/slices/no_floor_stand_V1-B1_slim_wing_1_of_2_left/plate_1.gcode | 7effbedfbe638f82a3a596c812563a38d4035f8f74f519f5d56839a9785d94e0 | /Users/antor/gh/lx/top_baffle_v2/review/captive_magnet_slice_audit/slices/no_floor_stand_V1-B1_slim_wing_1_of_2_left/audited_slice_project.3mf | 78bc840fc5d78afd6be1da53de308f1bf9f09be6f0c28dfdb416df4c1e128f02 | 0.0 | [{"site":"v1_lower_left_receiver","print_marked_pole_axis_xyz":[-0.9584785342953424,0.2851646880226448,0.0],"installed_marked_pole_axis_xyz":[-0.9584785342953424,-0.2851646880226448,0.0],"instruction":"marked/N pole points along the same installed pair-axis vector as the carrier magnet; the face toward the carrier is therefore the opposite pole"},{"site":"v1_upper_left_receiver","print_marked_pole_axis_xyz":[-0.35021039696371,0.9366710617172503,0.0],"installed_marked_pole_axis_xyz":[-0.35021039696371,-0.9366710617172503,0.0],"instruction":"marked/N pole points along the same installed pair-axis vector as the carrier magnet; the face toward the carrier is therefore the opposite pole"}]
no_floor_stand:V1-B1:slim_wing_2_of_2_right | no_floor_stand | V1-B1 | slim_wing_2_of_2_right | front_face_down | 1 | v1_lower_right_receiver; v1_upper_right_receiver | 2 | 5.8 | 5.80 | 5.96 | 5.96 | 0.09999990000004377 | 0.2599999000000439 | [0.0,0.0,-1.0] | insert vertically downward from above the paused part (+Z side) through the open loading chimney along print -Z | /Users/antor/gh/lx/top_baffle_v2/build/no_floor_stand/stl/slim_wing_2_of_2_right.stl | 52491d7e9e756a76699d176edd2f0303dbb2ab9a473b85f588fb0dee194d73e9 | /Users/antor/gh/lx/top_baffle_v2/review/captive_magnet_slice_audit/slices/no_floor_stand_V1-B1_slim_wing_2_of_2_right/ready/plate_1.gcode | 68887254adc1383a234a18e51937d5a440e967b28ebb45f899caead36f28f071 | /Users/antor/gh/lx/top_baffle_v2/review/captive_magnet_slice_audit/slices/no_floor_stand_V1-B1_slim_wing_2_of_2_right/ready/ready_to_print.gcode.3mf | 8a779f218aa71b0755be489f17e6a21577b8501a4ab7fe76ab1f510f4d018963 | True | b617b71664a22df6f401eae009022114ca5991bc4cc6e20690e77b210cd90c93 | /Users/antor/gh/lx/top_baffle_v2/review/captive_magnet_slice_audit/slices/no_floor_stand_V1-B1_slim_wing_2_of_2_right/plate_1.gcode | 3ab73c77002091b22ffbd53cc636f57d9c8fc6cc7baf5149069d08e40407d76b | /Users/antor/gh/lx/top_baffle_v2/review/captive_magnet_slice_audit/slices/no_floor_stand_V1-B1_slim_wing_2_of_2_right/audited_slice_project.3mf | e1fa3202a4f49c4252f525567642f3816c7667ff7e442c55caa52345222616ea | 0.0 | [{"site":"v1_lower_right_receiver","print_marked_pole_axis_xyz":[0.9584785342953424,0.2851646880226448,0.0],"installed_marked_pole_axis_xyz":[0.9584785342953424,-0.2851646880226448,0.0],"instruction":"marked/N pole points along the same installed pair-axis vector as the carrier magnet; the face toward the carrier is therefore the opposite pole"},{"site":"v1_upper_right_receiver","print_marked_pole_axis_xyz":[0.35021039696371,0.9366710617172503,0.0],"installed_marked_pole_axis_xyz":[0.35021039696371,-0.9366710617172503,0.0],"instruction":"marked/N pole points along the same installed pair-axis vector as the carrier magnet; the face toward the carrier is therefore the opposite pole"}]
no_floor_stand:V1L:slim_4_of_4_vase_b2 | no_floor_stand | V1L | slim_4_of_4_vase_b2 | front_face_down | 1 | v1_lower_right_base; v1_lower_left_base; v1_upper_right_base; v1_upper_left_base | 4 | 5.8 | 5.80 | 5.96 | 5.96 | 0.09999990000003667 | 0.2599999000000368 | [0.0,0.0,-1.0] | insert vertically downward from above the paused part (+Z side) through the open loading chimney along print -Z | /Users/antor/gh/lx/top_baffle_v2/build/no_floor_stand/stl/slim_4_of_4_vase_b2.stl | 33ee34409d1de413ca149d16c06fd670b093f110a6e9ce60fa7248821068ea0d | /Users/antor/gh/lx/top_baffle_v2/review/captive_magnet_slice_audit/slices/no_floor_stand_V1L_slim_4_of_4_vase_b2/ready/plate_1.gcode | 4bec8470bcab6de78bbd698abfc6e151e2ab028c4b48be72e19f5d7db0e3ff48 | /Users/antor/gh/lx/top_baffle_v2/review/captive_magnet_slice_audit/slices/no_floor_stand_V1L_slim_4_of_4_vase_b2/ready/ready_to_print.gcode.3mf | 0d89a94294cf20c7f2d7c39377b4ecf5d726b9f1e13ff64cf0cfa2cbc31cb736 | True | 8b3200b50ce40b8a103c40ced1e4d6f2cffdcc0eceb489ca36f2ab47ee17b4e3 | /Users/antor/gh/lx/top_baffle_v2/review/captive_magnet_slice_audit/slices/no_floor_stand_V1L_slim_4_of_4_vase_b2/plate_1.gcode | 541af2c4419c440f185c4008608fa207ff747b10389439b0ba1034c49336735b | /Users/antor/gh/lx/top_baffle_v2/review/captive_magnet_slice_audit/slices/no_floor_stand_V1L_slim_4_of_4_vase_b2/audited_slice_project.3mf | 6753a027241de93e1e7cd5de41ac183a91512a94cb3f2c8cb6dfbe2c2493d917 | 0.0 | [{"site":"v1_lower_right_base","print_marked_pole_axis_xyz":[0.9584785342953424,0.2851646880226448,0.0],"installed_marked_pole_axis_xyz":[0.9584785342953424,-0.2851646880226448,0.0],"instruction":"marked/N pole points OUT from carrier toward its mating piece, along installed_marked_pole_axis_xyz"},{"site":"v1_lower_left_base","print_marked_pole_axis_xyz":[-0.9584785342953424,0.2851646880226448,0.0],"installed_marked_pole_axis_xyz":[-0.9584785342953424,-0.2851646880226448,0.0],"instruction":"marked/N pole points OUT from carrier toward its mating piece, along installed_marked_pole_axis_xyz"},{"site":"v1_upper_right_base","print_marked_pole_axis_xyz":[0.35021039696371,0.9366710617172503,0.0],"installed_marked_pole_axis_xyz":[0.35021039696371,-0.9366710617172503,0.0],"instruction":"marked/N pole points OUT from carrier toward its mating piece, along installed_marked_pole_axis_xyz"},{"site":"v1_upper_left_base","print_marked_pole_axis_xyz":[-0.35021039696371,0.9366710617172503,0.0],"installed_marked_pole_axis_xyz":[-0.35021039696371,-0.9366710617172503,0.0],"instruction":"marked/N pole points OUT from carrier toward its mating piece, along installed_marked_pole_axis_xyz"}]
no_floor_stand:coupon1:lx521_coupon_1_fit_plate | no_floor_stand | coupon1 | lx521_coupon_1_fit_plate | front_face_down | 1 | coupon1_v1_upper_base | 1 | 6.6 | 6.60 | 6.76 | 6.76 | 0.1999999999999993 | 0.35999999999999943 | [0.0,0.0,-1.0] | insert vertically downward from above the paused part (+Z side) through the open loading chimney along print -Z | /Users/antor/gh/lx/top_baffle_v2/build/no_floor_stand/stl/lx521_coupon_1_fit_plate.stl | 88ec70cfeaf03b854e8271aaac5d0646c24efbdba8d6f374fad12a644df425a3 | /Users/antor/gh/lx/top_baffle_v2/review/captive_magnet_slice_audit/slices/no_floor_stand_coupon1_lx521_coupon_1_fit_plate/ready/plate_1.gcode | 4b4de9860fb3bdde82bbe670bd9f668554a857d309adb62591176acfd12a0e3f | /Users/antor/gh/lx/top_baffle_v2/review/captive_magnet_slice_audit/slices/no_floor_stand_coupon1_lx521_coupon_1_fit_plate/ready/ready_to_print.gcode.3mf | 48097c9ed4e0ef31a26ce0b24584c5037c378635663958fbc07b3a557e88ccf6 | True | 3647ac1acbecafa5b10486b20ce8cb53cf2f4d75b0d2359af75b38dfcc8a81d6 | /Users/antor/gh/lx/top_baffle_v2/review/captive_magnet_slice_audit/slices/no_floor_stand_coupon1_lx521_coupon_1_fit_plate/plate_1.gcode | 9585cef398791041497e4d732334091754630af9182d8ea4b6995945fe97ecdb | /Users/antor/gh/lx/top_baffle_v2/review/captive_magnet_slice_audit/slices/no_floor_stand_coupon1_lx521_coupon_1_fit_plate/audited_slice_project.3mf | b1b262bbcce7f2911b14d01db5bf15a68d7407a258966e9490e4ebf490b8f1f5 | 0.0 | [{"site":"coupon1_v1_upper_base","print_marked_pole_axis_xyz":[0.0,1.0,0.0],"installed_marked_pole_axis_xyz":[0.0,-1.0,0.0],"instruction":"unpaired coupon1 regression station: marked/N pole points along installed -Y (print +Y under its X180/Z0 transform); there is no mating magnet and no attraction claim"}]
shared:Obi-Wan-Flat:obiwan_wing_flat_left_split2_1_of_2_lm_lower | shared | Obi-Wan-Flat | obiwan_wing_flat_left_split2_1_of_2_lm_lower | front_face_down | 1 | lm_lower_left | 1 | 5.8 | 5.80 | 5.96 | 5.96 | 0.10000000000000941 | 0.26000000000000956 | [0.0,0.0,-1.0] | insert vertically downward from above the paused part (+Z side) through the open loading chimney along print -Z | /Users/antor/gh/lx/top_baffle_v2/build/wings/flat/stl/obiwan_wing_flat_left_split2_1_of_2_lm_lower.stl | 6a810e136c585d3419011ae003ff4445b09fa76a2b6eaa912f0850ff50eb1d3a | /Users/antor/gh/lx/top_baffle_v2/review/captive_magnet_slice_audit/slices/shared_Obi-Wan-Flat_obiwan_wing_flat_left_split2_1_of_2_lm_lower/ready/plate_1.gcode | f006defe7df07dc367bf04c80516a55fafe3fc5d477894043f03139ef94c9a2c | /Users/antor/gh/lx/top_baffle_v2/review/captive_magnet_slice_audit/slices/shared_Obi-Wan-Flat_obiwan_wing_flat_left_split2_1_of_2_lm_lower/ready/ready_to_print.gcode.3mf | 2741cbe595d0d0a580db48503d35a2403f307c38b53abaf2d0190f411fb21b8f | True | 8d0c142dcf4f62a5eb2e9d124725dc896c1cef4a5eec5d7886ffa3b88e98fee5 | /Users/antor/gh/lx/top_baffle_v2/review/captive_magnet_slice_audit/slices/shared_Obi-Wan-Flat_obiwan_wing_flat_left_split2_1_of_2_lm_lower/plate_1.gcode | 5e17e5f0c8dc1fbbbdc702a44a4c6f43df26f4e09e741341a1bcfafceed7c50c | /Users/antor/gh/lx/top_baffle_v2/review/captive_magnet_slice_audit/slices/shared_Obi-Wan-Flat_obiwan_wing_flat_left_split2_1_of_2_lm_lower/audited_slice_project.3mf | 8ffe973bfd200c8be36171a82c340f59f0176d75bacac802aadc00b66292af4b | 0.0 | [{"site":"lm_lower_left","print_marked_pole_axis_xyz":[-0.9806556088468728,0.19574109644417936,0.0],"installed_marked_pole_axis_xyz":[-0.7064513012709772,-0.7077616540421945,0.0],"instruction":"marked/N pole points along the same installed pair-axis vector as the carrier magnet; the face toward the carrier is therefore the opposite pole"}]
shared:Obi-Wan-Flat:obiwan_wing_flat_left_split2_2_of_2_lm_um_upper | shared | Obi-Wan-Flat | obiwan_wing_flat_left_split2_2_of_2_lm_um_upper | front_face_down | 1 | lm_upper_left; um_left | 2 | 5.8 | 5.80 | 5.96 | 5.96 | 0.09999990000002246 | 0.2599999000000226 | [0.0,0.0,-1.0] | insert vertically downward from above the paused part (+Z side) through the open loading chimney along print -Z | /Users/antor/gh/lx/top_baffle_v2/build/wings/flat/stl/obiwan_wing_flat_left_split2_2_of_2_lm_um_upper.stl | c750c0025c0a168f50705ede3a77e84d3954432f56155d29a86d494c6d5cef79 | /Users/antor/gh/lx/top_baffle_v2/review/captive_magnet_slice_audit/slices/shared_Obi-Wan-Flat_obiwan_wing_flat_left_split2_2_of_2_lm_um_upper/ready/plate_1.gcode | 37659fd3d45c3534bf9efc7a0a08321004b5a45835f837ed4cb4fc126857c9f6 | /Users/antor/gh/lx/top_baffle_v2/review/captive_magnet_slice_audit/slices/shared_Obi-Wan-Flat_obiwan_wing_flat_left_split2_2_of_2_lm_um_upper/ready/ready_to_print.gcode.3mf | 516fc300cbaa8feb04de6d1ce17c2cd5190ac9222ef4bcc38d5710ce50a9e002 | True | d057b19d1e2f3d1d00ffb4077fa369dba46e80ade734bac5d1b2d9bbced41796 | /Users/antor/gh/lx/top_baffle_v2/review/captive_magnet_slice_audit/slices/shared_Obi-Wan-Flat_obiwan_wing_flat_left_split2_2_of_2_lm_um_upper/plate_1.gcode | e48918985c62ee6dc5c9afc940211e90267281ca017ac15b236fd720cd1571be | /Users/antor/gh/lx/top_baffle_v2/review/captive_magnet_slice_audit/slices/shared_Obi-Wan-Flat_obiwan_wing_flat_left_split2_2_of_2_lm_um_upper/audited_slice_project.3mf | 11dc755751101c84847be4e12dd286f11d4d7e6f095722b431446ebd70cb8858 | 0.0 | [{"site":"lm_upper_left","print_marked_pole_axis_xyz":[0.9999143275740072,0.013089595571344037,0.0],"installed_marked_pole_axis_xyz":[-0.4383711467890776,0.8987940462991671,0.0],"instruction":"marked/N pole points along the same installed pair-axis vector as the carrier magnet; the face toward the carrier is therefore the opposite pole"},{"site":"um_left","print_marked_pole_axis_xyz":[0.9753423205085127,-0.22069743502150146,0.0],"installed_marked_pole_axis_xyz":[-0.6360782202777641,0.7716245833877199,0.0],"instruction":"marked/N pole points along the same installed pair-axis vector as the carrier magnet; the face toward the carrier is therefore the opposite pole"}]
shared:Obi-Wan-Flat:obiwan_wing_flat_right_split2_1_of_2_lm_lower | shared | Obi-Wan-Flat | obiwan_wing_flat_right_split2_1_of_2_lm_lower | front_face_down | 1 | lm_lower_right | 1 | 5.8 | 5.80 | 5.96 | 5.96 | 0.10000000000000941 | 0.26000000000000956 | [0.0,0.0,-1.0] | insert vertically downward from above the paused part (+Z side) through the open loading chimney along print -Z | /Users/antor/gh/lx/top_baffle_v2/build/wings/flat/stl/obiwan_wing_flat_right_split2_1_of_2_lm_lower.stl | d2c17b218d7c5a2898e334d0edfc0d54c6a15c8f73c4850585661a977ac522d8 | /Users/antor/gh/lx/top_baffle_v2/review/captive_magnet_slice_audit/slices/shared_Obi-Wan-Flat_obiwan_wing_flat_right_split2_1_of_2_lm_lower/ready/plate_1.gcode | 796a7128d623b42b76dd9a1aaa62a6dbcffd6c9d0231a1099e558ac2698dd82a | /Users/antor/gh/lx/top_baffle_v2/review/captive_magnet_slice_audit/slices/shared_Obi-Wan-Flat_obiwan_wing_flat_right_split2_1_of_2_lm_lower/ready/ready_to_print.gcode.3mf | 8f0ba3abaa815c311e01bc0a7fdbcbf07aa3fedf418183b6e1f2fe3eaa2149fa | True | fd6d649433d7a6da0a17476af63ca69ab2799ea2ae3e9145f547ef5501581407 | /Users/antor/gh/lx/top_baffle_v2/review/captive_magnet_slice_audit/slices/shared_Obi-Wan-Flat_obiwan_wing_flat_right_split2_1_of_2_lm_lower/plate_1.gcode | 893de125cdda6fc2b6f5fa91eea8539b8d07136ebb0bcda40966beddebd8a4df | /Users/antor/gh/lx/top_baffle_v2/review/captive_magnet_slice_audit/slices/shared_Obi-Wan-Flat_obiwan_wing_flat_right_split2_1_of_2_lm_lower/audited_slice_project.3mf | 3a12148151ecb89d7e93a08bc96ad19ff5a1bf4fc01c642b0227509280c6f881 | 0.0 | [{"site":"lm_lower_right","print_marked_pole_axis_xyz":[-0.19574109644417936,0.9806556088468728,0.0],"installed_marked_pole_axis_xyz":[0.7064513012709772,-0.7077616540421945,0.0],"instruction":"marked/N pole points along the same installed pair-axis vector as the carrier magnet; the face toward the carrier is therefore the opposite pole"}]
shared:Obi-Wan-Flat:obiwan_wing_flat_right_split2_2_of_2_lm_um_upper | shared | Obi-Wan-Flat | obiwan_wing_flat_right_split2_2_of_2_lm_um_upper | front_face_down | 1 | lm_upper_right; um_right | 2 | 5.8 | 5.80 | 5.96 | 5.96 | 0.09999990000002246 | 0.2599999000000226 | [0.0,0.0,-1.0] | insert vertically downward from above the paused part (+Z side) through the open loading chimney along print -Z | /Users/antor/gh/lx/top_baffle_v2/build/wings/flat/stl/obiwan_wing_flat_right_split2_2_of_2_lm_um_upper.stl | 8be9c65c59b2a961419d2af159bd585c20e49ded7b1a266ae8070b4ec3fa1ae5 | /Users/antor/gh/lx/top_baffle_v2/review/captive_magnet_slice_audit/slices/shared_Obi-Wan-Flat_obiwan_wing_flat_right_split2_2_of_2_lm_um_upper/ready/plate_1.gcode | 84b84aa8b746d78dca2ba82dd69dc0f1b36ff182fa33ad060bcf448daf37324e | /Users/antor/gh/lx/top_baffle_v2/review/captive_magnet_slice_audit/slices/shared_Obi-Wan-Flat_obiwan_wing_flat_right_split2_2_of_2_lm_um_upper/ready/ready_to_print.gcode.3mf | df34793fddaec5ffb4d84af7dbb9b5f54db68cff22293e778dec79a1188a8a51 | True | efe5dfbe9f7d3e2232f773bf1f8aeb82a686159efbf19e331ec2732277c78b3d | /Users/antor/gh/lx/top_baffle_v2/review/captive_magnet_slice_audit/slices/shared_Obi-Wan-Flat_obiwan_wing_flat_right_split2_2_of_2_lm_um_upper/plate_1.gcode | 86a719b8940d98a45a27dbfd8e0ad24f96ea7d277933c41ec268c57132298057 | /Users/antor/gh/lx/top_baffle_v2/review/captive_magnet_slice_audit/slices/shared_Obi-Wan-Flat_obiwan_wing_flat_right_split2_2_of_2_lm_um_upper/audited_slice_project.3mf | 8e980a99a7d0a707708f4b85ea523d1ea3e87a70ea4c3a8c85bb9404a846ad6d | 0.0 | [{"site":"lm_upper_right","print_marked_pole_axis_xyz":[0.999914327574007,-0.013089595571344537,0.0],"installed_marked_pole_axis_xyz":[0.43837114678907746,0.898794046299167,0.0],"instruction":"marked/N pole points along the same installed pair-axis vector as the carrier magnet; the face toward the carrier is therefore the opposite pole"},{"site":"um_right","print_marked_pole_axis_xyz":[0.9753423205085128,0.22069743502150102,0.0],"installed_marked_pole_axis_xyz":[0.636078220277764,0.77162458338772,0.0],"instruction":"marked/N pole points along the same installed pair-axis vector as the carrier magnet; the face toward the carrier is therefore the opposite pole"}]
shared:Obi-Wan-Graded:obiwan_wing_graded_left_split2_1_of_2_lm_lower | shared | Obi-Wan-Graded | obiwan_wing_graded_left_split2_1_of_2_lm_lower | front_face_down | 1 | lm_lower_left | 1 | 5.8 | 5.80 | 5.96 | 5.96 | 0.09999990000000825 | 0.2599999000000084 | [0.0,0.0,-1.0] | insert vertically downward from above the paused part (+Z side) through the open loading chimney along print -Z | /Users/antor/gh/lx/top_baffle_v2/build/wings/graded/stl/obiwan_wing_graded_left_split2_1_of_2_lm_lower.stl | bb82846c5a0581c4eab2b7e84750b67c6d12be3abf59d5ced1d727ac80e4bb4b | /Users/antor/gh/lx/top_baffle_v2/review/captive_magnet_slice_audit/slices/shared_Obi-Wan-Graded_obiwan_wing_graded_left_split2_1_of_2_lm_lower/ready/plate_1.gcode | 1187b12f356234ba72513e42d5093b62eb700e71d5bc7baeabb618299754d4ad | /Users/antor/gh/lx/top_baffle_v2/review/captive_magnet_slice_audit/slices/shared_Obi-Wan-Graded_obiwan_wing_graded_left_split2_1_of_2_lm_lower/ready/ready_to_print.gcode.3mf | bdc34fbb0edfaf26f2c134eedae750326b8bd9e0b797680898710d4d8d0089e1 | True | fe5b0f1aabcdab953278743f78b5d21bc928e6df9b00c24e60d9ebb7be2414f2 | /Users/antor/gh/lx/top_baffle_v2/review/captive_magnet_slice_audit/slices/shared_Obi-Wan-Graded_obiwan_wing_graded_left_split2_1_of_2_lm_lower/plate_1.gcode | 3c20187d562213935fa3e7717897017717c1d964699a8f03093d23242431491d | /Users/antor/gh/lx/top_baffle_v2/review/captive_magnet_slice_audit/slices/shared_Obi-Wan-Graded_obiwan_wing_graded_left_split2_1_of_2_lm_lower/audited_slice_project.3mf | d0b41ed903d54e01117a486932c57d2f7d9000ae45c348cc4e21174b94d61844 | 0.0 | [{"site":"lm_lower_left","print_marked_pole_axis_xyz":[-0.9806556088468728,0.19574109644417936,0.0],"installed_marked_pole_axis_xyz":[-0.7064513012709772,-0.7077616540421945,0.0],"instruction":"marked/N pole points along the same installed pair-axis vector as the carrier magnet; the face toward the carrier is therefore the opposite pole"}]
shared:Obi-Wan-Graded:obiwan_wing_graded_left_split2_2_of_2_lm_um_upper | shared | Obi-Wan-Graded | obiwan_wing_graded_left_split2_2_of_2_lm_um_upper | front_face_down | 1 | lm_upper_left; um_left | 2 | 5.8 | 5.80 | 5.96 | 5.96 | 0.09999990000002246 | 0.2599999000000226 | [0.0,0.0,-1.0] | insert vertically downward from above the paused part (+Z side) through the open loading chimney along print -Z | /Users/antor/gh/lx/top_baffle_v2/build/wings/graded/stl/obiwan_wing_graded_left_split2_2_of_2_lm_um_upper.stl | fa15e5f241e426367f4c85aba41c417f5cf037c3cd152956cb67bba51b77cac5 | /Users/antor/gh/lx/top_baffle_v2/review/captive_magnet_slice_audit/slices/shared_Obi-Wan-Graded_obiwan_wing_graded_left_split2_2_of_2_lm_um_upper/ready/plate_1.gcode | cb6e6cdf78e74324b0f601d43e45b4470ca580da11c2a463a332906aa3cdd74c | /Users/antor/gh/lx/top_baffle_v2/review/captive_magnet_slice_audit/slices/shared_Obi-Wan-Graded_obiwan_wing_graded_left_split2_2_of_2_lm_um_upper/ready/ready_to_print.gcode.3mf | dc8fc4b7154f02915e7d481d6a7c2dad1c66cb2ad743123640f5f5be1ce905c7 | True | 3edc7f0b1a887193113f88b75edd7e22f33ba96d27546dae4c667c0d28115c2e | /Users/antor/gh/lx/top_baffle_v2/review/captive_magnet_slice_audit/slices/shared_Obi-Wan-Graded_obiwan_wing_graded_left_split2_2_of_2_lm_um_upper/plate_1.gcode | e25607f2a73699d3c7118bdf63a93dc0fe96c284b6fc7528cd28cea4ffdcde85 | /Users/antor/gh/lx/top_baffle_v2/review/captive_magnet_slice_audit/slices/shared_Obi-Wan-Graded_obiwan_wing_graded_left_split2_2_of_2_lm_um_upper/audited_slice_project.3mf | 0aa11e9672a1bf29f3f4e2d4946ab116d4a897ed4235b0d4c0bbbeb19fe1516e | 0.0 | [{"site":"lm_upper_left","print_marked_pole_axis_xyz":[0.013089595571344259,-0.9999143275740072,0.0],"installed_marked_pole_axis_xyz":[-0.4383711467890776,0.8987940462991671,0.0],"instruction":"marked/N pole points along the same installed pair-axis vector as the carrier magnet; the face toward the carrier is therefore the opposite pole"},{"site":"um_left","print_marked_pole_axis_xyz":[-0.22069743502150124,-0.9753423205085127,0.0],"installed_marked_pole_axis_xyz":[-0.6360782202777641,0.7716245833877199,0.0],"instruction":"marked/N pole points along the same installed pair-axis vector as the carrier magnet; the face toward the carrier is therefore the opposite pole"}]
shared:Obi-Wan-Graded:obiwan_wing_graded_right_split2_1_of_2_lm_lower | shared | Obi-Wan-Graded | obiwan_wing_graded_right_split2_1_of_2_lm_lower | front_face_down | 1 | lm_lower_right | 1 | 5.8 | 5.80 | 5.96 | 5.96 | 0.09999990000000825 | 0.2599999000000084 | [0.0,0.0,-1.0] | insert vertically downward from above the paused part (+Z side) through the open loading chimney along print -Z | /Users/antor/gh/lx/top_baffle_v2/build/wings/graded/stl/obiwan_wing_graded_right_split2_1_of_2_lm_lower.stl | e94e8cb163407d9e608e1345d9041207bda0b228b190ac8764effdcc4ba750af | /Users/antor/gh/lx/top_baffle_v2/review/captive_magnet_slice_audit/slices/shared_Obi-Wan-Graded_obiwan_wing_graded_right_split2_1_of_2_lm_lower/ready/plate_1.gcode | 8f88da552cbaeedbb1310530c1abce05fd3a707298c93cbe4675168a7e05a3ed | /Users/antor/gh/lx/top_baffle_v2/review/captive_magnet_slice_audit/slices/shared_Obi-Wan-Graded_obiwan_wing_graded_right_split2_1_of_2_lm_lower/ready/ready_to_print.gcode.3mf | afd20999d77c485c08582a847863d0f2190ca9665b4e6f9676b18078a18d53bd | True | 7d9e744de1c71b4a82cfe2d1caab56814df80cd701c1132052781e9129184df7 | /Users/antor/gh/lx/top_baffle_v2/review/captive_magnet_slice_audit/slices/shared_Obi-Wan-Graded_obiwan_wing_graded_right_split2_1_of_2_lm_lower/plate_1.gcode | 72310ba9496dc4c7e3b5ba62db3e6669636a7fb8f52c5d10d4a2e0fa3dac58d6 | /Users/antor/gh/lx/top_baffle_v2/review/captive_magnet_slice_audit/slices/shared_Obi-Wan-Graded_obiwan_wing_graded_right_split2_1_of_2_lm_lower/audited_slice_project.3mf | 59f1f8a4cbc4d4590b916b5918f707cfd19cdef9c1b7eda484936fe1a03f8e6b | 0.0 | [{"site":"lm_lower_right","print_marked_pole_axis_xyz":[-0.19574109644417936,0.9806556088468728,0.0],"installed_marked_pole_axis_xyz":[0.7064513012709772,-0.7077616540421945,0.0],"instruction":"marked/N pole points along the same installed pair-axis vector as the carrier magnet; the face toward the carrier is therefore the opposite pole"}]
shared:Obi-Wan-Graded:obiwan_wing_graded_right_split2_2_of_2_lm_um_upper | shared | Obi-Wan-Graded | obiwan_wing_graded_right_split2_2_of_2_lm_um_upper | front_face_down | 1 | lm_upper_right; um_right | 2 | 5.8 | 5.80 | 5.96 | 5.96 | 0.09999990000002246 | 0.2599999000000226 | [0.0,0.0,-1.0] | insert vertically downward from above the paused part (+Z side) through the open loading chimney along print -Z | /Users/antor/gh/lx/top_baffle_v2/build/wings/graded/stl/obiwan_wing_graded_right_split2_2_of_2_lm_um_upper.stl | cd1c013a5d78a0478261d8665b91cd44e7bbd098b1e45f35a77d36994507fd60 | /Users/antor/gh/lx/top_baffle_v2/review/captive_magnet_slice_audit/slices/shared_Obi-Wan-Graded_obiwan_wing_graded_right_split2_2_of_2_lm_um_upper/ready/plate_1.gcode | eab1c7c54aa167805356dfaaae845f7241c297d1b08cd9d4a37bdc24e6796b5a | /Users/antor/gh/lx/top_baffle_v2/review/captive_magnet_slice_audit/slices/shared_Obi-Wan-Graded_obiwan_wing_graded_right_split2_2_of_2_lm_um_upper/ready/ready_to_print.gcode.3mf | 4f8d6cc6f98e3ba3ae2ddb599a0222a3b18fa810b1aab05eca4527d9099aa467 | True | 9b999a39968ca92c4655f4bc7e2d39e9d3dd7dcd735bc324bd7dc326f913eca3 | /Users/antor/gh/lx/top_baffle_v2/review/captive_magnet_slice_audit/slices/shared_Obi-Wan-Graded_obiwan_wing_graded_right_split2_2_of_2_lm_um_upper/plate_1.gcode | 1f41484b5607249d5966fa0e93bb35bf0ee07e95ab52b146ad9568b6bd0adf9f | /Users/antor/gh/lx/top_baffle_v2/review/captive_magnet_slice_audit/slices/shared_Obi-Wan-Graded_obiwan_wing_graded_right_split2_2_of_2_lm_um_upper/audited_slice_project.3mf | 7df025e121b4db885dca57ce9a6c4b005f107d43bcf2ed3c8ad042edc0a19e8c | 0.0 | [{"site":"lm_upper_right","print_marked_pole_axis_xyz":[0.999914327574007,-0.013089595571344537,0.0],"installed_marked_pole_axis_xyz":[0.43837114678907746,0.898794046299167,0.0],"instruction":"marked/N pole points along the same installed pair-axis vector as the carrier magnet; the face toward the carrier is therefore the opposite pole"},{"site":"um_right","print_marked_pole_axis_xyz":[0.9753423205085128,0.22069743502150102,0.0],"installed_marked_pole_axis_xyz":[0.636078220277764,0.77162458338772,0.0],"instruction":"marked/N pole points along the same installed pair-axis vector as the carrier magnet; the face toward the carrier is therefore the opposite pole"}]
