antorsae/lx/top_baffle_v2/build/bmr_crescent_TEBM35C10-4/obiwan_bmr_crescent_opposed_TEBM35C10-4.gcode.3mf

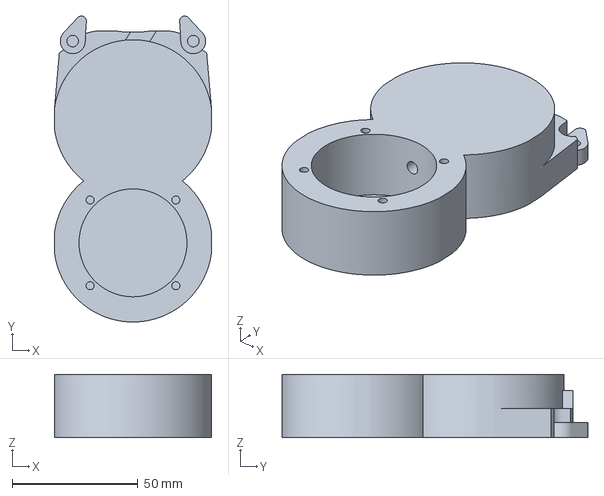
[picture p138: CAD file, 2026-08-13]
top_baffle_v2/build/bmr_crescent_TEBM35C10-4/obiwan_bmr_crescent_opposed_TEBM35C10-4.gcode.3mf
62.7 x 121.8 x 25.1 mm
