antorsae/lx/top_baffle_v2/build/bmr_slim_TEBM35C10-4/obiwan_bmr_slim_crescent_opposed_TEBM35C10-4.step

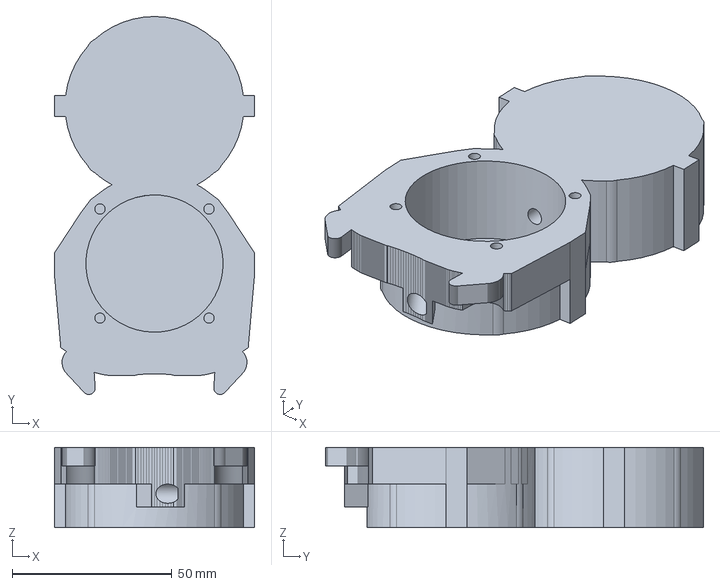
[picture p139: CAD file, 2026-08-15]
top_baffle_v2/build/bmr_slim_TEBM35C10-4/obiwan_bmr_slim_crescent_opposed_TEBM35C10-4.step
62.7 x 118.3 x 25.1 mm
