antorsae/lx/top_baffle_v2/build/bmr_slim_TEBM35C10-4/proud/stock/vase_TEBM35C10-4.step

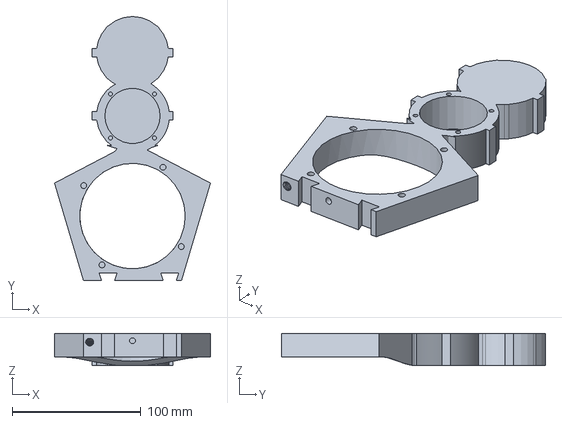
[picture p141: CAD file, 2026-08-15]
top_baffle_v2/build/bmr_slim_TEBM35C10-4/proud/stock/vase_TEBM35C10-4.step
121.3 x 205.2 x 25.1 mm
