antorsae/lx/top_baffle_v2/build/common/attachments.step

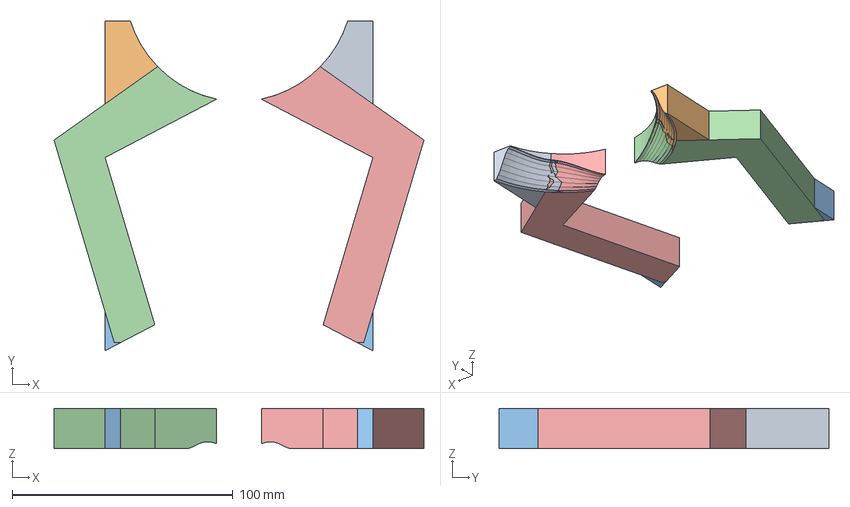
[picture p142: CAD file, 2026-08-09]
top_baffle_v2/build/common/attachments.step
167.6 x 149.3 x 18.3 mm
attach_a_shoulder_top_right
attach_a_shoulder_top_left
attach_a_shoulder_bottom_left
attach_a_shoulder_bottom_right
attach_b1_wing_left
attach_b1_wing_right
