antorsae/lx/top_baffle_v2/build/floor_stand/stl/obiwan_core_2_of_2_um_carrier.stl

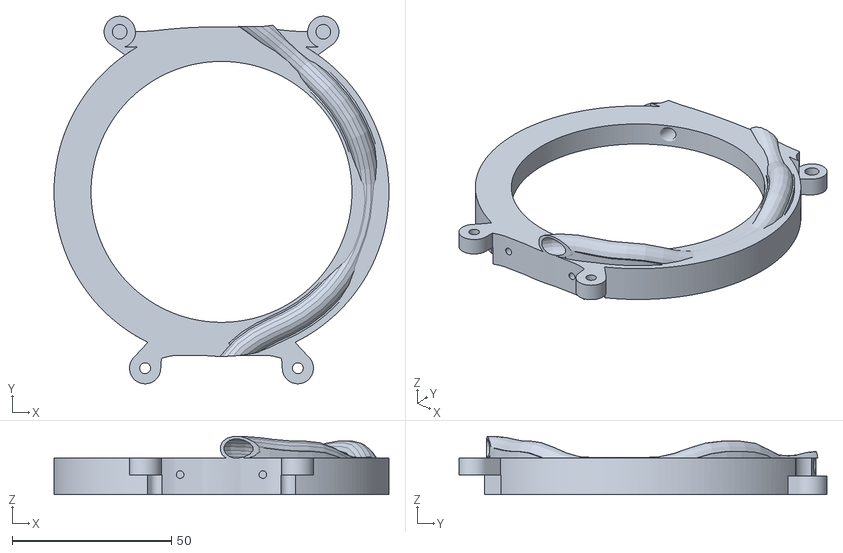
[picture p143: CAD file, 2026-09-15]
top_baffle_v2/build/floor_stand/stl/obiwan_core_2_of_2_um_carrier.stl
105.3 x 115.5 x 18.3
