antorsae/lx/top_baffle_v2/build/floor_stand/support_blockers/obiwan_core_2_of_2_um_carrier.support_blocker.stl

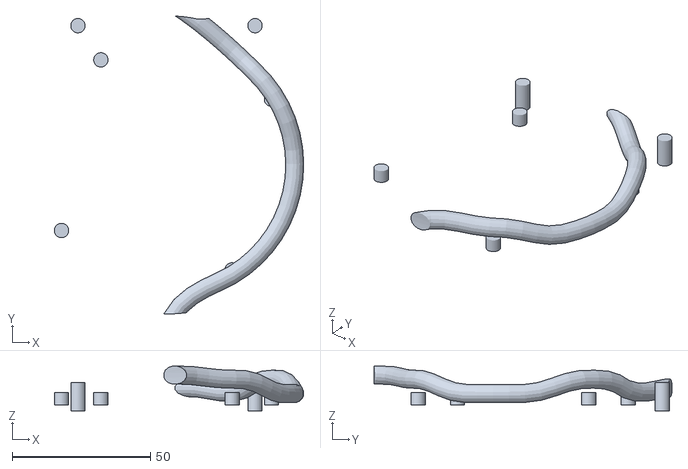
[picture p144: CAD file, 2026-09-15]
top_baffle_v2/build/floor_stand/support_blockers/obiwan_core_2_of_2_um_carrier.support_blocker.stl
90.1 x 107.7 x 16.1
