antorsae/lx/top_baffle_v2/build/floor_stand/v1_attachments.step

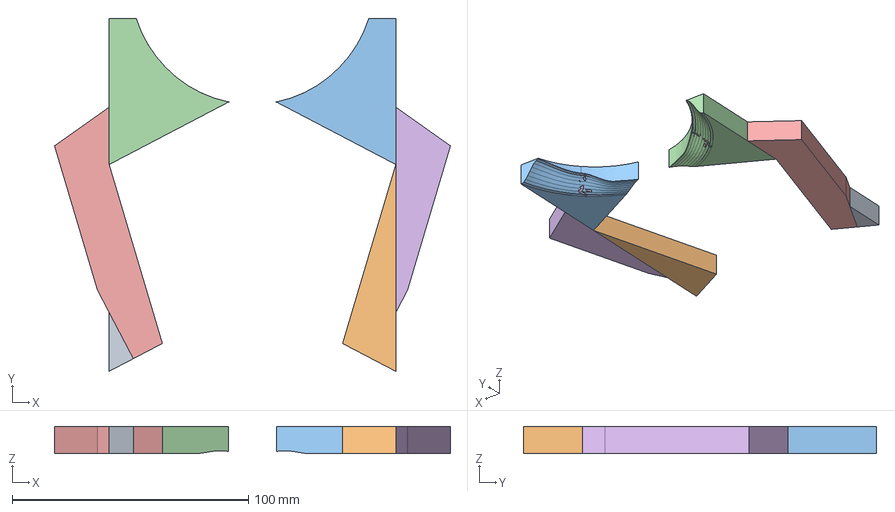
[picture p145: CAD file, 2026-08-18]
top_baffle_v2/build/floor_stand/v1_attachments.step
167.6 x 149.3 x 11.5 mm
attach_v1a_shoulder_bottom_left
attach_v1a_shoulder_bottom_right
attach_v1a_shoulder_top_right
attach_v1a_shoulder_top_left
attach_v1b1_wing_left
attach_v1b1_wing_right
