antorsae/lx/top_baffle_v2/build/h2c/inputs/h2c_dayton_nd25fn4_wing_graded_right_support_blocker.stl

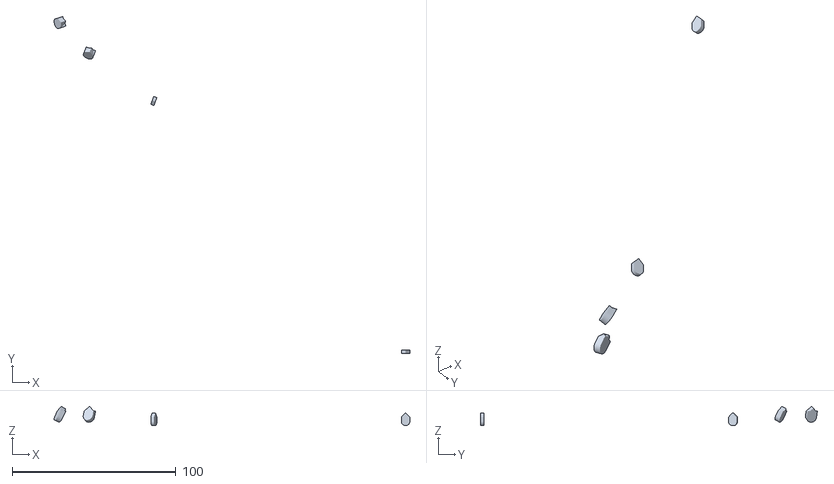
[picture p146: CAD file, 2026-09-15]
top_baffle_v2/build/h2c/inputs/h2c_dayton_nd25fn4_wing_graded_right_support_blocker.stl
217.1 x 205.7 x 11.8
