antorsae/lx/top_baffle_v2/build/h2c/review_models/stock_floor_stand.step

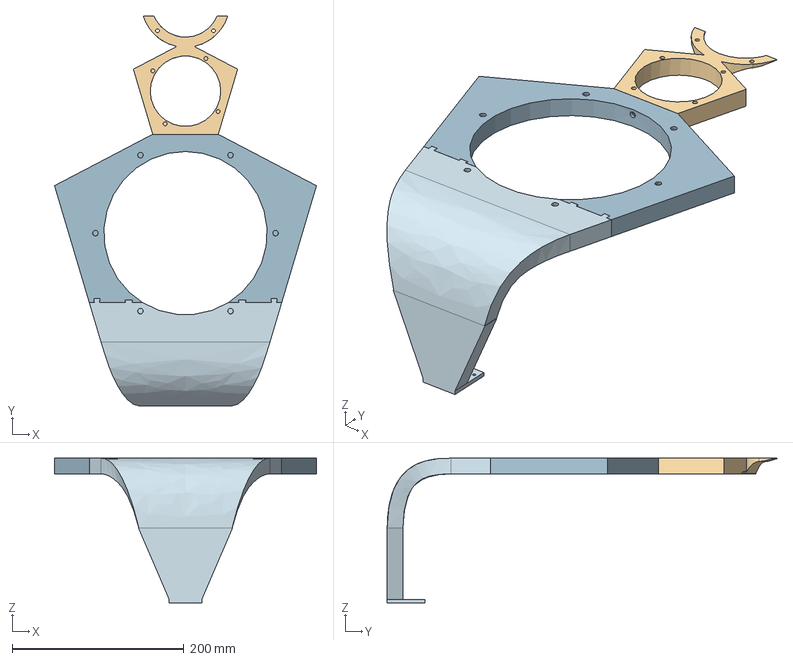
[picture p147: CAD file, 2026-09-15]
top_baffle_v2/build/h2c/review_models/stock_floor_stand.step
304.8 x 453.5 x 168.3 mm
stock_lm_lower_floor_stand
stock_lm_upper_floor_stand
upper_module
