antorsae/lx/top_baffle_v2/build/h2c/STEP/h2c_obiwan_wing_flat_left.step

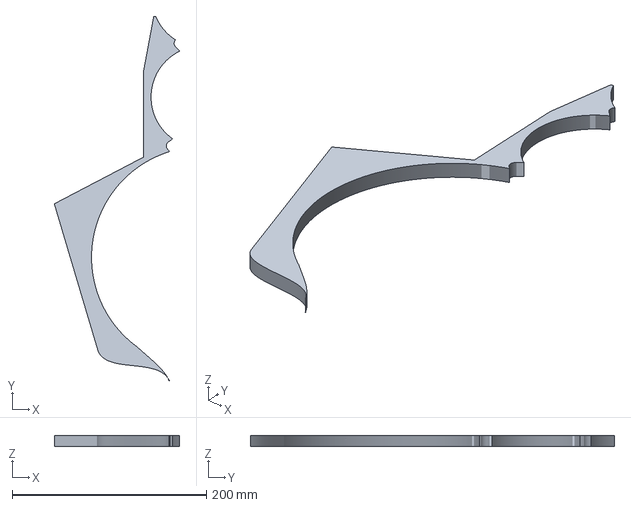
[picture p148: CAD file, 2026-09-15]
top_baffle_v2/build/h2c/STEP/h2c_obiwan_wing_flat_left.step
129.2 x 374.9 x 11.5 mm
