antorsae/lx/top_baffle_v2/build/h2c/STL/h2c_dayton_nd25fn4_wing_graded_right.stl

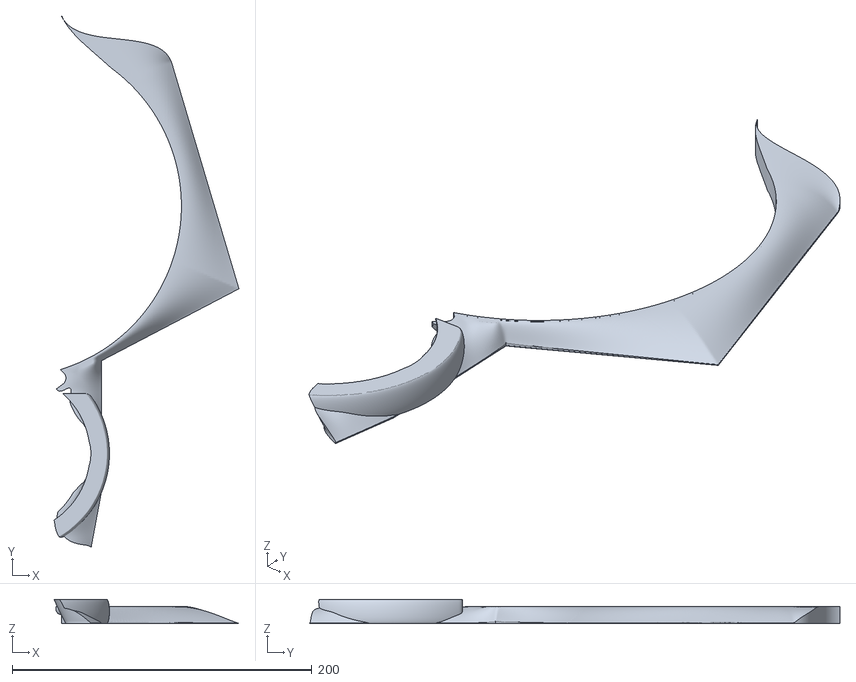
[picture p149: CAD file, 2026-09-15]
top_baffle_v2/build/h2c/STL/h2c_dayton_nd25fn4_wing_graded_right.stl
123.4 x 354.3 x 16.3
