antorsae/lx/top_baffle_v2/build/h2c/support_blockers/h2c_slim_lm_upper_floor_stand.stl

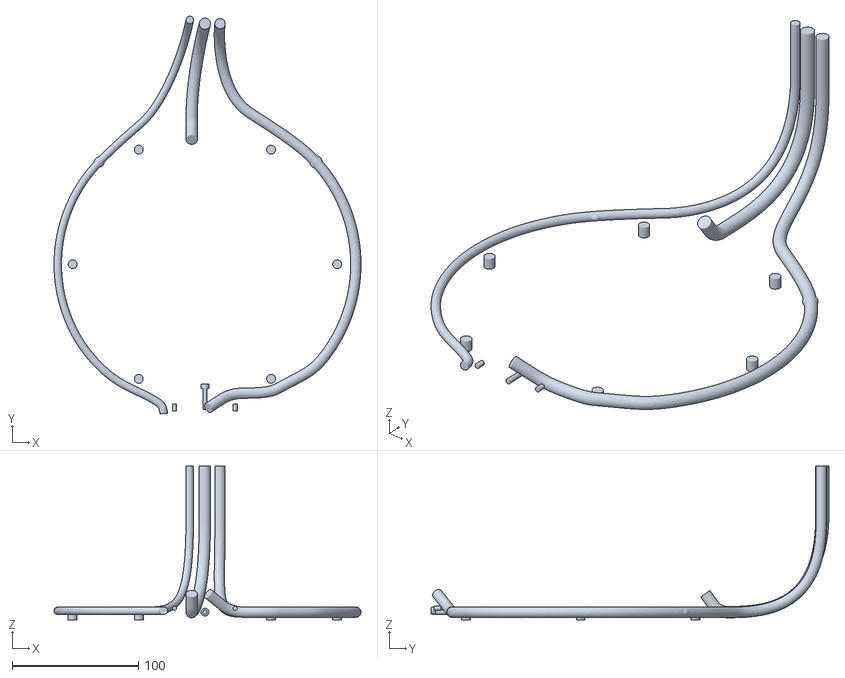
[picture p150: CAD file, 2026-09-15]
top_baffle_v2/build/h2c/support_blockers/h2c_slim_lm_upper_floor_stand.stl
243.1 x 315.0 x 121.6
