antorsae/lx/top_baffle_v2/build/no_floor_stand/obiwan_lm_split.step

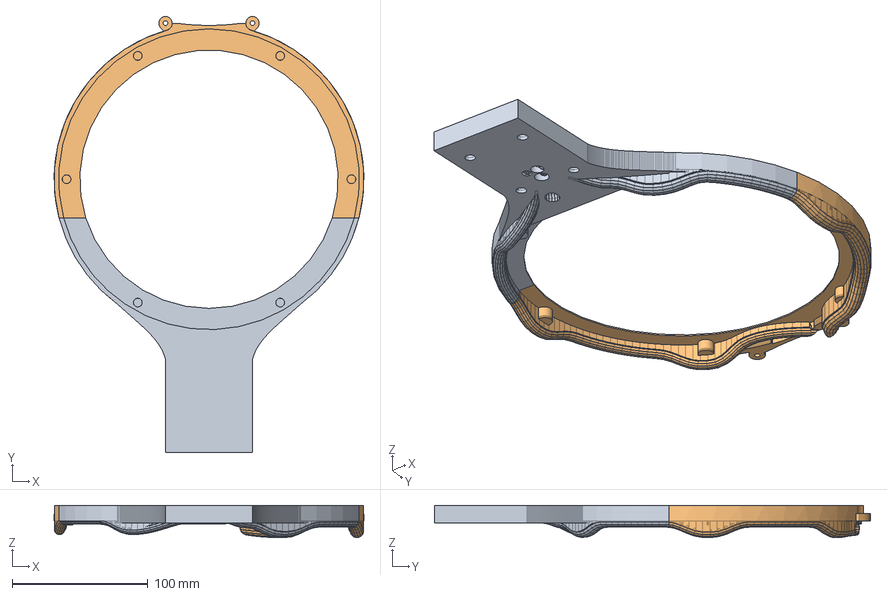
[picture p151: CAD file, 2026-08-20]
top_baffle_v2/build/no_floor_stand/obiwan_lm_split.step
227.8 x 320.7 x 23.6 mm
optional_lm_keyed_1_of_2_bottom
optional_lm_keyed_2_of_2_top
