antorsae/lx/top_baffle_v2/build/print_plates/obiwan/obiwan_01_02_03_04_LM_UM_combo_no_floor_stand.stl

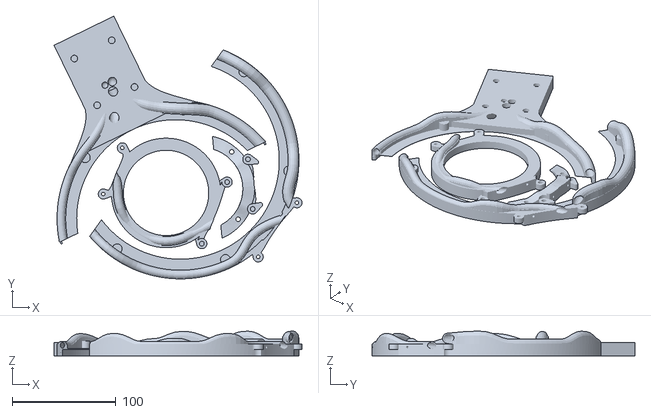
[picture p152: CAD file, 2026-09-15]
top_baffle_v2/build/print_plates/obiwan/obiwan_01_02_03_04_LM_UM_combo_no_floor_stand.stl
238.5 x 252.6 x 23.6
