antorsae/lx/top_baffle_v2/build/vase_TEBM35C10-4/stock/vase_TEBM35C10-4.gcode.3mf

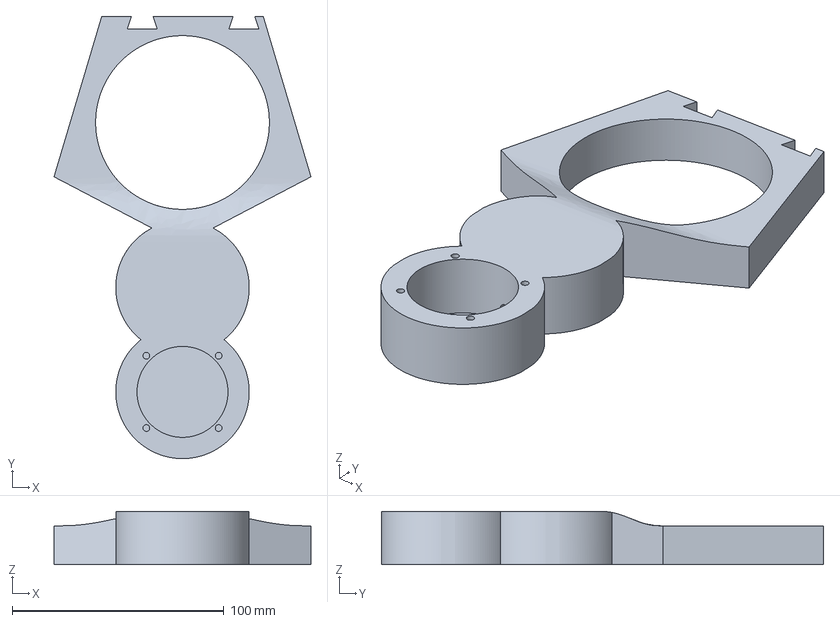
[picture p153: CAD file, 2026-08-13]
top_baffle_v2/build/vase_TEBM35C10-4/stock/vase_TEBM35C10-4.gcode.3mf
121.3 x 208.7 x 25.1 mm
