antorsae/lx/top_baffle_v2/build/wings/ae/stl/lx521_top_obiwan_wing_ae_left_b_1of2_lm_lower.stl

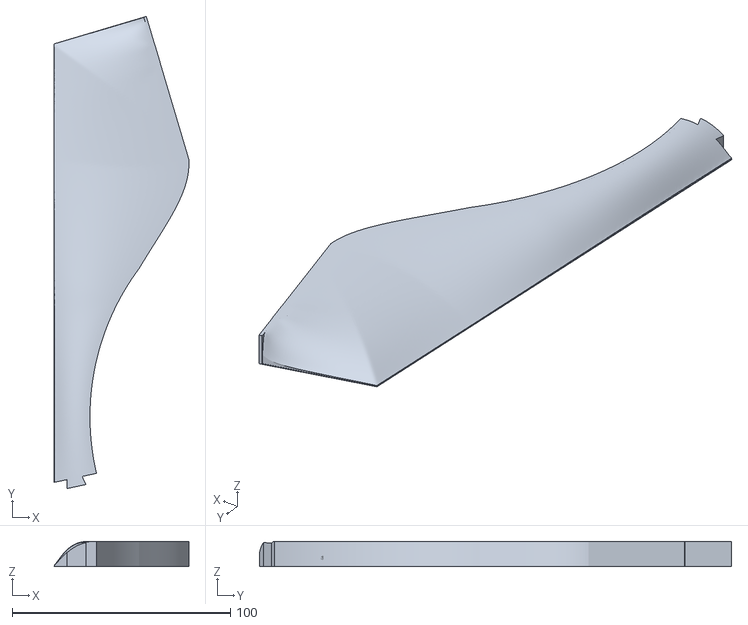
[picture p154: CAD file, 2026-08-09]
top_baffle_v2/build/wings/ae/stl/lx521_top_obiwan_wing_ae_left_b_1of2_lm_lower.stl
61.9 x 216.4 x 11.5
