antorsae/lx/top_baffle_v2/candidates/nd25fn4_crescent/print/geometry/V4_graded_left_UPPER_PRINT.stl

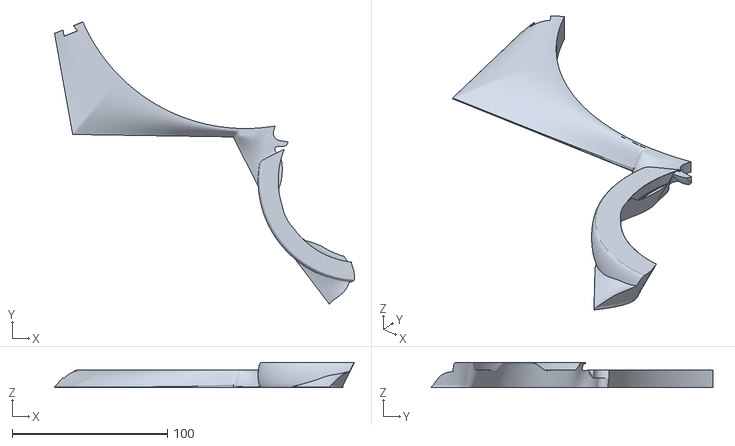
[picture p155: CAD file, 2026-09-15]
top_baffle_v2/candidates/nd25fn4_crescent/print/geometry/V4_graded_left_UPPER_PRINT.stl
193.4 x 182.2 x 16.3
