antorsae/lx/top_baffle_v2/candidates/nd25fn4_crescent/print/qualification/D6_body_wing_fit_06HF_PETG_GF_PLA.gcode.3mf

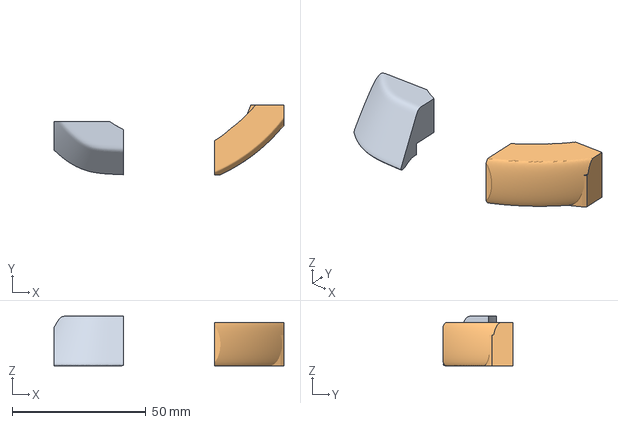
[picture p156: CAD file, 2026-09-15]
top_baffle_v2/candidates/nd25fn4_crescent/print/qualification/D6_body_wing_fit_06HF_PETG_GF_PLA.gcode.3mf
86.0 x 26.0 x 18.7 mm
01_D6_body_coupon
D6_wing_coupon
