antorsae/lx/top_baffle_v2/candidates/nd25fn4_crescent/print/V4_flat_right_UPPER_06HF_PETG_GF_PLA.gcode.3mf

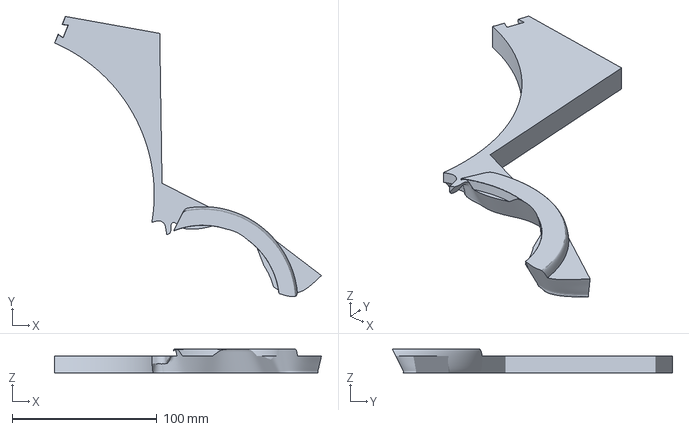
[picture p157: CAD file, 2026-09-15]
top_baffle_v2/candidates/nd25fn4_crescent/print/V4_flat_right_UPPER_06HF_PETG_GF_PLA.gcode.3mf
184.4 x 193.4 x 16.3 mm
