antorsae/lx/top_baffle_v2/candidates/nd25fn4_crescent/print_translucent/qualification/00_Magnet_Surface_Test_06HF_PETG_TRANSLUCENT_PLA_TRANSLUCENT.gcode.3mf

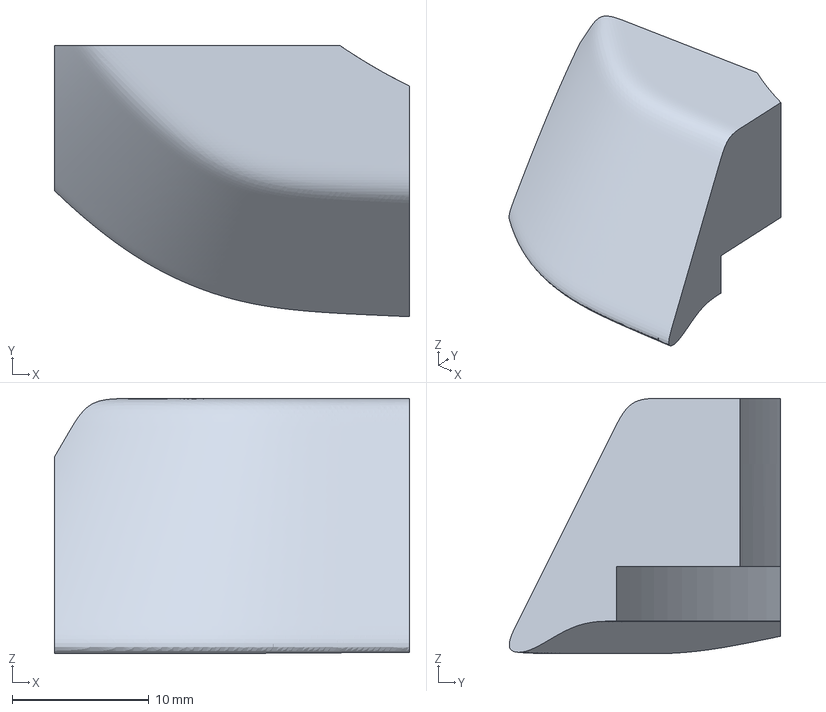
[picture p158: CAD file, 2026-09-15]
top_baffle_v2/candidates/nd25fn4_crescent/print_translucent/qualification/00_Magnet_Surface_Test_06HF_PETG_TRANSLUCENT_PLA_TRANSLUCENT.gcode.3mf
26.0 x 19.9 x 18.7 mm
