antorsae/lx/top_baffle_v2/candidates/nd25fn4_crescent/print_translucent_changeover/02_Caps_TWO_Retainers_TWO_PURGE560_06HF_PETG_TRANSLUCENT_PLA_TRANSLUCENT.gcode.3mf

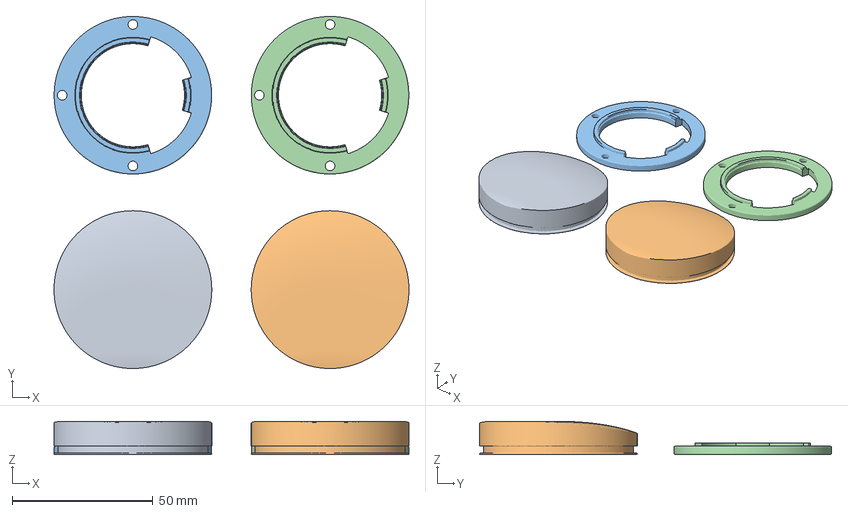
[picture p159: CAD file, 2026-09-15]
top_baffle_v2/candidates/nd25fn4_crescent/print_translucent_changeover/02_Caps_TWO_Retainers_TWO_PURGE560_06HF_PETG_TRANSLUCENT_PLA_TRANSLUCENT.gcode.3mf
126.0 x 125.0 x 11.8 mm
02_Closed_Cap_PRINT_TWO x 2
03_Tweeter_Retainer_PRINT_TWO x 2
