antorsae/lx/top_baffle_v2/coupons/obiwan_ae_embed/lx521_obiwan_ae_embed_coupon_carrier.step

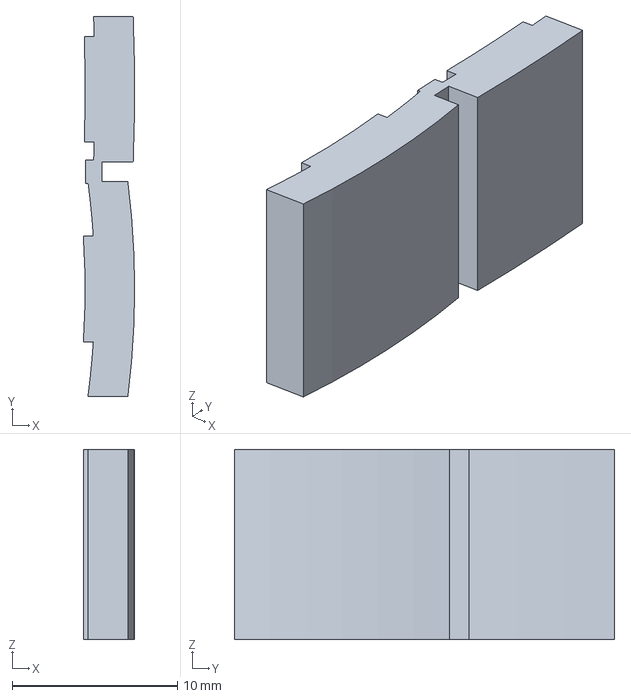
[picture p160: CAD file, 2026-08-09]
top_baffle_v2/coupons/obiwan_ae_embed/lx521_obiwan_ae_embed_coupon_carrier.step
3.11 x 23.0 x 11.5 mm
