antorsae/lx/top_baffle_v2/qualification/female_socket_pair.stl

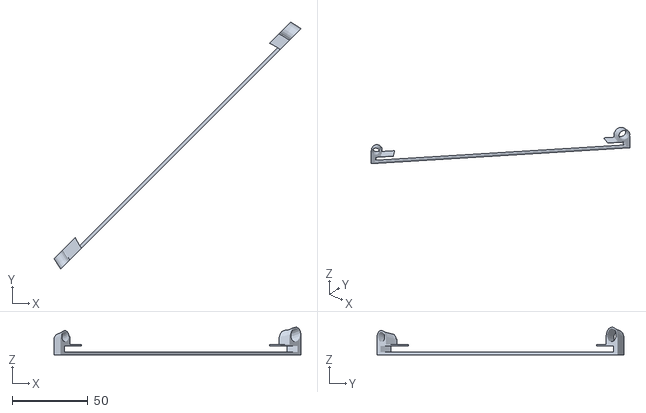
[picture p161: CAD file, 2026-09-15]
top_baffle_v2/qualification/female_socket_pair.stl
162.9 x 162.9 x 18.3
