antorsae/lx/top_baffle_v2/review/bug_reports/bambu_28_crash_repro/model.stl

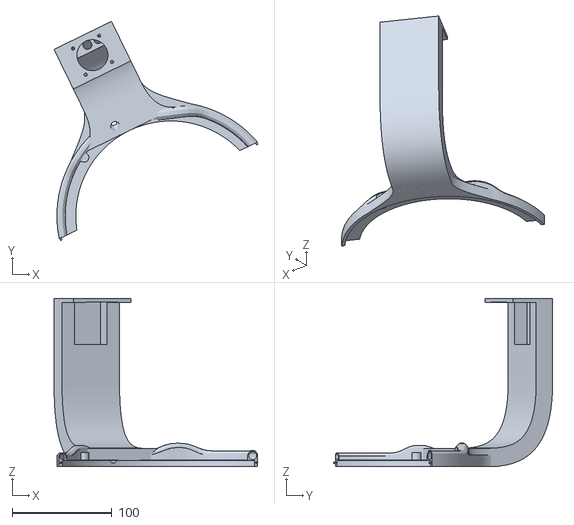
[picture p162: CAD file, 2026-08-13]
top_baffle_v2/review/bug_reports/bambu_28_crash_repro/model.stl
204.0 x 219.3 x 168.3
