antorsae/lx/top_baffle_v2/review/nd25fn4_engineering_guide/pla_basic_supports_petg_hf_P2S.3mf

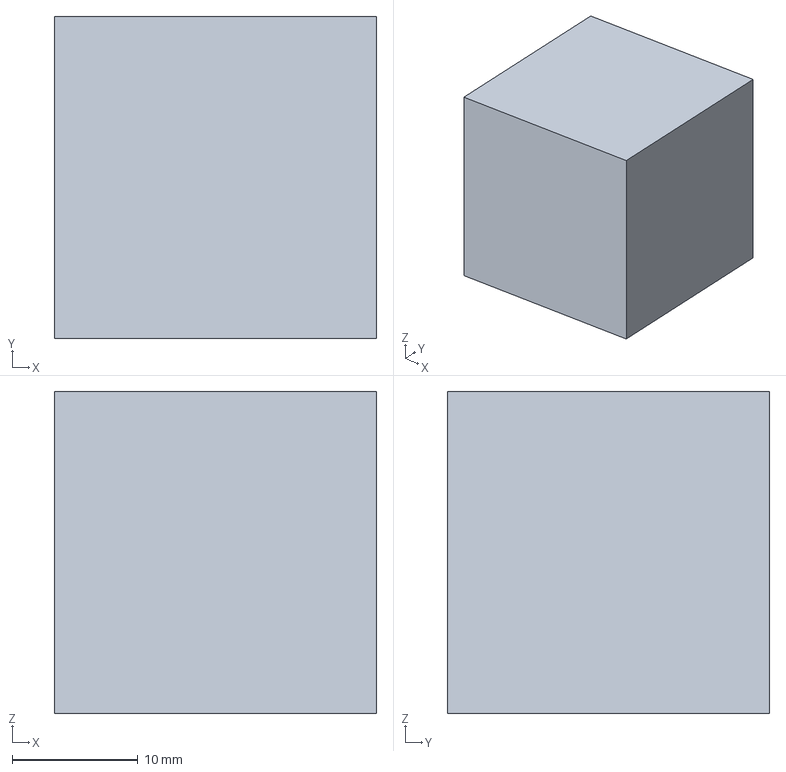
[picture p163: CAD file, 2026-09-15]
top_baffle_v2/review/nd25fn4_engineering_guide/pla_basic_supports_petg_hf_P2S.3mf
25.6 x 25.6 x 25.6 mm
