antorsae/lx/top_baffle_v2/review/nd25fn4_print/D6_coupon/01_D6_body_coupon_blocker.stl

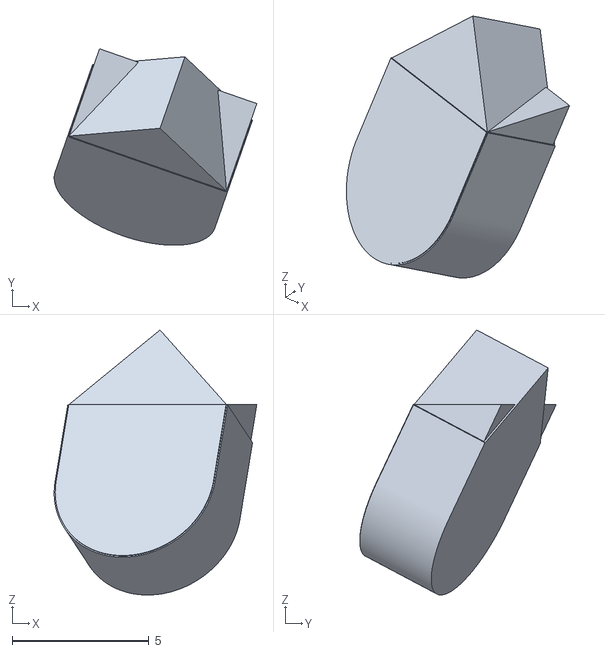
[picture p164: CAD file, 2026-09-15]
top_baffle_v2/review/nd25fn4_print/D6_coupon/01_D6_body_coupon_blocker.stl
7.42 x 7.19 x 9.70
