antorsae/lx/top_baffle_v2/review/nd25fn4_print/inputs/V4_graded_left_UPPER_magnet_blocker.stl

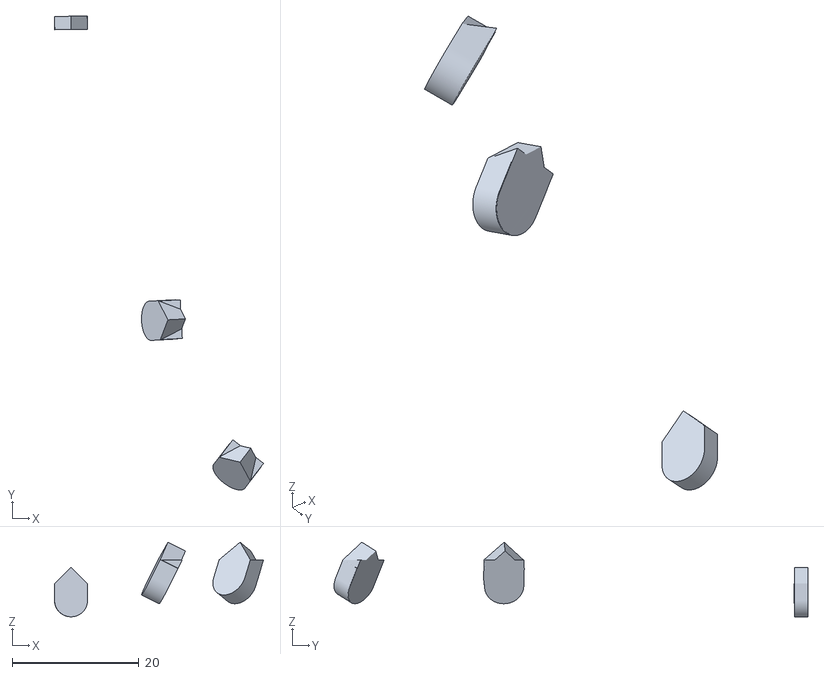
[picture p165: CAD file, 2026-09-15]
top_baffle_v2/review/nd25fn4_print/inputs/V4_graded_left_UPPER_magnet_blocker.stl
33.0 x 74.7 x 11.8
