antorsae/lx/top_baffle_v2/review/part_views/concept/lm_block_magnet_wing_seated.stl

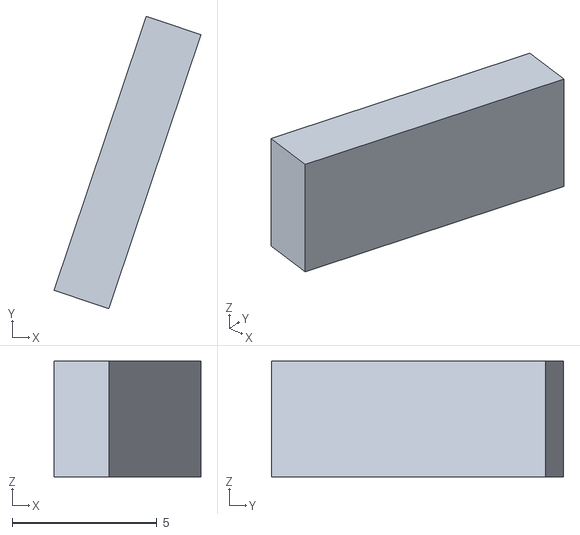
[picture p166: CAD file, 2026-09-15]
top_baffle_v2/review/part_views/concept/lm_block_magnet_wing_seated.stl
5.09 x 10.1 x 4.00
