antorsae/lx/top_baffle_v2/to_print/h2c/dayton_nd25fn4/petg_gf_pla/h2c_dayton_nd25fn4_wing_flat_left.gcode.3mf

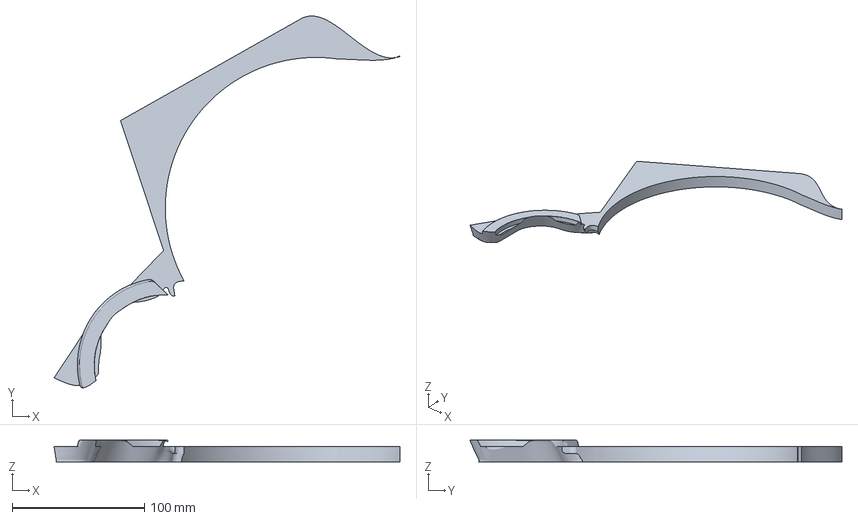
[picture p167: CAD file, 2026-09-15]
top_baffle_v2/to_print/h2c/dayton_nd25fn4/petg_gf_pla/h2c_dayton_nd25fn4_wing_flat_left.gcode.3mf
261.8 x 281.5 x 16.3 mm
