antorsae/lx/top_baffle_v2/to_print/h2c/obiwan/petg_gf_pla/h2c_obiwan_bmr_crescent_TEBM35C10-4.3mf

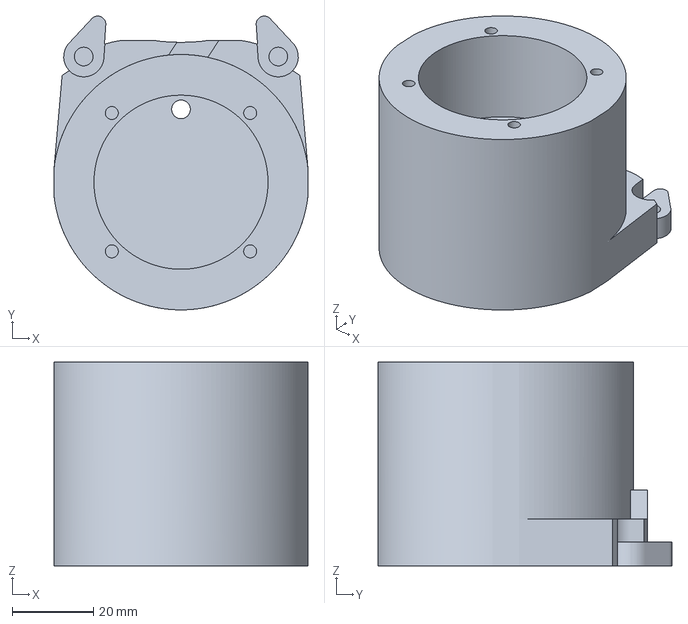
[picture p168: CAD file, 2026-09-15]
top_baffle_v2/to_print/h2c/obiwan/petg_gf_pla/h2c_obiwan_bmr_crescent_TEBM35C10-4.3mf
62.7 x 72.5 x 50.2 mm
