antorsae/lx/top_baffle_v2/to_print/h2c/slim/petg_gf_pla/h2c_slim_06_A_shoulder_top_left_2_of_4.3mf

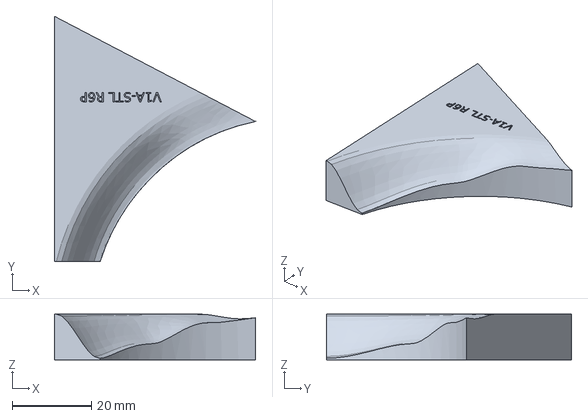
[picture p169: CAD file, 2026-09-15]
top_baffle_v2/to_print/h2c/slim/petg_gf_pla/h2c_slim_06_A_shoulder_top_left_2_of_4.3mf
50.6 x 61.7 x 11.5 mm
