antorsae/lx/top_baffle_v2/to_print/h2c/STL/dayton_nd25fn4/h2c_dayton_nd25fn4_retainer.stl

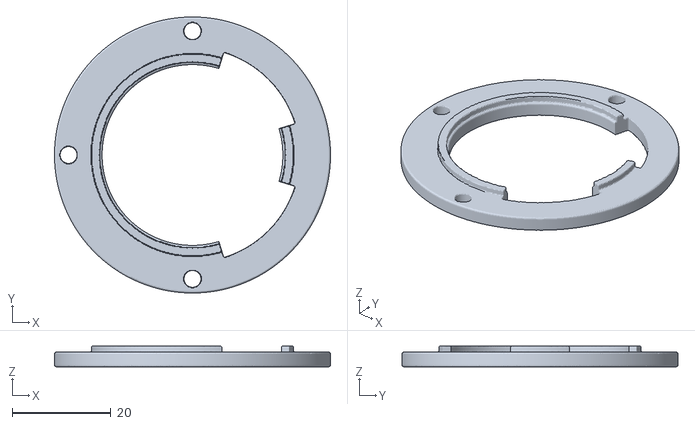
[picture p170: CAD file, 2026-09-15]
top_baffle_v2/to_print/h2c/STL/dayton_nd25fn4/h2c_dayton_nd25fn4_retainer.stl
55.9 x 55.9 x 4.20
