antorsae/lx/top_baffle_v2/to_print/h2c/stock/petg_gf_pla/h2c_stock_upper.gcode.3mf

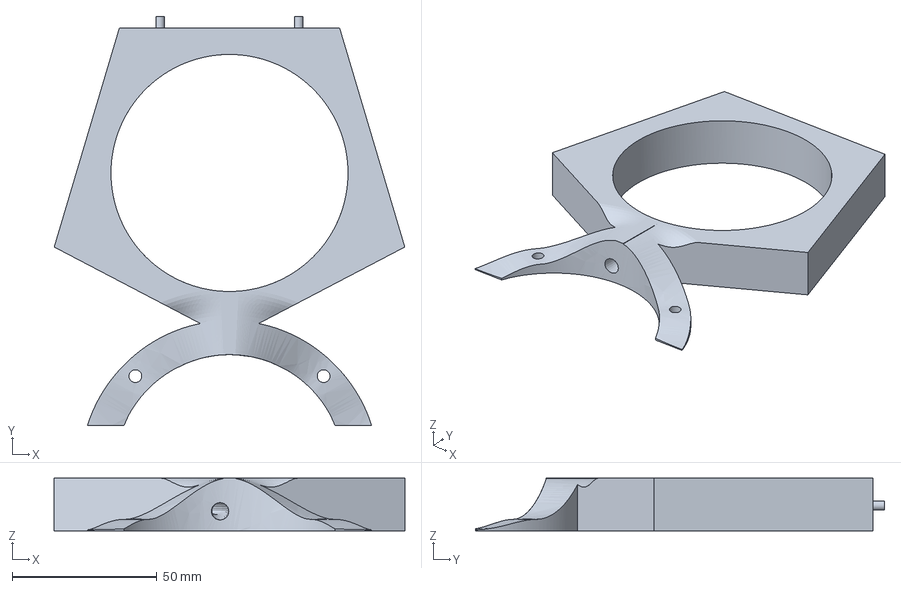
[picture p171: CAD file, 2026-09-15]
top_baffle_v2/to_print/h2c/stock/petg_gf_pla/h2c_stock_upper.gcode.3mf
121.3 x 141.5 x 18.3 mm
