antorsae/lx/top_baffle_v2/to_print/obiwan/3mf_04/obiwan_graded_wings_split2_combo.gcode.3mf

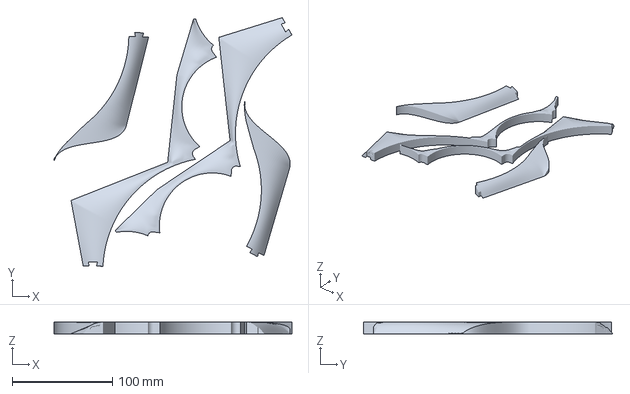
[picture p172: CAD file, 2026-08-20]
top_baffle_v2/to_print/obiwan/3mf_04/obiwan_graded_wings_split2_combo.gcode.3mf
237.2 x 247.8 x 11.5 mm
