antorsae/lx/top_baffle_v2/to_print/obiwan/3mf_06hf/obiwan_11_split2_graded_wing_LM_lower_left_1_of_2_06hf.gcode.3mf

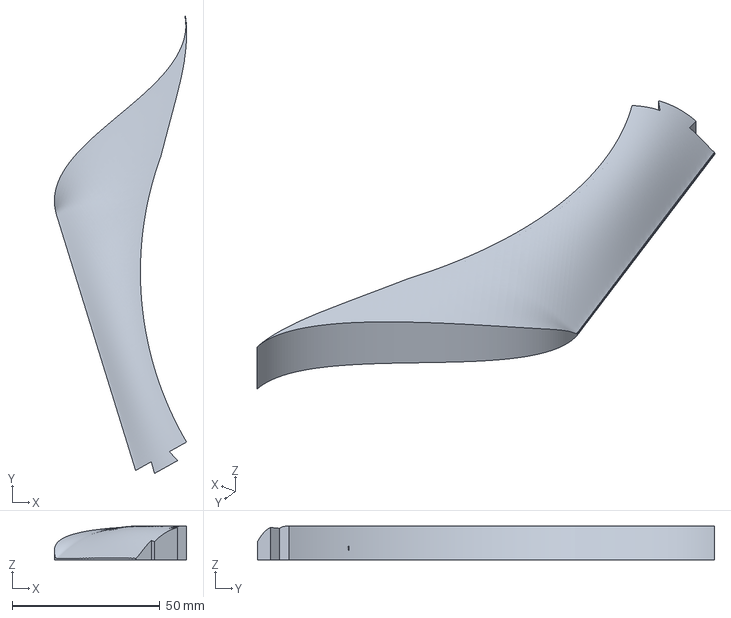
[picture p173: CAD file, 2026-08-20]
top_baffle_v2/to_print/obiwan/3mf_06hf/obiwan_11_split2_graded_wing_LM_lower_left_1_of_2_06hf.gcode.3mf
44.8 x 154.8 x 11.5 mm
