antorsae/lx/top_baffle_v2/to_print/obiwan/3mf_06hf_petg-gf_pla/obiwan_01_LM_bottom_keyed_1_of_2_floor_stand_GUI.3mf

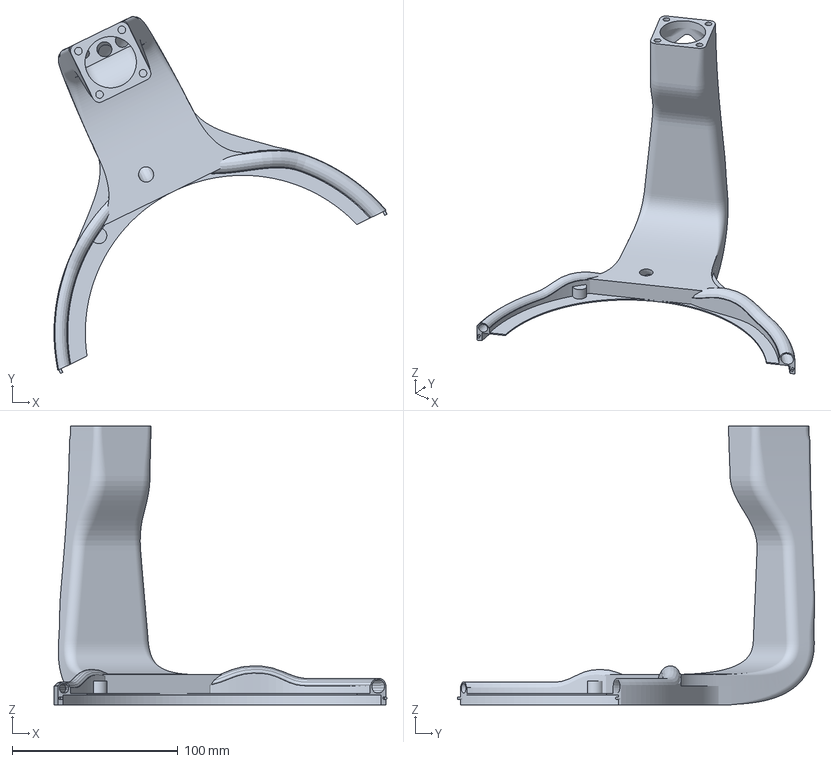
[picture p174: CAD file, 2026-09-15]
top_baffle_v2/to_print/obiwan/3mf_06hf_petg-gf_pla/obiwan_01_LM_bottom_keyed_1_of_2_floor_stand_GUI.3mf
201.1 x 215.6 x 168.3 mm
