antorsae/lx/top_baffle_v2/to_print/slim/3mf_04/slim_05_A_shoulder_bottom_left_1_of_4.gcode.3mf

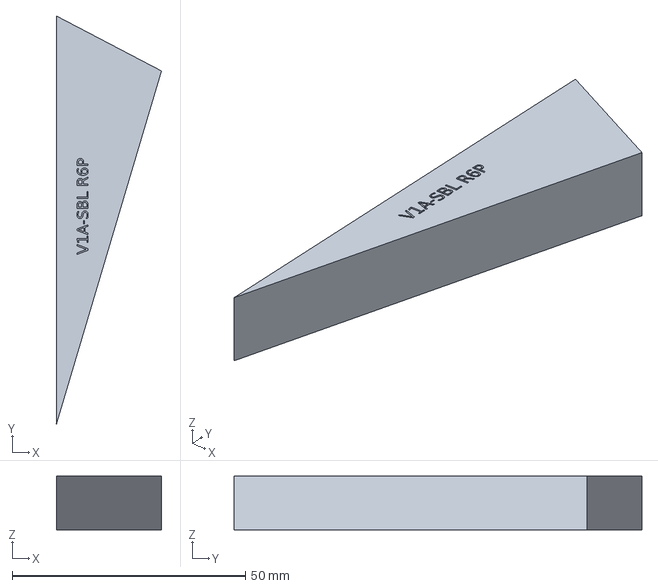
[picture p175: CAD file, 2026-08-20]
top_baffle_v2/to_print/slim/3mf_04/slim_05_A_shoulder_bottom_left_1_of_4.gcode.3mf
22.5 x 87.5 x 11.5 mm
