antorsae/lx/top_baffle_v2/to_print/slim/3mf_06hf/slim_01_LM_bottom_1_of_3_floor_stand_06hf.gcode.3mf

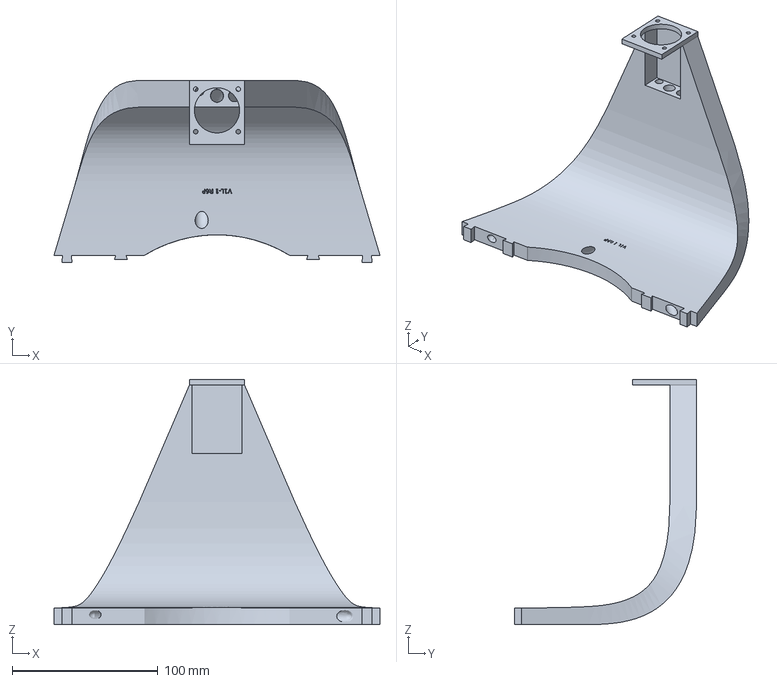
[picture p176: CAD file, 2026-08-20]
top_baffle_v2/to_print/slim/3mf_06hf/slim_01_LM_bottom_1_of_3_floor_stand_06hf.gcode.3mf
223.8 x 125.0 x 168.3 mm
