antorsae/lx/top_baffle_v2/to_print/stock/3mf_04/stock_04_UM_vase_1_of_1.gcode.3mf

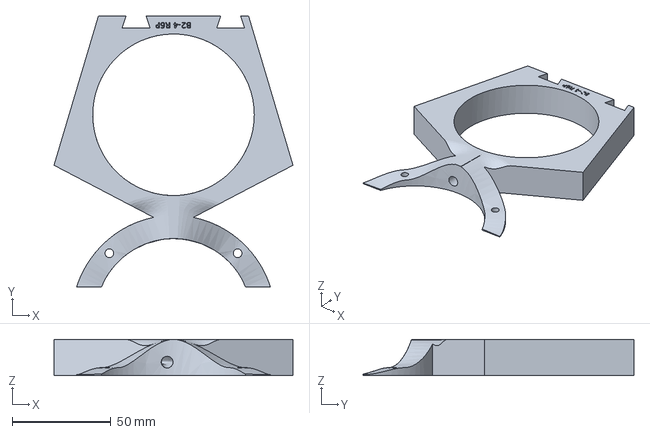
[picture p177: CAD file, 2026-08-20]
top_baffle_v2/to_print/stock/3mf_04/stock_04_UM_vase_1_of_1.gcode.3mf
121.3 x 137.5 x 18.3 mm
