antorsae/lx/top_baffle_v2/wings/ae/top_baffle_nd25fw4_obiwan_wing_ae.step

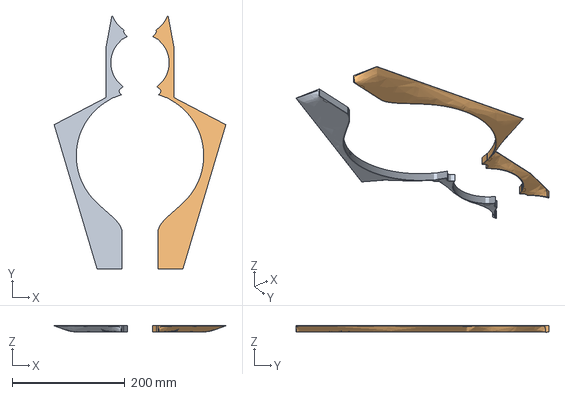
[picture p179: CAD file, 2026-08-09]
top_baffle_v2/wings/ae/top_baffle_nd25fw4_obiwan_wing_ae.step
304.8 x 449.1 x 11.7 mm
obiwan_wing_ae_left_monolithic
obiwan_wing_ae_right_monolithic
