antorsae/lx/top_baffle_v2/build/bmr_slim_TEBM35C10-4/obiwan_bmr_slim_crescent_TEBM35C10-4.step

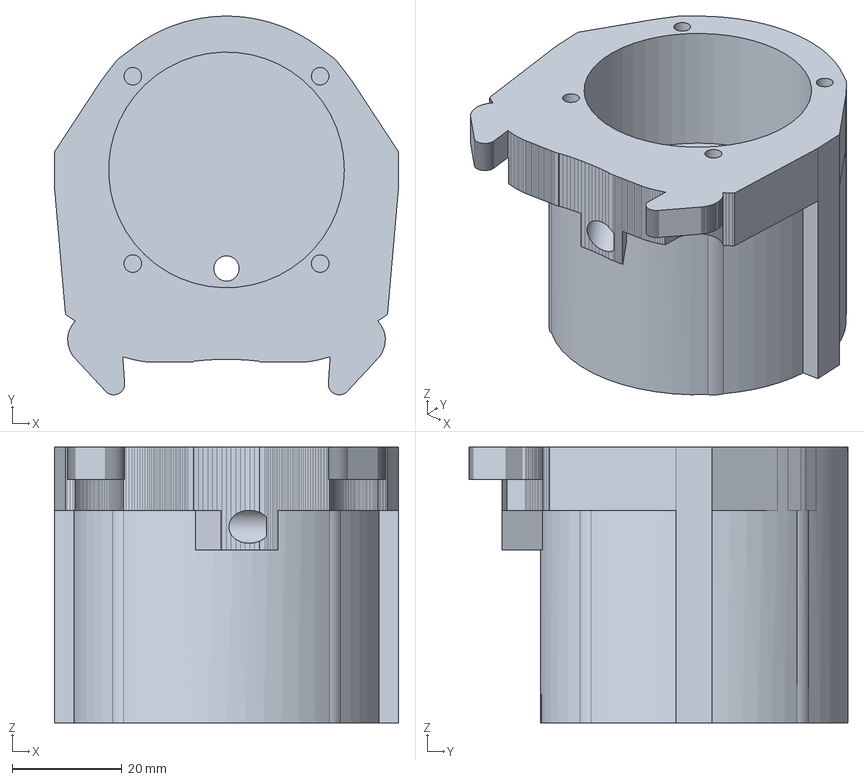
[picture p180: CAD file, 2026-08-15]
top_baffle_v2/build/bmr_slim_TEBM35C10-4/obiwan_bmr_slim_crescent_TEBM35C10-4.step
62.7 x 69.0 x 50.2 mm
