antorsae/lx/top_baffle_v2/build/floor_stand/obiwan_attachments.step

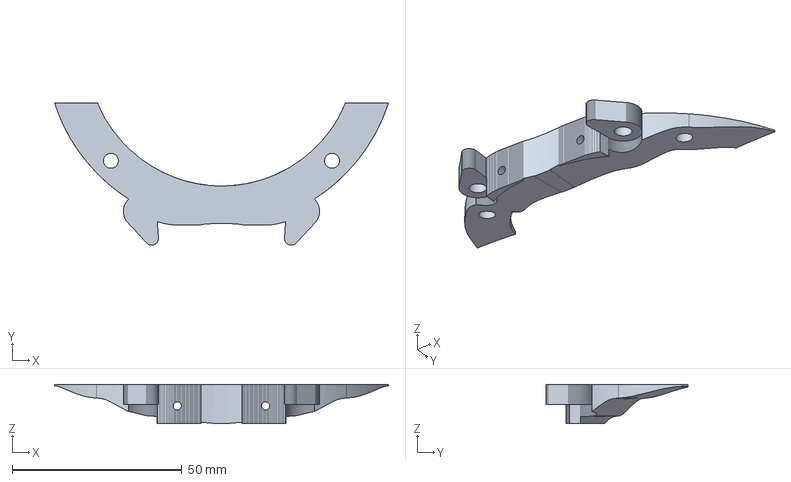
[picture p181: CAD file, 2026-08-15]
top_baffle_v2/build/floor_stand/obiwan_attachments.step
98.3 x 41.9 x 11.5 mm
