antorsae/lx/top_baffle_v2/build/floor_stand/stl/obiwan_core_1_of_2_lm_carrier.stl

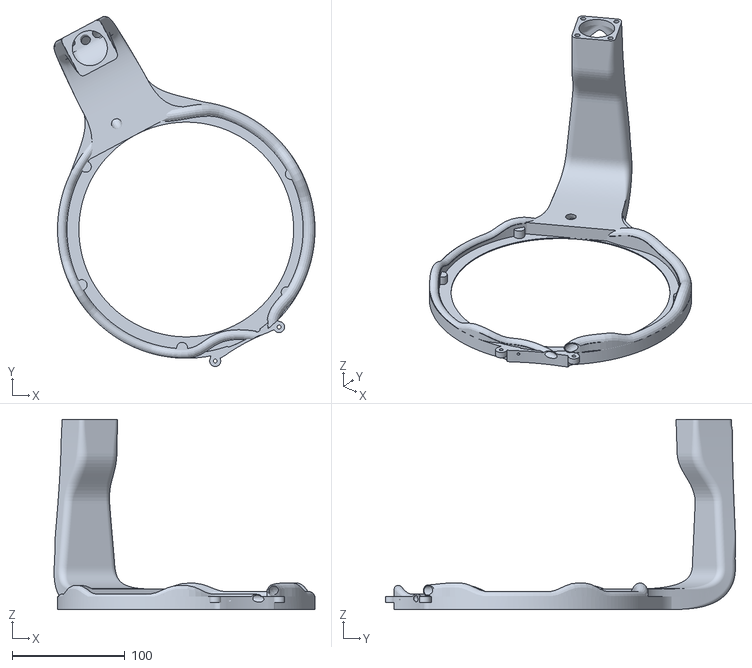
[picture p182: CAD file, 2026-08-20]
top_baffle_v2/build/floor_stand/stl/obiwan_core_1_of_2_lm_carrier.stl
231.0 x 309.8 x 168.3
