antorsae/lx/top_baffle_v2/build/floor_stand/support_blockers/obiwan_optional_lm_keyed_2_of_2_top.support_blocker.stl

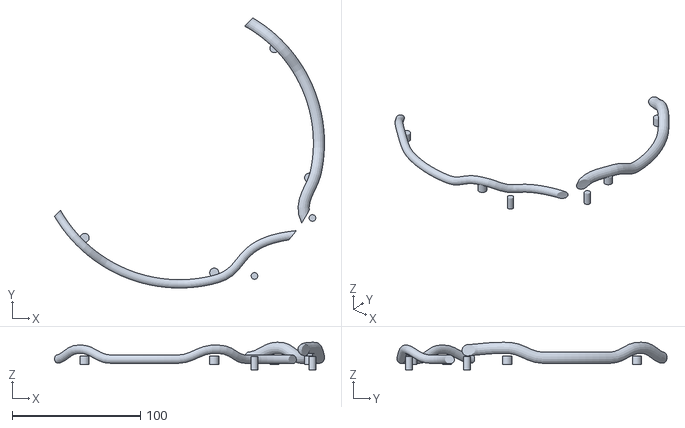
[picture p183: CAD file, 2026-08-20]
top_baffle_v2/build/floor_stand/support_blockers/obiwan_optional_lm_keyed_2_of_2_top.support_blocker.stl
210.8 x 210.8 x 21.5
