antorsae/lx/top_baffle_v2/build/h2c/STEP/h2c_stock_lm_upper_floor_stand.step

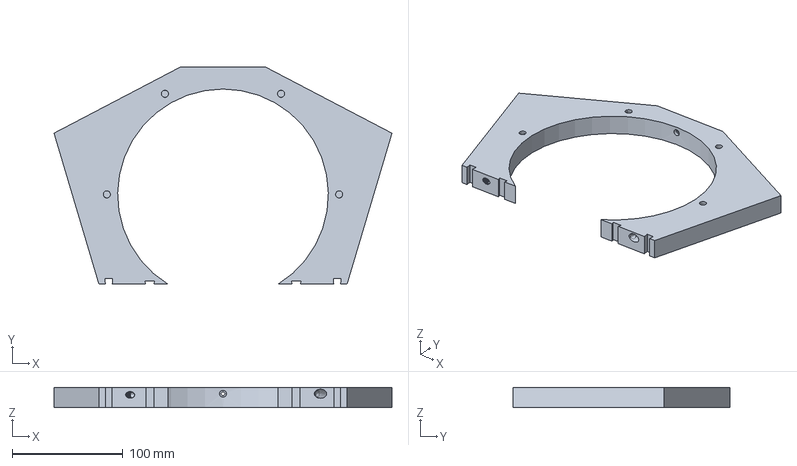
[picture p184: CAD file, 2026-09-15]
top_baffle_v2/build/h2c/STEP/h2c_stock_lm_upper_floor_stand.step
304.8 x 195.9 x 18.3 mm
