antorsae/lx/top_baffle_v2/build/h2c/support_blockers/h2c_stock_upper_bmr.stl

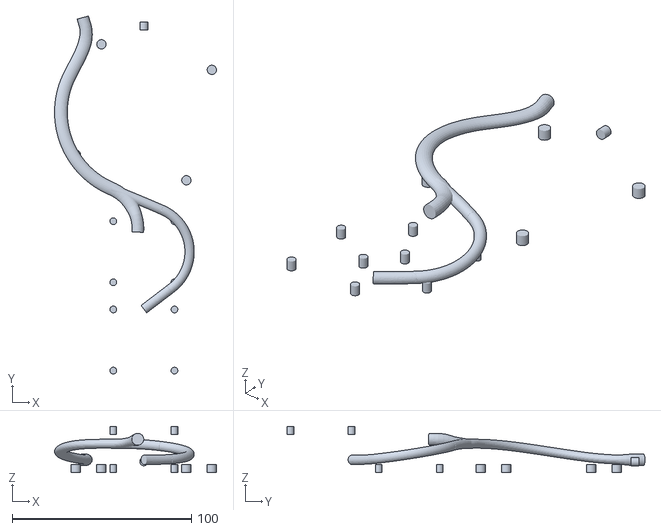
[picture p186: CAD file, 2026-09-15]
top_baffle_v2/build/h2c/support_blockers/h2c_stock_upper_bmr.stl
90.4 x 199.9 x 25.7
