antorsae/lx/top_baffle_v2/build/no_floor_stand/stl/obiwan_optional_lm_keyed_2_of_2_top.stl

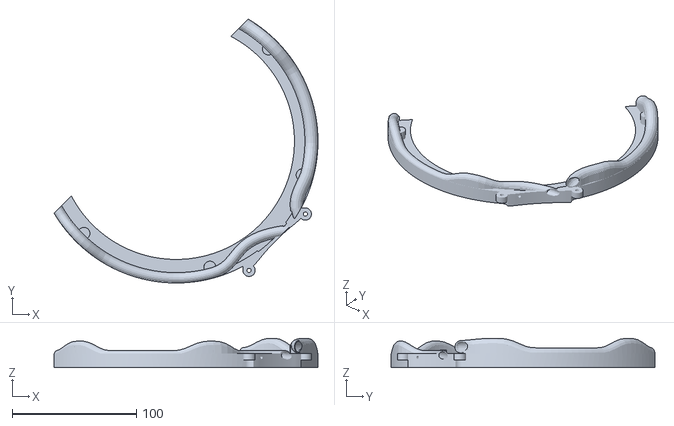
[picture p187: CAD file, 2026-08-20]
top_baffle_v2/build/no_floor_stand/stl/obiwan_optional_lm_keyed_2_of_2_top.stl
212.1 x 212.1 x 23.6
