antorsae/lx/top_baffle_v2/build/print_plates/obiwan/obiwan_01_02_03_04_LM_UM_combo_floor_stand.stl

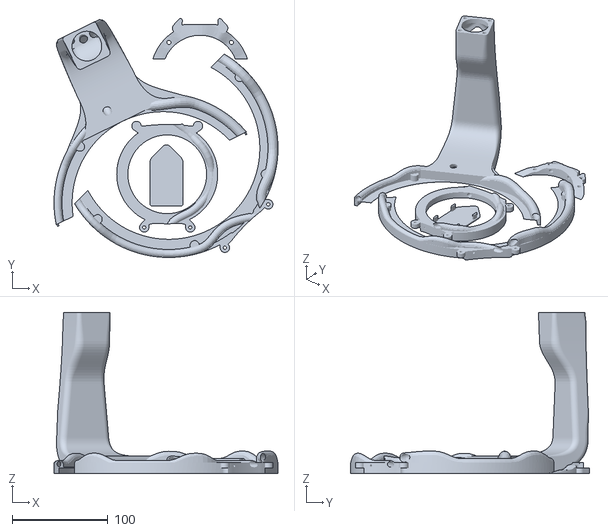
[picture p188: CAD file, 2026-09-15]
top_baffle_v2/build/print_plates/obiwan/obiwan_01_02_03_04_LM_UM_combo_floor_stand.stl
233.5 x 249.1 x 168.3
