antorsae/lx/top_baffle_v2/build/ptt_crescent_PTT1.3T04-HAG-01/obiwan_ptt13_dipole_crescent_PTT1.3T04-HAG-01.print.stl

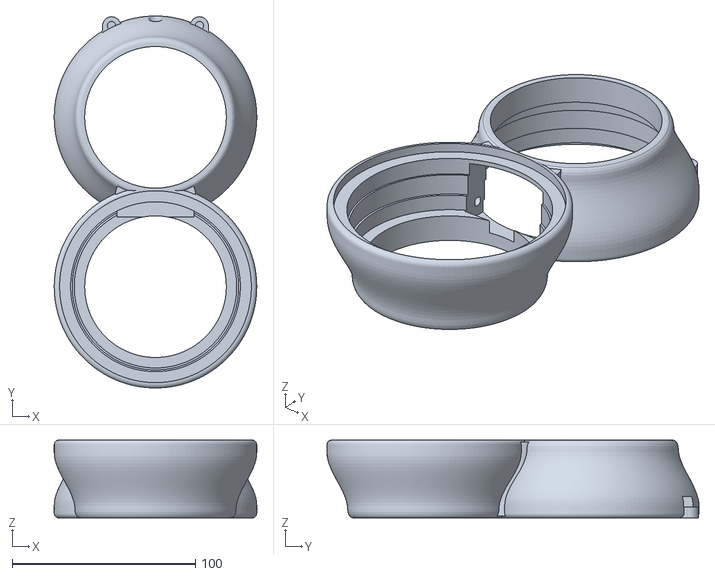
[picture p189: CAD file, 2026-08-21]
top_baffle_v2/build/ptt_crescent_PTT1.3T04-HAG-01/obiwan_ptt13_dipole_crescent_PTT1.3T04-HAG-01.print.stl
110.6 x 203.1 x 42.5
