antorsae/lx/top_baffle_v2/candidates/nd25fn4_crescent/print/qualification/D6_wing_coupon.stl

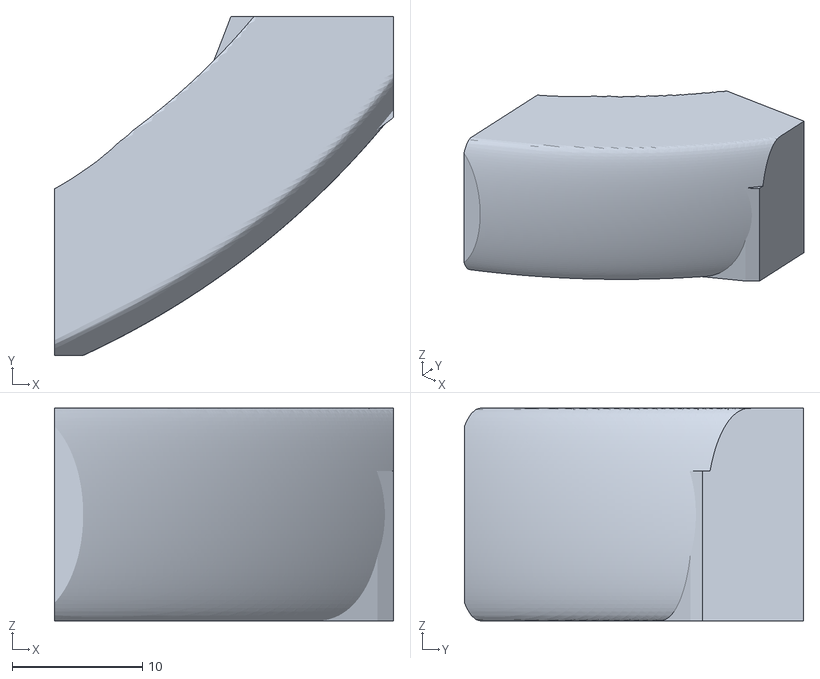
[picture p190: CAD file, 2026-09-15]
top_baffle_v2/candidates/nd25fn4_crescent/print/qualification/D6_wing_coupon.stl
26.0 x 26.0 x 16.3
