antorsae/lx/top_baffle_v2/coupons/obiwan_ae_embed/lx521_obiwan_ae_embed_coupon_pair.step

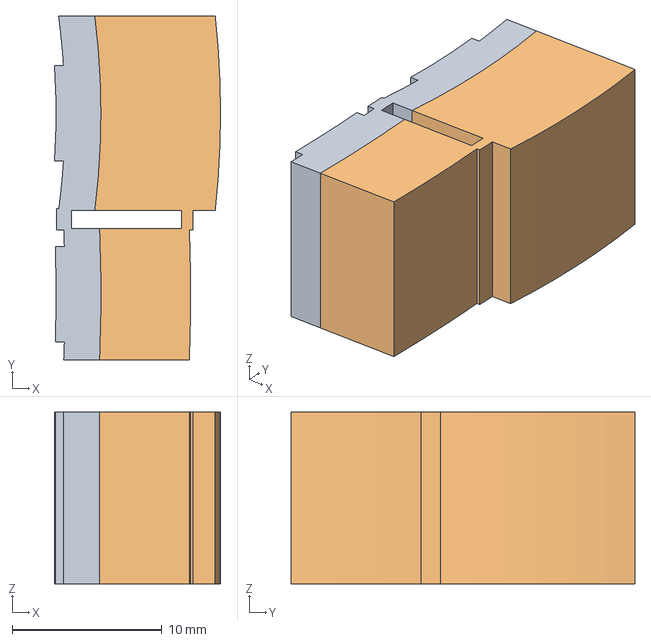
[picture p191: CAD file, 2026-08-09]
top_baffle_v2/coupons/obiwan_ae_embed/lx521_obiwan_ae_embed_coupon_pair.step
11.1 x 23.0 x 11.5 mm
obiwan_lm_um_carrier_embed_coupon
obiwan_ae_lm_um_embed_coupon
