antorsae/lx/top_baffle_v2/coupons/obiwan_ae_embed/stl/lx521_coupon_obiwan_ae_embed_ae_wing.stl

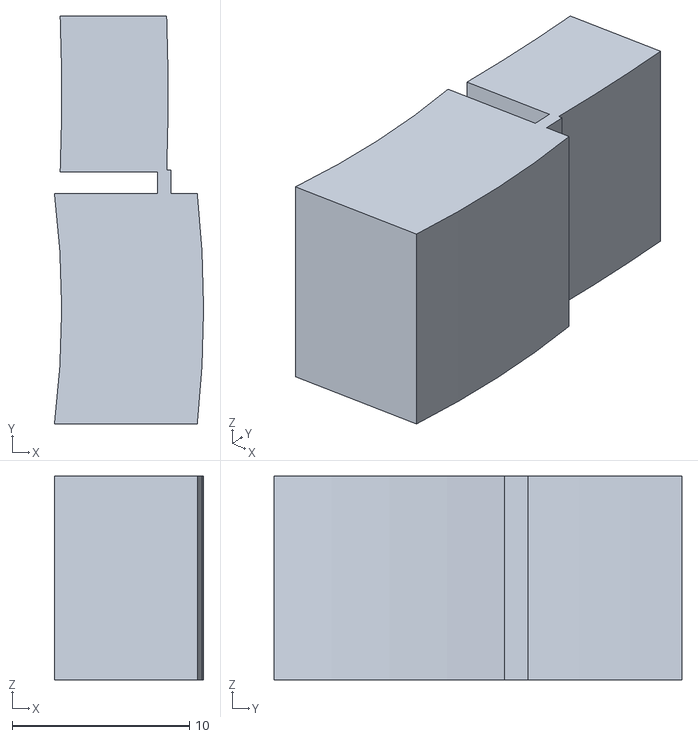
[picture p192: CAD file, 2026-08-09]
top_baffle_v2/coupons/obiwan_ae_embed/stl/lx521_coupon_obiwan_ae_embed_ae_wing.stl
8.41 x 23.0 x 11.5
