antorsae/lx/top_baffle_v2/floor_stand/top_baffle_nd25fw4_obiwan_split.step

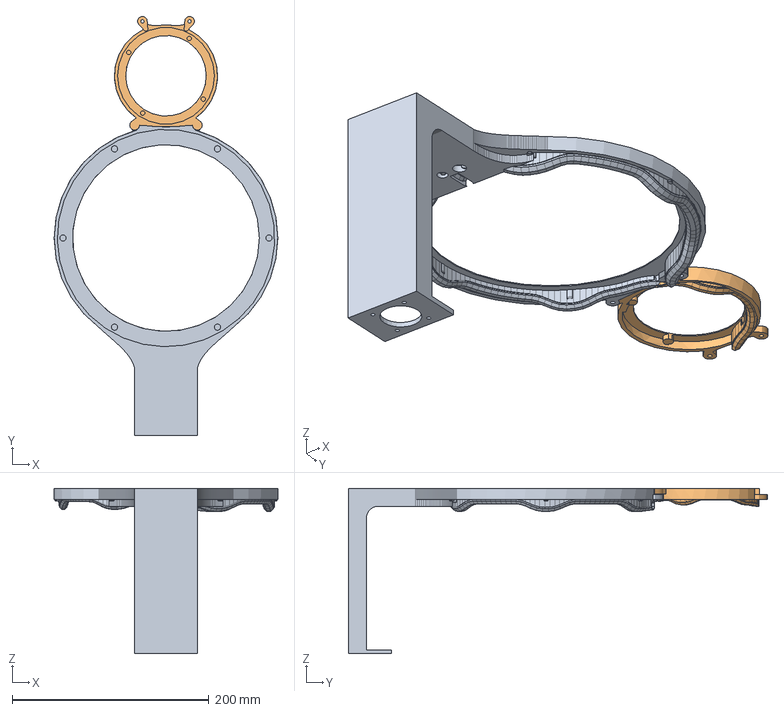
[picture p193: CAD file, 2026-08-09]
top_baffle_v2/floor_stand/top_baffle_nd25fw4_obiwan_split.step
227.6 x 426.4 x 168.3 mm
core_lm_carrier
core_um_carrier
