antorsae/lx/top_baffle_v2/no_floor_stand/top_baffle_nd25fw4_v1_split.step

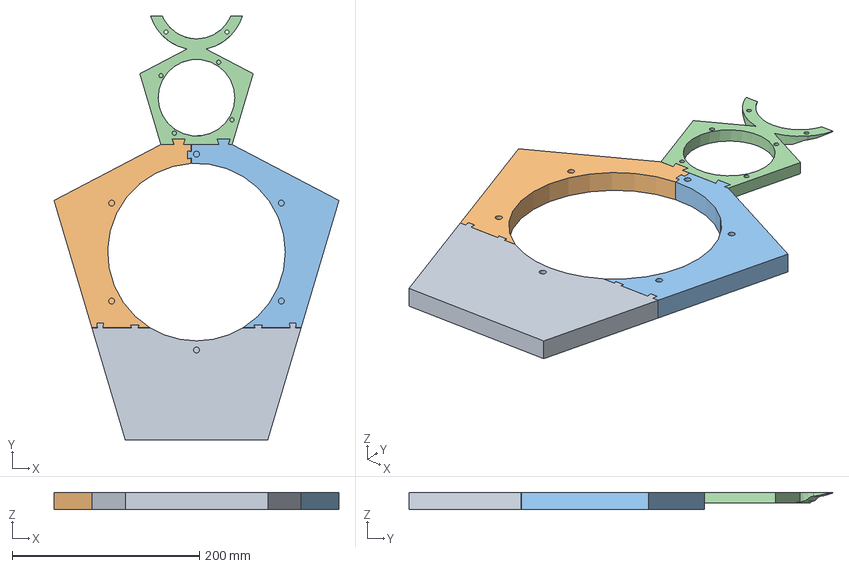
[picture p194: CAD file, 2026-08-09]
top_baffle_v2/no_floor_stand/top_baffle_nd25fw4_v1_split.step
304.8 x 453.5 x 18.3 mm
piece_bottom
piece_mid_left
piece_mid_right
piece_top_b2
