antorsae/lx/top_baffle_v2/qualification/process_witnesses.step

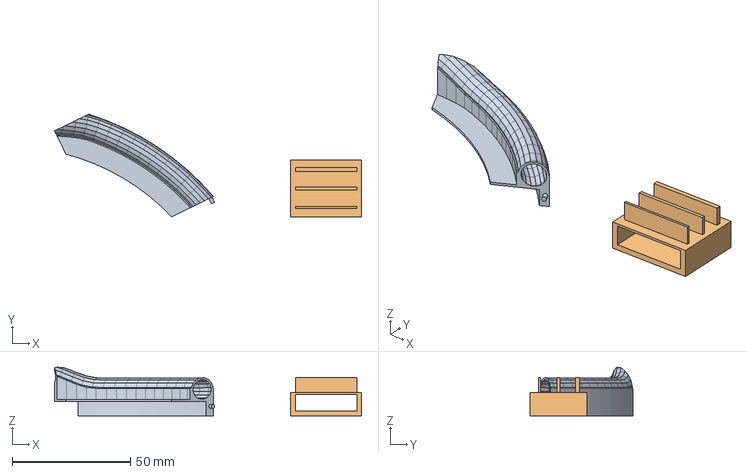
[picture p195: CAD file, 2026-09-15]
top_baffle_v2/qualification/process_witnesses.step
130.0 x 43.5 x 20.6 mm
native_route_cover
supported_roof_and_wall_steps
