antorsae/lx/top_baffle_v2/review/nd25fn4_print/D6_coupon/D6_wing_coupon_blocker.stl

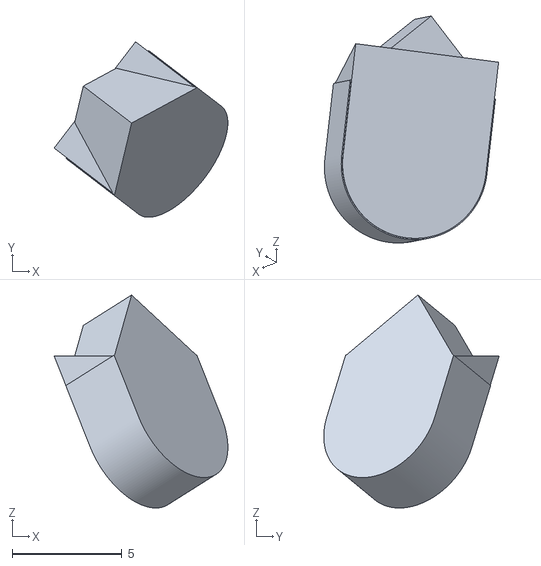
[picture p196: CAD file, 2026-09-15]
top_baffle_v2/review/nd25fn4_print/D6_coupon/D6_wing_coupon_blocker.stl
7.92 x 7.99 x 9.70
