antorsae/lx/top_baffle_v2/to_print/h2c/STL/dayton_nd25fn4/h2c_dayton_nd25fn4_cap.stl

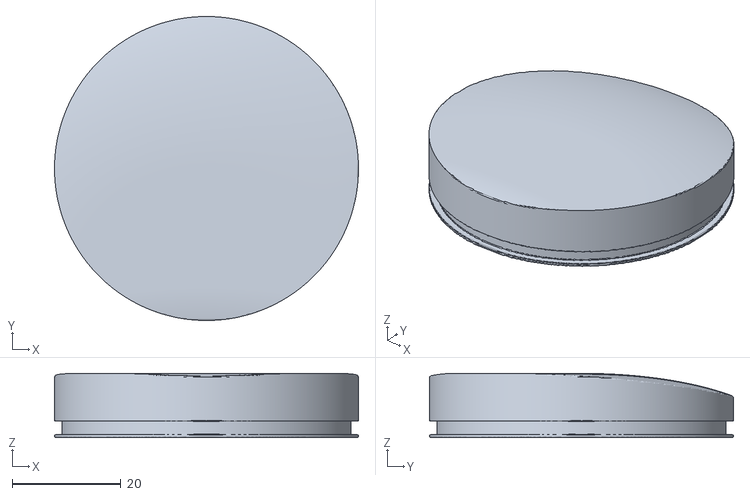
[picture p197: CAD file, 2026-09-15]
top_baffle_v2/to_print/h2c/STL/dayton_nd25fn4/h2c_dayton_nd25fn4_cap.stl
56.0 x 56.0 x 11.8
