antorsae/lx/top_baffle_v2/to_print/obiwan/3mf_04/obiwan_09_split2_flat_wing_LM_UM_upper_right_2_of_2.gcode.3mf

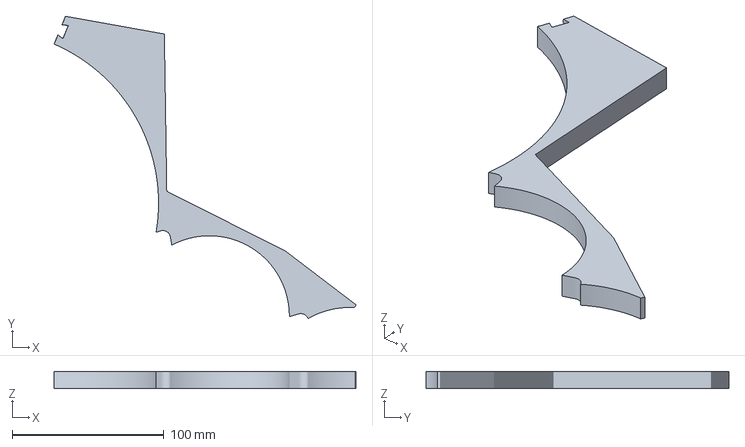
[picture p198: CAD file, 2026-08-20]
top_baffle_v2/to_print/obiwan/3mf_04/obiwan_09_split2_flat_wing_LM_UM_upper_right_2_of_2.gcode.3mf
198.9 x 199.2 x 11.5 mm
