antorsae/lx/top_baffle_v2/to_print/obiwan/3mf_06hf_petg-gf/obiwan_flat_wings_split2_combo_06hf_petg-gf.gcode.3mf

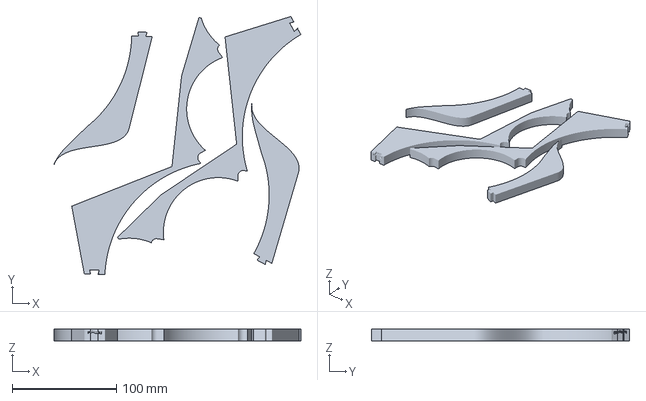
[picture p200: CAD file, 2026-09-15]
top_baffle_v2/to_print/obiwan/3mf_06hf_petg-gf/obiwan_flat_wings_split2_combo_06hf_petg-gf.gcode.3mf
237.2 x 247.8 x 11.5 mm
