antorsae/lx/top_baffle_v2/to_print/slim/3mf_04/slim_01_LM_bottom_1_of_3_no_floor_stand.gcode.3mf

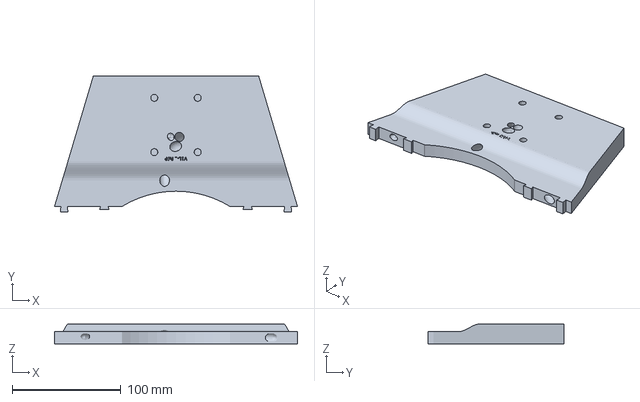
[picture p201: CAD file, 2026-08-20]
top_baffle_v2/to_print/slim/3mf_04/slim_01_LM_bottom_1_of_3_no_floor_stand.gcode.3mf
223.8 x 125.0 x 18.3 mm
