antorsae/lx/top_baffle_v2/to_print/slim/3mf_06hf/slim_02_LM_mid_left_2_of_3_06hf.gcode.3mf

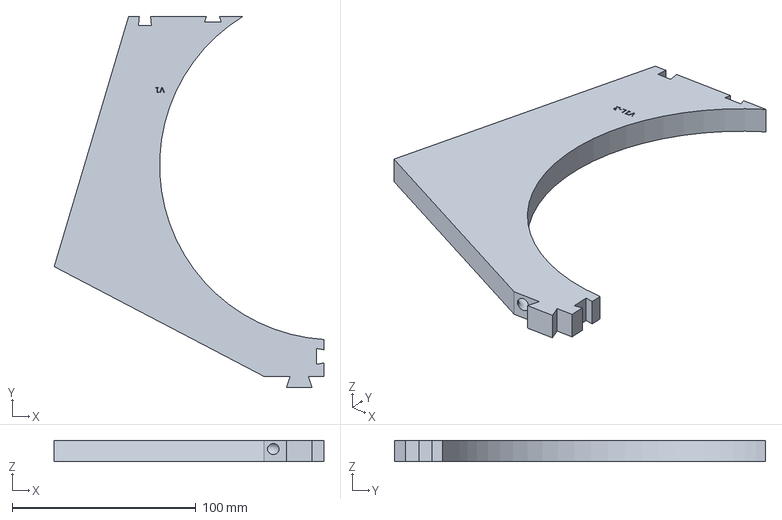
[picture p202: CAD file, 2026-08-20]
top_baffle_v2/to_print/slim/3mf_06hf/slim_02_LM_mid_left_2_of_3_06hf.gcode.3mf
146.8 x 201.9 x 11.5 mm
