antorsae/lx/top_baffle_v2/to_print/stock/3mf_04/stock_06_A_shoulder_top_left_2_of_4.gcode.3mf

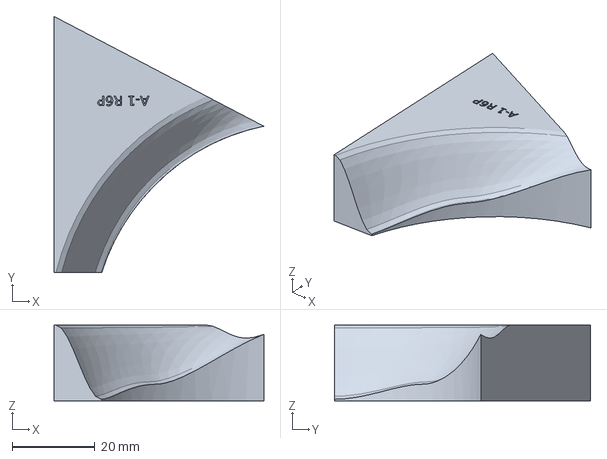
[picture p203: CAD file, 2026-08-20]
top_baffle_v2/to_print/stock/3mf_04/stock_06_A_shoulder_top_left_2_of_4.gcode.3mf
50.6 x 61.7 x 18.3 mm
