antorsae/lx/top_baffle_v2/build/floor_stand/obiwan_lm_split.step

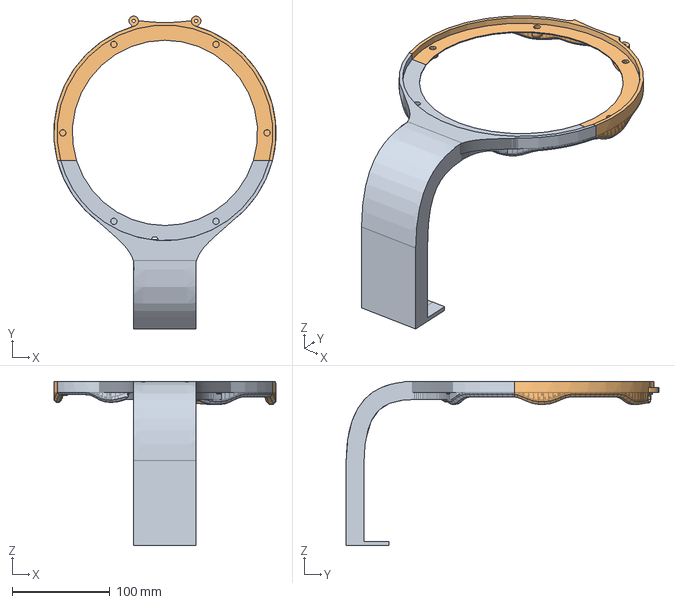
[picture p204: CAD file, 2026-08-13]
top_baffle_v2/build/floor_stand/obiwan_lm_split.step
227.6 x 320.7 x 168.3 mm
optional_lm_keyed_1_of_2_bottom
optional_lm_keyed_2_of_2_top
