antorsae/lx/top_baffle_v2/build/floor_stand/stl/lx521_coupon_7_recess_seat.stl

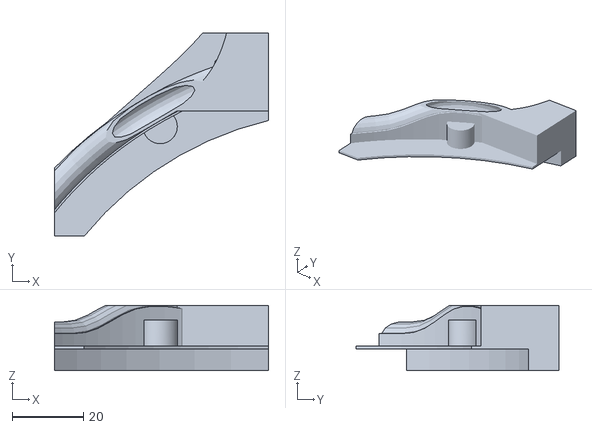
[picture p205: CAD file, 2026-08-20]
top_baffle_v2/build/floor_stand/stl/lx521_coupon_7_recess_seat.stl
60.0 x 57.0 x 18.3
