antorsae/lx/top_baffle_v2/build/h2c/README.md

# H2C build authorities

The user-facing file guide is [to_print/h2c](../../to_print/h2c/README.md).
This directory stores native geometry, frozen profiles, print provenance and
digital qualification reports.

- `STEP/` and `STL/`: explicit H2C exports. Stock/Slim uses
  `src/lx521_baffle/h2c/proud.py`; the full Obiwan LM and regular wings reuse the
  existing canonical native solids. Full Stock/Slim floor LM exports are
  intermediate geometry for the released lower/upper pair.
- `contracts/` and `support_blockers/`: native bore definitions and nonprinting
  cable/insert keepouts. `inputs/` contains their positioned print copies.
- `profiles/`: resolved H2C machine, process and material settings, plus the
  original Bambu profile inheritance sources. `print_policy_h2c.json` owns the
  printer-specific settings; `print_policy.json` owns shared hardware and infill.
- `jobs/`: current process inputs, exact CLI commands and per-job audits.
  Disposable slicer work files are excluded from Git. Validation can recover
  plain G-code from each hash-verified published `.gcode.3mf`.
- `review_models/` and `views/`: source-positioned native assemblies, inspection
  reports and orthographic review images.
- `experiments/`: development evidence outside the print shelf.

The migration also preserves both existing `build/<stand-state>/.obiwan_stage/`
transactions in Git. They are native input authorities for the continuous LM,
including the complete manifests and referenced BREP files. The exporter checks
the state, transaction and hashes before importing them. Changing shared Obiwan
CAD requires regenerating those canonical inputs before rebuilding H2C outputs.

The retained Dayton ND25FN-4 waveguide body uses its original installed-to-print transform metadata.
Caps and retainers were authored directly in print coordinates and use their
original hash-bound build records. The release validator recognizes exactly
those three retained files and verifies them against the original sources; all
other released meshes use the shared front-down print sidecar contract.
