antorsae/lx/top_baffle_v2/build/bmr_crescent_TEBM35C10-4/slice_audit_coaxial/CAPTIVE_MAGNET_PAUSE_MANIFEST.md

# Captive-magnet pause manifest

Authoritative for the exact STL and profile hashes below. This run used Bambu Lab P2S 0.4 nozzle, 0.16 mm Arachne layers, and Bambu PLA Basic @BBL P2S. All parts are front-face-down.

This audit did not contact a printer and did not upload or start a print.

## Insertion procedure

1. Open the hash-listed ready-to-print 3MF; do not auto-orient it.
2. The Bambu Custom park/pause/restore events at the exact **first-closing** Z values below are already embedded and were verified in both project XML and G-code; do not add or move them manually. Each raises the nozzle to Z=250 mm (lowering the bed), pauses with `M400 U1`, then restores the exact layer Z on Continue.
3. At each pause, insert the listed number of D5 x 2 mm magnets vertically downward from above (+Z side) along print `-Z` (`print_insertion_direction_xyz = [0, 0, -1]`), with the marked pole oriented exactly as specified.
4. Ensure every magnet is fully seated below the completed layer and cannot rise into the toolhead path.
5. Resume printing. Polarity cannot be corrected after the roof buries the magnet.

## Exact pauses

| State | Variant / part | Pause Z | Last open | Seated margin | Magnets / sites | Insertion | Polarity |
|---|---|---:|---:|---:|---|---|---|
| shared | Obiwan-TEBM35C10-4-BMR-crescent / `obiwan_bmr_crescent_TEBM35C10-4` | **5.96 mm** | 5.80 mm | 0.10 mm | 2 / tebm_front_left_base, tebm_front_right_base | `[0.0, 0.0, -1.0]`: insert vertically downward from above the paused part (+Z side) through the open loading chimney along print -Z | `tebm_front_left_base`: marked pole → `(-1.0, 0.0, 0.0)` in print coordinates; marked/N pole points OUT from the pod along installed_marked_pole_axis_xyz; verify the future mating piece uses the opposite interface-facing pole before burial<br>`tebm_front_right_base`: marked pole → `(1.0, 0.0, 0.0)` in print coordinates; marked/N pole points OUT from the pod along installed_marked_pole_axis_xyz; verify the future mating piece uses the opposite interface-facing pole before burial |

## Audited Bambu arrangements

Every listed 3MF was exported by the same Bambu slice invocation, hash-bound to the staged STL, and audited as an exact mesh with only a proper unit-scale rotation about print Z plus XY placement.

| State | Variant / part | Arrange Rz | Ready-to-print 3MF | SHA-256 | Ready fingerprint |
|---|---|---:|---|---|---|
| shared | Obiwan-TEBM35C10-4-BMR-crescent / `obiwan_bmr_crescent_TEBM35C10-4` | 0.000000 deg | `/Users/antor/gh/lx/top_baffle_v2/build/bmr_crescent_TEBM35C10-4/slice_audit_coaxial/slices/shared_Obiwan-TEBM35C10-4-BMR-crescent_obiwan_bmr_crescent_TEBM35C10-4/ready/ready_to_print.gcode.3mf` | `1dd0e012b292f7af7a64b1bc720a5ce36610672bd9dddd95b8768e0e246c6cdb` | `56b031462a3a4940632623f6143b1ef37d15b20fd94e130fac5ea46c45d4a5ec` |

## Profile and evidence

- Catalog SHA-256: `cf910de26961093f4d1804c205b755441bfe93071ef661d5a583b03fdee42ca4`
- Resolved profile-set SHA-256: `6a5436c0b966a93241d612c2dd8d465f3f4234e7ccfc24ba9292c93fd2e89263`
- Bambu Studio binary SHA-256: `b022be6750898454803e9e07178b7c7446c0e5b4d148c593b4b56efde09ba281`
- Artifacts: 1 passed, 0 failed
- Each printable artifact directory under `slices/` contains the hash-bound arranged Bambu 3MF, plain G-code, Bambu `result.json`, static validator output, and five-layer SVG/PNG toolpath evidence for every cavity.

The JSON file is the machine-readable authority; this Markdown and the CSV are derived views.
