antorsae/lx/top_baffle_v2/build/floor_stand/baffle_b1_drivers.png

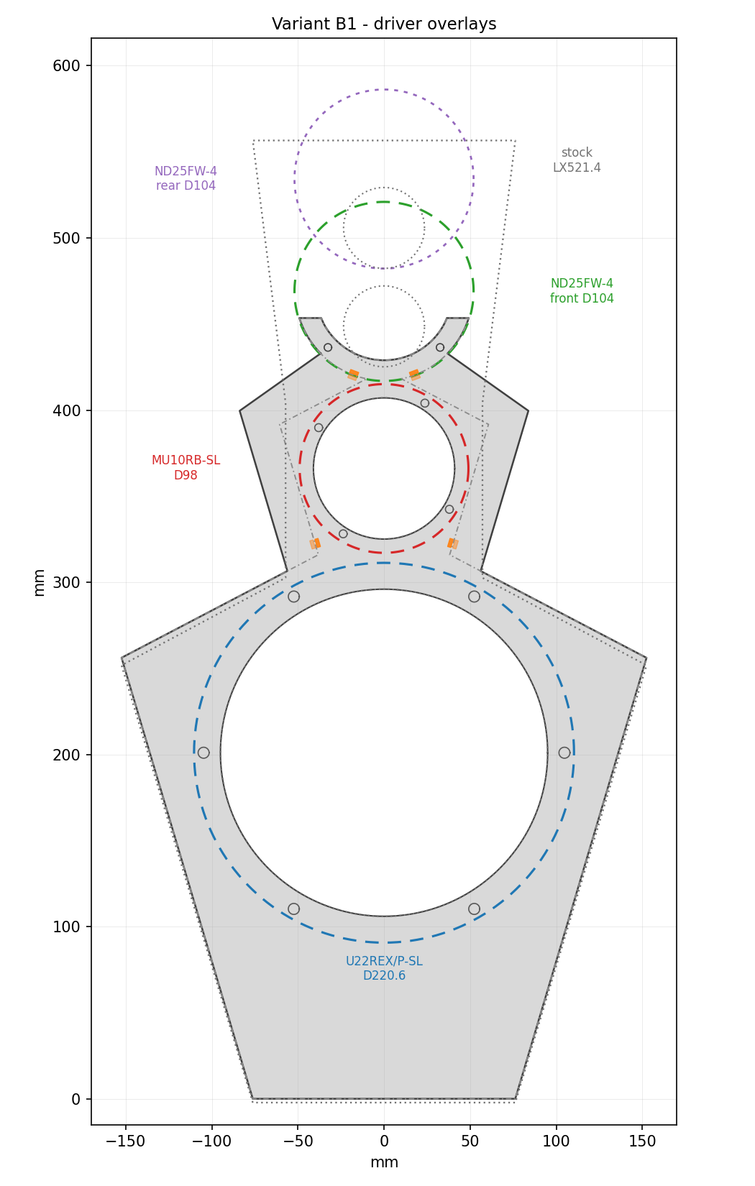
top_baffle_v2/build/floor_stand/baffle_b1_drivers.png
