antorsae/lx/top_baffle_v2/build/floor_stand/baffle_cable_routing_proud.png

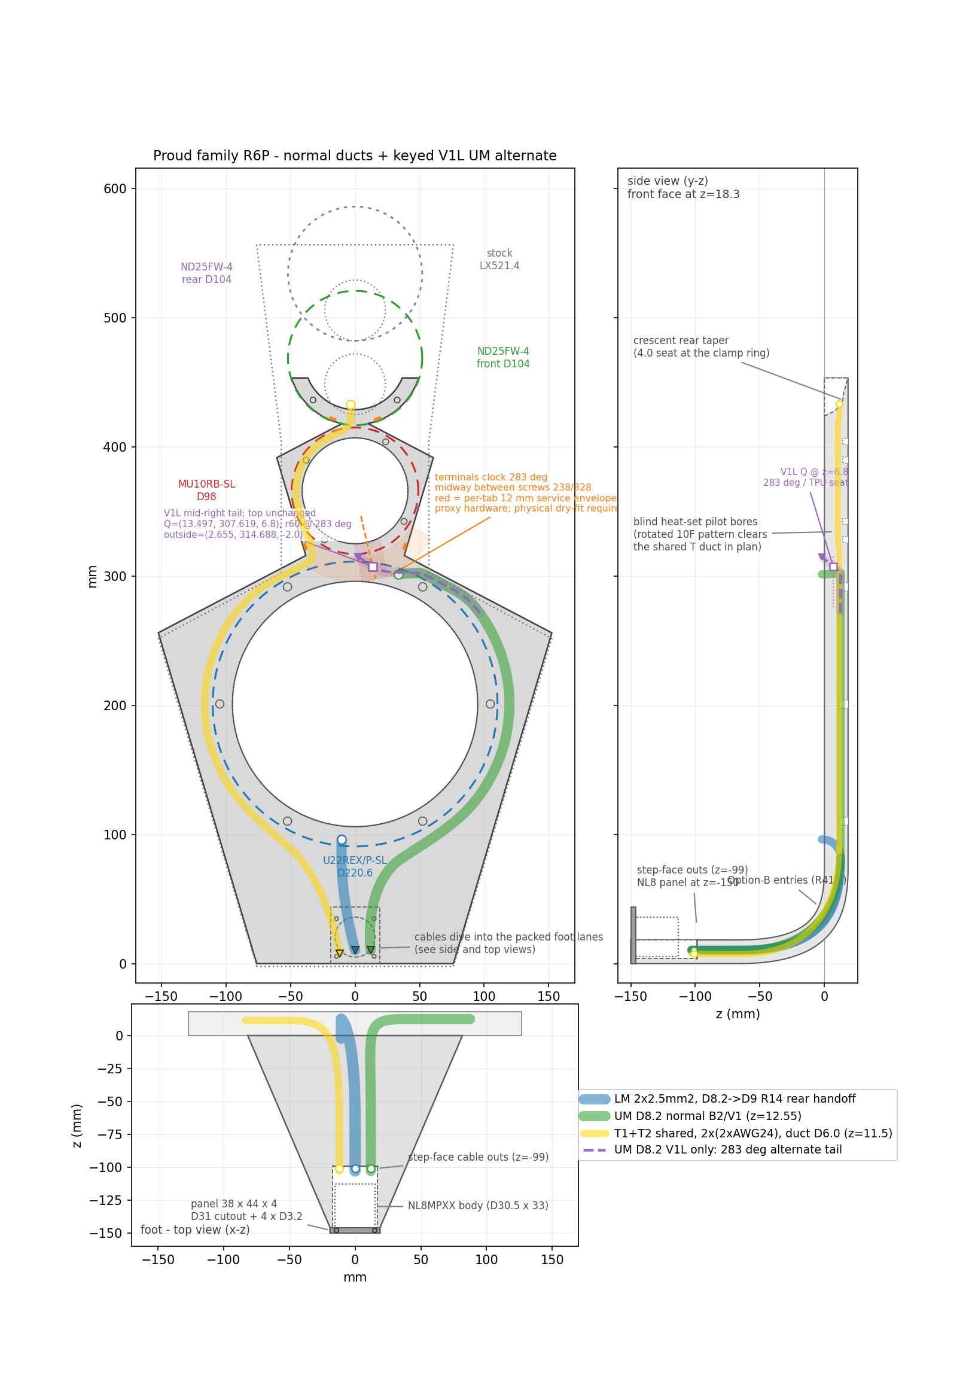
top_baffle_v2/build/floor_stand/baffle_cable_routing_proud.png
