antorsae/lx/top_baffle_v2/build/floor_stand/baffle_variants_drivers.png

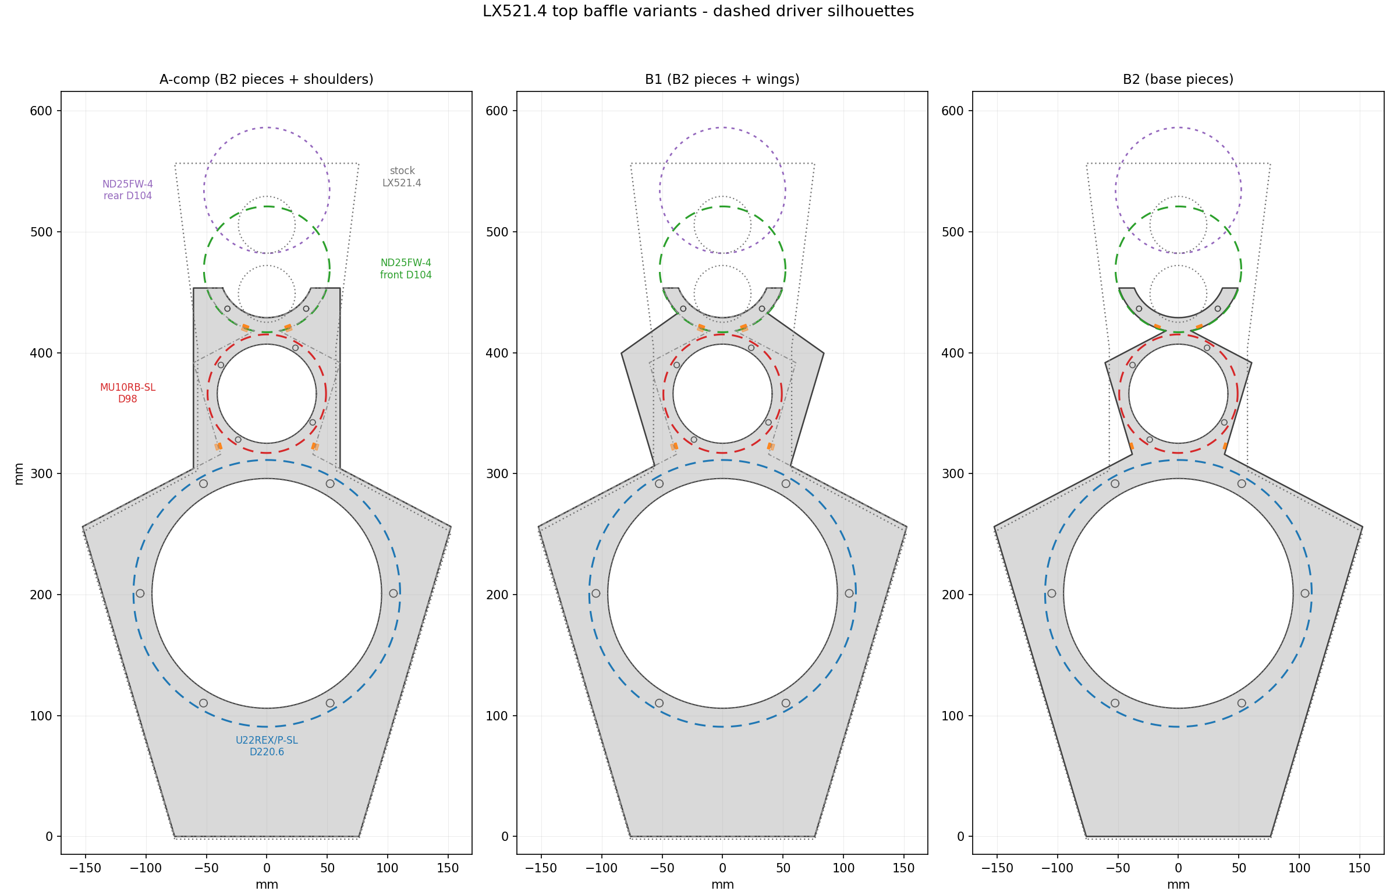
top_baffle_v2/build/floor_stand/baffle_variants_drivers.png
