antorsae/lx/top_baffle_v2/build/floor_stand/um_finish/UM_rear.png

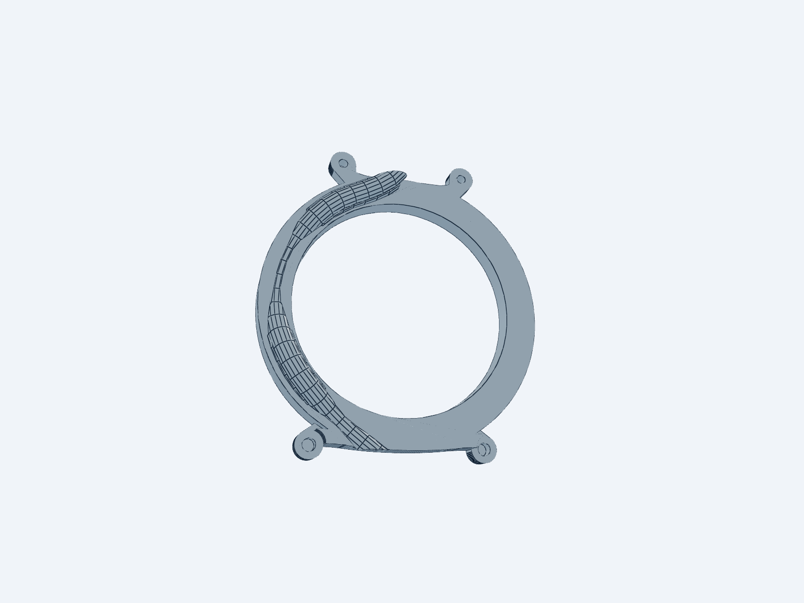
top_baffle_v2/build/floor_stand/um_finish/UM_rear.png
