antorsae/lx/top_baffle_v2/build/h2c/views/H2C_Dayton_ND25FN4_flat_rear_oblique.png

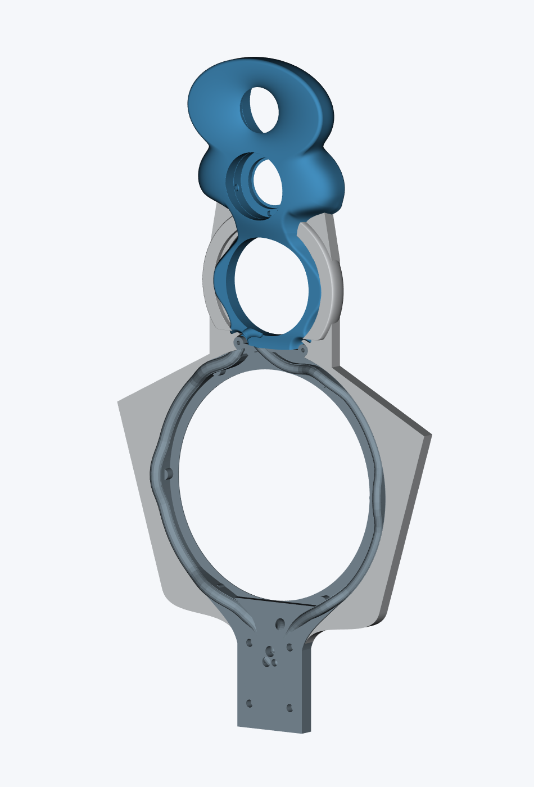
top_baffle_v2/build/h2c/views/H2C_Dayton_ND25FN4_flat_rear_oblique.png
