antorsae/lx/top_baffle_v2/build/h2c/views/primary_review_contact_sheet.png

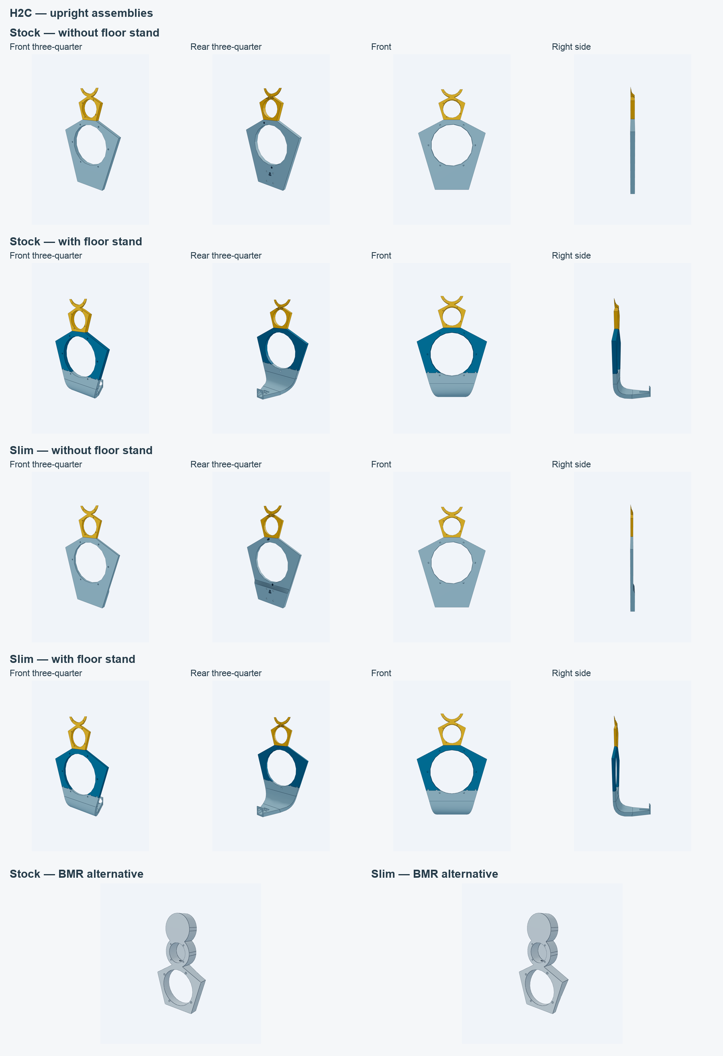
top_baffle_v2/build/h2c/views/primary_review_contact_sheet.png
