antorsae/lx/top_baffle_v2/build/h2c/views/slim_floor_stand_opposite_20260915T152205Z.png

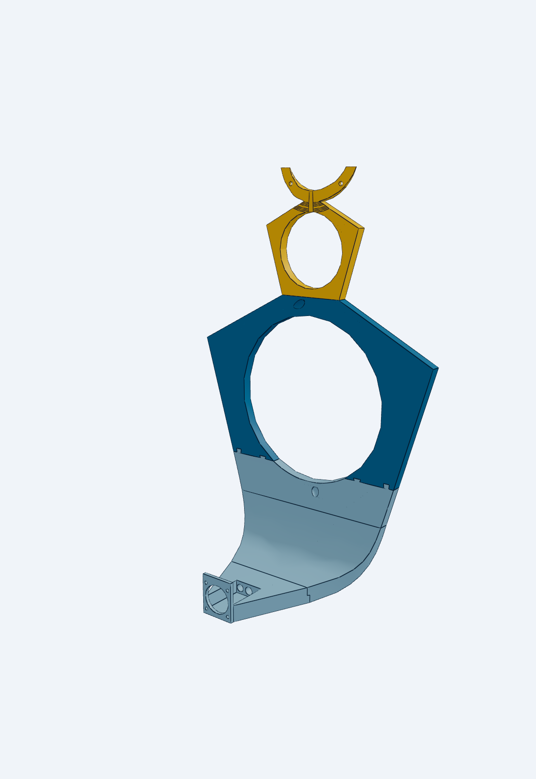
top_baffle_v2/build/h2c/views/slim_floor_stand_opposite_20260915T152205Z.png
