antorsae/lx/top_baffle_v2/build/h2c/views/slim_upper_bmr_20260915T133254Z.png

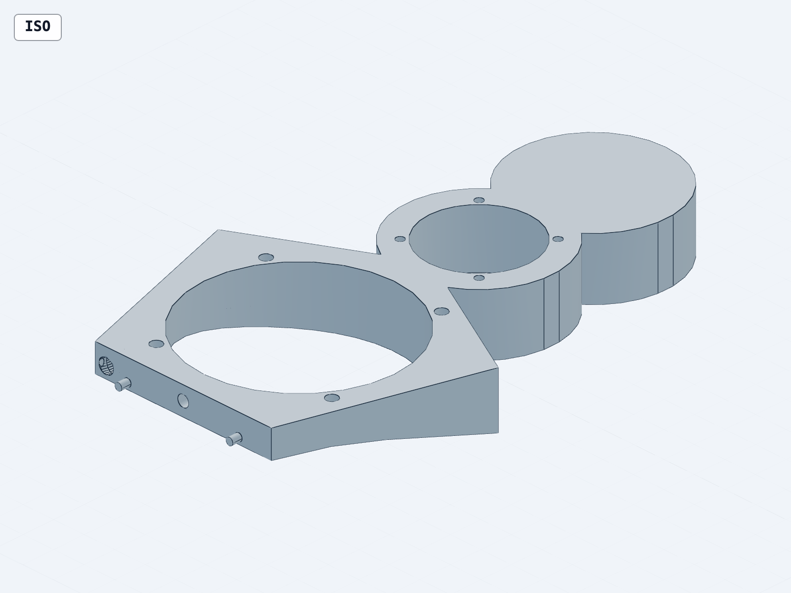
top_baffle_v2/build/h2c/views/slim_upper_bmr_20260915T133254Z.png
