antorsae/lx/top_baffle_v2/build/print_plates/obiwan/obiwan_flat_wings_split2_combo.layout.png

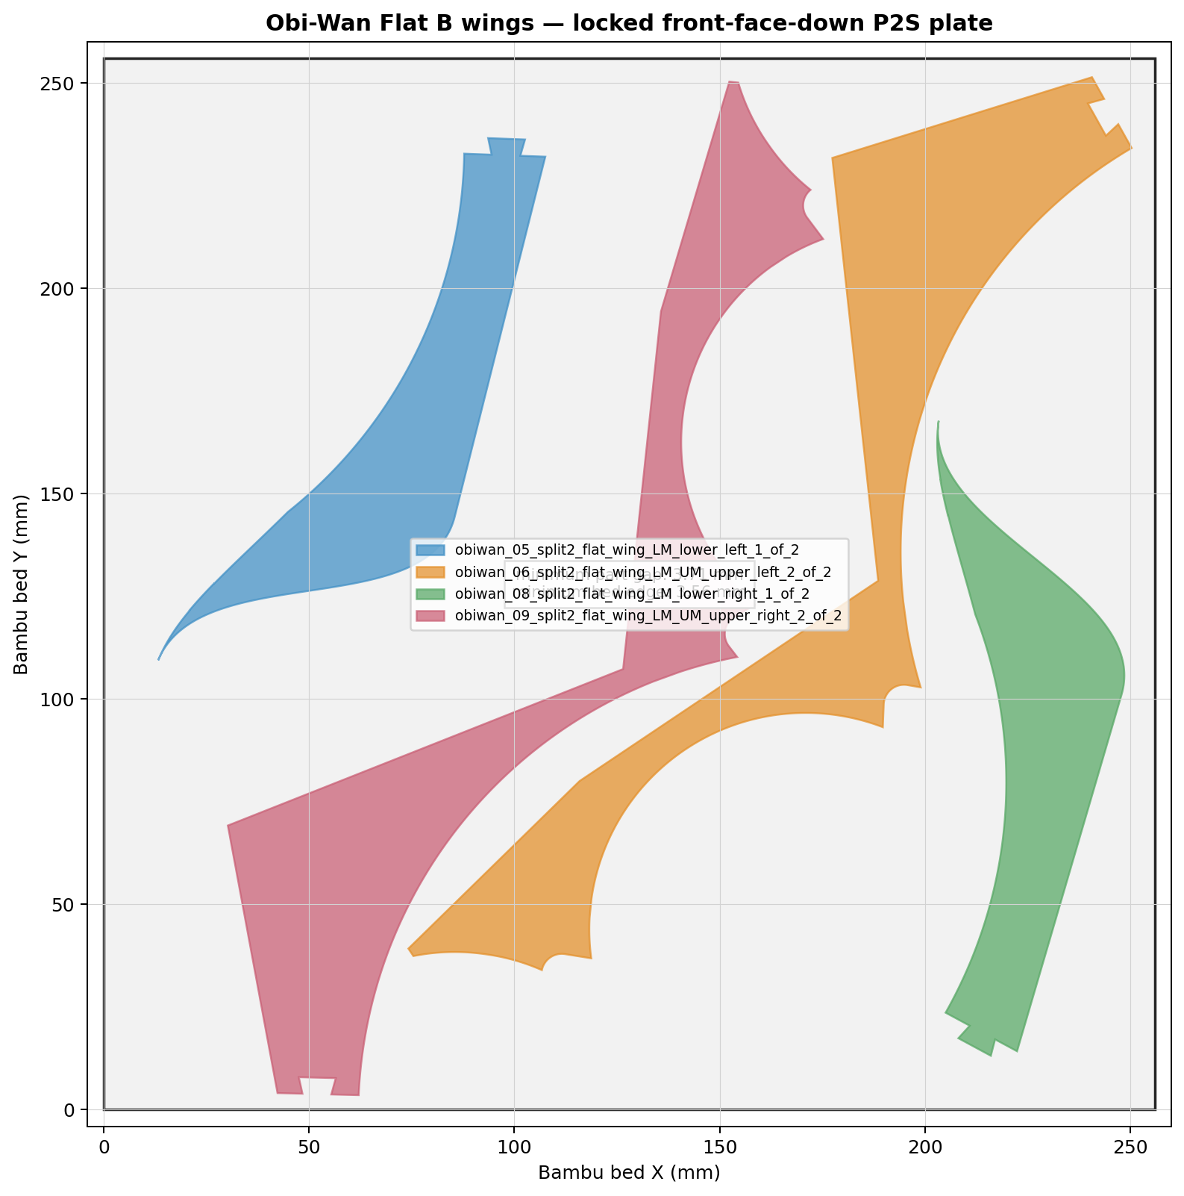
top_baffle_v2/build/print_plates/obiwan/obiwan_flat_wings_split2_combo.layout.png
