antorsae/lx/top_baffle_v2/build/wings/flat/review/obiwan_wing_flat_rear.png

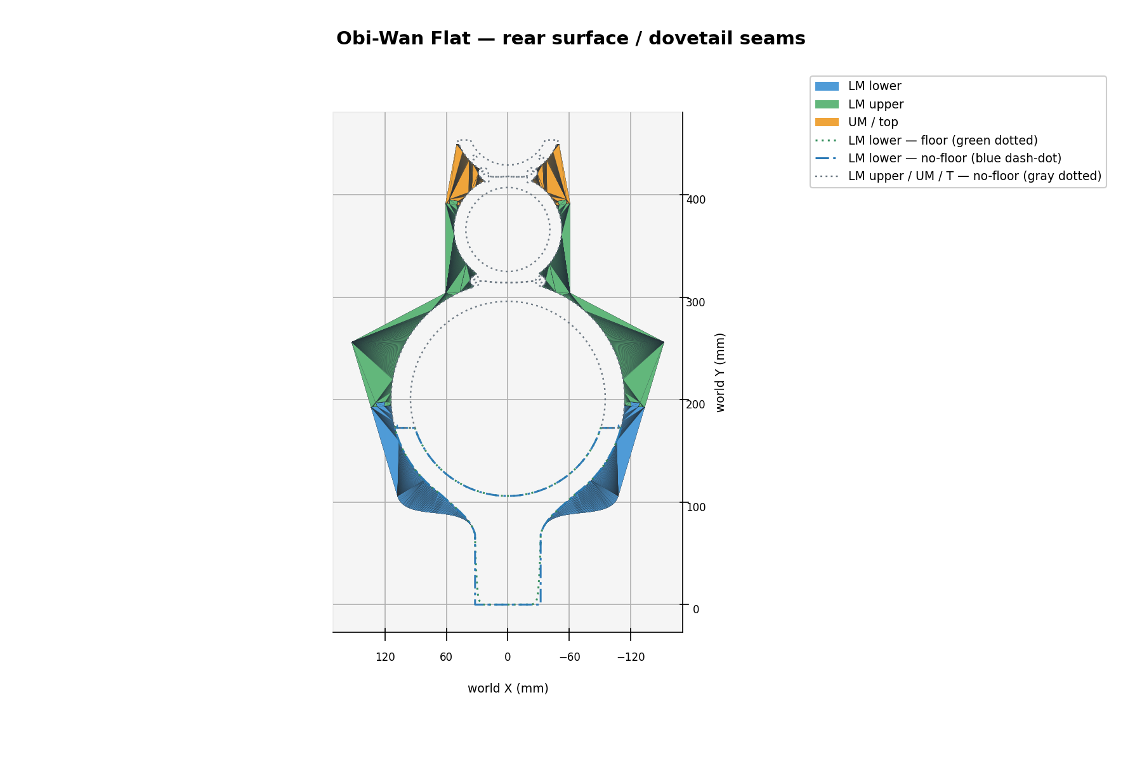
top_baffle_v2/build/wings/flat/review/obiwan_wing_flat_rear.png
