antorsae/lx/top_baffle_v2/build/wings/flat/review/obiwan_wing_flat_side_section.png

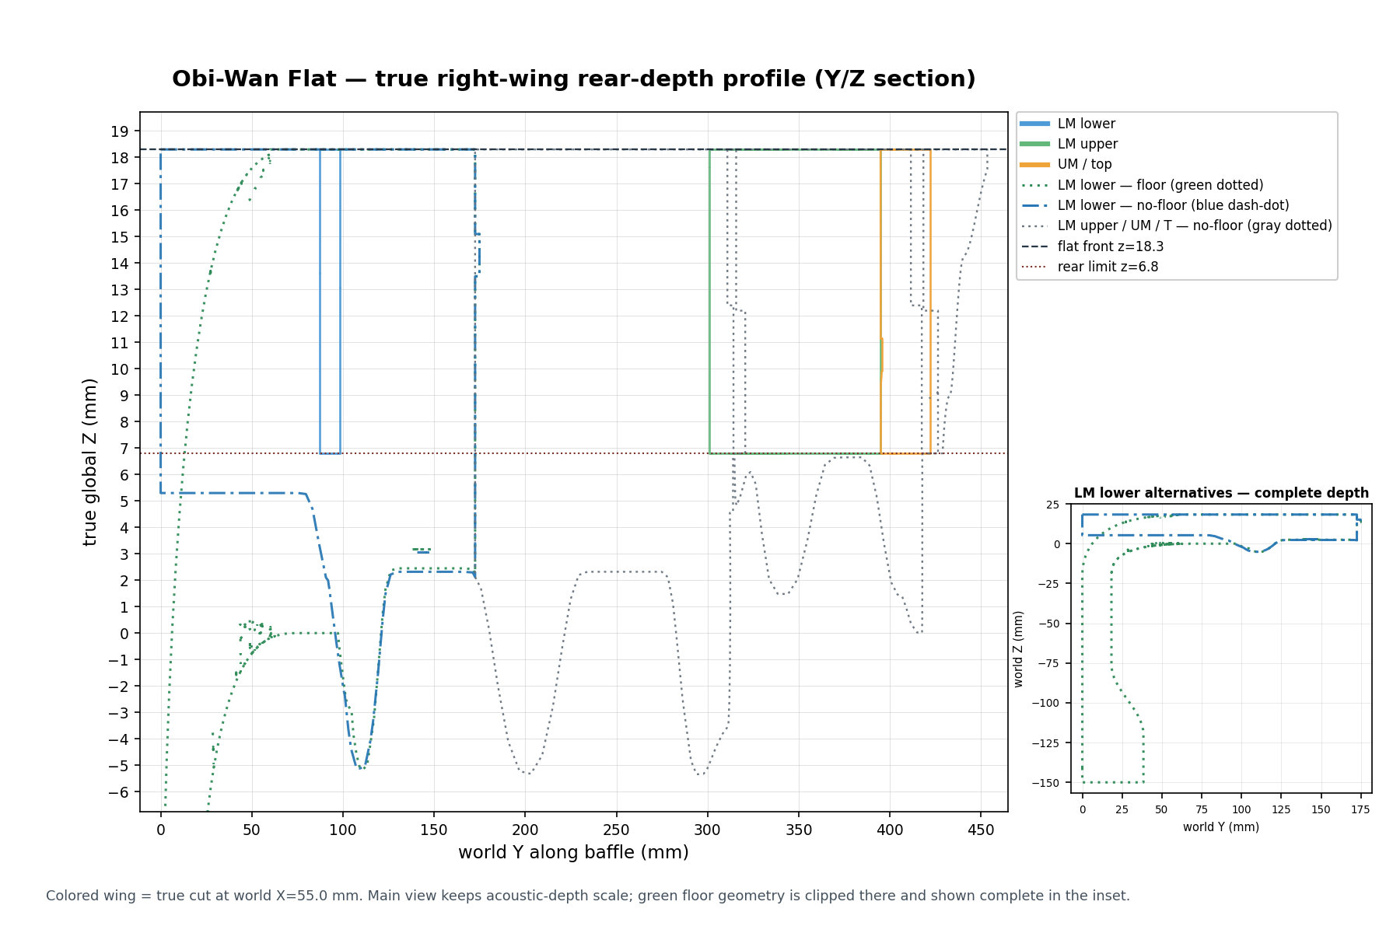
top_baffle_v2/build/wings/flat/review/obiwan_wing_flat_side_section.png
