antorsae/lx/top_baffle_v2/build/wings/flat/review/obiwan_wing_flat_split_exploded.png

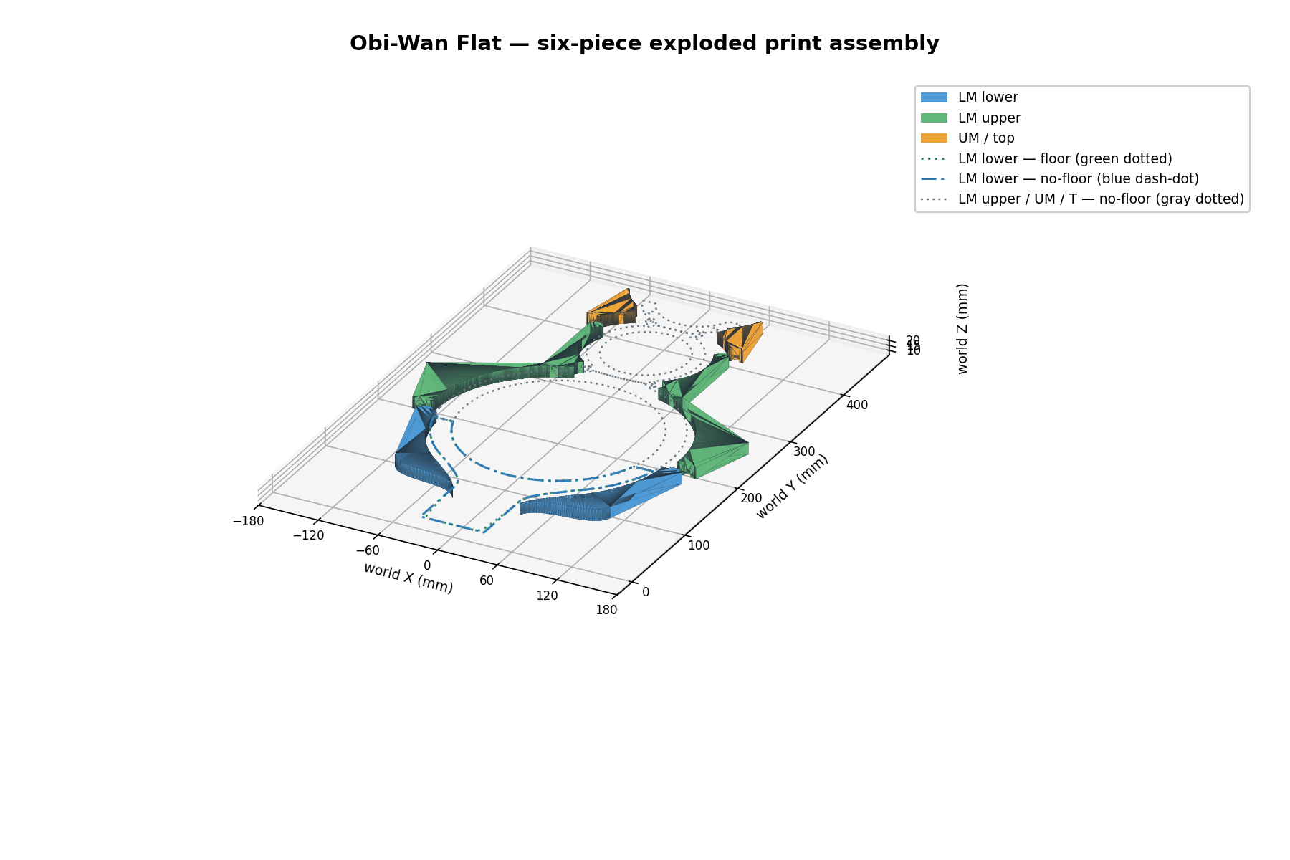
top_baffle_v2/build/wings/flat/review/obiwan_wing_flat_split_exploded.png
