antorsae/lx/top_baffle_v2/candidates/nd25fn4_crescent/print/LM_assembly_sections.png

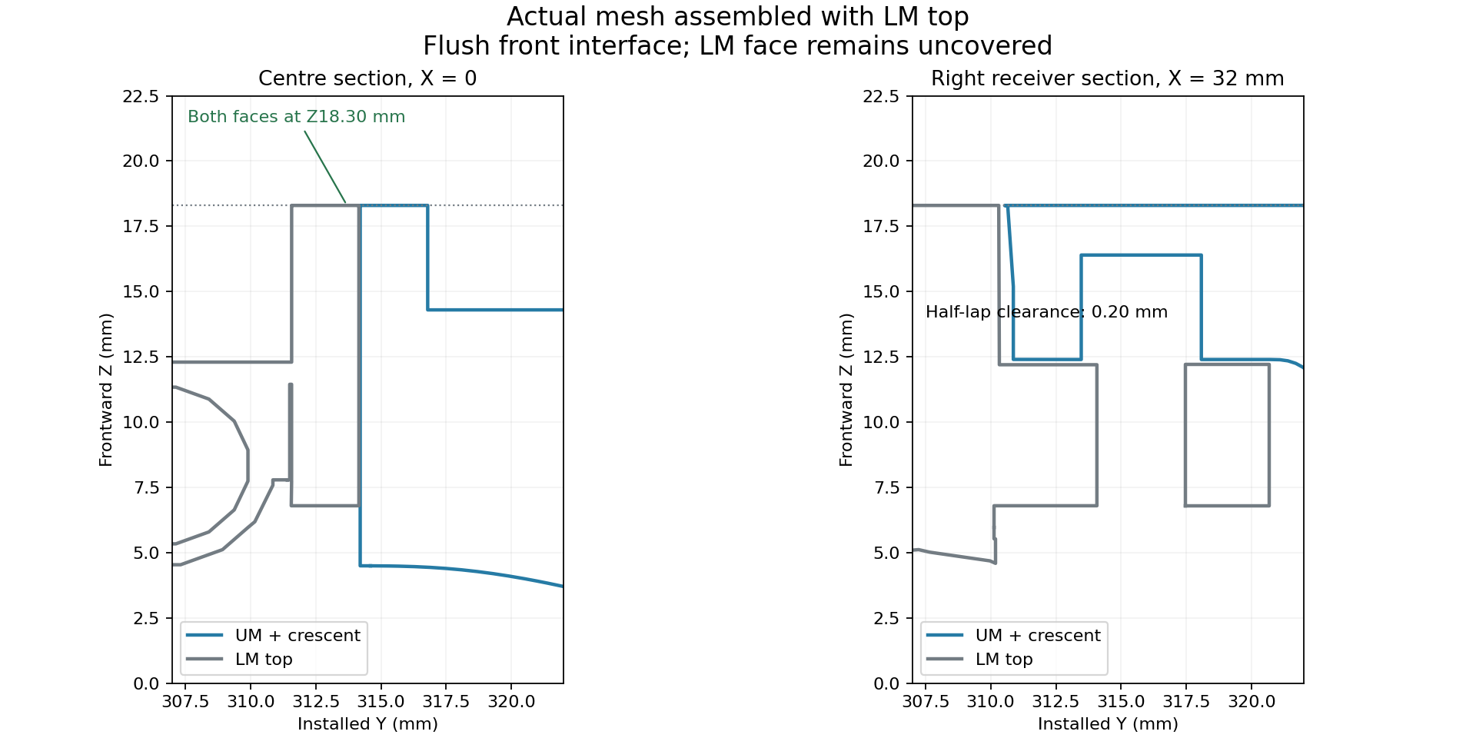
top_baffle_v2/candidates/nd25fn4_crescent/print/LM_assembly_sections.png
