antorsae/lx/top_baffle_v2/candidates/nd25fn4_crescent/views/installed.png

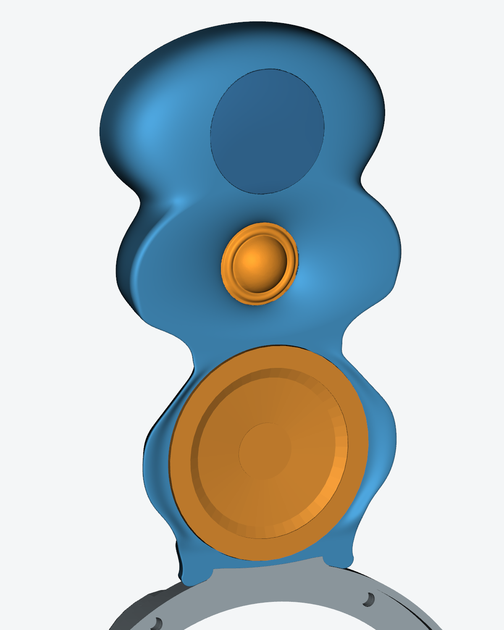
top_baffle_v2/candidates/nd25fn4_crescent/views/installed.png
