antorsae/lx/top_baffle_v2/review/nd25fn4_engineering_guide/support_settings_marked.png

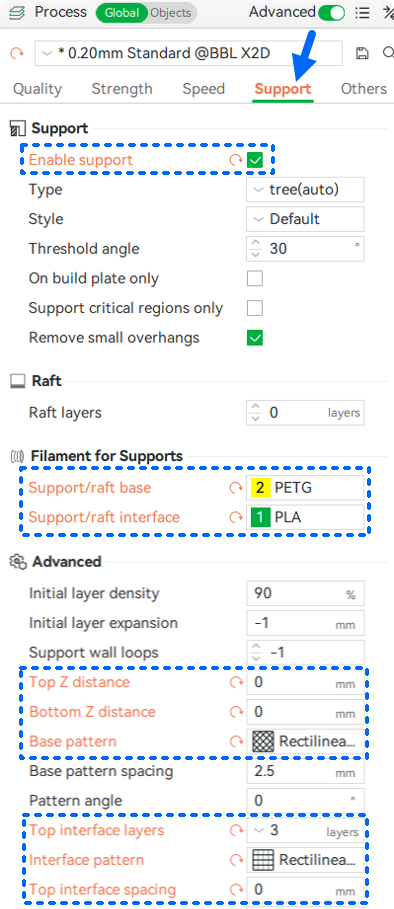
top_baffle_v2/review/nd25fn4_engineering_guide/support_settings_marked.png
