antorsae/lx/top_baffle_v2/review/nd25fn4_print/accessories/plate_1.png

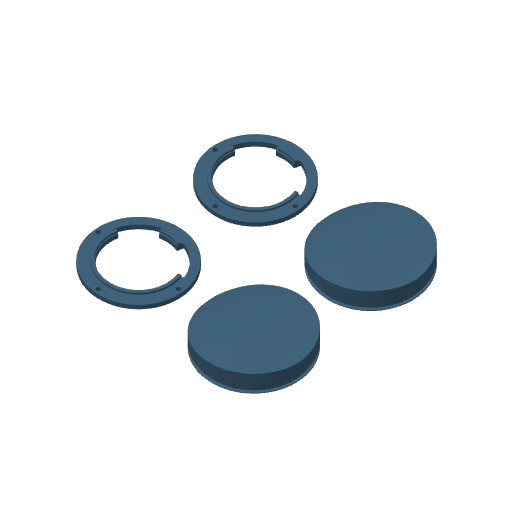
top_baffle_v2/review/nd25fn4_print/accessories/plate_1.png
