antorsae/lx/top_baffle_v2/review/nd25fn4_print/accessories/top_1.png

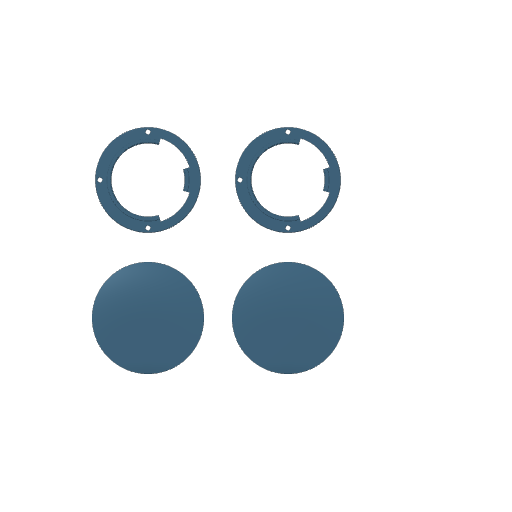
top_baffle_v2/review/nd25fn4_print/accessories/top_1.png
