antorsae/lx/top_baffle_v2/review/nd25fn4_print/body/top_1.png

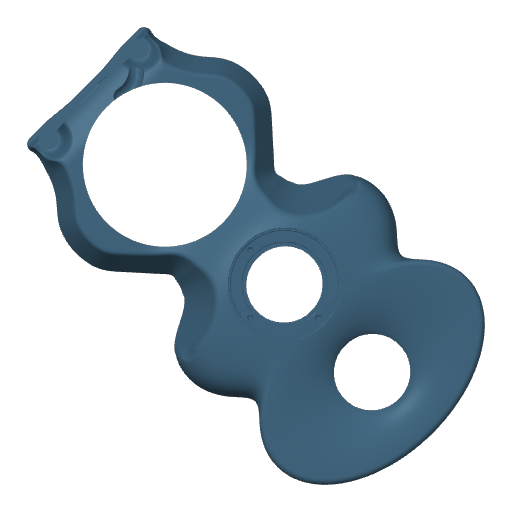
top_baffle_v2/review/nd25fn4_print/body/top_1.png
