antorsae/lx/top_baffle_v2/review/nd25fn4_print/cap_support_project_viewer.png

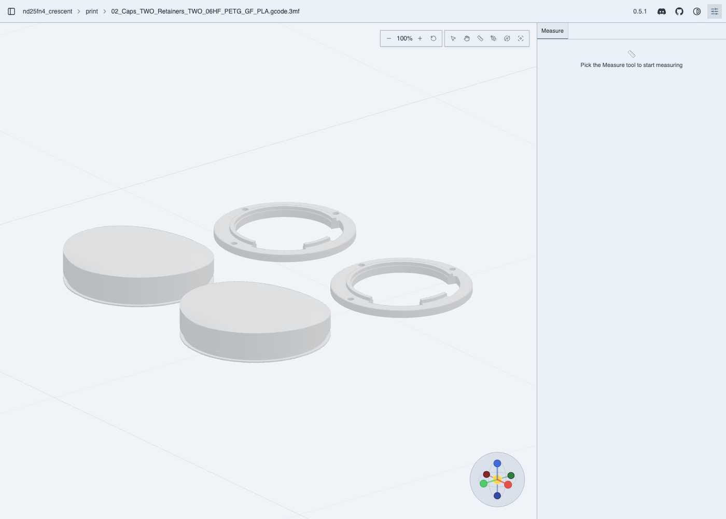
top_baffle_v2/review/nd25fn4_print/cap_support_project_viewer.png
