antorsae/lx/top_baffle_v2/review/nd25fn4_print/flush_visual_review_2.png

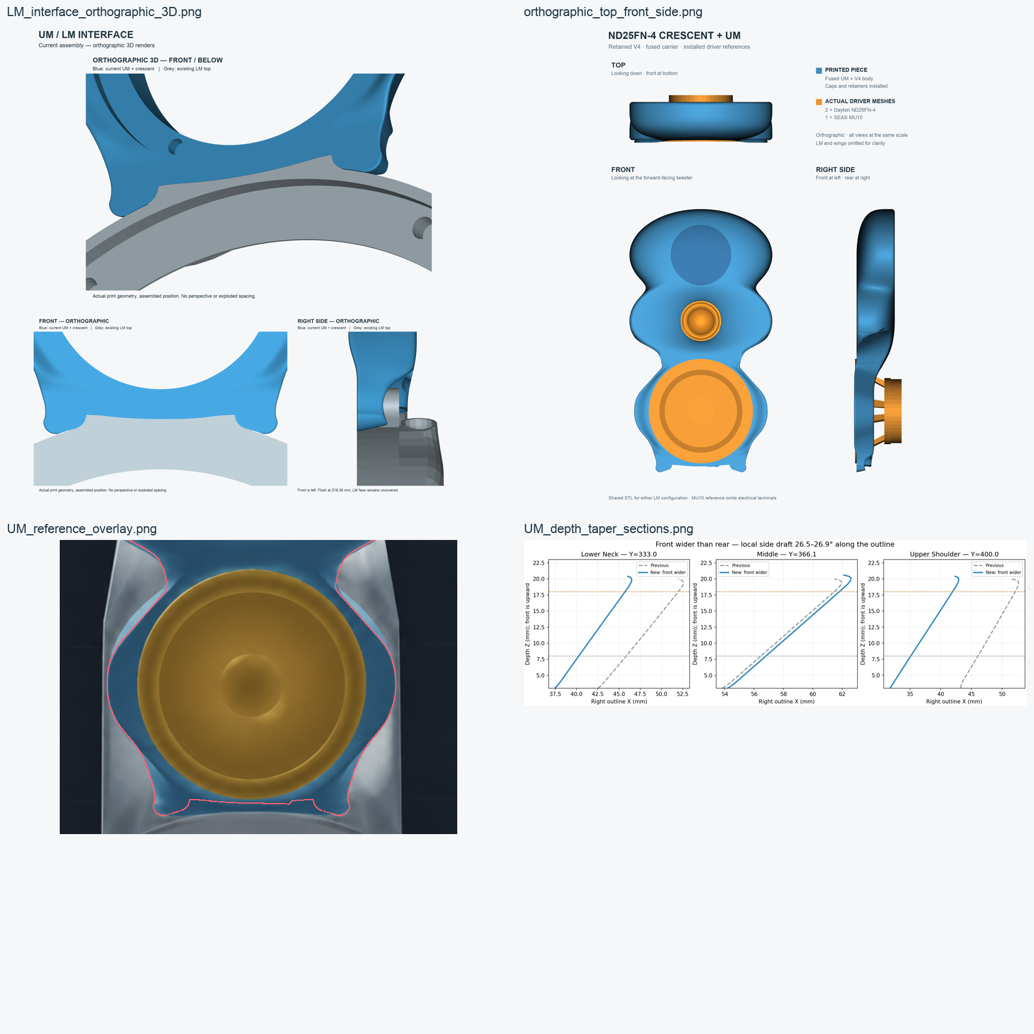
top_baffle_v2/review/nd25fn4_print/flush_visual_review_2.png
