antorsae/lx/top_baffle_v2/review/nd25fn4_print/LM_interface_detail_viewer.png

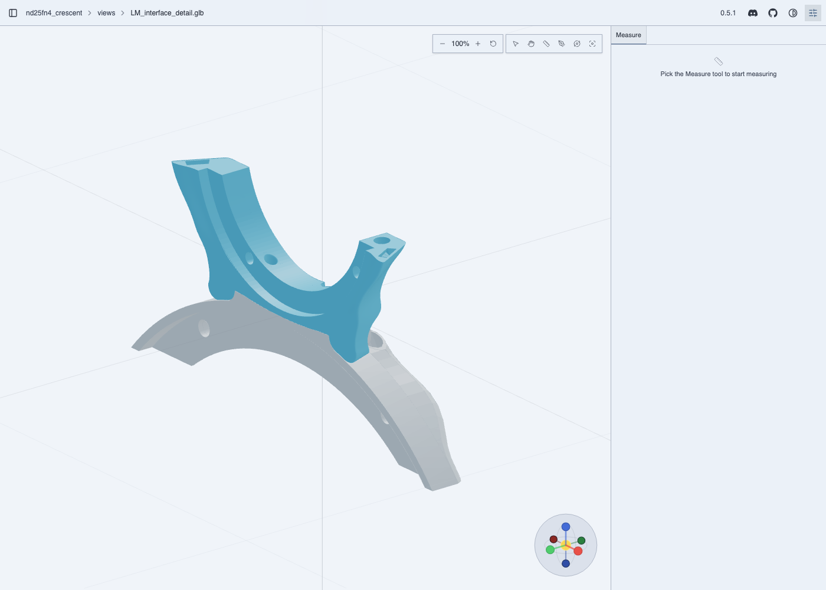
top_baffle_v2/review/nd25fn4_print/LM_interface_detail_viewer.png
