antorsae/lx/top_baffle_v2/review/nd25fn4_print/nd25fn4_color_review_viewer.png

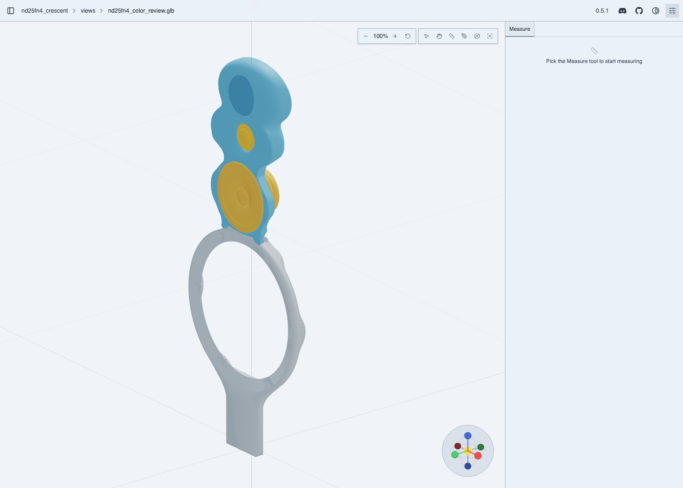
top_baffle_v2/review/nd25fn4_print/nd25fn4_color_review_viewer.png
