antorsae/lx/top_baffle_v2/review/nd25fn4_print/pre_flush_interface/views/LM_interface_orthographic_3D.png

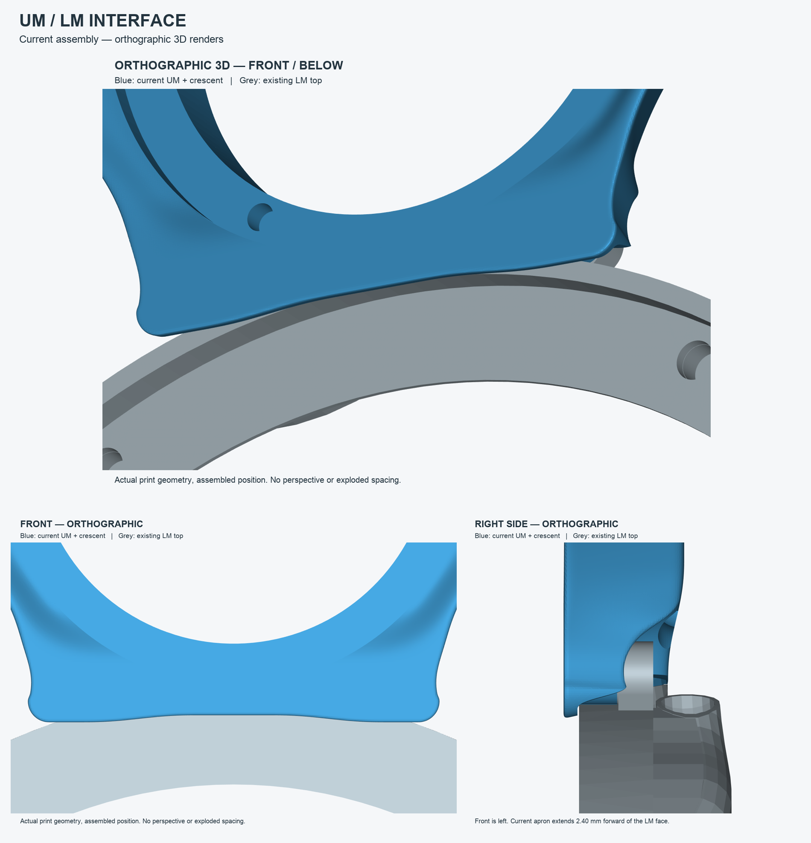
top_baffle_v2/review/nd25fn4_print/pre_flush_interface/views/LM_interface_orthographic_3D.png
