antorsae/lx/top_baffle_v2/review/nd25fn4_print/V4_flat_left_UPPER/plate_1.png

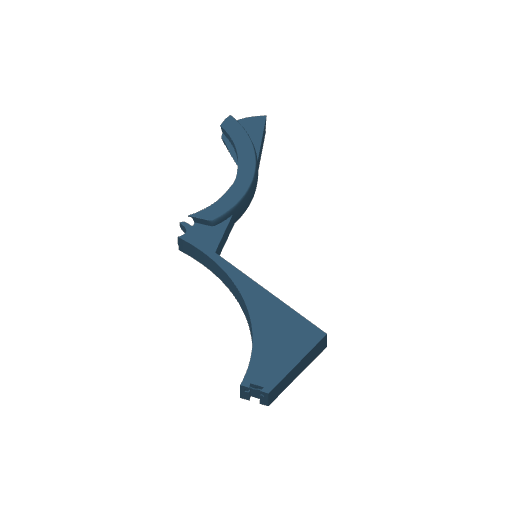
top_baffle_v2/review/nd25fn4_print/V4_flat_left_UPPER/plate_1.png
