antorsae/lx/top_baffle_v2/review/nd25fn4_print/viewer_absolute.png

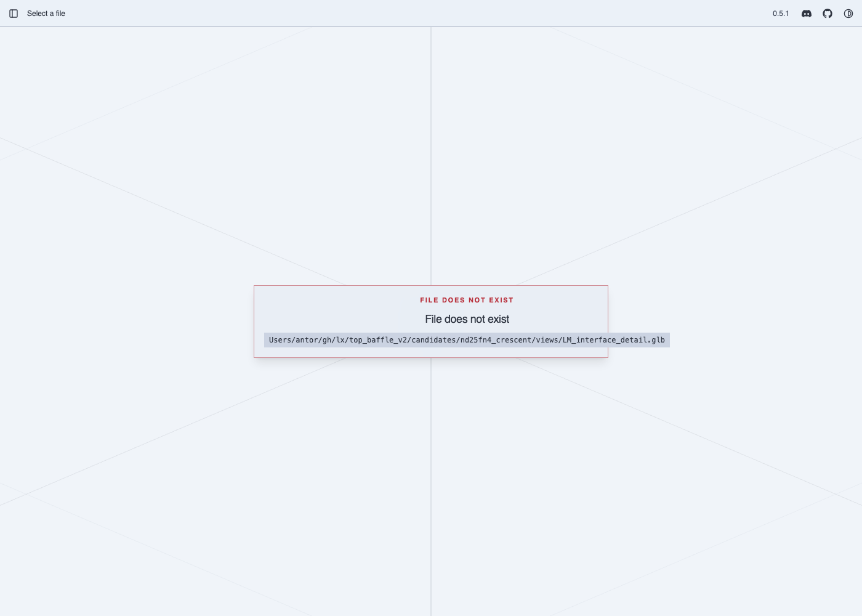
top_baffle_v2/review/nd25fn4_print/viewer_absolute.png
