antorsae/lx/top_baffle_v2/review/nd25fn4_print/waist_before_profiles.png

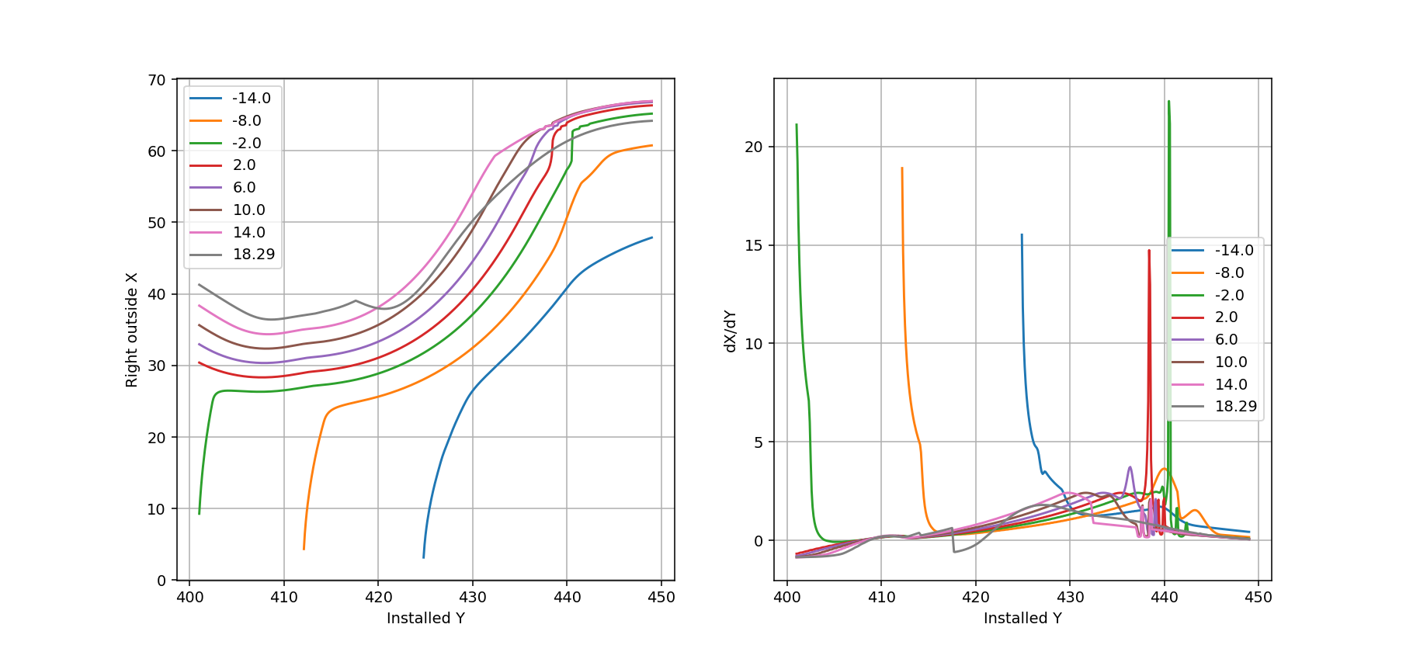
top_baffle_v2/review/nd25fn4_print/waist_before_profiles.png
