antorsae/lx/top_baffle_v2/review/nd25fn4_print/waist_fair_lofts.png

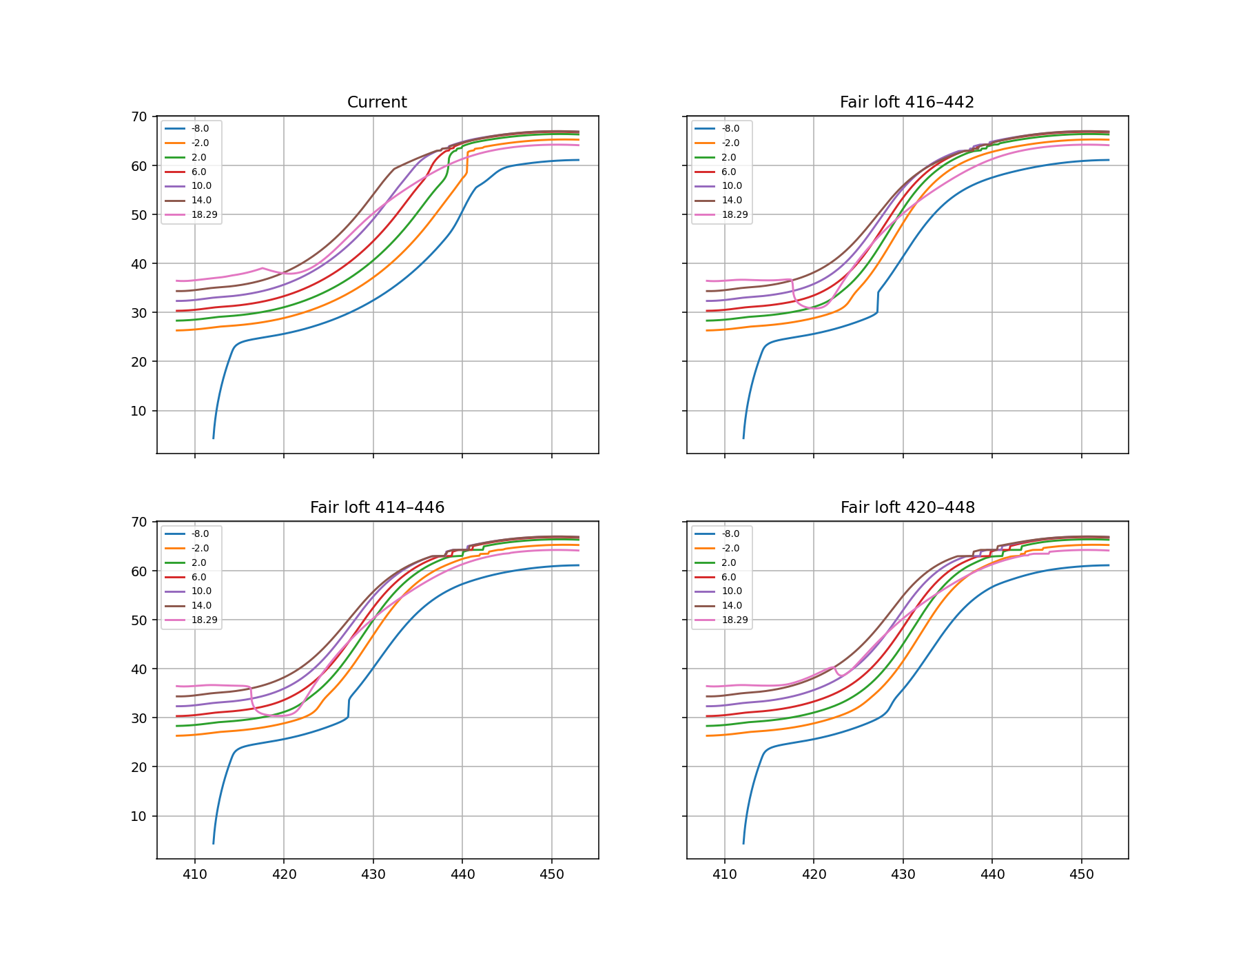
top_baffle_v2/review/nd25fn4_print/waist_fair_lofts.png
