antorsae/lx/top_baffle_v2/review/nd25fn4_print/waist_final_print_views.png

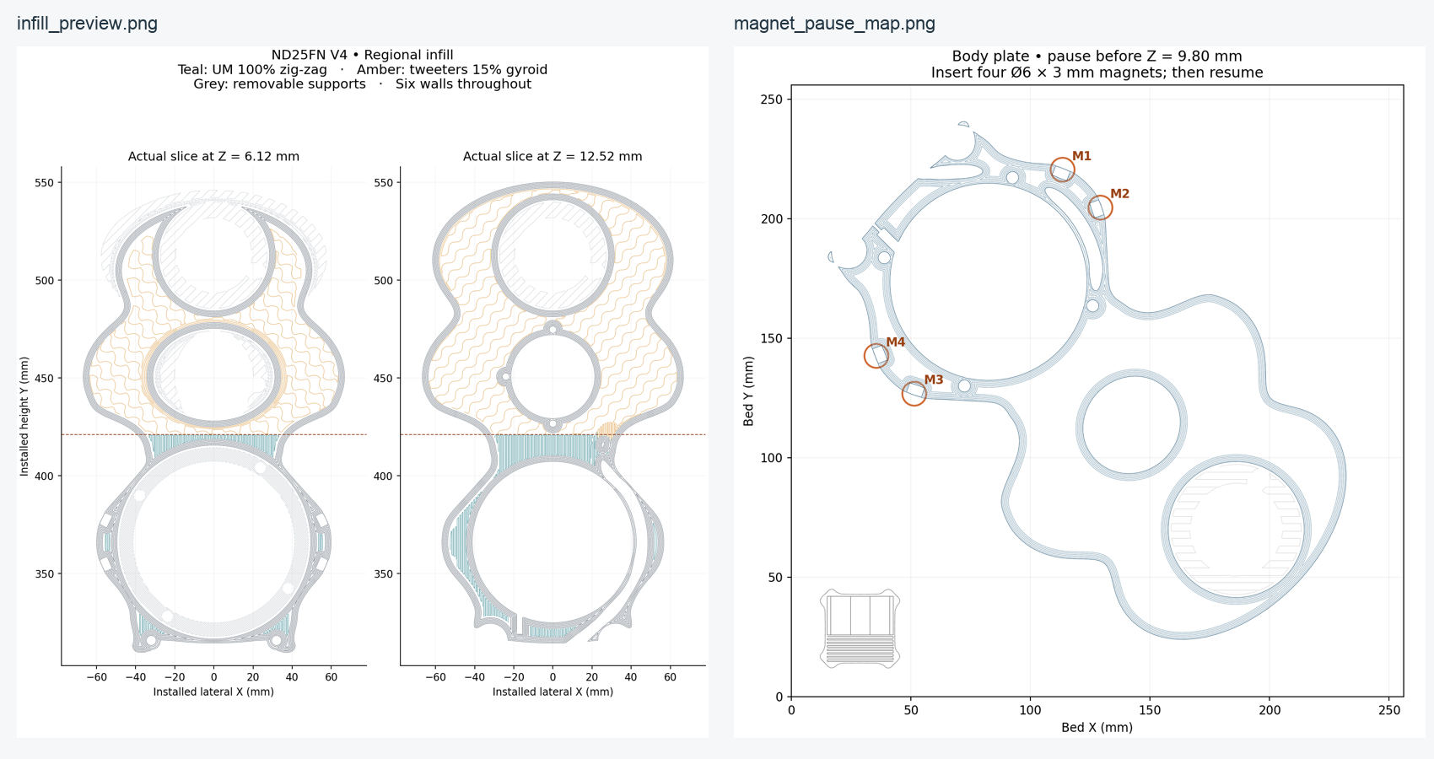
top_baffle_v2/review/nd25fn4_print/waist_final_print_views.png
