antorsae/lx/top_baffle_v2/review/print_policy_audit_20260912/obiwan_PLA_three_layers.png

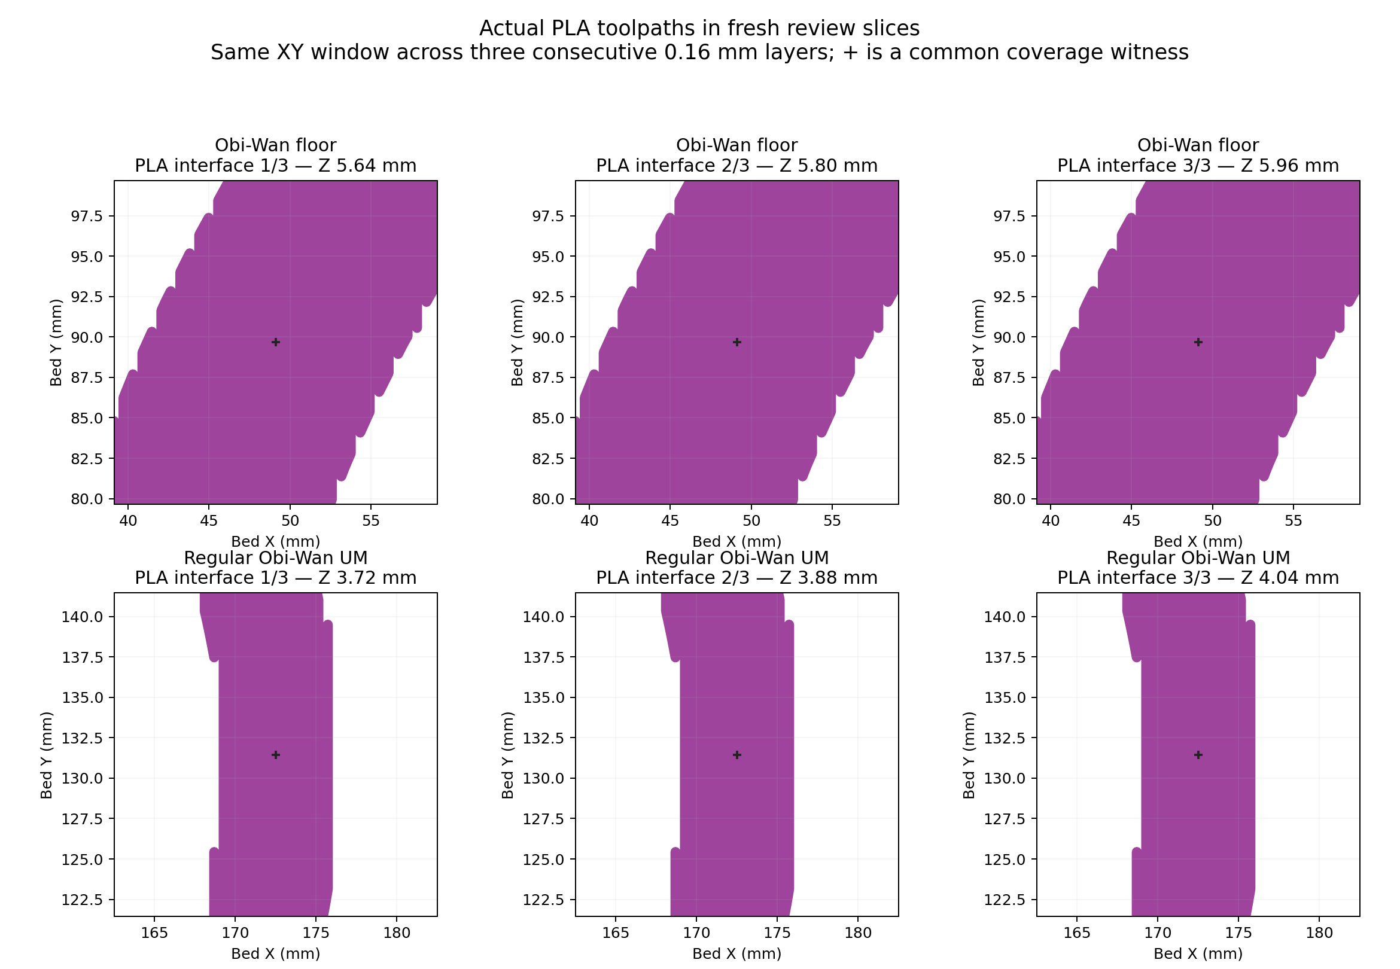
top_baffle_v2/review/print_policy_audit_20260912/obiwan_PLA_three_layers.png
