antorsae/lx/top_baffle_v2/review/print_policy_audit_20260912/regular_UM_magnet_toolpaths.png

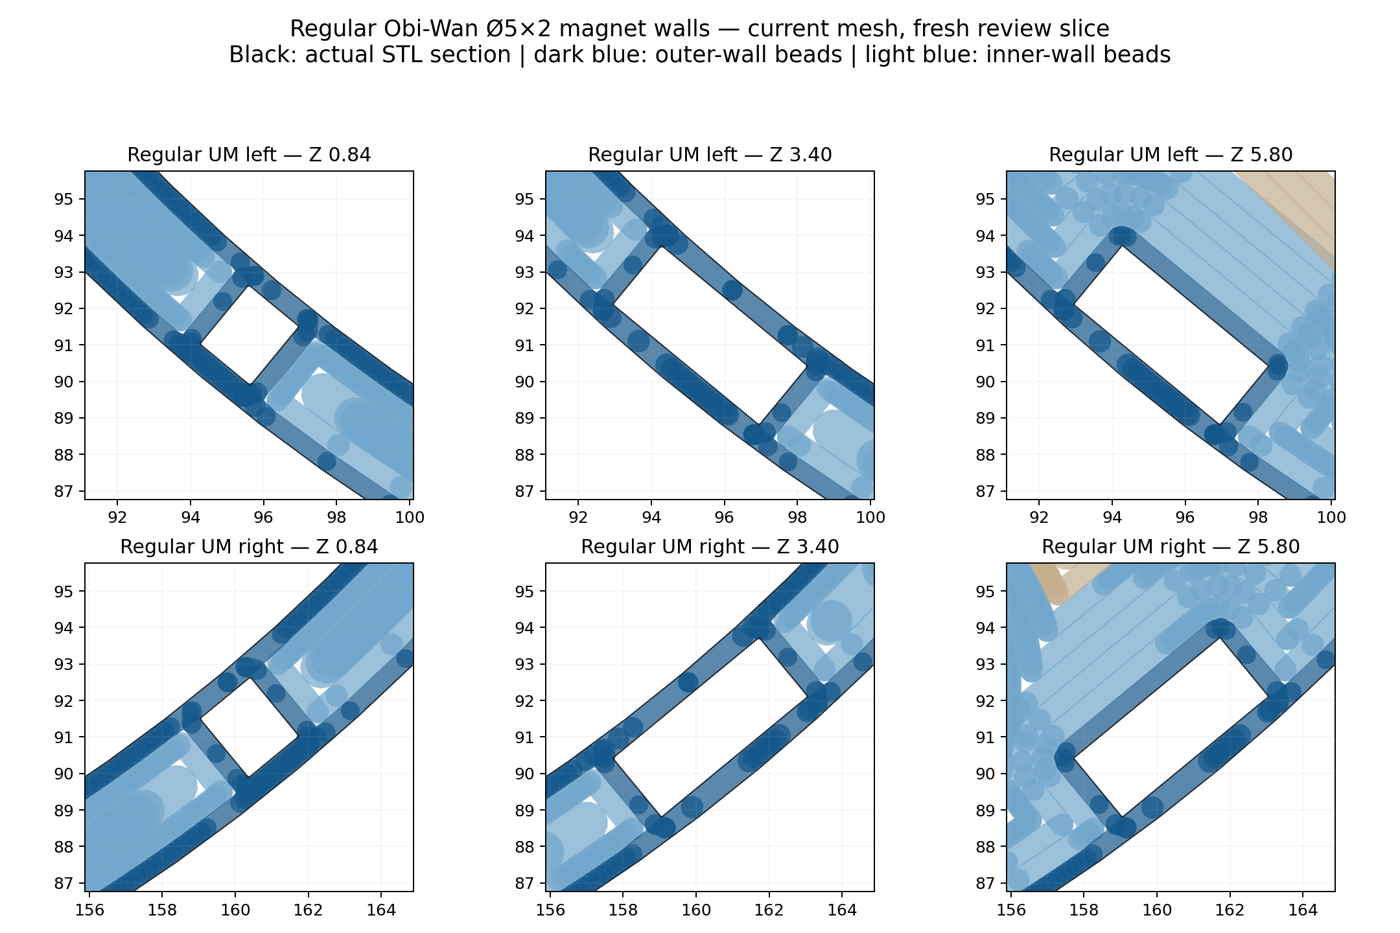
top_baffle_v2/review/print_policy_audit_20260912/regular_UM_magnet_toolpaths.png
