antorsae/lx/top_baffle_v2/review/print_policy_update_20260912/current_geometry_review_2.png

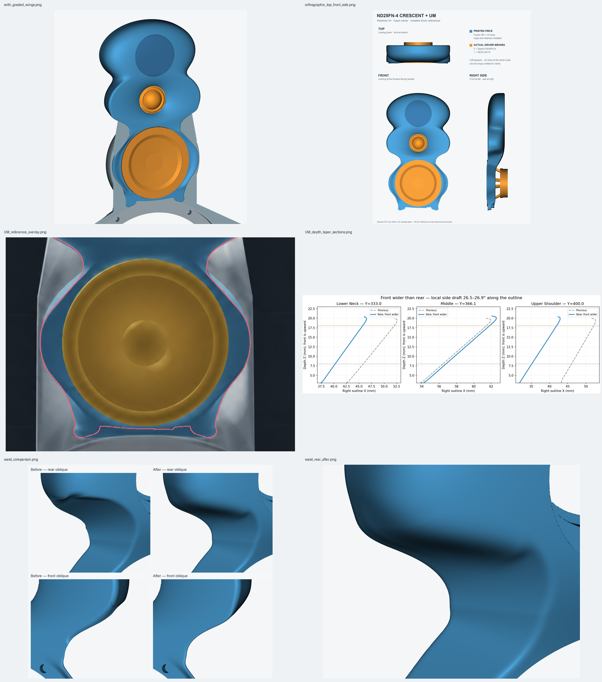
top_baffle_v2/review/print_policy_update_20260912/current_geometry_review_2.png
