antorsae/lx/top_baffle_v2/build/h2c/experiments/README.md

# H2C development trials

These are diagnostic reports, outside the manufacturing shelf. Trial meshes,
editable projects, raw toolpaths and duplicate slices are local workspaces.
Use the current projects in `../../../to_print/h2c/` for printing.

- `rejected_one_piece_floor/`: unchanged Stock/Slim full floor-stand LM
  proposals. Actual PLA support deposition exceeded the right nozzle's reach.
  The released floor version uses the established lower LM joint instead.
- `classic_wing/`: changing the full Dayton ND25FN-4 waveguide right wing to Classic fixed the D6
  insertion path but obstructed a D5 pocket too early. This setting was rejected.
- `wing_arachne_43.5_inner/`: a small orientation change still obstructed a D6
  insertion path. `wing_arachne_224.0_inner/` established the successful opposite
  orientation subsequently qualified for both right-wing styles and materials.
- `floor_support_witness.*` and `h2c_slim_lm_lower_floor_stand_shadow_trial/`:
  support seeded beneath the rear service panel passed down the cable entries.
  Extending the entry blockers through that panel removed those columns. The
  current floor jobs include this correction and have their own release audits.

Trial hashes describe the inputs at the time of each experiment. They do not
qualify current print files. Plain G-code and duplicate trial slice archives
remain disposable local caches; release G-code is stored in the published
`.gcode.3mf` files.

The public-name migration is recorded in
[`tweeter_name_migration.json`](../tweeter_name_migration.json). The previous
H2C names survive in the source history and the local ignored
`retired_dayton_revision_names/` archive. The
[history guide](../../../docs/GENERATED_HISTORY.md) maps the original commit
identifiers; old generated versions are omitted from the published rewrite.
They are not current print files.
