antorsae/lx/baffle_modeling/l22mg-bem-juan-top-populated-silent-axisym-directivity-wmax-abcd/plots/validation_vs_andres.png

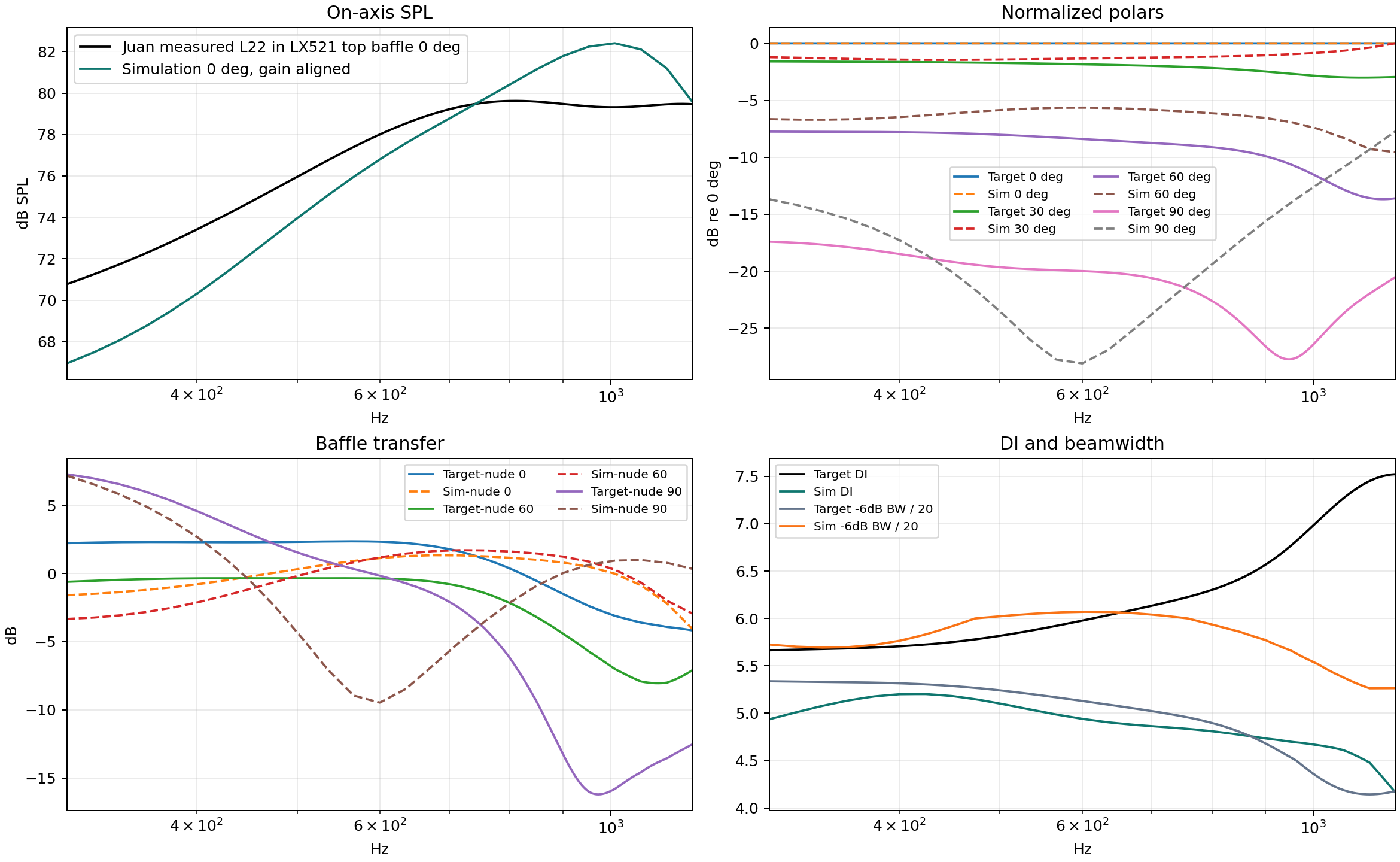
baffle_modeling/l22mg-bem-juan-top-populated-silent-axisym-directivity-wmax-abcd/plots/validation_vs_andres.png
