antorsae/lx/baffle_modeling/l22mg-source-model-cross-validation/plots/source_cv_vs_insample.png

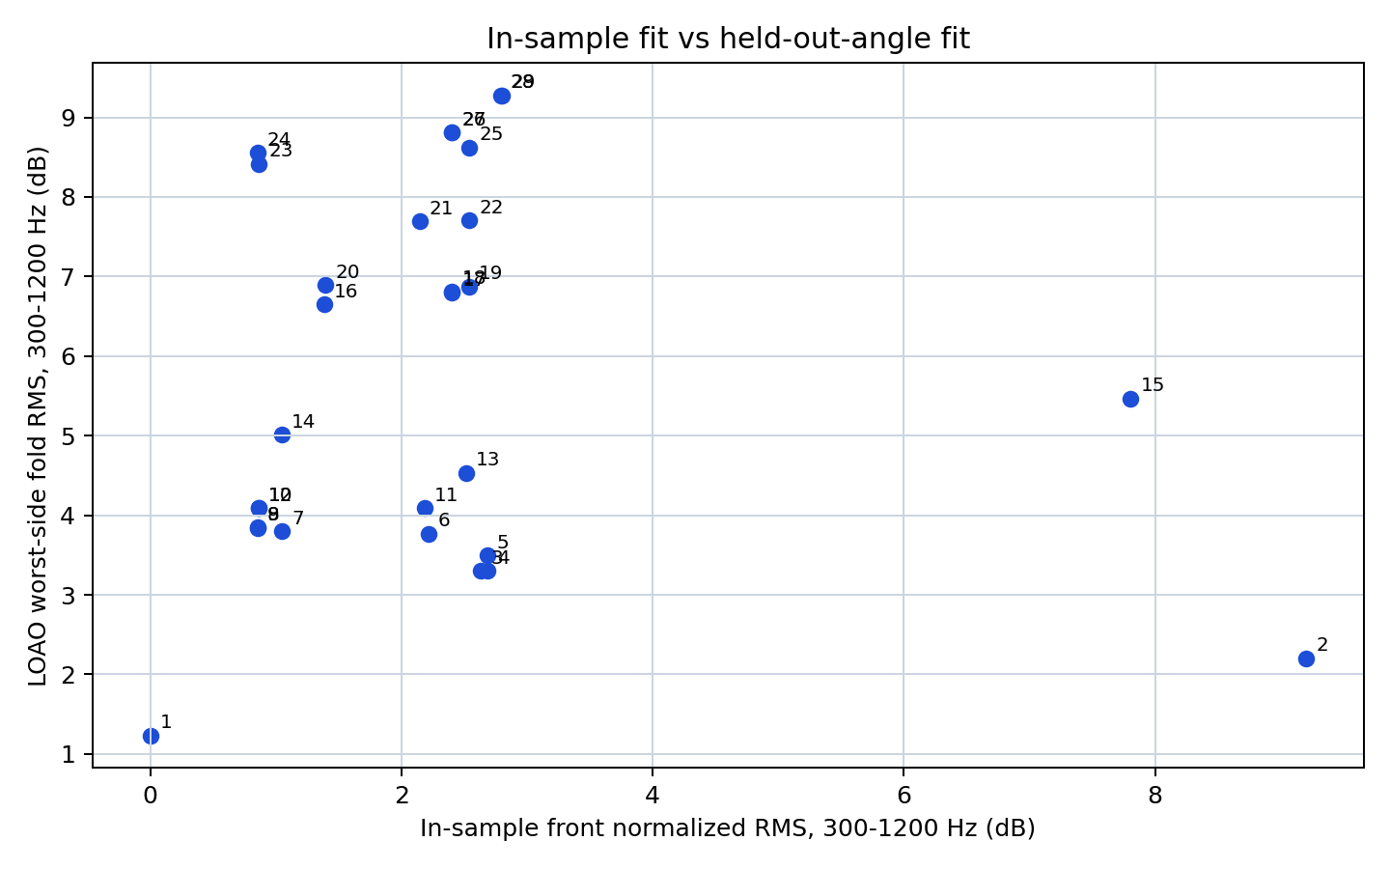
baffle_modeling/l22mg-source-model-cross-validation/plots/source_cv_vs_insample.png
