antorsae/lx/baffle_modeling/l22mg-source-model-cross-validation/plots/source_cv_worst_side_300_1200.png

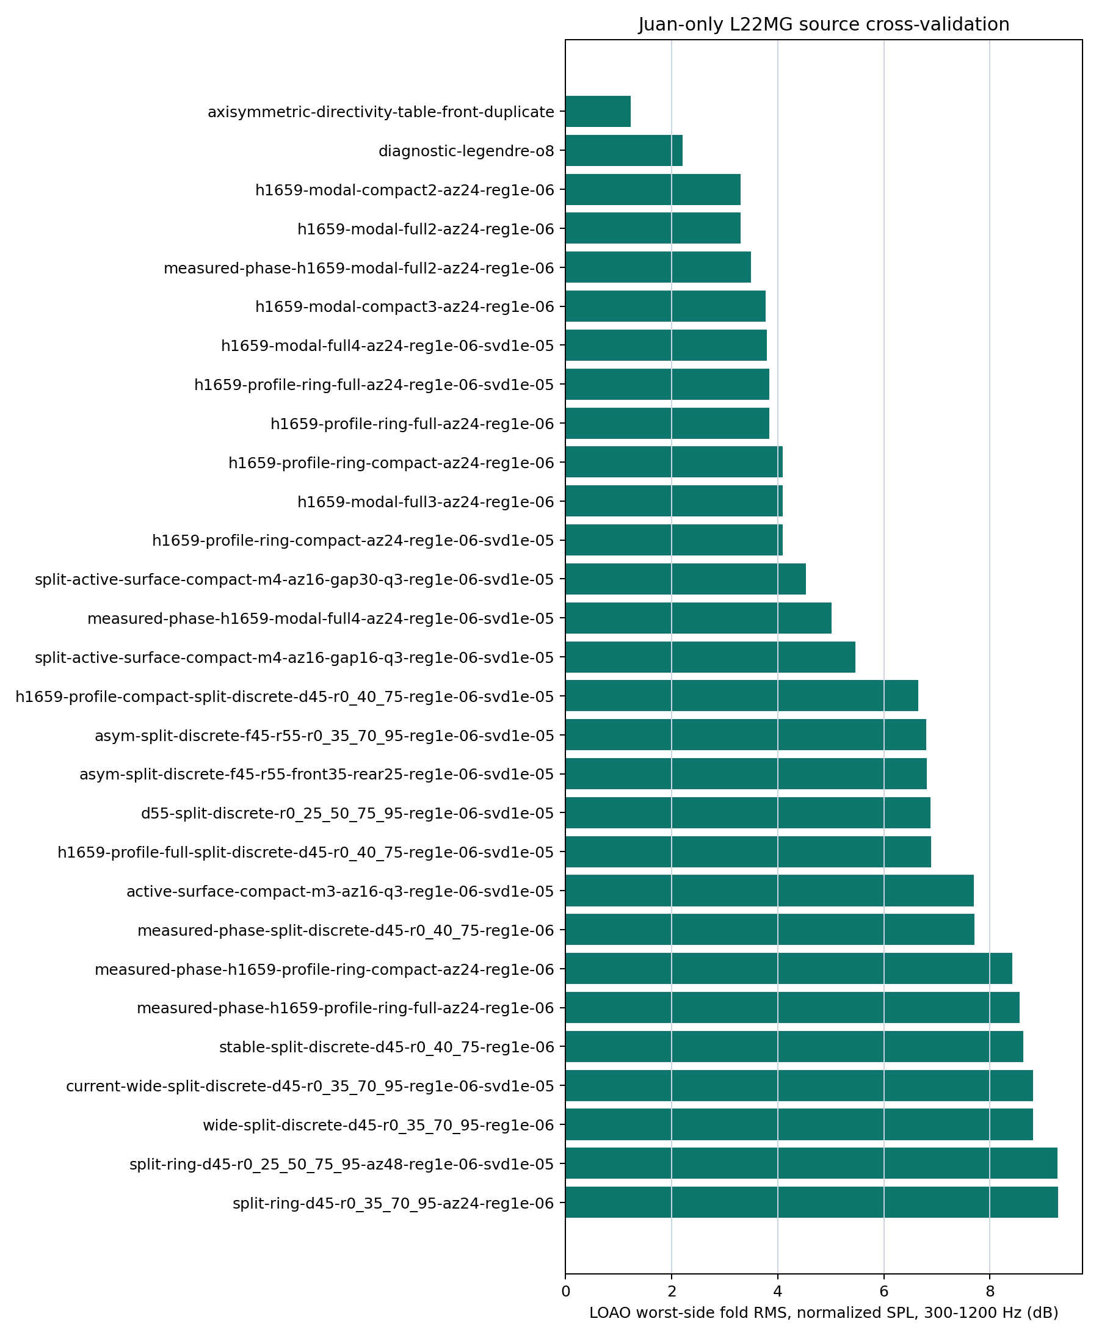
baffle_modeling/l22mg-source-model-cross-validation/plots/source_cv_worst_side_300_1200.png
