antorsae/lx/top_baffle_v2/review/nd25fn4_print/pre_waist_and_insert_fix/views/UM_outline_oblique.png

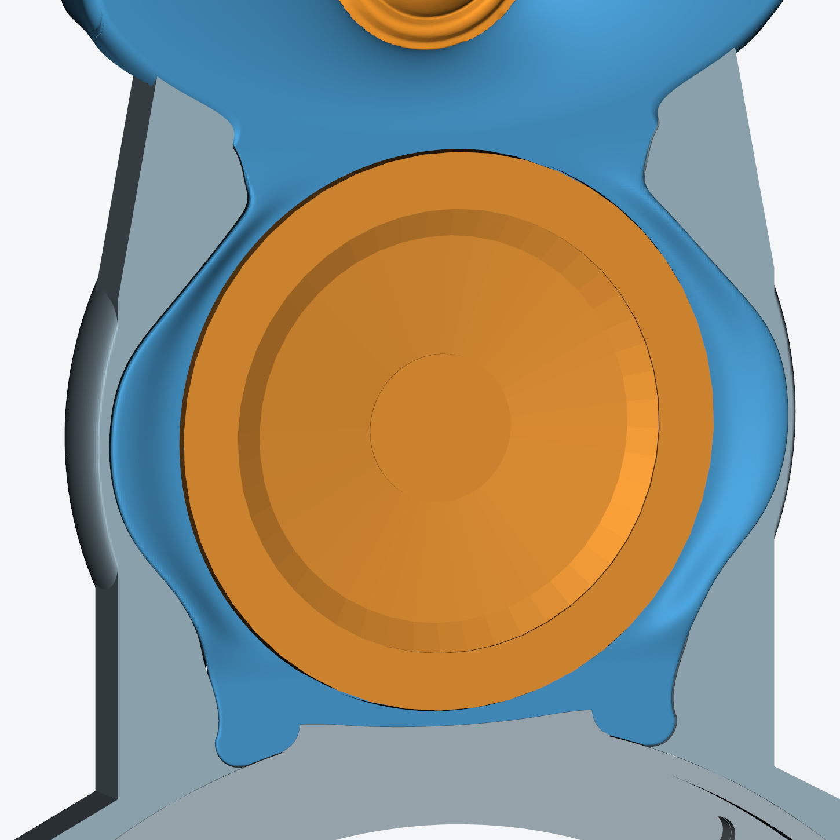
top_baffle_v2/review/nd25fn4_print/pre_waist_and_insert_fix/views/UM_outline_oblique.png
