antorsae/lx/top_baffle_v2/review/nd25fn4_print/waist_root_fix.png

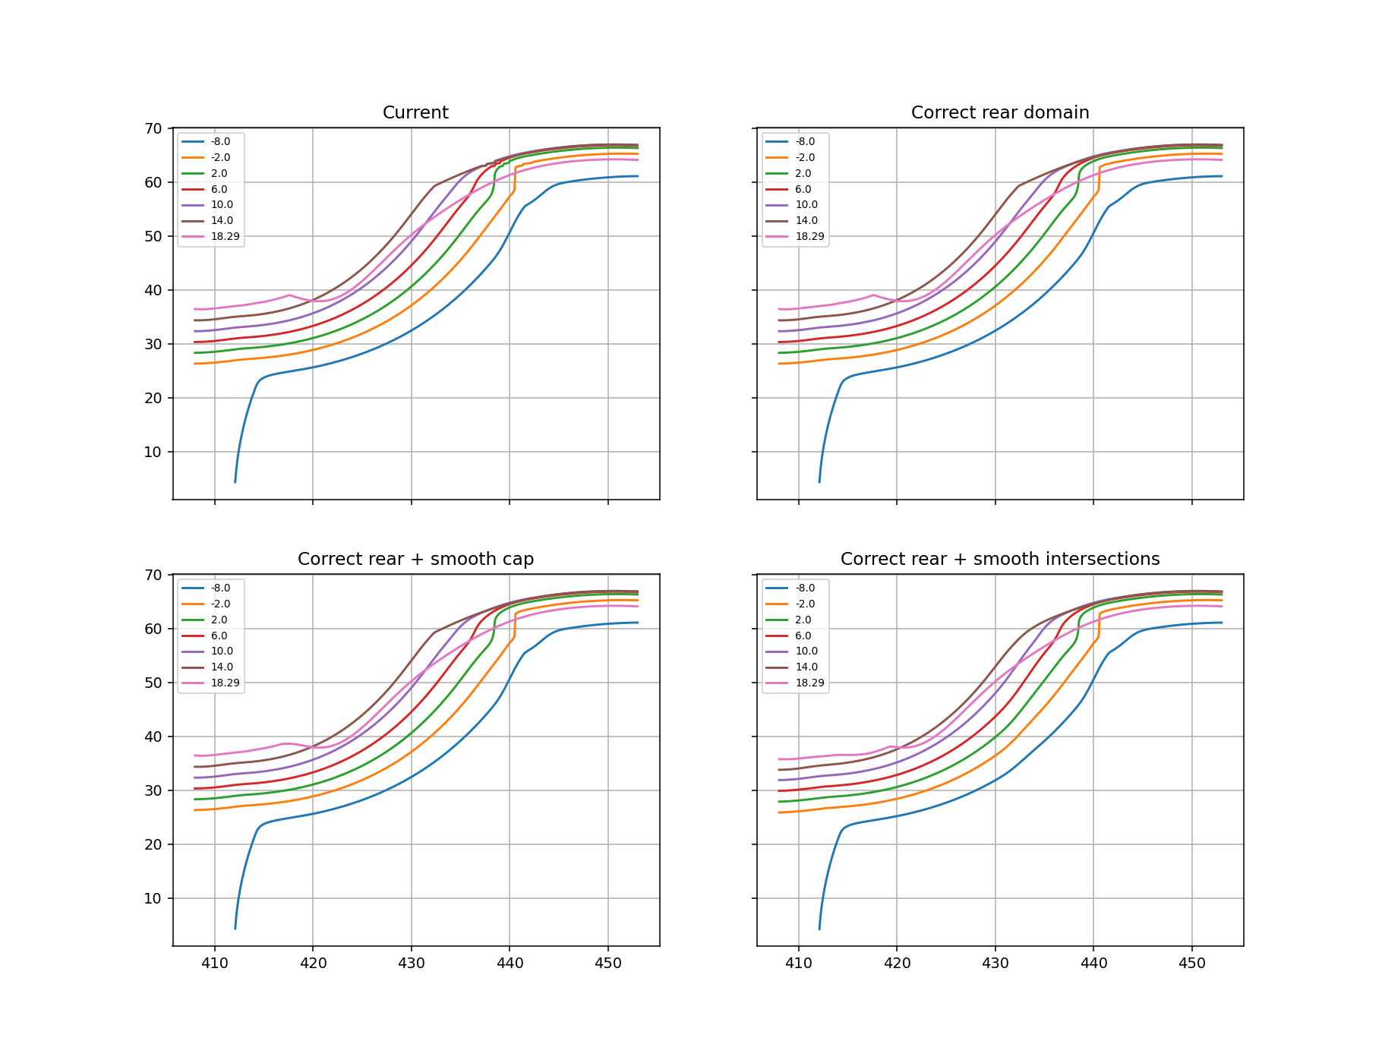
top_baffle_v2/review/nd25fn4_print/waist_root_fix.png
